SimonGAndrews/ESP32_SGATest/docs/targets/espruino_pico/resources/espruino_pico_pinout.jpg

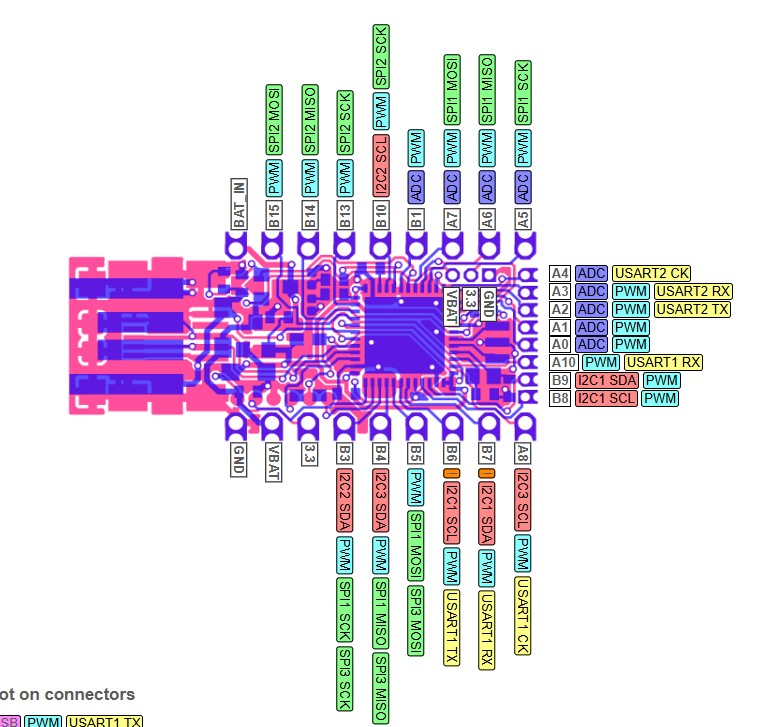
docs/targets/espruino_pico/resources/espruino_pico_pinout.jpg
