SimonGAndrews/ESP32_SGATest/docs/targets/olimex-esp32-devkit-lipo/Resources/Pinout_ESP32-S3-DevKit-LiPo.jpg

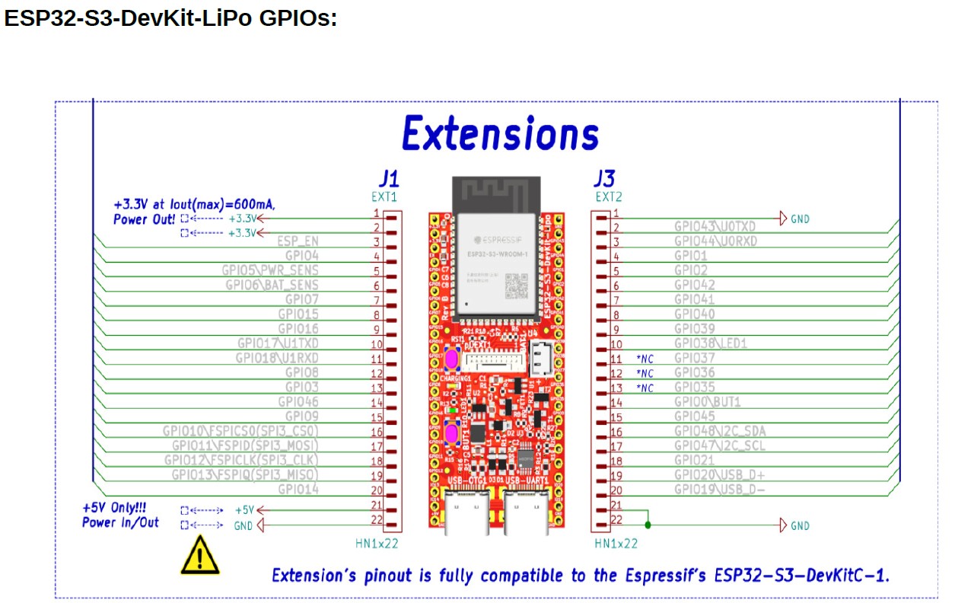
docs/targets/olimex-esp32-devkit-lipo/Resources/Pinout_ESP32-S3-DevKit-LiPo.jpg
