SimonGAndrews/ESP32_SGATest/KICAD/V2/RevA/README.md

# V2 Rev-A Project

The fresh Rev-A KiCad project is located at:

```text
KICAD/V2/RevA/Espruino_Harness_RevA/
```

It was created through KiCad as a new project rather than copied from the
exploratory schematic or PCB. Bring across only individually reviewed symbols,
footprints and implementation decisions, keeping each accepted library local
to the Rev-A project and referenced through `${KIPRJMOD}`.
