SimonGAndrews/ESP32_SGATest/KICAD/V2/RevA/Espruino_Harness_RevA/README.md

# Espruino Harness V2 Rev A

This is the fresh KiCad 9 project for the V2 Rev-A engineering-validation
harness.

The production hierarchy deliberately uses five pages:

1. `Espruino_Harness_RevA.kicad_sch` — the main A2 system page containing
   power, Rack Control, target control, the Target Interface and the
   hierarchical connections between the implementation pages.
2. `standard_test_blocks.kicad_sch` — one A2 page containing all accepted
   Standard Test Blocks as clearly labelled circuit sections.
3. `prototype_daughter_board.kicad_sch` — one A3 page containing the flexible
   wire-wrap daughter-board implementation.
4. `routing_control.kicad_sch` — one A3 page containing the Routing Fabric,
   both routing-control MCP23017s and the fixed direct-I2C isolation.
5. `power_control.kicad_sch` — one A2 page containing operating-mode
   selection, the 3.3 V rail selection and Test Block power control, and the
   target 5 V switch and two-range current monitor.

The main page is the visual integration view. Keep important supply, control,
routing and Target Interface relationships visible there. Diagnostic links,
isolation components and test points remain beside the circuits that own them.

## Draft workbench

`draft_workbench.kicad_sch` is an A3 standalone schematic for candidate
circuits and alternative implementations. It uses the project-local libraries
but is deliberately not referenced by the production hierarchy.

The workbench is therefore absent from production hierarchy exports, ERC,
netlists and BOMs. Validate it independently while drafting. When a circuit is
accepted:

1. copy it into its production-sheet location
2. check and, where necessary, re-annotate its references
3. inspect copied labels, power symbols and no-connect markers
4. run ERC and export the netlist from the production root schematic
5. compare the resulting connections with the governing specification

Do not treat the presence of a circuit on the workbench as design acceptance.

Use the project-local libraries described in `LIBRARY_PROVENANCE.md`. Bring
assets across from the exploratory project only after individual review.

The Rev-A verification scaffold is under `verification/`. Production ERC and
netlist evidence must be generated from the root schematic, not from an
individual hierarchical sheet.
