SimonGAndrews/ESP32_SGATest/docs/design/V2Harness/arch/TargetInterfaceContract_V2.md

# V2 Target Interface Contract

**Status:** Accepted — corrected power allocation and complete 48-contact map

**Version:** 1.4

**Last Updated:** 5 September 2026

## 1. Conclusion

The accepted mechanical direction uses two 24-pin connectors on each board,
giving 48 contacts. The accepted map assigns 32 signal/control contacts, four
power contacts — one target 3.3 V reference, one selected target-VBUS return
and two switched 5 V feeds — and twelve grounds. VBUS source selection is
manual and local to the daughter board, so no select conductor crosses the
Target Interface.

The currently mapped 32 signal and control pins provide:

* seven reusable route pins, R0-R6
* 23 direct connections to the Standard Test Blocks
* direct reset and boot-control pins

Section 7 shows the accepted mapping, how Connector A and Connector B mate
and how the Breakaway Links join the boards before separation. It is not an
implementation authority for the Target Interface.

The accepted physical arrangement uses two female right-angle socket banks on
the reusable harness and two male right-angle header banks on each daughter
board. The connectors are cut to 2x12 positions from the selected 2x36 parts
listed in Section 7.1 and hand-fitted after AISLER manufacture. Received-part
measurements, physical mating, current capacity and final PCB footprints still
need to be verified before the Rev-A PCB is released.

## 2. What This Document Defines

This document defines the wires that cross between the reusable harness board
and a removable target daughter board. It also gives each wire a pin on
Connector A or Connector B.

The pinout is based on:

* `StandardTestBlocks_V2.md`
* `StandardControlServices_V2.md`
* `TargetRoutingEnvelope_V2.md`
* `CombinedCapabilityConnectionMatrix_V2.md`
* `I2CControlledRouting_V2.md`
* `HybridHarnessArchitecture_V2.md`

Every daughter board must use this same pinout. A pin may carry one listed
function, a duplicated power connection or ground. There are no unassigned
spare pins in the accepted 48-pin arrangement.

## 3. Signals And Power On The Connectors

### 3.1 Reusable Route Pins

R0-R6 are seven connector pins that feed the Routing Fabric on the reusable
harness. The daughter board wires a suitable target GPIO to each route pin
used by that target.

| Route pin | It can be switched to | How the target uses it | Electrical type |
|---|---|---|---|
| R0 | `TI_ANALOG_ADC_IN`; `TI_ONEWIRE_DQ` | Analogue input or bidirectional open-drain | Bidirectional analogue-capable 0 V to 3.3 V |
| R1 | `TI_GPIO_LOOP_A_OUT`; `TI_SPI_MISO` | Output or input | Bidirectional 3.3 V digital |
| R2 | `TI_GPIO_LOOP_A_IN`; `TI_I2C_FB`; `TI_SPI_CS_ADC`; `TI_ONEWIRE_GPIO_A_FB` | Input or output | Bidirectional 3.3 V digital |
| R3 | `TI_GPIO_LOOP_B_OUT`; `TI_SPI_MOSI`; `TI_UART_A_TX` | Output | 3.3 V digital output |
| R4 | `TI_SPI_SCK`; `TI_UART_A_RX` | Output or input | Bidirectional 3.3 V digital |
| R5 | `TI_ANALOG_PWM_OUT`; `TI_RGB_DATA` | Output | 3.3 V digital waveform |
| R6 | `TI_GPIO_LOOP_B_IN`; `TI_I2C_INT`; `TI_SPI_CS_EXT`; `TI_ONEWIRE_GPIO_B_FB` | Input or output | Bidirectional 3.3 V digital |

All seven route pins are present on every harness. A daughter board may leave
one unconnected only when that target provides the required test connection by
a documented direct connection instead.

### 3.2 Direct Standard Test Block Pins

The connectors provide 23 pins that wire directly to the Standard Test Blocks.
A target with enough GPIO can use these direct pins. A target with fewer GPIO
can use R0-R6 and the Routing Fabric instead. The direction in the table is
shown from the target's point of view.

| Pin function | Test Block | Target direction | Connection |
|---|---:|---|---|
| `TI_GPIO_LOOP_A_OUT` | 1 | Output | Dedicated Test Block pin |
| `TI_GPIO_LOOP_A_IN` | 1 | Input | Dedicated Test Block pin |
| `TI_GPIO_LOOP_B_OUT` | 1 | Output | Dedicated Test Block pin |
| `TI_GPIO_LOOP_B_IN` | 1 | Input | Dedicated Test Block pin |
| `TI_ANALOG_PWM_OUT` | 2 | Output | Dedicated Test Block pin |
| `TI_ANALOG_ADC_IN` | 2 | Analogue input | Dedicated Test Block pin |
| `TI_I2C_SDA` | 3 | Bidirectional open-drain | Direct shared I2C bus |
| `TI_I2C_SCL` | 3 | Bidirectional open-drain | Direct shared I2C bus |
| `TI_I2C_FB` | 3 | Input | Dedicated Test Block pin |
| `TI_I2C_INT` | 3 | Input | Dedicated Test Block pin |
| `TI_SPI_SCK` | 4 | Output | Dedicated Test Block pin |
| `TI_SPI_MOSI` | 4 | Output | Dedicated Test Block pin |
| `TI_SPI_MISO` | 4 | Input | Dedicated Test Block pin |
| `TI_SPI_CS_ADC` | 4 | Output | Dedicated Test Block pin |
| `TI_SPI_CS_EXT` | 4 | Output | Dedicated Test Block pin |
| `TI_ONEWIRE_DQ` | 5 | Bidirectional open-drain | Dedicated Test Block pin |
| `TI_ONEWIRE_GPIO_A_FB` | 5 | Input | Dedicated Test Block pin |
| `TI_ONEWIRE_GPIO_B_FB` | 5 | Input | Dedicated Test Block pin |
| `TI_UART_A_TX` | 7 | Output | Dedicated Test Block pin |
| `TI_UART_A_RX` | 7 | Input | Dedicated Test Block pin |
| `TI_UART_B_TX` | 7 | Output | Dedicated Test Block pin |
| `TI_UART_B_RX` | 7 | Input | Dedicated Test Block pin |
| `TI_RGB_DATA` | 9 | Output | Dedicated Test Block pin |

The harness provides every pin in this table, but a daughter board does not
have to connect all of them. Its schematic and Target Profile must show which
functions are wired directly, wired through R0-R6 or left unconnected. The
direct and routed versions of the same function must never be enabled together.

### 3.3 Power, Reset And Boot Pins

| Pin function | Direction | What it does | Wiring rule |
|---|---|---|---|
| `TI_TARGET_3V3` | Target to harness | Provides the target's actual 3.3 V I/O-domain reference and rail-valid indication | Low-current reference only; shall remain between 3.00 V and 3.60 V while the target is powered and shall never supply harness logic or be joined to another 3.3 V source |
| `TI_TARGET_VBUS` | Daughter board to harness | Returns the manually selected VBUS — the same VBUS delivered to the target — to the harness-local 5 V-to-3.3 V regulator | Shall be absent when selected target VBUS is intentionally off and shall not bypass target-power monitoring or switching |
| `TI_SWITCHED_TARGET_5V` | Harness to daughter board | Supplies the Supervisor-controlled input to the daughter-board VBUS selector | Shall not be joined directly to host VBUS; the selector chooses exactly one source and is changed only while unpowered |
| `TI_TARGET_RESET_N` | Harness to target | Pulls the target reset input low | Must normally be released and must not depend on I2C or the Routing Fabric |
| `TI_BOOT_REQUEST` | Harness to target | Optionally pulls a target boot or recovery input low | A daughter board may leave it unconnected when the target has no safe equivalent |

`TI_TARGET_3V3` is deliberately independent of the 300 mA harness-load budget.
The corrected Power Control Service always supplies that load from either the
harness-local regulator or `EXT_3V3`.

The three power functions have fixed ownership: switched 5 V travels from the
harness to the selector, selected target VBUS returns from the selector to the
harness regulator, and target 3.3 V travels from the target only as a bounded
reference. None may be used in the opposite direction.

### 3.4 Common Ground

All `TI_GND` pins are connected to the same 0 V ground on both boards. Multiple
ground pins spread the return current and place a nearby ground beside the
main signal groups.

The accepted pinout uses twelve ground pins across Connector A and Connector B.
They are placed near power, analogue, I2C, SPI, UART and the general digital
signals.

## 4. Contact Allocation

The corrected interface has 35 different functions:

| Function group | Pins |
|---|---:|
| Route pins R0-R6 | 7 |
| Direct Standard Test Block pins | 23 |
| Target 3.3 V reference, selected target VBUS and switched 5 V | 3 |
| Reset and boot controls | 2 |
| **Different functions** | **35** |

The physical map uses 48 contacts for the 35 functions, one duplicate
switched-target-5-V contact and twelve ground contacts. The allocation is
therefore complete. Using R0-R6 can reduce the number of target GPIOs needed
for a particular daughter board, but it does not remove the direct Test Block
pins from the standard connector.

## 5. Connections Handled Elsewhere

The following connections do not pass through Connector A or Connector B:

| Function | Where it connects instead |
|---|---|
| Target USB D+, D−, host VBUS and the physical host/target USB connectors | Common daughter-board USB data/VBUS-selector Adapter Service; only selected `TI_TARGET_VBUS` and Supervisor `TI_SWITCHED_TARGET_5V` cross the interface |
| SWD, JTAG and target-specific debug | A target connector or daughter-board Adapter Service |
| UART CTS and RTS | A daughter-board Adapter Service when a target needs that test |
| Onboard USB-UART bridge isolation | Target-specific links, wiring or a proved target modification; a setup instruction alone is sufficient only when bench evidence shows that it removes the bridge drive |
| `SUP_EVENT_OUT` and `SUP_EVENT_IN` | The separate Supervisor Interface between the Rack Control Endpoint and Test Block 3 |
| Rack Control I2C | The Rack Control Backplane |
| Target Power Monitor I2C and shunt | Reusable-harness circuitry connected to the Rack Control Backplane |
| `ROUTE_CLEAR_N` and routing-controller controls | Internal reusable-harness wiring |
| External regulated 3.3 V and 5 V inputs | Harness power connectors |
| Target-specific VIN, VBAT, USB-OTG VBUS or other rails | A daughter-board Adapter Service where required |
| Target or daughter-board identity | Documentation and the Target Profile; no connector pin is currently required |

ESP32-C3-DevKitC-02 V1 evidence demonstrates why this remains outside the
common Interface. Its daughter-board native USB Adapter Service successfully
provides an independent `/dev/ttyACM` control path, but the target's onboard
CP2102N still drives UART0 RX on D20 through R21 whenever the DevKit is
powered. That internal target-board branch cannot be disconnected by Connector
A, Connector B or reusable-harness routing. The unmodified target profile must
therefore disable the full UART crosslink and use the standard endpoint-A
external-peer form unless another non-contending mapping is proved.

Adding one of these functions to a later Target Interface would require a
review of this pinout and the architecture documents that define the function.

## 6. Architecture Cross-Check

The pin list includes:

* all 23 target-facing connections from `StandardTestBlocks_V2.md`
* all seven route pins from `TargetRoutingEnvelope_V2.md`
* the direct I2C and second UART connections required by the combined matrix
* target 3.3 V reference, selected target VBUS, switched target 5 V, reset and optional boot from
  `StandardControlServices_V2.md`
* both the direct and routed wiring required by
  `HybridHarnessArchitecture_V2.md`
* the decision to handle CTS/RTS and the Target Power Monitor elsewhere

The accepted resolution is a separate manual two-position source selector on
every daughter board. It chooses host VBUS in Standalone or
`TI_SWITCHED_TARGET_5V` in Supervisor and is changed only while unpowered. No
schematic shall infer mode solely from the presence of
`TI_SWITCHED_TARGET_5V`, and raw host VBUS shall not cross this interface.

## 7. Connector Pinout

### 7.1 Connector Arrangement

The Target Interface uses two 24-pin connectors, called Connector A and
Connector B. Each connector has two rows of 12 pins on a 2.54 mm pitch.
Right-angle through-hole parts allow the reusable harness and daughter board
to lie in the same plane.

This gives:

* 48 pins using only two connectors on each board
* a clear Connector A and Connector B in the schematic and PCB layout
* female contacts on the permanently installed harness and exposed male pins
  only on the removable daughter board
* fewer parts to buy and align than four smaller connectors

The accepted connector products are:

| Board | Accepted product | Supplier reference | Preparation and assembly |
|---|---|---|---|
| Reusable harness | Adafruit Product `1543`, 0.1-inch 2x36 right-angle female socket strip | The Pi Hut SKU `104444` | Cut into 2x12 sections; mandatory hand-fit after AISLER manufacture |
| Daughter board | Adafruit Product `1541`, 0.1-inch 2x36 right-angle male breakaway header | The Pi Hut SKU `104400` | Break into 2x12 sections; mandatory hand-fit after manufacture |

Product sources and the available female technical drawing are:

* <https://thepihut.com/products/0-1-2x36-pin-strip-right-angle-socket-female-header-5-pack>
* <https://thepihut.com/products/break-away-0-1-2x36-pin-strip-right-angle-male-header-5-pack>
* <https://www.adafruit.com/product/1543>
* <https://www.adafruit.com/product/1541>
* <https://cdn-shop.adafruit.com/datasheets/P1543.pdf>

Received-part photographs are held in `../Parts/`; the controlled bench
measurement worksheet is
`../implementation/J900_J901_ReceivedPartMeasurementWorksheet.md`. Complete
that record before accepting the J900/J901 footprints, board-edge datums or
mating clearances.

The measured Rev-A footprints are held in the shared KiCad footprint library
`KICAD/V2/RevA/V2_Target_Interface.pretty`. The accepted nominal placement
uses 10.43 mm from the female inner-row centre to the harness mating edge and
4.42 mm from the male inner-row centre to the daughter-board mating edge. At
full insertion, each connector mating face projects 0.25 mm beyond its PCB
edge, producing the physically demonstrated 0.50 mm board-to-board gap. The
footprint `Dwgs.User` lines mark these nominal PCB-edge datums; they are not
`Edge.Cuts` geometry.

The male product is intended to break apart at the 2.54 mm pitch. The female
product is not breakaway: it shall be cut with diagonal cutters or a thin
hacksaw by sacrificing a socket position, then dressed and inspected so the
retained 2x12 housing and contacts are undamaged. The prepared parts are BOM
items for the completed assembly but shall use KiCad native DNP for the AISLER
assembly stage. For these Target Interface connectors, DNP therefore means
mandatory post-manufacture hand fitting rather than absence from the completed
board. `AISLER_MPN` shall remain empty.

The retail product information confirms the pitch, orientation and gold-plated
contacts but does not state an accepted contact-current rating. Before PCB
release, received samples must be measured and mated, the footprint and drill
geometry must be confirmed, and adequate current capacity must be established
for the accepted 3.3 V and 5 V limits.

### 7.2 Pin Names And Orientation

Connector A pins are named `A01`-`A24`. Connector B pins are named
`B01`-`B24`. These names do not depend on a particular connector manufacturer.
The matching schematic connector pins are numbered 1-24.

Each connector has twelve columns of two pins. Looking into the mating face of
the harness-board connector, with the pin-1 end on the left, the pins are:

```text
Column:    1   2   3   4   5   6   7   8   9  10  11  12
Odd row:  01  03  05  07  09  11  13  15  17  19  21  23
Even row: 02  04  06  08  10  12  14  16  18  20  22  24
```

The daughter-board connector must be laid out so `A01` mates with `A01`, `A02`
with `A02`, and so on. The same applies to Connector B. The daughter footprint
will normally appear mirrored relative to the harness footprint. The pin
numbers must be checked against the manufacturer's drawings rather than judged
from appearance.

Both harness connectors are female and both daughter-board connectors are
male. Connector A and Connector B shall therefore use a deliberately
asymmetric board-height offset and fixed edge datums so both banks can engage
simultaneously only in the correct orientation. When correctly mated, the
harness and daughter board lie in the same plane and their top edges align.
The PCB outlines, connector spacing and rack installation shall make inversion,
Connector A/B exchange, sideways one-pin offset and convincing one-bank-only
engagement mechanically implausible.

Both PCBs must mark Connector A, Connector B and pin 1. The boards must be
unpowered before the connectors are joined or separated. The daughter board
is inserted into the female banks on the harness after the harness is situated
in the rack.

### 7.3 Accepted Pin Allocation

Each connector uses sixteen pins for signals and controls, two for power and
six for ground.

| Pin use | Pins |
|---|---:|
| Signals and controls | 32 |
| `TI_TARGET_3V3` | 1 |
| `TI_TARGET_VBUS` | 1 |
| `TI_SWITCHED_TARGET_5V` | 2 |
| `TI_GND` | 12 |
| **Total** | **48** |

The switched 5 V feed appears once on each connector to share target current.
`TI_TARGET_3V3` and `TI_TARGET_VBUS` each use one contact with an adjacent
ground because their revised reference and regulator-input currents do not
require duplicated contacts. Contact-current capability remains a PCB-release
verification action.

#### 7.3.1 Connector A — Routing, Control And Low-Speed Signals

| Column | Odd pin | Function | Even pin | Function |
|---:|---|---|---|---|
| 1 | `A01` | `TI_TARGET_3V3` | `A02` | `TI_GND` |
| 2 | `A03` | `R0` | `A04` | `R1` |
| 3 | `A05` | `R2` | `A06` | `R3` |
| 4 | `A07` | `R4` | `A08` | `TI_GND` |
| 5 | `A09` | `R5` | `A10` | `R6` |
| 6 | `A11` | `TI_TARGET_RESET_N` | `A12` | `TI_GND` |
| 7 | `A13` | `TI_BOOT_REQUEST` | `A14` | `TI_RGB_DATA` |
| 8 | `A15` | `TI_I2C_SDA` | `A16` | `TI_GND` |
| 9 | `A17` | `TI_I2C_SCL` | `A18` | `TI_I2C_FB` |
| 10 | `A19` | `TI_I2C_INT` | `A20` | `TI_GND` |
| 11 | `A21` | `TI_ANALOG_PWM_OUT` | `A22` | `TI_ANALOG_ADC_IN` |
| 12 | `A23` | `TI_SWITCHED_TARGET_5V` | `A24` | `TI_GND` |

#### 7.3.2 Connector B — Direct Digital Test Block Signals

| Column | Odd pin | Function | Even pin | Function |
|---:|---|---|---|---|
| 1 | `B01` | `TI_TARGET_VBUS` | `B02` | `TI_GND` |
| 2 | `B03` | `TI_GPIO_LOOP_A_OUT` | `B04` | `TI_GPIO_LOOP_A_IN` |
| 3 | `B05` | `TI_GPIO_LOOP_B_OUT` | `B06` | `TI_GPIO_LOOP_B_IN` |
| 4 | `B07` | `TI_SPI_SCK` | `B08` | `TI_GND` |
| 5 | `B09` | `TI_SPI_MOSI` | `B10` | `TI_SPI_MISO` |
| 6 | `B11` | `TI_SPI_CS_ADC` | `B12` | `TI_GND` |
| 7 | `B13` | `TI_SPI_CS_EXT` | `B14` | `TI_ONEWIRE_DQ` |
| 8 | `B15` | `TI_ONEWIRE_GPIO_A_FB` | `B16` | `TI_GND` |
| 9 | `B17` | `TI_ONEWIRE_GPIO_B_FB` | `B18` | `TI_UART_A_TX` |
| 10 | `B19` | `TI_UART_A_RX` | `B20` | `TI_GND` |
| 11 | `B21` | `TI_UART_B_TX` | `B22` | `TI_UART_B_RX` |
| 12 | `B23` | `TI_SWITCHED_TARGET_5V` | `B24` | `TI_GND` |

### 7.4 Why The Pins Are Arranged This Way

The 48-pin arrangement was selected because:

* `TI_SWITCHED_TARGET_5V` supplies the complete target load in Supervisor
  operation, so it uses one pin on each connector
* `TI_TARGET_VBUS` returns the source-qualified VBUS delivered to the target
  and supplies the harness-local Standalone regulator through one contact
* `TI_TARGET_3V3` is a low-current target-domain reference through one contact
* twelve ground pins spread the return current and put ground pins near the
  main signal groups
* all required signals already have pins, so no pins are left unused just in
  case
* two 24-pin connectors cost less and are easier to align than four smaller
  connectors

Connector A keeps R0-R6 together with reset, boot, I2C, analogue and RGB.
Connector B carries the direct GPIO, SPI, OneWire and UART connections. Both
connectors include power and ground contacts; Connector A carries the target
3.3 V reference and Connector B carries the combined target-VBUS return.

This grouping only makes the schematic, PCB and wiring easier to follow. It
does not change which tests or combinations are allowed.

### 7.5 Breakaway Link Tracks

When the harness and daughter board are manufactured as one joined PCB, 40
copper tracks cross the Breakaway Links. Each of the 32 signal and control pins
uses one track. The 3.3 V, 5 V and ground connections use parallel tracks to
carry more current.

| Link group | Connector pins carried | Tracks |
|---|---|---:|
| `A-S1` | `A03`, `A04`, `A05`, `A06`, `A07`, `A09`, `A10`, `A11` | 8 |
| `A-S2` | `A13`, `A14`, `A15`, `A17`, `A18`, `A19`, `A21`, `A22` | 8 |
| `B-S1` | `B03`, `B04`, `B05`, `B06`, `B07`, `B09`, `B10`, `B11` | 8 |
| `B-S2` | `B13`, `B14`, `B15`, `B17`, `B18`, `B19`, `B21`, `B22` | 8 |
| `P-REF/VBUS` | `A01` (`TI_TARGET_3V3`), `B01` (`TI_TARGET_VBUS`), plus grounds `A02`, `B02` | 4 |
| `P-5V` | `A23`, `B23`, plus grounds `A24`, `B24` | 4 |
| **Total** | 32 signal, 4 power and 4 ground conductors | **40** |

The other eight ground pins are already connected to the same ground copper on
each PCB, so they do not need separate tracks across the break. The separate
target-3.3-V-reference and target-VBUS tracks plus the two switched-5-V tracks
match the accepted power contacts.

PCB layout must set suitable track widths for the expected current and make
the tracks narrow enough at the break points for clean separation. The link
group names are only PCB-layout labels; they do not create any new signals.

### 7.6 Checks Before Rev-A PCB Release

Before releasing the Rev-A PCB we must:

1. measure cut samples of Adafruit Products `1543` and `1541`, confirm their
   PCB-tail, drill, body, mating-depth and board-edge geometry, and check that
   both PCBs lie in the same plane with their top edges aligned when mated
2. establish adequate connector/contact current capacity and set maximum
   allowed 3.3 V and 5 V currents
3. check that A23 and B23 are connected together on every harness and daughter
   board and that the single-contact reference/return rails meet their budgets
4. place the Target Power Monitor before the switched 5 V track divides
   between Connector A and Connector B
5. check what happens during partial or misaligned insertion and prohibit
   connecting or disconnecting powered boards
6. verify that the asymmetric offset, board outlines, rack constraints and
   markings prevent reversal, connector exchange, one-pin offset and
   convincing one-bank-only engagement
7. check that both connectors align and mate without twisting either PCB
8. test the Breakaway Links for continuity, current capacity, clean separation
   and isolation after separation
9. define and verify a hand-assembly fixture or mated-board process that keeps
   both connector banks square, parallel and co-planar while their end pins are
   tack-soldered and before all joints are completed

There are no spare pins in this 48-pin pinout. If a future requirement needs
another pin, use a larger connector arrangement rather than removing the
recommended power or ground pins.

The signal pinout is accepted. The KiCad footprints must not be released until
the selected male and female parts have been checked against the pin view in
section 7.2.
