SimonGAndrews/ESP32_SGATest/docs/design/V2Harness/implementation/ReusableHarnessRevA_DesignBaseline.md

# Reusable Harness Rev-A Design Baseline

**Status:** Draft
**Baseline decision:** Not released for manufacture

## Purpose

This document defines the exact Rev-A implementation of the V2 Reusable
Harness Board and the evidence required before it is released to a PCB
manufacturer.

The architecture specifications define the required behaviour. This baseline
records how Rev A implements that behaviour. The KiCad project is the
authoritative implementation, while generated ERC, connectivity, BOM and DRC
outputs provide verification evidence.

The deterministic connectivity evidence required by this baseline is produced
by the tool defined in the
[Rev-A Connectivity Checker specification](ReusableHarnessRevA_ConnectivityChecker.md).

Rev A is ready for manufacture only when every applicable requirement maps to
an implemented and reviewed circuit, all release checks pass, and the accepted
baseline is identified by a Git commit.

## 1. Board identity, scope and implementation

| Item | Value |
|---|---|
| Board | V2 Reusable Harness Board |
| Revision | Rev A |
| Baseline status | Draft |
| Baseline Git commit | TBD |
| KiCad version | KiCad 9.0.x; exact release version TBD |
| Review date | TBD |
| Manufacturing release decision | Not approved |

### Included scope

- Reusable Harness Board implementation.
- Standard Test Blocks.
- Routing Control Service and Routing Fabric.
- Power Control Service.
- Target Interface connector banks.
- Provisional Rack Control and backplane interface.
- Rev-A isolation, diagnostic and test provisions.

Any excluded or provisional function shall be identified in its owning block
analysis before release.

### KiCad implementation structure

| Area | Owning schematic |
|---|---|
| Board integration and external interfaces | `Espruino_Harness_RevA.kicad_sch` |
| Standard Test Blocks | `standard_test_blocks.kicad_sch` |
| Routing Control and Routing Fabric | `routing_control.kicad_sch` |
| Power Control | `power_control.kicad_sch` |
| Rack Control Endpoint and direct reset/boot stages | `rack_control.kicad_sch` |
| Prototype daughter-board provision | `prototype_daughter_board.kicad_sch` |

The standalone `draft_workbench.kicad_sch` is not part of the production
hierarchy and cannot provide baseline evidence.

### First-pass schematic milestone

The first-pass functional schematic for the Rev-A Reusable Harness Board is
complete. Every circuit block in the register has an implementation in the
production hierarchy, and the root export dated 2026-08-05 completed with
zero ERC errors and zero warnings. This establishes schematic coverage and
hierarchical integration; it does not establish that any `Draft` block is
electrically verified or ready for manufacture.

The clean working exports are currently named `Rack_Control.net` and
`Rack_Control_ERC.rpt`. Subsequent baseline-review exports shall use the
full-hierarchy names defined in Appendix A so they cannot be mistaken for
sheet-only evidence.

The first-pass netlist contains 225 components. The following symbols do not
yet have footprints and therefore remain manufacturing-release gaps:

- `J900`, `J901` — Target Interface connector banks
- `J2`, `J301` — Grove I2C connectors
- `JBP2` — second provisional backplane connector

The prototype daughter-board sheet remains a provision rather than a
populated daughter-board design. The Shared Supervisor Assembly and physical
rack backplane are separate hardware designs outside this board baseline.

## 2. Governing requirements and artifact authority

### Governing specifications

- [V2 architecture](../arch/TestHarnessArchitecture_V2.md)
- [Conceptual model](../arch/HarnessConceptualModel_V2.md)
- [Hybrid harness architecture](../arch/HybridHarnessArchitecture_V2.md)
- [Standard Test Blocks](../arch/StandardTestBlocks_V2.md)
- [Standard Control Services](../arch/StandardControlServices_V2.md)
- [Target Routing Envelope](../arch/TargetRoutingEnvelope_V2.md)
- [Combined Capability Connection Matrix](../arch/CombinedCapabilityConnectionMatrix_V2.md)
- [Controlled routing](../arch/I2CControlledRouting_V2.md)
- [Target Interface contract](../arch/TargetInterfaceContract_V2.md)
- [Rev-A prototype strategy](../arch/ReusableHarnessPrototypeStrategy_V2.md)

### Artifact roles

| Artifact | Role |
|---|---|
| V2 architecture and interface specifications | Define required behaviour and accepted contracts |
| This baseline | Defines the selected Rev-A implementation and its acceptance state |
| `KICAD/V2/RevA/Espruino_Harness_RevA/` | Authoritative schematic, symbols, footprints and PCB implementation |
| Connectivity contract | Machine-readable required and forbidden connectivity |
| [Connectivity checker specification](ReusableHarnessRevA_ConnectivityChecker.md) | Defines the tool that compares the complete root netlist with the connectivity contract and produces deterministic evidence |
| Generated ERC, connectivity, BOM and DRC reports | Repeatable verification evidence |
| Review images | Visual record of the circuit that was reviewed; not connectivity authority |
| AISLER BOM Assign and final quote | Confirms the manufacturer part selections, exclusions, availability and assembly cost used for release |

When artifacts disagree, resolve the discrepancy explicitly. Do not silently
change a requirement to match the schematic or treat a generated report as a
replacement for design intent.

### KiCad assembly attributes

Set `DNP` through KiCad's native Symbol Fields Table control and then update
the PCB from the schematic. Do not add a user-defined symbol property named
`DNP`: it does not set the native schematic `(dnp yes)` state or propagate the
PCB `dnp` attribute. Parts that are hand fitted after manufacture remain
included in the KiCad BOM and on the board, with native DNP enabled; use
`Exclude from BOM` only when the part must be absent from the complete design
BOM rather than merely excluded from automated assembly.

## 3. Circuit-block register

Use `Draft`, `Reviewed` or `Verified` for block status. Manufacturing release
is a board-level decision. A material change returns the affected block to
`Draft`.

| ID | Circuit block | Risk | Owning sheet | Requirements | Visual review | Status |
|---|---|---|---|---|---|---|
| PC01 | Operating mode and 3.3 V rail | High | `power_control.kicad_sch` | Standard Control Services | [PNG](review-images/PC01-operating-mode-and-3v3-rail.png) | Superseded by accepted power correction; redesign pending |
| PC02 | Target 5 V switch and two-range monitor | High | `power_control.kicad_sch` | Standard Control Services | [PNG](review-images/PC02-target-5v-switch-and-two-range-monitor.png) | Verified |
| RC01 | Routing Fabric | High | `routing_control.kicad_sch` | Controlled routing | [PNG](review-images/RC01-routing-fabric.png) | Verified |
| RC02 | Routing controllers and fixed I2C isolation | High | `routing_control.kicad_sch`; Hardware Clear request stage on `rack_control.kicad_sch` | Controlled routing and Standard Control Services | [Full sheet](review-images/RC02-routing-controllers-and-fixed-i2c-isolation.png); [Hardware Clear](review-images/RC02-hardware-clear-request.png) | Verified |
| TB01 | Digital GPIO loopback | Standard | `standard_test_blocks.kicad_sch` | Standard Test Blocks | [PNG](review-images/TB01-digital-gpio-loopback.png) | Verified |
| TB02 | Analogue/PWM feedback | Standard | `standard_test_blocks.kicad_sch` | Standard Test Blocks | [PNG](review-images/TB02-analogue-pwm-feedback.png) | Verified |
| TB03 | I2C functional device | Standard | `standard_test_blocks.kicad_sch` | Standard Test Blocks | [Functional device](review-images/TB03-i2c-functional-device.png); [event handshake](review-images/TB03-supervisor-event-handshake.png) | Verified |
| TB04 | SPI functional device and fixed microSD storage extension | Standard | `standard_test_blocks.kicad_sch` | Standard Test Blocks | [PNG](review-images/TB04-spi-functional-device-and-storage.png) | Verified |
| TB05 | 1-Wire devices and GPIO | Standard | `standard_test_blocks.kicad_sch` | Standard Test Blocks | [PNG](review-images/TB05-onewire-functional-devices-and-gpio.png) | Verified |
| TB07 | UART crosslink and external peer | Standard | `standard_test_blocks.kicad_sch` | Standard Test Blocks | [PNG](review-images/TB07-uart-crosslink-and-external-peer.png) | Verified |
| TB09 | Addressable RGB output | Standard | `standard_test_blocks.kicad_sch` | Standard Test Blocks | [PNG](review-images/TB09-addressable-rgb-output.png) | Verified |
| TI01 | Target Interface connector banks | High | Root schematic | Target Interface contract | [PNG](review-images/TI01-target-interface-connector-banks.png) | Power-pin correction pending |
| BP01 | Rack Control and backplane interface | High | Root schematic | Standard Control Services | TBD | Draft |
| EP01 | Rack Control Endpoint and direct reset/boot stages | High | `rack_control.kicad_sch` | Standard Control Services | TBD | Draft |

## 4. Circuit-block analyses

This section records the analysis and verification state of each implemented
circuit block. Each block has its own subsection and follows the template in
Appendix A.

### 4.1 PC01 — Operating mode and 3.3 V rails

**Purpose and requirements:** Select the permitted Routing Logic 3.3 V source,
enable the local regulator only in Standalone, and provide either automatic or
Supervisor-controlled Test Block 3.3 V without joining the local and external
supplies. Complete power-off is achieved by removing the sources rather than
by a selector position. See Standard Control Services Sections 3.1–3.3 and
Appendix C.2.
**Source schematic:** `power_control.kicad_sch`, references `U1001`, `U1002`,
`D1001`–`D1005`, `Q1001`, `R1001`–`R1004`, `R1009` and `C1001`–`C1005`.
**Visual review:** Accepted
[`PC01-operating-mode-and-3v3-rail.png`](review-images/PC01-operating-mode-and-3v3-rail.png).
**Risk:** High
**Status:** Superseded by the accepted 22 August 2026 two-position power
architecture. The evidence below remains valid only where explicitly retained.
PC01 must be redesigned so `TI_TARGET_VBUS` feeds a harness-local 5 V-to-3.3 V
regulator and a manual 2x3 two-shunt selector chooses that local rail or
`EXT_3V3`. Its second shunt column drives `LOCAL_REG_ENABLE`: high in
Standalone, low in Supervisor and pulled low if unselected. A
`SN74LVC2G14DBVR` dual Schmitt-trigger inverter derives
`MODE_SUPERVISOR` and `TEST_BLOCK_AUTO_EN` from that static state.
`R1009` and `R1004` change from 100 kOhm to 22 kOhm so the corresponding
logic and Test Block enable states remain guaranteed low during partial-power
conditions. `TI_TARGET_3V3` is reference-only. TPS2116 and its old mode decode
are removed. Re-run the complete PC01 baseline before manufacturing release.

#### Interfaces and domains

| Type | Signals or rails | Function |
|---|---|---|
| Source inputs | `TI_TARGET_VBUS`, `EXT_3V3` | `TI_TARGET_VBUS` feeds the new local regulator; its output and `EXT_3V3` are alternative Routing Logic supplies and must never be directly joined |
| Reference input | `TI_TARGET_3V3` | Low-current target I/O-domain reference and rail-valid indication only |
| Mode selection | Würth `61300621121` 2x3 header with two `60900213421` shunts | Odd pins 1-3-5 select `LOCAL_3V3` or `EXT_3V3`; even pins 2-4-6 drive the resistor-protected `LOCAL_REG_ENABLE` state. `SN74LVC2G14DBVR` derives `MODE_SUPERVISOR` and `TEST_BLOCK_AUTO_EN`; hand-fitted header and shunts after AISLER manufacture |
| Supervisor input | `TEST_BLOCK_POWER_EN` | Enables Test Block power only in Supervisor mode |
| Power outputs | `ROUTING_LOGIC_3V3`, `TEST_BLOCK_3V3` | Supplies routing-control circuits and Standard Test Blocks |
| Ground | `TI_GND` | Common 0 V reference |

#### Corrected architecture requirement cross-check

This is a requirements-level result, not schematic acceptance. The accepted
two-selector architecture can satisfy the complete V2 power-service contract
without another Target Interface contact, subject to the implementation
conditions below.

| Requirement | Corrected architecture result | Remaining proof |
|---|---|---|
| Target USB enumeration in both active modes | Satisfied: D+/D−/GND pass directly and the selected source powers the target's normal USB VBUS | Target-by-target enumeration and back-power tests |
| No host/harness 5 V source joining | Satisfied by a local two-position daughter-board selector changed only while unpowered | Exact selector MPN, contact/current/inrush review and continuity test |
| Standalone routing and Test Blocks without target-3.3-V loading | Satisfied by the selected TPSM828438 module from returned `TI_TARGET_VBUS` through a TPS22917 input isolator | Schematic integration, layout/ripple/startup evidence and accepted host-source load envelope |
| Supervisor routing while target power is removed | Satisfied by the selected 3 A header/shunts on pins 3-5 and 4-6, selecting `EXT_3V3` and disabling the TPS22917 regulator-input isolator | Exact bias circuit, visual-preflight proof and cold-start/power-down captures |
| Supervisor-controlled target power cycling | Satisfied when the daughter selector is in its Harness position | Recorded selector states and preflight proof that the target de-energizes |
| 100 µA target-current measurement | Satisfied at component-budget level by isolating the regulator behind a TPS22917 whose disabled input current is 100 nA maximum through 85 °C | Complete calibrated error and leakage evidence through 55 °C |
| Test Block default and inrush behaviour | Unchanged: TPS22917 remains automatic-on in Standalone and controlled/default-off in Supervisor | Corrected enable decode and retained 2.2 nF/50 µF validation |
| Complete Target Interface allocation | Satisfied: 35 functions, duplicated switched 5 V and twelve grounds fit 48 contacts | TI01 net correction and connectivity contract refresh |
| Complete power-off | Satisfied as a system condition, not a selector state | Disconnect host, rack/external and every target-local competing source |

The analysis therefore identifies no fundamental architecture blocker. PC01
remains unverified until the mode-bias circuit is selected, the accepted
selector, regulator and input isolator are implemented, and the corrected
block passes the normal baseline process.

#### Resolved design decision — local regulator and PC02 isolation

**Status:** Regulator and input-isolator devices selected; schematic,
footprint and physical verification pending.
**Decision:** Use Texas Instruments `TPSM828438VCFR`, a 600 mA
integrated-inductor synchronous buck module, for the 5 V-to-3.3 V conversion.
Place a `TPS22917DBVR` active-high load switch between `TI_TARGET_VBUS` and
the module input. The even-numbered shunt column controls the TPS22917; the
module enable remains inside the isolated input domain. Set 3.3 V with
249 kΩ, 1% from `VSET` to
ground. Use at least 4.7 µF effective input capacitance and 10 µF nominal
output capacitance after tolerance and DC-bias derating.

**Manufacturer evidence:** The
[TPSM82843 product page](https://www.ti.com/product/TPSM82843) and
[Rev-A data sheet](https://www.ti.com/lit/ds/symlink/tpsm82843.pdf) confirm
1.8 V to 5.5 V input, 600 mA output, the QFN-FCMOD VCF-7 package, integrated
inductor, output discharge, the 249 kΩ 3.3 V selection and the required
capacitor ranges. The
[TPS22917 product page](https://www.ti.com/product/TPS22917) and
[Rev-B data sheet](https://www.ti.com/lit/ds/symlink/tps22917.pdf) confirm the
active-high DBVR device, 1 V to 5.5 V operation, 2 A rating, always-on reverse
current blocking and 100 nA maximum disabled input current from -40 °C to
85 °C. Mouser listed `TPSM828438VCFR` and `TPS22917DBVR` in stock during
the 22 August 2026 review; AISLER assignment and availability remain release
checks rather than frozen architecture facts.

**Thermal result:** TPSM828438 specifies `RθJA = 72.4 °C/W`. At 5 V,
3.3 V and 300 mA, a conservative 80% efficiency calculation gives 0.248 W
loss, approximately 18 °C rise and 73 °C junction at 55 °C ambient. At
the required 500 mA continuous design capability the same calculation gives
0.413 W, approximately 30 °C rise and 85 °C junction. Both retain clear
margin to the 125 °C operating-junction limit. The calculation selects the
part but does not replace layout and assembled-board temperature/ripple tests.

**Leakage and reverse-current result:** The regulator module alone allows up
to 850 nA shutdown current over the complete 1.8 V to 5.5 V input range and
-40 °C to 85 °C. Direct connection would consume 0.85 percentage point at
100 µA and leave only about 1.44% of the current PC02 residual allowance.
The upstream TPS22917 reduces the guaranteed monitored-rail contribution to
100 nA, or 0.10 percentage point, leaving about 2.19%. Its specified -1 µA
maximum reverse leakage applies only when its output is driven above its
input; the permitted mode topology prevents that condition by disconnecting
`LOCAL_3V3` from `EXT_3V3`. Reverse-current blocking is therefore a secondary
fault control, not a permitted steady-state current path. Verify the complete
branch through 55 °C and challenge selector overlap, missing-source and
partial-power cases before PC01 acceptance.

#### Resolved design issue — Test Block turn-on current

**Status:** Accepted and implemented; Rev-A measurement remains required
before PC01 acceptance and manufacturing release.
**Affected requirement:** Each valid mode must power its selected source and
the Test Blocks without collapsing the target or rack 3.3 V rail.
**Evidence:** `U1002` is a TPS22917 with its adjustable-rise-time `CT` pin open.
The current full-hierarchy netlist places at least 23.3 µF of fixed capacitance
on `TEST_BLOCK_3V3`: `C1004` 1 µF, `C401`, `C402` and `C901` 100 nF each, and
`C403` 22 µF. Removable Test Block modules can add more. TI's
[Managing Inrush Current](https://www.ti.com/lit/an/slva670a/slva670a.pdf)
shows that charging current is `C × dV/dt`, can collapse a shared source rail,
and must be designed from total load capacitance and an acceptable peak.
**Decision:** Limit the complete `TEST_BLOCK_3V3` switched load to 50 µF and
fit `C1005`, 2.2 nF C0G/NP0, from `U1002.CT` to
`ROUTING_LOGIC_3V3` (`U1002.VIN`). Using the TPS22917 typical 3.6 V timing
constant, the resulting 10%–90% output rise is approximately 3.5 ms. Charging
current is approximately 20 mA for the present 23.3 µF fixed load and 43 mA at
the 50 µF design limit. Because TI specifies the relevant timing constants as
typical rather than guaranteed limits, Rev A shall verify no more than 100 mA
peak charging current, acceptable source disturbance and successful startup
from both permitted 3.3 V sources. A later load above 50 µF requires renewed
calculation and validation.

#### Superseded evidence — discrete control-voltage margins

**Status:** Superseded with the target-powered source and retained only as
evidence for the currently implemented schematic. It shall not be used to
accept the corrected mode decoder.
**Affected requirement:** Every fitted Operating Mode row must select the stated
rail, while `OFF` must leave `ROUTING_LOGIC_3V3` high impedance.
**Decision:** `TI_TARGET_3V3` is specified as 3.00 V to 3.60 V at the Target
Interface. Use Vishay BAT54C-E3-08 for `D1001`–`D1005` and Diodes Inc.
DMN2024UQ-7 for `Q1001`. The diode guarantees at most 0.24 V forward drop at
0.1 mA. The MOSFET guarantees at most 29 mOhm on-resistance at 2.5 V gate
drive and retains the existing SOT-23 gate/source/drain pin mapping.
**Evidence:** The 100 kOhm decode loads keep D1001, D1002, D1004 and D1005
below the diode's 0.1 mA test current. The worst two-diode target-powered high
is 3.00 V - 2 x 0.24 V = 2.52 V, giving 1.52 V margin over the 1.0 V TPS2116
`MODE` and TPS22917 `ON` high thresholds. The external-source result is at
least 3.23 V - 2 x 0.24 V = 2.75 V. In external modes, Q1001 gate drive is at
least 3.23 V - 0.24 V = 2.99 V. `R1002` limits drain current to less than
0.34 mA, so 29 mOhm produces less than 0.01 mV at `MUX_PR1`, versus the
TPS2116 0.92 V minimum selection reference. With Q1001 off, target-derived
`MUX_PR1` is at least 3.00 V - 0.24 V = 2.76 V, giving 1.68 V margin over the
TPS2116 1.08 V maximum selection reference.

#### Superseded implemented topology

The following bullets describe the current KiCad circuit, not the newly
accepted requirement. They remain here to make the redesign delta auditable.

- `U1001`, TPS2116DRL, is used in manual mode as a break-before-make 2:1 power
  multiplexer. `VIN1` receives `TI_TARGET_3V3`, `VIN2` receives `EXT_3V3`, and
  `VOUT` drives `ROUTING_LOGIC_3V3`.
- `D1001`, `D1002`, `Q1001` and their bias resistors decode the three fitted
  Operating Mode rows into TPS2116 `MODE` and `PR1` without software.
- `U1002`, TPS22917DBV, switches `ROUTING_LOGIC_3V3` to `TEST_BLOCK_3V3`.
  `D1004` enables it automatically in either Standalone mode; `D1005` ORs that
  result with `TEST_BLOCK_POWER_EN` for Supervisor control. `C1005`, 2.2 nF,
  controls its output slew and Test Block charging current.
- `D1003` Schottky-ORs the available 3.3 V inputs only to create the low-current
  `MODE_BIAS_3V3` control bias. It does not join the power rails.
- `C1001`–`C1004` provide the local source, mux-output and Test Block output
  bypassing shown by the schematic. `C1005` is the separate TPS22917 timing
  capacitor and does not add to the switched-load capacitance.

#### Corrected required operating logic and safe states

| Operating Mode | Odd-column shunt | Even-column shunt | Routing source | Test Block switch |
|---|---|---|---|---|
| `STANDALONE` | Pins 1-3: `LOCAL_3V3` selected | Pins 2-4: local regulator enabled | Harness-local regulated 3.3 V from `TI_TARGET_VBUS` | On automatically |
| `SUPERVISOR` | Pins 3-5: `EXT_3V3` selected | Pins 4-6: local regulator disabled; `MODE_SUPERVISOR` asserted | `EXT_3V3` | Controlled by `TEST_BLOCK_POWER_EN`, default off |

The 2x3 header is a power-configuration device and both shunts shall be moved
only with associated sources off. The circuit does not rely on live transfer.
Both shunts must occupy the same end; missing, mismatched or cross-column
shunts are invalid preflight states. `OFF` is the de-energized condition with
host USB, external supplies and competing target sources removed. TPS22917
`QOD` remains tied to its output to discharge `TEST_BLOCK_3V3` when disabled;
no alternative source may drive that rail.

#### Superseded calculations and retained TPS22917 limits

| Subject | Calculation or limit | Reviewed result |
|---|---|---|
| Maximum specified steady load | U1001: Routing allocation 50 mA + selected Test Blocks 250 mA; U1002: selected Test Blocks 250 mA | 300 mA through U1001 and 250 mA through U1002, well below the 2.5 A and 2 A ratings |
| TPS2116 maximum hot path drop | 300 mA × 59 mΩ, using the 3.3 V, −40°C to 105°C data-sheet limit | 17.7 mV and 5.3 mW |
| TPS22917 conservative hot path drop | 250 mA × 185 mΩ, using the conservative 1.8 V, −40°C to 105°C limit because 3.3 V is below the tabulated 3.6 V point | 46.3 mV and 11.6 mW |
| Complete external-source path | 3.234 V minimum external supply − 17.7 mV − 46.3 mV | Approximately 3.170 V minimum at `TEST_BLOCK_3V3` before connector and PCB losses |
| Estimated junction rise | Data-sheet JEDEC `θJA`: 111.5°C/W for U1001 and 183°C/W for U1002 | Approximately 0.6°C and 2.1°C respectively; thermal performance is not a blocker at the specified load |
| Fixed switched capacitance | 1 µF + 22 µF + three × 100 nF | 23.3 µF before removable modules |
| Maximum switched capacitance | Fixed and removable loads combined | 50 µF; later increases require renewed analysis |
| Selected TPS22917 timing capacitor | `C1005 = 2.2 nF`; typical `dV/dt = 1900 / 2200` mV/µs at 3.6 V | Approximately 0.864 mV/µs and 3.5 ms 10%–90% rise |
| Calculated charging current | `I_INRUSH = C_LOAD × dV/dt` | Approximately 20 mA at 23.3 µF and 43 mA at 50 µF |
| Rev-A inrush acceptance | Measured at both permitted sources with the 50 µF maximum load | No more than 100 mA peak and no unacceptable source-rail disturbance |
| TPS22917 protection | Product data: no current limit | Source and wiring protection must not be inferred from this load switch |
| Minimum target-domain decode high | 3.00 V minimum `TI_TARGET_3V3` - 2 × 0.24 V BAT54C maximum forward drop | 2.52 V; at least 1.52 V above the 1.0 V input-high requirement |
| Minimum external-domain decode high | 3.23 V minimum external rail - 2 × 0.24 V | 2.75 V; at least 1.75 V above the 1.0 V input-high requirement |
| Q1001 minimum gate drive | 3.23 V - 0.24 V | 2.99 V; above the DMN2024UQ-7 2.5 V guaranteed on-resistance test point |
| Q1001 low-state current | 3.37 V maximum bias / 10 kΩ `R1002` | Less than 0.34 mA |
| `MUX_PR1` low | 0.34 mA × 29 mOhm | Less than 0.01 mV; far below the 0.92 V TPS2116 minimum reference |
| `MUX_PR1` target-derived high | 3.00 V - 0.24 V | At least 2.76 V; 1.68 V above the 1.08 V TPS2116 maximum reference |

#### Superseded manufacturer source and application review

The source screen below covers every principal PC01 component. Product pages
are retained because they are the current index of manufacturer-linked data
sheets and application material; the data sheets remain the authority for
guaranteed limits.

The reviewed local data-sheet snapshots are
[`tps2116.pdf`](DataSheets/tps2116.pdf) and
[`tps22917.pdf`](DataSheets/tps22917.pdf). The live manufacturer links below
remain authoritative for current revisions.

| Device | Manufacturer sources screened | Consequence for PC01 |
|---|---|---|
| TPS2116 | [Product page and all four linked documents](https://www.ti.com/product/TPS2116), [data sheet](https://www.ti.com/lit/ds/symlink/tps2116.pdf), [TPS2116EVM user guide](https://www.ti.com/lit/ug/slvubz0a/slvubz0a.pdf), [Basics of Power MUX](https://www.ti.com/lit/pdf/SLVAE51), eMeter and building-automation application briefs, and the linked 24 VAC reference-design guide | PC01 follows the manual `MODE`/`PR1` truth table. True `OFF` requires `MODE` low and `PR1` high; `MODE` low alone is not shutdown. The data sheet supports 1 µF input bypass in most applications and at least 0.1 µF at VOUT, subject to source-transient testing. The EVM independently demonstrates manual control, local capacitors, and VIN1/VIN2/VOUT/MODE/PR1 observability. Its automatic-priority, battery-backup, high-current bulk-capacitance and conversion examples are not copied because the PC01 header is changed with supplies off. Reverse-current blocking is not current limiting. |
| TPS22917 | [Product page and all eleven linked documents](https://www.ti.com/product/TPS22917), [data sheet](https://www.ti.com/lit/ds/symlink/tps22917.pdf), [TPS22917EVM user guide](https://www.ti.com/lit/ug/slvub64/slvub64.pdf), [Managing Inrush Current](https://www.ti.com/lit/an/slva670a/slva670a.pdf), [Timing of Load Switches](https://www.ti.com/lit/an/slva883/slva883.pdf), [On-Resistance](https://www.ti.com/lit/an/slva771/slva771.pdf), [Load Switch Thermal Considerations](https://www.ti.com/lit/pdf/SLVUA74), and [Selecting a Load Switch](https://www.ti.com/lit/pdf/SLVA887) | The exact TPS22917 is active-high; TPS22917L is active-low, despite conflicting generic metadata on the product page. `CT` must be designed from maximum switched capacitance and allowed inrush; timing varies with voltage, load, capacitance and temperature. QOD tied to VOUT is the deliberate fastest discharge path and is valid only because no alternative source drives `TEST_BLOCK_3V3`. The EVM independently demonstrates local input/output capacitance, adjustable `CT` and QOD arrangements, accessible enable and sense points, high-current PCB routing, and bench tests for rise time and on-resistance. Its evaluation jumpers and test fixtures are supporting evidence rather than Rev-A requirements. On-resistance, dissipation and lack of current limiting remain explicit release checks. The remaining linked integrated-vs-discrete, basics and power-consumption documents add no conflicting requirement. |
| BAT54C-E3-08 (`D1001`–`D1005`) | [Vishay BAT54 family data sheet](https://www.vishay.com/docs/86410/bat54_bat54a_bat54c_bat54s.pdf); no product-specific application note relevant to this static low-current decode was identified | The exact common-cathode SOT-23 part is selected. Its 0.24 V maximum forward drop at 0.1 mA supports every reviewed decode-high margin. |
| DMN2024UQ-7 (`Q1001`) | [Local reviewed Diodes Inc. data sheet](DataSheets/3168380-DMN2024UQ.pdf); no product-specific application note relevant to this low-current pull-down was identified | The part guarantees 29 mOhm maximum on-resistance at 2.5 V gate drive and uses the existing SOT-23 pin 1 gate, pin 2 source, pin 3 drain mapping. The calculated minimum gate drive is 2.99 V. |

#### Superseded components and packaging

| References | Manufacturer | Exact orderable part | Package | KiCad footprint | Datasheet/revision | Pin/pad mapping | AISLER assignment |
|---|---|---|---|---|---|---|---|
| `U1001` | Texas Instruments | [TPS2116DRLR](https://www.ti.com/product/TPS2116/part-details/TPS2116DRLR) | SOT-5X3 (DRL), 8 pin | `Package_TO_SOT_SMD:SOT-583-8` | [TPS2116](https://www.ti.com/lit/ds/symlink/tps2116.pdf), Rev A | Pins 1–8 agree. Hidden duplicate VOUT pin 7 is stacked with pin 2 in the symbol; PCB pads 2 and 7 both use `ROUTING_LOGIC_3V3`. The KiCad pad sizes, 0.50 mm pitch, row spacing and pin-1 marker agree with TI DRL0008A. Accepted. | Exact active-production MPN selected; assign and confirm AISLER availability |
| `U1002` | Texas Instruments | [TPS22917DBVR](https://www.ti.com/product/TPS22917/part-details/TPS22917DBVR) | SOT-23 (DBV), 6 pin | `Package_TO_SOT_SMD:SOT-23-6` | [TPS22917](https://www.ti.com/lit/ds/symlink/tps22917.pdf), Rev B | Pins 1–6, including CT pin 4 and QOD pin 5, agree. The KiCad IPC-7351 DBV footprint is a compatible alternate to TI DBV0006A and has the correct pitch, pad order and pin-1 marker. Accepted. | Exact active-production MPN selected; assign and confirm AISLER availability |
| `D1001`–`D1005` | Vishay | BAT54C-E3-08 | SOT-23 | `Package_TO_SOT_SMD:SOT-23` | [BAT54C-E3-08](https://www.vishay.com/docs/86410/bat54_bat54a_bat54c_bat54s.pdf) | Exact common-cathode mapping is pin 1 A1, pin 2 A2 and pin 3 K. The KiCad IPC-7351 TO-236/SOT-23 pad order, dimensions and pin-1 marker are compatible with the Vishay package. Accepted. | Accepted exact MPN and KiCad instance metadata synchronized; assign in AISLER |
| `Q1001` | Diodes Incorporated | DMN2024UQ-7 | SOT-23 | `Package_TO_SOT_SMD:SOT-23` | [DMN2024UQ](DataSheets/3168380-DMN2024UQ.pdf) | Exact mapping is pin 1 gate, pin 2 source and pin 3 drain. The KiCad IPC-7351 TO-236/SOT-23 pad order, dimensions and pin-1 marker are compatible with the Diodes package. Accepted. | Accepted exact MPN and KiCad value synchronized; assign in AISLER |
| `R1001`, `R1003`, `R1004`, `R1009` | TBD | 100 kΩ, standard passive policy | 0603 | `Resistor_SMD:R_0603_1608Metric` | Standard policy | Two-terminal mapping and standard KiCad footprint inspected; accepted | Grouped assignment pending |
| `R1002` | TBD | 10 kΩ, standard passive policy | 0603 | `Resistor_SMD:R_0603_1608Metric` | Standard policy | Two-terminal mapping and standard KiCad footprint inspected; accepted | Assignment pending |
| `C1001`–`C1004` | TBD | 1 µF, X7R, ±20% or better, at least 10 V | 0603 | `Capacitor_SMD:C_0603_1608Metric` | Standard policy | Two-terminal mapping and standard KiCad footprint inspected; accepted | Grouped assignment pending; preserve adequate effective capacitance at 3.3 V bias |
| `C1005` | TBD | 2.2 nF, C0G/NP0, ±10% or better, at least 10 V | 0603 | `Capacitor_SMD:C_0603_1608Metric` | [TPS22917](https://www.ti.com/lit/ds/symlink/tps22917.pdf) | `U1002.CT` to `U1002.VIN`; connectivity reviewed | Assign exact approved part; pending |

This package review applies to the superseded PC01 circuit only. Retained
devices may reuse its evidence, but the new regulator, corrected mode decode
and every changed connection require a fresh package and manufacturer review.

#### Superseded verification evidence

| Check | Evidence | Result |
|---|---|---|
| Requirements inspection | Superseded Standard Control Services topology | Historical result only; corrected requirements now govern |
| Behaviour and safe-state analysis | Historical truth table and calculations above | Retain only where unchanged by redesign |
| Manufacturer source screen | Product-linked documents summarized above | Retain for reused parts; new regulator and decode require review |
| Connectivity contract | `verification/contracts/PC01-operating-mode-and-3v3-rail.yaml` and historical exports | Superseded; contract and exports must be replaced after redesign |
| Full-hierarchy ERC | Historical accepted report | Superseded for PC01; run again after redesign |
| Symbol-to-footprint mapping | Historical component and PCB review | Superseded for changed or added parts |
| Visual schematic review | `review-images/PC01-operating-mode-and-3v3-rail.png` | Superseded; replace after redesign |

#### Open issues and accepted exceptions

- Implement the selected `TPS22917DBVR` input isolator and
  `TPSM828438VCFR` 5 V-to-3.3 V module from `TI_TARGET_VBUS`. Assign new
  references, add the 249 kΩ 1% `VSET` resistor, select exact input/output
  capacitors that retain the required effective capacitance, and verify the
  manufacturer-derived QFN-FCMOD footprint and AISLER assembly mapping.
- Replace the existing mode header and TPS2116 circuit with the accepted manual
  2x3 two-shunt selector. The odd-numbered column selects `LOCAL_3V3` or
  `EXT_3V3`; the even-numbered column enables the local regulator in
  Standalone and grounds its control in Supervisor. Use Würth
  `61300621121` with two `60900213421` shunts and select the static
  regulator-enable/`MODE_SUPERVISOR` circuit from manufacturer evidence.
- Update the Target Interface B01 implementation from duplicate
  `TI_TARGET_3V3` to `TI_TARGET_VBUS` and add the common USB data path and
  manual two-position VBUS selector to every daughter-board design. Route
  A23/B23 to its Supervisor input, B01 from its common output and host VBUS only
  to its Standalone input.
- Replace the PC01 connectivity contract, visual evidence, netlist and
  full-hierarchy ERC after the corrected schematic and PCB are synchronized.
- Perform the defined Rev-A inrush measurements with both permitted sources
  and the 50 µF maximum load.
- During PCB review, place `C1001`–`C1004` close to their devices and use short,
  wide VIN/VOUT/GND paths. Confirm that the backplane and target sources tolerate
  the specified load step or add connector-side bulk capacitance.
- Confirm accessible Rev-A measurement points for `TI_TARGET_VBUS`,
  `LOCAL_3V3`, `TI_TARGET_3V3`, `EXT_3V3`, `ROUTING_LOGIC_3V3`,
  `TEST_BLOCK_3V3`, local-regulator enable and `MODE_SUPERVISOR`.
- Verify the complete disabled TPS22917/regulator branch against the allocated
  100 nA PC02 contribution through 55 °C. Challenge reverse drive and
  selector-overlap fault cases even though the permitted states disconnect
  `LOCAL_3V3` from `EXT_3V3`.
- Define and verify the Standalone USB source envelope for simultaneous target
  current, up to 300 mA harness load at 3.3 V, regulator losses and startup
  inrush. Do not inherit the 1.5 A Supervisor allowance implicitly.
- Complete AISLER assignments and the release-stage PCB placement, rotation
  and assembly-rendering review. The engineering package and footprint review
  is complete.
No exceptions are accepted at this stage.

### 4.2 PC02 — Target 5 V switch and two-range power monitor

**Purpose and requirements:** Provide Supervisor-controlled target power,
observe the delivered voltage, current and power, cover both 100 µA sleep
measurements and target loads up to 1.5 A, and remain non-loading and
reverse-isolated while ordinary USB powers the target in Standalone modes.
See Standard Control Services Sections 3.1, 3.5 and 3.5.1.
**Source schematic:** `power_control.kicad_sch`, references `U1101`–`U1105`
and associated `Q1101`, `R11xx` and `C11xx` components.
**Visual review:**
[`PC02-target-5v-switch-and-two-range-monitor.png`](review-images/PC02-target-5v-switch-and-two-range-monitor.png).
**Status:** Verified; topology, exported connectivity, principal-device
sources, control behaviour, exact shunt selection, analytical electrical
budgets, engineering package evidence, visual review, ERC and deterministic
connectivity checks are accepted. PCB implementation, AISLER commercial
assignments and physical Rev-A measurements remain manufacturing-release
actions.

#### Key design issue — Integrated per-position target-power protection

**Status:** Accepted; schematic implementation complete and release
verification pending.
**Decision:** `U1101` shall be TPS2559-Q1 with a provisional 66.5 kΩ 1%
`ILIM` resistor. Each harness position therefore owns its target-power switch,
soft start, overload limit, fast short-circuit response, thermal protection
and active-low fault indication. The data-sheet tolerance gives an initial
limit range of approximately 1.63 A to 1.89 A: above the permitted 1.5 A load
at the low limit and bounded below 1.9 A at the high limit.
**Reason:** The earlier TPS22964C candidate conflicted with Standalone USB
power because its Quick Output Discharge loaded the disabled output. Removing
that discharge with TPS22963C preserved Standalone operation but left the
1.5 A position without hardware overload or short-circuit protection.
TPS2559-Q1 resolves both requirements in the normal switch position and is the
production-intent architecture for Rev A and subsequent revisions.
**Verification impact:** The schematic, project-local symbol and footprint,
connectivity contract, component record, netlist, ERC and visual review shall
all implement TPS2559-Q1. Review shall independently confirm the `ILIM`
tolerance, exposed-PowerPAD layout, voltage-drop and thermal budgets,
supported target capacitance, valid boot/radio transients, fault response and
disabled-state Standalone reverse isolation before PC02 is accepted.

#### Resolved design issue — Partial-power-safe range driver

**Status:** Accepted; schematic implementation complete and release
verification pending.
**Affected requirement:** The monitor and range-control circuit shall remain
safe when rack control is powered but external 5 V is absent, including
Standalone operation and arbitrary supply sequencing.
**Decision:** `U1102` is a TXU0101 fixed-direction dual-supply translator.
`VCCA` and its constant-high `A` input use `RACK_CONTROL_3V3`; `VCCB` uses
`EXT_5V`; `OE` receives `LOW_RANGE_GATE_3V3`; and output `B` drives
`LOW_SHUNT_BYPASS_GATE`. `R1106` and `R1107` hold `OE` and the MOSFET gate
low when the corresponding driver is unavailable.
**Evidence:** The
[TXU0101 data sheet](https://www.ti.com/lit/ds/symlink/txu0101.pdf) specifies
`Ioff` partial-power-down protection and disables the outputs to high
impedance if either supply is below 100 mV or disconnected. It also permits
either supply power-up order. The external pull-down on
`LOW_SHUNT_BYPASS_GATE` therefore restores the high-current bypass whenever
the translator cannot drive it.
**Verification impact:** The project-local symbol, SOT-23-6 pad mapping,
dual-supply decoupling, partial-power states and connectivity contract remain
release checks; the earlier SN74AHCT1G125 blocker is closed.

#### Resolved design issue — Low-range alert is latched and observable

**Status:** Accepted schematic implementation; firmware and release
verification remain pending.
**Affected requirement:** An unsafe low-range current shall restore the
high-current bypass and remain observable without oscillating or depending on
polling latency.
**Evidence:** `U1104` asserts `LOW_RANGE_OK_N` when its shunt-overvoltage
threshold is exceeded. That low state immediately disables `U1102` through
`U1105` and restores the `Q1101` bypass. Restoring the bypass also removes the
1 Ω shunt voltage that caused the alert. In the INA228 default transparent
mode, the alert can therefore clear while `TARGET_LOW_RANGE_EN` remains high
and reinsert the shunt. The INA228 data sheet states that `ALATCH = 1` holds
the alert and its flag active until `DIAG_ALRT` is read.
**Resolution:** `LOW_RANGE_OK_N` connects the `U1104` alert to the existing
`U1105` hardware interlock and to `GPB3` of Rack Control MCP23017 `U1201`.
`GPB3` contributes to the active-low open-drain `RACK_INT_N` interrupt. The
accepted firmware contract configures `U1104` for its ±40.96 mV range,
active-low latched shunt-overvoltage alert and accepted threshold. Firmware
clears `TARGET_LOW_RANGE_EN` before reading INA228 `DIAG_ALRT`, then clears the
MCP23017 capture. The refreshed root netlist contains the complete path and
the full hierarchy passes ERC with zero errors and zero warnings.

#### Key design issue — Low-range physical accuracy is not yet proved

**Severity:** Major; blocks acceptance of the 100 µA measurement claim.
**Affected requirement:** Sleep-current measurements shall achieve the agreed
5%–10% practical accuracy at 100 µA.
**Evidence:** The required signal is only 100 µV across `R1102`. INA228 offset
is small enough in the ±40.96 mV range, but `Q1101` remains connected across
the 1 Ω shunt while off. The selected AO3401A data sheet specifies 1 µA
maximum off leakage at 25°C and 5 µA at 55°C, measured at a much higher
drain-source voltage than this circuit. The 55°C limit therefore consumes up
to 5% of the 100 µA measurement allowance before shunt tolerance, thermal
EMF, PCB leakage, input bias, noise and layout are included.
**Analytical resolution:** Retain AO3401A as the exact Rev-A bypass MOSFET.
The component budget below gives a 7.71% known worst-case subtotal at 100 µA
with the accepted 1%, 100 ppm/°C shunt, leaving 2.29% for residual physical
effects within the ±10% requirement. The resulting 1% shunt requirement and
the exact Rev-A candidates are accepted in Standard Control Services.
**Required physical resolution:** Verify zero-offset and known-current points
on Rev A through 55°C. Cooling shall keep the circuit at or below 55°C when
the guaranteed low-current accuracy is required. Measured characterization
remains mandatory before the 100 µA claim is accepted because the data sheet
does not characterize leakage at the actual low drain-source voltage and the
remaining noise, thermal-EMF and PCB-leakage allowance is only 2.29%.

#### Interfaces and domains

| Type | Signals or rails | Function |
|---|---|---|
| Power input | `EXT_5V` | Source for Supervisor-controlled target power and the 5 V range driver |
| Always-on control supply | `RACK_CONTROL_3V3` | Supplies both monitors and the control gates |
| Control inputs | `MODE_SUPERVISOR`, `TARGET_POWER_EN`, `TARGET_LOW_RANGE_EN` | Qualify target power and low-range selection |
| Rack Control bus | `RACK_CONTROL_SDA`, `RACK_CONTROL_SCL` | Reads the two power monitors |
| Power output | `TI_SWITCHED_TARGET_5V` | Measured and switched 5 V delivered to the Target Interface |
| Status outputs | `TARGET_POWER_ALERT_N`, `TARGET_POWER_FAULT_N`, `LOW_RANGE_OK_N` | Normal-range alert, hardware switch fault and latched low-range qualification event observed by Rack Control |
| Ground | `TI_GND` | Common reference for the circuit and Target Interface |

#### Selected implementation

- TPS2559-Q1 `U1101` switches and protects `EXT_5V` only when both
  `MODE_SUPERVISOR` and `TARGET_POWER_EN` are asserted through `U1105`.
  Its 66.5 kΩ `ILIM` resistor sets the provisional per-position overload
  threshold, and `TARGET_POWER_FAULT_N` reports an overload or thermal fault.
- `R1101` is the always-present 50 mΩ normal-range shunt. `U1103` is the
  normal-range INA226 monitor at I2C address `0x40`.
- `R1102` is the 1 Ω low-range shunt. `Q1101` normally bypasses it so boot and
  active target current do not pass through 1 Ω.
- `U1104` is the low-offset INA228 low-range monitor at I2C address `0x41`.
  Its latched active-low alert output `LOW_RANGE_OK_N` qualifies
  `TARGET_LOW_RANGE_EN` through the second `U1105` gate and is observed by the
  Rack Control Endpoint.
- `U1102` is a TXU0101 powered from `RACK_CONTROL_3V3` on its A side and
  `EXT_5V` on its B side. It translates the qualified 3.3 V selection into
  the 5 V gate drive required to turn the P-channel bypass MOSFET off. Its
  `Ioff` and supply-disconnect behaviour make the output high impedance if
  either domain is unavailable.
- Both monitors are powered from always-on `RACK_CONTROL_3V3` and share
  `RACK_CONTROL_SDA` and `RACK_CONTROL_SCL`. Their bus-voltage inputs observe
  `TI_SWITCHED_TARGET_5V`.
- `U1103` senses `R1101` through `HIGH_SHUNT_P` and `HIGH_SHUNT_N`; `U1104`
  senses `R1102` through `HIGH_SHUNT_N` and `TI_SWITCHED_TARGET_5V`. The PCB
  shall route a separate Kelvin pair directly from each shunt's pads to its
  corresponding monitor inputs.
- `TARGET_POWER_ALERT_N` exposes the normal-range monitor alert to Rack
  Control. `TI_SWITCHED_TARGET_5V` feeds the Target Interface after both
  measurement elements.

The hardware-safe state is target power off and the low-range shunt bypassed.
`R1009`, owned by PC01, holds `MODE_SUPERVISOR` low; `R1103` and `R1104` hold
the two Rack Control requests low. `R1106` holds the range-driver input low and
`R1107` holds the P-channel MOSFET gate low if its driver is unavailable.

#### Operating logic and safe states

`U1105` implements two independent AND functions:

- `TARGET_SWITCH_EN = MODE_SUPERVISOR AND TARGET_POWER_EN`
- `LOW_RANGE_GATE_3V3 = TARGET_LOW_RANGE_EN AND LOW_RANGE_OK_N`

`U1102` drives the P-channel bypass gate. A low
`LOW_RANGE_GATE_3V3`, loss of either translator supply or a low
`LOW_RANGE_OK_N` makes the output high impedance; `R1107` then keeps `Q1101`
on and bypasses the 1 Ω shunt. A valid high value drives the gate towards
`EXT_5V`, turns `Q1101` off and inserts `R1102`.

| Supervisor mode | Target-power request | Low-range request | `LOW_RANGE_OK_N` | Expected hardware state |
|---:|---:|---:|---:|---|
| 0 | X | X | X | `U1101` off; target 5 V not supplied |
| 1 | 0 | X | X | `U1101` off; target 5 V not supplied |
| 1 | 1 | 0 | X | Target powered through `R1101`; `R1102` bypassed |
| 1 | 1 | 1 | 0 | Target powered; low range rejected and `R1102` bypassed |
| 1 | 1 | 1 | 1 | Target powered; `R1102` inserted for low-current measurement |

`X` means that the input does not change the expected state for that row.
Firmware shall request low range only after the normal-range monitor indicates
that target current is within the permitted transition threshold. `U1104`
shall use its active-low latched shunt-overvoltage alert for
`LOW_RANGE_OK_N`. If it asserts, hardware restores the bypass. Firmware shall
then clear `TARGET_LOW_RANGE_EN` before reading `DIAG_ALRT` to clear the
latched alert and shall not retry until normal-range current is verified.

The intended uncommanded state is target power off with `R1102` bypassed:

- `MODE_SUPERVISOR`, `TARGET_POWER_EN` and `TARGET_LOW_RANGE_EN` have external
  pull-downs.
- `LOW_RANGE_GATE_3V3` and `LOW_SHUNT_BYPASS_GATE` have pull-downs, so the
  1 Ω shunt is bypassed when range control is unavailable.
- Loss of `EXT_5V` removes the target supply regardless of the logic state;
  the TXU0101 becomes high impedance and cannot back-power either domain.

The [SN74LVC2G08 data sheet](https://www.ti.com/lit/ds/symlink/sn74lvc2g08.pdf)
specifies partial-power-down protection: `U1105` outputs become high impedance
when `RACK_CONTROL_3V3` is absent. The
[TPS2559-Q1 data sheet](https://www.ti.com/lit/ds/symlink/tps2559-q1.pdf)
requires a defined enable state. Therefore the current input-side pull-downs
do not by themselves guarantee the required power-off state across an
unpowered `U1105`. `R1110` therefore provides the required 100 kΩ pull-down
directly from `TARGET_SWITCH_EN` to `TI_GND` on the switch side of `U1105`.

#### Key calculations and limits

| Subject | Calculation | Initial result |
|---|---|---|
| Normal-range shunt drop | 1.5 A × 50 mΩ | 75 mV; exactly the specified shunt limit |
| Normal-range shunt dissipation | 1.5 A² × 50 mΩ | 112.5 mW; accepted 2 W PE2512 part has ample component margin, subject to final PCB thermal review |
| Low-range upper-limit drop | 20 mA × 1 Ω | 20 mV; meets the specified limit |
| Low-range upper-limit dissipation | 20 mA² × 1 Ω | 0.4 mW |
| Low-range minimum signal | 100 µA × 1 Ω | 100 µV |
| Target-switch loss | 1.5 A × 21 mΩ; 1.5 A² × 21 mΩ | 31.5 mV drop and 47.25 mW dissipation at the data-sheet maximum on-resistance |
| Listed-maximum component path | 21 mΩ switch + 50.65 mΩ maximum selected shunt at 55°C + 60 mΩ bypass MOSFET at 25°C | 197.5 mV at 1.5 A; leaves 52.5 mV, or 35 mΩ, for PCB, connectors and backplane |
| Temperature-aware 55°C path estimate | 21 mΩ switch + 50.65 mΩ shunt + approximately 69 mΩ bypass MOSFET | Approximately 211 mV at 1.5 A; leaves approximately 39 mV, or 26 mΩ, for PCB, connectors and backplane |
| Component-path dissipation at 1.5 A | 47.25 mW switch + 114 mW shunt + approximately 155 mW bypass MOSFET | Approximately 316 mW total; individual device dissipation is within rating, subject to the specified PCB copper and footprint implementation |
| Provisional current limit | 66.5 kΩ 1% `ILIM` resistor | Approximately 1.63 A minimum, 1.77 A nominal and 1.89 A maximum |

The listed-maximum bound uses the MOSFET 25°C maximum on-resistance and includes
the selected shunt's 1% initial tolerance plus 100 ppm/°C drift to 55°C. The
55°C estimate applies the AO3401A data-sheet typical normalized-temperature
curve to its 60 mΩ maximum at 25°C; the manufacturer does not guarantee that
combined value. The result shows that the 250 mV complete-path requirement is
feasible but allocates no more than about 26 mΩ to all copper, connector and
backplane contacts. PCB resistance calculation and a 1.5 A end-to-end Rev-A
measurement are therefore release requirements rather than unresolved circuit
topology.

The selection and protection review follows TI's
[Selecting a Load Switch to Replace a Discrete Solution](https://www.ti.com/lit/pdf/SLVA887)
and
[Power Multiplexing Using Load Switches and eFuses](https://www.ti.com/lit/an/slva811a/slva811a.pdf)
application reports. The former requires explicit preservation of current
limit, reverse-current, undervoltage and thermal protections where the system
needs them. The latter makes the coupled output-drop, inrush, reverse-current
and switchover trade-offs explicit. Live source transfer is not a harness
requirement because Operating Mode changes only with its supplies off, but
startup inrush and reverse isolation remain release checks.

The INA226 maximum 10 µV shunt offset is 2% of the 500 µV signal produced by
10 mA through `R1101`. The INA228 maximum 1 µV shunt offset is 1% of the
100 µV minimum low-range signal. These results support the selected split, but
the complete calibrated error budget still needs shunt tolerance, temperature,
layout, noise and zero-offset compensation.

The former 0.1% shunt-tolerance requirement was more restrictive than the
system accuracy requires and led to specialist precision-foil parts with
poor availability and high unit cost. The accepted Rev-A parts are a
[Yageo PE2512FKF7W0R05L](https://www.yageogroup.com/component-documentation/download/specsheet/PE2512FKF7W0R05L)
for `R1101` and a
[Bourns CHP2512-FX-1R00ELF](https://www.bourns.com/docs/product-datasheets/chp.pdf)
for `R1102`. Both are 2512, 1%, 100 ppm/°C parts. The Yageo `R1101` is rated
2 W and dissipates only 112.5 mW at 1.5 A. The RoHS-compliant Bourns `R1102`
is rated 3 W at 70°C and for high-power surge operation, so it covers the
2.25 W worst-case dissipation that would occur if 1.5 A persisted while the
low range was inserted. Its PCB land and copper area must keep the board
surface within the manufacturer's 105°C full-load limit. Both parts have
accepted project-local, manufacturer-derived two-terminal footprints.
Separate Kelvin traces must leave directly from their pads during PCB routing,
and AISLER availability still requires confirmation.

The conservative uncalibrated low-range budget at 100 µA and 55°C is:

| Contribution | Maximum allowance at 100 µA | Percentage of reading |
|---|---:|---:|
| AO3401A bypass off leakage | 5 µA | 5.00% |
| INA228 input offset at 25°C | 1 µV across 1 Ω | 1.00% |
| INA228 offset drift, 25°C to 55°C | 0.3 µV | 0.30% |
| INA228 gain error and 30°C drift | 0.11% combined | 0.11% |
| Proposed 1% shunt initial tolerance | 1% | 1.00% |
| Proposed 100 ppm/°C shunt drift, 25°C to 55°C | 0.30% | 0.30% |
| INA228 input bias, conservatively treated as 2.5 nA measurement current | 0.0025 µA | 0.003% |
| TPS22917 local-regulator input-isolator shutdown current | 0.10 µA | 0.10% |
| **Known worst-case subtotal** |  | **7.81%** |

This leaves approximately 2.19% for quantization, noise, thermal EMF, PCB
leakage and residual zero-compensation error within the ±10% requirement.
The selected TPSM828438 regulator is isolated from `TI_TARGET_VBUS` by the
TPS22917 during Supervisor measurement. The switch's 100 nA guaranteed
maximum through 85°C consumes 0.10 percentage point; the regulator's own
850 nA shutdown limit is downstream of the disabled isolation switch and is
not added.
Without that isolation, a 1 µA worst-case contribution would consume one
percentage point and leave only about 1.29% for all other residual effects.
Complete-board leakage and calibrated accuracy verification through 55°C
remain mandatory.
At 1 mA the bypass-leakage and monitor-offset percentages each reduce by a
factor of ten, leaving more than 2.5 percentage points inside the ±5%
requirement. In the normal range, the INA226 10 µV offset contributes 1% at
20 mA through 50 mΩ; including a 1% shunt, 0.3% shunt drift, 0.1% gain error
and 0.15% gain drift gives a known subtotal below 2.6%. The analytical result
therefore supports the accepted 1% shunt requirement, provided the required
zero measurement, averaging and Rev-A known-current calibration are retained.

The INA226 ±81.92 mV shunt range corresponds to 1.6384 A through the 50 mΩ
normal-range shunt. This covers the 1.5 A permitted load but can saturate
before the provisional TPS2559-Q1 upper current-limit tolerance. That is
acceptable only if firmware treats INA226 as the normal operating monitor and
uses `TARGET_POWER_FAULT_N`, rather than an INA226 current reading, as the
authoritative overload indication. INA228 shall use its ±40.96 mV range for
the 1 Ω low-current path, giving a 40.96 mA measurement ceiling.

#### Manufacturer source and application review

| Device | Manufacturer sources screened | Consequence for PC02 |
|---|---|---|
| TPS2559-Q1 | [Product page and both linked technical documents](https://www.ti.com/product/TPS2559-Q1), [data sheet](https://www.ti.com/lit/ds/symlink/tps2559-q1.pdf), [Basics of Load Switches](https://www.ti.com/lit/an/slva652/slva652.pdf), [MFi overcurrent-test application note](https://www.ti.com/lit/an/slvaeq2/slvaeq2.pdf), and [TPS2559-Q1 EVM guide](https://www.ti.com/lit/pdf/SLUUB15) | Adjustable current limit, soft start, fast short response, thermal retry, disabled reverse blocking, FAULT pull-up and PowerPAD layout apply. SLVA652A confirms the 1 µF local input bypass, the decision not to use output discharge where Standalone USB can power the output, and the need to calculate inrush, local bulk capacitance, voltage drop and thermal behaviour from the complete target load and PCB implementation. It introduces no topology change. The MFi compliance procedure itself does not apply, but its overload/fault test method supports Rev-A protection tests. |
| INA226 | [Product page and linked technical documents](https://www.ti.com/product/INA226), [data sheet](https://www.ti.com/lit/ds/symlink/ina226.pdf), [Getting Started with Digital Power Monitors](https://www.ti.com/lit/an/sboa511a/sboa511a.pdf), and [Digital Interfaces for Current-Sense Devices](https://www.ti.com/lit/an/sboa203a/sboa203a.pdf) | Shunt range, calibration, averaging, conversion timing, alert programming, I2C pull-ups and Kelvin connections apply. Copper-trace shunts, high-voltage, power-amplifier, heater, solar and ESD/EOS application examples do not change this precision 5 V external-shunt design. |
| INA228 | [Product page and linked technical documents](https://www.ti.com/product/INA228), [data sheet](https://www.ti.com/lit/ds/symlink/ina228.pdf), and the same digital-monitor and interface guides | ±40.96 mV range, averaging, conversion timing, calibration and Kelvin layout support the low range. Energy/charge accumulation is useful but not required. High-voltage, E3/solenoid, robot and heater examples do not alter this application. |
| SN74LVC2G08 | [Product page](https://www.ti.com/product/SN74LVC2G08), [data sheet](https://www.ti.com/lit/ds/symlink/sn74lvc2g08.pdf), and [Implications of Slow or Floating CMOS Inputs](https://www.ti.com/lit/an/scba004e/scba004e.pdf) | `Ioff` explicitly protects inputs/outputs when its 3.3 V supply is absent. External pull-downs keep all CMOS inputs defined; the product-linked solid-state-relay application brief is unrelated. |
| TXU0101 | [Product page and linked technical documents](https://www.ti.com/product/TXU0101) and [data sheet](https://www.ti.com/lit/ds/symlink/txu0101.pdf) | Fixed A-to-B translation, Schmitt-trigger input, output enable, `Ioff` protection, supply-disconnect isolation and arbitrary power sequencing implement the partial-power-safe 3.3 V-to-5 V range driver. The device becomes high impedance if either supply is absent; external pull-downs establish the bypass state. |
| AO3401A | [Alpha & Omega AO3401A data sheet](https://www.aosmd.com/res/data_sheets/AO3401A.pdf); no product-specific application note identified | The exact AO3401A is accepted for the Rev-A bypass path. Its on-resistance supports 1.5 A operation. Its 5 µA maximum off-leakage specification at 55°C can consume 5% of the 100 µA measurement allowance, and the actual low-`VDS` condition is not characterized; Rev-A leakage and accuracy verification through 55°C remain mandatory. |
| PE2512FKF7W0R05L (`R1101`) | [Yageo part specification](https://www.yageogroup.com/component-documentation/download/specsheet/PE2512FKF7W0R05L) | The exact 50 mΩ, 1%, 100 ppm/°C, 2 W, RoHS 2512 candidate has ample dissipation margin at 1.5 A. Pad-level Kelvin routing and AISLER assignment remain required. |
| CHP2512-FX-1R00ELF (`R1102`) | [Bourns CHP data sheet](https://www.bourns.com/docs/product-datasheets/chp.pdf) | The exact 1 Ω, 1%, 100 ppm/°C, 3 W, RoHS 2512 candidate supports the analytical accuracy budget and remains within its continuous rating even for the abnormal 2.25 W case. Its specified land pattern, copper area and 105°C board-surface limit apply. |

The product-page screen also covered documents linked to these devices that
address unrelated end equipment or sensing topologies. They are excluded above
by application rather than silently omitted.

#### Components and packaging

| References | Manufacturer | Exact orderable part | Package | KiCad symbol | KiCad footprint | Datasheet/revision | Pin/pad mapping | AISLER assignment |
|---|---|---|---|---|---|---|---|---|
| `U1101` | Texas Instruments | [TPS2559QWDRCRQ1](https://www.ti.com/product/TPS2559-Q1/part-details/TPS2559QWDRCRQ1) | DRC0010K, 10-pin 3 mm × 3 mm VSON with exposed PowerPAD and wettable flanks | Project-local `TPS2559Q1_TARGET_POWER_SWITCH` | Project-local `TPS2559Q1_DRC0010K_VSON10_EP` | [TPS2559-Q1](https://www.ti.com/lit/ds/symlink/tps2559-q1.pdf), SLVSD03 | Pins 1–10 map directly; symbol PowerPAD pin 11 maps to the 1.65 mm × 2.40 mm exposed pad. TI land dimensions and 81% paste coverage are implemented. PCB-editor inspection confirmed pin 1 at upper left, pins 1–5 down the left side, pins 6–10 up the right side and pad 11 on `TI_GND`. | Exact active-production MPN selected; confirm AISLER availability and assign |
| `U1102` | Texas Instruments | TXU0101DBVR | DBV, SOT-23-6 | Project-local `TXU0101_RANGE_DRIVER` | `Package_TO_SOT_SMD:SOT-23-6` | [TXU0101](https://www.ti.com/lit/ds/symlink/txu0101.pdf), SCES940A, Rev A | Exact mapping is pin 1 VCCA, pin 2 GND, pin 3 A, pin 4 B, pin 5 OE and pin 6 VCCB. The standard KiCad IPC-7351 DBV footprint is a compatible alternate to TI DBV0006A and has the correct 0.95 mm pitch, pad order and pin-1 marker. Accepted. | Exact active-production MPN selected; assign and confirm AISLER availability |
| `U1103` | Texas Instruments | [INA226AIDGSR](https://www.ti.com/product/INA226/part-details/INA226AIDGSR) | DGS, VSSOP-10 | Project-local `INA226_HIGH_RANGE` | `Package_SO:VSSOP-10_3x3mm_P0.5mm` | [INA226](https://www.ti.com/lit/ds/symlink/ina226.pdf), SBOS547B, Rev B | Pins 1–10 and their functions agree. The standard KiCad DGS/VSSOP footprint has the correct 3 mm × 3 mm body, 0.50 mm pitch, pad order and intrinsic pin-1 marker. Accepted. | Exact active-production MPN selected and visible in AISLER matching; final assignment pending |
| `U1104` | Texas Instruments | [INA228AIDGSR](https://www.ti.com/product/INA228/part-details/INA228AIDGSR) | DGS, VSSOP-10 | Project-local `INA228_LOW_RANGE` | `Package_SO:VSSOP-10_3x3mm_P0.5mm` | [INA228](https://www.ti.com/lit/ds/symlink/ina228.pdf), SLYS021A, Rev A | Pins 1–10 and their functions agree. The standard KiCad DGS/VSSOP footprint has the correct 3 mm × 3 mm body, 0.50 mm pitch, pad order and intrinsic pin-1 marker. Accepted. | Exact active-production MPN selected and visible in AISLER matching; final assignment pending |
| `U1105` | Texas Instruments | [SN74LVC2G08DCUR](https://www.ti.com/product/SN74LVC2G08/part-details/SN74LVC2G08DCUR) | DCU, VSSOP-8 | Project-local `74LVC2G08_POWER_CONTROL` | `Package_SO:VSSOP-8_2.3x2mm_P0.5mm` | [SN74LVC2G08](https://www.ti.com/lit/ds/symlink/sn74lvc2g08.pdf), Rev N | Exact mapping is pins 1/2 to gate 1 inputs, pin 7 gate 1 output, pins 5/6 to gate 2 inputs, pin 3 gate 2 output, pin 4 GND and pin 8 VCC. The standard KiCad DCU/VSSOP footprint has the correct 2.3 mm × 2 mm body, 0.50 mm pitch, pad order and intrinsic pin-1 marker. Accepted. | Exact active-production MPN selected; confirm AISLER availability and assign |
| `Q1101` | Alpha & Omega Semiconductor | AO3401A | SOT-23 | Project-local `AO3401A_LOW_RANGE_BYPASS` | `Package_TO_SOT_SMD:SOT-23` | [AO3401A](https://www.aosmd.com/res/data_sheets/AO3401A.pdf), Rev 3.1 | Exact mapping is pin 1 gate, pin 2 source and pin 3 drain. The standard KiCad IPC-7351 TO-236/SOT-23 footprint pad order, dimensions and pin-1 marker are compatible with the AOS package. Accepted. | Assign and confirm AISLER availability; pending |
| `R1101` | Yageo | PE2512FKF7W0R05L; 50 mΩ, 1%, 100 ppm/°C, 2 W | 2512 | Standard resistor | Project-local `R_Shunt_Yageo_PE2512_CurrentSense` | [Yageo part specification](https://www.yageogroup.com/component-documentation/download/specsheet/PE2512FKF7W0R05L) | Two-terminal symbol maps to pads 1 and 2. The manufacturer-derived footprint implements the PE2512 7 mΩ–910 mΩ land dimensions: 7.36 mm overall span, 4.06 mm inner gap and 1.65 mm × 3.68 mm pads. The root netlist and PCB agree on pad 1 `HIGH_SHUNT_P` and pad 2 `HIGH_SHUNT_N`. Accepted. | Accepted exact candidate; AISLER assignment pending |
| `R1102` | Bourns | CHP2512-FX-1R00ELF; 1 Ω, 1%, 100 ppm/°C, 3 W, RoHS | 2512 | Standard resistor | Project-local `R_Shunt_Bourns_CHP2512_CurrentSense` | [Bourns CHP data sheet](https://www.bourns.com/docs/product-datasheets/chp.pdf) | Two-terminal symbol maps to pads 1 and 2. The manufacturer-derived footprint implements the CHP2512 recommended 2.45 mm × 3.70 mm pads and 7.60 mm overall land span. The root netlist and PCB agree on pad 1 `HIGH_SHUNT_N` and pad 2 `TI_SWITCHED_TARGET_5V`. Accepted; the data-sheet copper-area requirement remains a PCB-layout control. | Accepted exact candidate; AISLER assignment pending |
| `R1103`, `R1104`, `R1106`, `R1107` | TBD | 100 kΩ; standard passive policy | 0603 | Standard resistor | `Resistor_SMD:R_0603_1608Metric` | Standard policy | Two-terminal mapping and standard KiCad footprint inspected; accepted | Assign as one grouped 100 kΩ part; pending |
| `R1105`, `R1108`, `R1112` | TBD | 10 kΩ; standard passive policy | 0603 | Standard resistor | `Resistor_SMD:R_0603_1608Metric` | Standard policy | Two-terminal mapping and standard KiCad footprint inspected; accepted | Assign as one grouped 10 kΩ part; pending |
| `R1110` | TBD | 100 kΩ `TARGET_SWITCH_EN` safe-state pull-down | 0603 | Standard resistor | `Resistor_SMD:R_0603_1608Metric` | Standard policy | Two-terminal mapping and standard KiCad footprint inspected; accepted | Assign in the grouped 100 kΩ AISLER part selection; pending |
| `R1111` | TBD | 66.5 kΩ, 1%, `U1101` current-limit programming resistor | 0603 | Standard resistor | `Resistor_SMD:R_0603_1608Metric` | TPS2559-Q1 current-limit programming | Two-terminal mapping and standard KiCad footprint inspected; accepted | Assign exact approved part; pending |
| `C1101` | TBD | 1 µF, X7R, ±20% or better, at least 10 V | 0603 | Standard capacitor | `Capacitor_SMD:C_0603_1608Metric` | TPS2559-Q1 input bypass | Two-terminal mapping and standard KiCad footprint inspected; accepted | Assign exact approved part; preserve adequate effective capacitance at 5 V bias |
| `C1102`–`C1107` | TBD | 100 nF, X7R, ±20% or better, at least 10 V | 0603 | Standard capacitor | `Capacitor_SMD:C_0603_1608Metric` | Principal-device local bypass | Two-terminal mapping and standard KiCad footprint inspected; accepted | Assign as one grouped 100 nF part; pending |

The engineering package review is complete for PC02. It accepts the listed
symbol pins, package families, footprint pad order and land patterns,
including the project-local PowerPAD and shunt footprints. Final PCB
placement, rotation, Kelvin routing, power/thermal copper and assembly-
rendering checks remain release-stage controls; AISLER stock and MPN
assignment remains a separate commercial selection step.

#### Verification

| Check | Evidence | Result |
|---|---|---|
| Requirements inspection | Standard Control Services 3.5, 3.5.1 and Appendix C.3 | Topology covers the required switching and two measurement ranges |
| Behaviour and safe-state analysis | Operating table, unpowered-state review and current schematic | Logic recorded and required `TARGET_SWITCH_EN` pull-down implemented as `R1110` |
| Manufacturer source screen and pin functions | Product pages, data sheets and applicable application documents summarized above | Pin functions and I2C addresses reviewed; TXU0101 closes the range-driver partial-power blocker, low-range alert integration is implemented, and exact shunt candidates support the analytical accuracy budget |
| Connectivity contract | `verification/contracts/PC02-target-5v-switch-and-two-range-monitor.yaml`, `verification/contracts/SYS01-power-events-to-rack-control.yaml`, canonical full-hierarchy netlist and `verification/baseline/Espruino_Harness_RevA_FullHierarchy_Connectivity.json` | Refreshed 2026-08-11: PC02 passes all 110 assertions and SYS01 passes all 3; complete PC01/PC02/SYS01 set passes 186 checks. `SYS01` confirms that `U1104.Alert`, `U1105.2B` and `U1201.GPB3` share `LOW_RANGE_OK_N`. |
| Full-hierarchy ERC | `verification/baseline/Espruino_Harness_RevA_FullHierarchy_ERC.rpt`, refreshed from the root schematic on 2026-08-12 | Accepted: zero errors and zero warnings |
| Symbol-to-footprint pin mapping | Manufacturer pin tables and package drawings, full-hierarchy netlist, project-local and installed KiCad footprints, and current PCB pad nets | U1101–U1105 and Q1101 pin functions, package pads and intrinsic pin-1 orientation agree. The project-local U1101 footprint implements the TI perimeter pads, exposed pad 11 and segmented paste opening. The manufacturer-derived R1101 and R1102 footprints implement their accepted two-terminal land patterns. Engineering package review complete; release-stage placement, Kelvin, copper and assembly checks remain. |
| Visual schematic review | `review-images/PC02-target-5v-switch-and-two-range-monitor.png` | Accepted current reviewed circuit capture |
| Electrical limits | Calculations above | Protection topology and analytical component-path voltage-drop, dissipation and accuracy budgets are supported; PCB/contact resistance, inrush and physical accuracy remain release measurements |

#### Open issues and accepted exceptions

- Confirm the TPS2559-Q1 no-via-in-pad assembly choice with AISLER during PCB
  review and place short, wide PowerPAD-to-ground copper with nearby ground
  vias. The project-local DRC0010K footprint and its top-view orientation,
  symbol mapping, 66.5 kΩ `ILIM` resistor, `TARGET_SWITCH_EN` pull-down,
  `TARGET_POWER_FAULT_N` and PC02 connectivity contract are implemented.
- Synchronize exact MPN metadata and complete component assignments together
  during the later board-wide AISLER BOM Assign stage. TPS2559-Q1 and
  SN74LVC2G08 availability remains to be confirmed; the selected INA226 and
  INA228 variants were visible in the AISLER matching results.
- Complete AISLER assignments and the release-stage PCB placement, rotation
  and assembly-rendering review. The PC02 engineering package and footprint
  review is complete. Pad-level Kelvin routing and the Bourns full-load copper
  area remain PCB implementation actions.
- Keep the combined PCB, connector and backplane resistance below the
  provisional 26 mΩ allocation, verify it from the completed PCB layout, and
  measure at least 4.75 V at `TI_SWITCHED_TARGET_5V` with a 5.00 V source and
  1.5 A Rev-A load. The AO3401A temperature coefficient is typical rather
  than guaranteed, so the physical test remains authoritative.
- Determine the maximum complete target-side capacitance, calculate the
  TPS2559-Q1 turn-on transient, provide the required local `EXT_5V` bulk
  capacitance and confirm the measured rail rise, rack-rail disturbance and
  observation delay on Rev A.
- Measure target-rail decay with TPS2559-Q1 and define the Target Power Monitor
  threshold and timeout that confirm the rail is off before power-cycle
  sequencing continues.
- Exercise valid target boot, radio and peripheral transients at the minimum
  current-limit tolerance, then verify overload, short-circuit, thermal-retry
  and `TARGET_POWER_FAULT_N` behaviour at the maximum tolerance.
- Implement and verify the firmware configuration for the `U1104` ±40.96 mV
  range, active-low latched shunt-overvoltage alert and accepted threshold.
  Enable the `U1201.GPB3` interrupt and verify the specified request-clear /
  `DIAG_ALRT`-read / MCP23017-capture-clear order.
- Verify both TXU0101 local decoupling capacitors and all partial-power states
  on Rev A. Its data-sheet pin mapping and KiCad footprint pad numbering now
  agree; the PC02 connectivity assertions are refreshed.
- The analytical low-range budget supports the proposed 1% shunts with a
  7.71% known worst-case subtotal at 100 µA. Characterize AO3401A bypass
  leakage, noise, thermal EMF, PCB leakage and zero-offset at 100 µA through
  55°C before accepting the stated minimum measurement.
- Configure INA228 for its ±40.96 mV shunt range and define conversion time,
  averaging and calibration. Treat INA226 saturation above 1.6384 A as an
  overload-region limitation and use `TARGET_POWER_FAULT_N` for protection.
- Confirm Rack Control I2C pull-ups and the total always-on
  `RACK_CONTROL_3V3` load in the Rack Control/backplane design.

No exceptions are accepted at this stage.

### 4.3 RC01 — Routing Fabric

**Purpose and requirements:** Implement the accepted 19 independently
controlled route-selection paths `RP01`–`RP19` between Target Interface route
entries R0–R6 and their legal Test Block endpoints. Every path shall default
open, pass bidirectional analogue and digital signals over the complete 0 V to
3.3 V harness range, remain isolated with the Routing Logic Supply Rail absent,
and preserve the required simultaneous configurations. See Controlled Routing
Sections 4, 5, 7, 9, 11 and 13 and the Combined Capability Connection Matrix
Sections 4, 7 and 9.
**Source schematic:** `routing_control.kicad_sch`, references `U601`–`U605`,
`C601`–`C605`, the 19 functional 100 kΩ `RPxx_EN` pull-downs and representative
test points `TP612`–`TP614`.
**Visual review:** Accepted after the redundant-resistor cleanup:
[`RC01-routing-fabric.png`](review-images/RC01-routing-fabric.png).
**Risk:** High
**Status:** Verified; the TMUX1511 circuit approach, current manufacturer
application material, exact `TMUX1511PWR` selection, PW package implementation,
100 nF decoupling-capacitor policy, 100 kΩ route-enable pull-down policy, visual
schematic and current full-hierarchy ERC have been reviewed and are suitable.
The board-wide 2.54 mm through-hole test-point policy and exact part are
accepted, and the DNP state is verified on all 43 test points in the saved
schematic hierarchy and current PCB. The independent RC01 connectivity contract
passes against a fresh root netlist. AISLER's interpretation of the test-point
DNP state remains a release-stage BOM-reconciliation issue and does not block
the schematic baseline.

#### Interfaces and domains

| Type | Signals or rails | Function |
|---|---|---|
| Route entries | `R0`–`R6` | Seven target-facing common route-entry nodes |
| Route destinations | `TI_ANALOG_ADC_IN`, `TI_ONEWIRE_DQ`, `TI_GPIO_LOOP_A_OUT`, `TI_SPI_MISO`, `TI_GPIO_LOOP_A_IN`, `TI_I2C_FB`, `TI_SPI_CS_ADC`, `TI_ONEWIRE_GPIO_A_FB`, `TI_GPIO_LOOP_B_OUT`, `TI_SPI_MOSI`, `TI_UART_A_TX`, `TI_SPI_SCK`, `TI_UART_A_RX`, `TI_ANALOG_PWM_OUT`, `TI_RGB_DATA`, `TI_GPIO_LOOP_B_IN`, `TI_I2C_INT`, `TI_SPI_CS_EXT`, `TI_ONEWIRE_GPIO_B_FB` | Accepted `RP01`–`RP19` Test Block endpoints |
| Control inputs | `RP01_EN`–`RP19_EN` | Active-high independent TMUX1511 channel controls from the routing controllers |
| Supply | `ROUTING_LOGIC_3V3` | Powers all five RC01 switch packages |
| Ground | `TI_GND` | Signal, control-bias and decoupling reference |

#### Key design issues

**Shared route-entry capacitance — accepted for the circuit approach; complete
path validation remains required.** Each R0–R6 entry is connected to every
TMUX1511 source pin assigned to that entry. An active route therefore sees the
active channel's maximum 6 pF on-capacitance plus the maximum 4 pF off-
capacitance of every alternative channel. The switch-only maximum contribution
is approximately 10 pF for the two-destination R0, R1, R4 and R5 entries,
14 pF for the three-destination R3 entry, and 18 pF for the four-destination R2
and R6 entries. These values exclude PCB, connector, daughter-board, protection
and Test Block capacitance. They do not challenge the selected device, but the
complete analogue, SPI, 1-Wire, UART, RGB and GPIO path budgets and prototype
tests shall use the fan-out totals rather than one channel's nominal
capacitance.

**Powered-off leakage and 3.6 V boundary — bounded and subject to physical
acceptance.** TMUX1511 powered-off protection maintains the signal path high
impedance and prevents ordinary ESD-diode back-power when `VDD = 0 V`. The
guaranteed powered-off signal range ends at 3.6 V, which equals the accepted
maximum `TI_TARGET_3V3` domain voltage. The data sheet permits up to 2 µA
powered-off I/O leakage per pin at that boundary. A deliberately conservative
19-channel RC01 aggregate is therefore 38 µA if every target-facing switch pin
simultaneously has worst-case leakage in the same direction. Rev A shall verify
that the supported partial-power sequences produce no functional or damaging
back-power, record the actual leakage and resulting unpowered-rail voltage, and
keep switching overshoot within the powered-off operating limit.

**Route-change charge injection and settling — implementation action.** The
data sheet gives 2 pC typical charge injection. The accepted reconfiguration
sequence establishes routes while target and peer drivers are inactive, which
prevents a route-change transient from becoming contention. Analogue tests
shall additionally allow the routed node to settle after `RP01` or `RP14`
changes and shall determine whether the first ADC conversion must be discarded.

**Simultaneous analogue and SPI operation — PCB and prototype action.** The
accepted analogue-plus-SPI configuration operates multiple switch channels at
the same time, including `RP01` and `RP04` in `U601`. TMUX1511 has substantial
typical bandwidth, off-isolation and crosstalk margin, but those figures do not
replace complete-board validation. Placement and routing shall separate the
analogue path from SPI clock and control edges, and Rev A shall compare analogue
results with SPI idle and active.

No application-note finding requires an architecture change. Netlist review
identified six copied 100 kΩ positions whose two pads were already on
`TI_GND`: `R603`, `R608`, `R13`, `R18`, `R23` and `R25`. They provided no
pull-down or isolation function and were removed on 2026-08-11. Their former
positions now directly connect `U601`–`U605.GND` and the deliberately disabled
`U605.SEL4` to `TI_GND`. Exact passive MPN selection remains a later RC01
implementation-review item.

#### Selected implementation

- `U601` implements `RP01`–`RP04`, `U602` implements `RP05`–`RP08`, `U603`
  implements `RP09`–`RP12`, `U604` implements `RP13`–`RP16`, and `U605`
  implements `RP17`–`RP19`. `U605` channel 4 is unused, its select input is
  grounded, and its signal pins are marked unconnected.
- Every selected channel is an independently controlled bidirectional 1:1
  switch. No shared address or select line couples route entries.
- Each switch has a local schematic 100 nF `ROUTING_LOGIC_3V3` decoupling
  capacitor. The data sheet accepts 0.1 µF to 10 µF from VDD to GND.
- Each implemented `RPxx_EN` input has a 100 kΩ external pull-down in addition
  to the TMUX1511 nominal 6 MΩ internal pull-down. With the switch's maximum
  ±2 µA control-input leakage considered alone, 100 kΩ develops no more than
  0.2 V, below the 0.45 V maximum input-low threshold. Routing-controller
  reset-state leakage and combined margin remain part of RC02 review.
- The accepted exact orderable device is `TMUX1511PWR`, the PW TSSOP-14 tape-
  and-reel variant. AISLER BOM Assign groups and assigns this part to all seven
  current PW-package instances: RC01 `U601`–`U605`, RC02 `U606` and TB07
  `U701`. This assignment accepts the RC01 devices commercially; RC02 and TB07
  retain their independent circuit-block reviews. The schematic value remains
  the functional base name `TMUX1511` while this baseline records the exact
  orderable MPN.

#### Operating logic and safe states

| Condition | Required and reviewed state |
|---|---|
| `ROUTING_LOGIC_3V3` absent or below the TMUX1511 operating range | Every RC01 signal path remains high impedance through powered-off protection for signal pins held within 0 V to 3.6 V |
| Routing controller reset, unpowered or configured as inputs | External 100 kΩ and internal nominal 6 MΩ pull-downs hold every implemented select input low; all paths remain open |
| Valid route state | At most one destination is enabled for each R0–R6 entry; other destinations remain open |
| Route change | Target and peer drivers inactive; old paths cleared and verified before a new path is enabled |
| Test complete or failed configuration | Drivers inactive before the selected paths are cleared and verified |
| Unused `U605` channel 4 | Select held low; S4 and D4 remain unconnected |

The TMUX1511 fixed logic thresholds accept the 3.3 V routing-controller
outputs with substantial high-level margin. Fail-safe control inputs prevent a
controller output from back-powering an unpowered switch, although RC01 and its
controllers normally share `ROUTING_LOGIC_3V3`.

#### Key calculations and limits

| Subject | Data-sheet or application-note basis | RC01 conclusion |
|---|---|---|
| Signal and supply range | VDD 1.5 V to 5.5 V; powered signal range 0 V to `VDD × 2` subject to 5.5 V maximum; powered-off range 0 V to 3.6 V | Suitable for the 3.3 V harness domain; 3.6 V is a no-margin powered-off boundary to be protected and measured |
| On-resistance | 2 Ω typical, 4.5 Ω maximum at 8 mA | Suitable for the high-impedance and protected Test Block loads; include 4.5 Ω in complete path budgets |
| Continuous signal current | ±25 mA maximum | Above normal routed signal currents; contention remains prohibited rather than treated as a valid load case |
| On/off capacitance | 6 pF maximum on and 4 pF maximum off | Fan-out contribution is 10 pF, 14 pF or 18 pF depending on route entry |
| Powered-off leakage | Up to ±2 µA per I/O pin over 0 V to 3.6 V | Conservative 19-target-pin aggregate 38 µA; physical partial-power verification required |
| On/off leakage while powered | 50 nA maximum on; 100 nA maximum off | Suitable at device level; complete analogue-node leakage remains a board-level check |
| Logic thresholds | `VIH` 1.2 V minimum; `VIL` 0.45 V maximum | Compatible with 3.3 V MCP23017 outputs; external pull-down margin accepted provisionally |
| Bandwidth and propagation | 3 GHz typical bandwidth and 67 ps typical propagation delay | Substantial device-level margin for the accepted SPI, UART, RGB and GPIO rates; PCB and attached loading determine the validated limits |
| Charge injection | 2 pC typical | Route before enabling drivers; allow analogue settling and assess first-sample discard |
| Crosstalk and off-isolation | Typical −90 dB channel crosstalk at 100 kHz and −75 dB off-isolation at 1 MHz | Supporting evidence only; verify the simultaneous analogue/SPI configuration on the completed board |

#### Manufacturer source and application review

The current [TMUX1511 product page](https://www.ti.com/product/TMUX1511) and
[Rev. B data sheet](https://www.ti.com/lit/ds/symlink/tmux1511.pdf) were
reviewed on 2026-08-10. The product page lists TMUX1511 as active and provides
the PW TSSOP-14 option. The data sheet is the authority for pin functions,
guaranteed electrical limits and powered-off behaviour.

| Manufacturer material | RC01 consequence |
|---|---|
| TMUX1511 data sheet, Rev. B | Confirms independent bidirectional channels, PW pinout, 0.1 µF to 10 µF decoupling, fixed logic thresholds, fail-safe control inputs, powered-off range and leakage, resistance, capacitance, current and timing limits. Its protocol-isolation example matches the RC01 use. |
| [Selecting the Correct Texas Instruments Signal Switch, Rev. E](https://www.ti.com/lit/an/szza030e/szza030e.pdf) | Confirms that configuration, signal/supply range, resistance, capacitance, leakage, bandwidth, charge injection, crosstalk, off-isolation and powered-off behaviour are the applicable selection criteria. RC01 satisfies the device-level screen; complete-board loading remains to be checked. |
| [Eliminate Power Sequencing with Powered-off Protection Signal Switches, Rev. C](https://www.ti.com/lit/ab/scda015c/scda015c.pdf) | Confirms that a switch without powered-off protection can back-power its supply and unintentionally pass signals. TMUX1511 is appropriate for the V2 target/routing partial-power boundary; data-sheet leakage and prototype evidence still bound acceptance. |
| [1.8-V Logic for Multiplexers and Signal Switches, Rev. C](https://www.ti.com/lit/pdf/SCAA126) | Confirms direct logic control without a translator when output-high and output-low margins satisfy the fixed thresholds. RC01 uses 3.3 V control and needs no translation. |
| [Enabling SPI-Based Flash Memory Expansion by Using Multiplexers, Rev. B](https://www.ti.com/lit/ab/scda016b/scda016b.pdf) | Identifies TMUX1511 as a suitable 1:1 SPI isolation switch based on low resistance and capacitance, high bandwidth, powered-off protection and logic compatibility. RC01 shall still validate its complete fan-out and PCB loading at the accepted SPI rate. |
| [Multiplexers and Signal Switches Glossary, Rev. B](https://www.ti.com/lit/an/slla471b/slla471b.pdf) | Supports the interpretation of bidirectionality, fail-safe logic, integrated pull-downs, leakage, charge injection and isolation terms; it adds no separate circuit requirement. |
| Selecting the Right Multiplexer for a Discrete PGA and Improve Stability Issues with Low-CON Multiplexers | The op-amp feedback applications do not apply directly. Their low-resistance and low-capacitance guidance supports the selected device and the requirement to include all shared-node capacitance. |
| Product-linked powered-off-protection and servo-drive technical articles | Supporting explanations only; they reinforce the authoritative powered-off application brief and add no new RC01 implementation requirement. |

#### Components and packaging

| References | Manufacturer | Exact orderable part | Package | KiCad symbol | KiCad footprint | Datasheet/revision | Pin/pad mapping | AISLER assignment |
|---|---|---|---|---|---|---|---|---|
| `U601`–`U605` | Texas Instruments | [`TMUX1511PWR`](https://www.ti.com/product/TMUX1511/part-details/TMUX1511PWR) | PW0014A, 14-pin TSSOP, 4.4 mm × 5.0 mm nominal body, 0.65 mm pitch | `Espruino_Harness_RevA:TMUX1511_PW` | `Package_SO:TSSOP-14_4.4x5mm_P0.65mm` | [TMUX1511 Rev. B, SCDS390B, March 2025](https://www.ti.com/lit/ds/symlink/tmux1511.pdf) | Accepted. Symbol pins agree exactly with the PW top-view table: `SEL1/S1/D1/SEL2/S2/D2/GND/D3/S3/SEL3/D4/S4/SEL4/VDD` on pins 1–14. The footprint has 14 sequential pads, the required 0.65 mm pitch, compatible 4.4 mm × 5.0 mm body outline and intrinsic pin-1 indication. Its IPC pads are 1.475 mm × 0.40 mm versus TI's 1.50 mm × 0.45 mm example; TI explicitly permits IPC-7351 alternate designs. | Assigned in AISLER on 2026-08-11 as one seven-component group covering `U601`–`U606` and `U701`; RC01 allocation is `U601`–`U605` |
| `C601`–`C605` | AISLER-selected commodity MLCC | Manufacturer intentionally open; controlled by `AISLER_MPN = 100nF 10% 16V X7R 0603` | 0603 (1608 metric) | `Device:C` | `Capacitor_SMD:C_0603_1608Metric` | TMUX1511 Rev. B requires 0.1 µF to 10 µF local VDD bypass; final supplied-part data applies at release | Accepted. Non-polarized two-terminal mapping agrees with the standard footprint. The 100 nF nominal value meets the TMUX1511 recommendation; 16 V provides nearly 5× rating margin over `ROUTING_LOGIC_3V3`, and X7R/10% controls dielectric and initial tolerance. Local placement and short VDD/GND connections remain PCB action `PCB-RC01-01`. | KiCad Smart Match requirement accepted. The current AISLER capture retains an earlier generic assignment for `C601`–`C605`; reject/reassign it and verify all parameters during final BOM reconciliation. |
| Nineteen functional `RPxx_EN` pull-downs: `R601`, `R602`, `R604`–`R607`, `R609`, `R610`, `R11`, `R12`, `R14`–`R17`, `R19`–`R22`, `R24` | AISLER-selected commodity resistor | Manufacturer intentionally open; controlled by `AISLER_MPN = 100k 0603 1% 0.1W` | 0603 (1608 metric), 0.1 W | `Device:R` | `Resistor_SMD:R_0603_1608Metric` | TMUX1511 Rev. B control-input limits and [AISLER Smart Match resistor parameters](https://community.aisler.net/t/documenting-parts/56) | Accepted. The refreshed hierarchy confirms exactly one 100 kΩ pull-down from each `RP01_EN`–`RP19_EN` to `TI_GND` and the standard two-terminal mapping. At the 1% high limit, 2 µA leakage develops 0.202 V, below the 0.45 V maximum input-low threshold without relying on the internal pull-down. Dissipation at 3.3 V is approximately 0.109 mW, more than 900 times below 0.1 W. | KiCad Smart Match requirement accepted on exactly the nineteen listed references. Reassign the current generic AISLER 100 kΩ entries and verify tolerance, power and package during final BOM reconciliation. |
| `TP612`–`TP614` | Würth Elektronik | [`61300111121`](https://www.we-online.com/components/products/datasheet/61300111121.pdf) | One-position, single-row, vertical 2.54 mm THT pin header; 0.64 mm square pin, 3.0 mm PCB tail and 6.0 mm exposed post | `Connector:TestPoint` | `Connector_PinHeader_2.54mm:PinHeader_1x01_P2.54mm_Vertical` | Würth `61300111121`, drawing revision 003.001, 2023-08-15 | Accepted under board-wide decision `INT02`. The KiCad footprint uses a 1.0 mm drill and 1.7 mm pad; the drill lies within the manufacturer's recommended 1.10 ±0.15 mm hole range and gives a 0.35 mm nominal annular ring. The single electrical pin maps directly to pad 1. | Exact `MPN = 61300111121` and DNP state are verified on all 43 board test points, including RC01 `TP612`–`TP614`. Retain them in the overall KiCad BOM and hand-fit after manufacture. AISLER exclusion interpretation remains a final BOM-reconciliation check. |

#### Verification

| Check | Evidence | Result |
|---|---|---|
| Requirements inspection | Controlled Routing and Combined Capability Connection Matrix | Accepted: the selected five-switch approach implements the complete 19-path inventory and preserves the required route-entry grouping |
| Behaviour and safe-state analysis | Operating table, partial-power review and current full-hierarchy normalized connectivity | Circuit approach accepted; powered-off leakage, 3.6 V boundary and complete controller-reset margin remain physical/RC02 checks |
| Manufacturer source screen | Sources and conclusions above | Accepted for circuit approach; no architecture or topology change required |
| Connectivity contract | `verification/contracts/RC01-routing-fabric.yaml` and `verification/baseline/Espruino_Harness_RevA_FullHierarchy_Connectivity.json` | Accepted: 164 RC01 checks pass against the fresh root netlist: 116 pin/net, 29 component-value and 19 forbidden-direct-path assertions; the complete thirteen-contract set passes 1071 checks |
| Full-hierarchy ERC | `verification/baseline/Espruino_Harness_RevA_FullHierarchy_ERC.rpt`, refreshed from the root schematic on 2026-08-12 | Accepted: zero errors and zero warnings after removal of the six redundant ground-to-ground resistors and application of the board-wide test-point metadata |
| Symbol-to-footprint pin mapping | TMUX1511 Rev. B PW pin table, PW0014A package drawing, project-local symbol, installed KiCad footprint and current PCB pads | Accepted: pins 1–14, package family, body size, pitch, pad order and pin-1 orientation agree; the footprint's IPC land pattern is a permitted alternate to TI's example pattern |
| Visual schematic review | `review-images/RC01-routing-fabric.png` | Accepted current reviewed circuit capture after removal of the six redundant resistors |
| Electrical limits | Calculations above | Device-level margins supported; complete path and prototype evidence pending |

#### Open issues and accepted exceptions

- The accepted DNP state is present on all 43 `INT02` test points in the saved
  hierarchy and PCB, but the latest AISLER upload did not exclude them as
  expected. Resolve the importer or assignment-state behaviour and verify the
  exclusion during final BOM reconciliation; retain the exact test-point MPNs
  in the overall KiCad BOM for hand fitting. Also reassign the current generic AISLER entries
  for `C601`–`C605` and the nineteen route-enable pull-downs to their accepted
  Smart Match requirements. The six redundant ground-to-ground positions have
  been removed and do not belong in the BOM or PCB.
- Include the maximum fan-out capacitance and 4.5 Ω switch resistance in every
  affected complete Test Block path budget.
- Define the analogue route-settling and first-sample policy from prototype
  evidence.
- Measure powered-off leakage and unpowered-rail voltage across the supported
  target/routing power sequences, including the 3.6 V boundary.
- Validate analogue performance with the required concurrent SPI activity and
  retain the maximum proven SPI, UART, 1-Wire, RGB and GPIO rates.

No exception is accepted at this stage.

### 4.4 RC02 — Routing controllers and fixed I2C isolation

**Purpose and requirements:** Provide the target-owned direct I2C control
plane at `RCTRL0 = 0x21` and `RCTRL1 = 0x22`, qualify the target, Test Block
and Routing Logic 3.3 V rails before connecting the fixed I2C branches, and
hold both routing controllers in hardware reset until the Routing Logic Supply
Rail is valid. Hardware Clear shall return every route-control output to its
safe inactive state independently of responsive target firmware. See
Controlled Routing Sections 3, 8, 9, 10 and 13 and Standard Control Services
Sections 5 and 8.
**Source schematic:** `routing_control.kicad_sch`, references `U606`–`U611`,
`C606`–`C611`, `C621`–`C623`, `R620`–`R623`, `R630`–`R634`, `JP610`–`JP615`
and diagnostic points `TP601`–`TP611`; the cross-sheet Hardware Clear request
stage is `Q1203`, `R1209` and `R1210` on `rack_control.kicad_sch`.
**Visual review:** Accepted full-sheet
[`RC02-routing-controllers-and-fixed-i2c-isolation.png`](review-images/RC02-routing-controllers-and-fixed-i2c-isolation.png)
and cross-sheet
[`RC02-hardware-clear-request.png`](review-images/RC02-hardware-clear-request.png).
**Risk:** High
**Status:** Verified at schematic-baseline level. Manufacturer-source review,
the corrected TPS3808 SENSE bypassing and address notes, the independent
Hardware Clear implementation, visual review, full-hierarchy ERC and the RC02
connectivity contract are accepted. PCB-layout and physical waveform/loading
actions remain open in Section 6.

#### Functional control, signal and safety flow

This subsection maps the accepted functional flow onto the implemented RC02
references. It introduces no additional route or behaviour; the owning
Controlled Routing and Standard Control Services specifications remain
authoritative.

Target firmware owns route configuration. Commands and controller-state
readback use the permanently assigned direct I2C path rather than any `RPxx`
route-selection path:

```text
Target firmware / Target Support Module
        |
        | bidirectional TI_I2C_SDA / TI_I2C_SCL
        v
R620 / R621 target-domain pull-ups
        |
        | U606 channels 1 and 2 (IP01 / IP02)
        | enabled by U607 only while TI_TARGET_3V3 is valid
        v
ROUTE_I2C_SDA / ROUTE_I2C_SCL
        |
        +----> U610 / RCTRL0 / 0x21
        |          +----> RP01_EN-RP16_EN
        |
        +----> U611 / RCTRL1 / 0x22
        |          +----> RP17_EN-RP19_EN
        |          +----> UP01_EN-UP04_EN
        |
        | U606 channels 3 and 4 (IP03 / IP04)
        | enabled by U608 only while TEST_BLOCK_3V3 is valid
        v
Standard Test Block I2C segment
```

`R622` and `R623` pull the routing-controller segment up to
`ROUTING_LOGIC_3V3`. Pull-ups on an enabled target or Test Block segment act
in parallel and are therefore part of the complete bus-current and rise-time
calculation. `U606` is itself powered from `ROUTING_LOGIC_3V3`; if that rail is
absent, its powered-off protection holds all four fixed I2C paths high
impedance even if an endpoint rail remains present.

The routing controllers convert the requested state into individual
active-high switch controls:

```text
verified U610 / U611 GPIO state
        |
        +----> RP01_EN-RP19_EN ----> U601-U605 routing-fabric channels
        |                                  |
        |                                  v
        |                         one legal R0-R6 destination
        |
        +----> UP01_EN-UP04_EN ----> U701 Block 7 local switching
```

`JP610`–`JP612` establish the `U610` default address `0x21`; `JP613`–`JP615`
establish the `U611` default address `0x22`. Firmware preloads the relevant
`OLAT` registers low before changing `IODIR` from inputs to outputs, reads the
actual `GPIO` state back, and enables target or Test Block drivers only after
the complete route state is verified. Controller readback proves the control
pin state; it does not prove TMUX1511 continuity or isolation.

Rail qualification and Hardware Clear form an out-of-band safety path:

```text
TI_TARGET_3V3 invalid                TEST_BLOCK_3V3 invalid
        |                                      |
        v                                      v
U607 RESET asserted                    U608 RESET asserted
        |                                      |
TARGET_I2C_ISO_EN low                  TEST_I2C_ISO_EN low
        |                                      |
U606 IP01 / IP02 open                  U606 IP03 / IP04 open

ROUTING_LOGIC_3V3 invalid       Supervisor Hardware Clear request
        |                       U1201.GPA6 -> R1209 -> Q1203
        v                                      |
U609 RESET asserted                            |
        +------------------+-------------------+
                           v
                    ROUTE_CLEAR_N low
                           |
                           v
                  U610 and U611 in reset
                           |
                           v
                controller GPIO high impedance
                           |
                           v
        external 100 kΩ RPxx_EN / UPxx_EN pull-downs
                           |
                           v
                 all controlled switches open
```

`R630/R631` and `R632/R633` provide the pull-up and disabled-state bias for
the two fixed-I2C enable groups. `R634` pulls `ROUTE_CLEAR_N` high only after
`U609` releases it. `C606`–`C611` are the local active-device supply bypasses;
`C621`–`C623` separately filter `U607`–`U609.SENSE` with 4.7 nF to `TI_GND`.
`TP601`–`TP611` expose representative rails, I2C, clear, interrupt and enable
states for bring-up without participating in normal control flow.

| References | Functional role |
|---|---|
| `U606` | Four-channel powered-off-protected fixed I2C boundary: IP01/IP02 connect target I2C to routing I2C and IP03/IP04 connect routing I2C to the Standard Test Block segment. |
| `U607` | Qualifies `TI_TARGET_3V3` and releases `TARGET_I2C_ISO_EN` after the rail-valid delay. |
| `U608` | Qualifies `TEST_BLOCK_3V3` and releases `TEST_I2C_ISO_EN` after the rail-valid delay. |
| `U609` | Qualifies `ROUTING_LOGIC_3V3` and releases the common active-low `ROUTE_CLEAR_N` reset after the rail-valid delay. |
| `U610`, `U611` | Target-owned MCP23017 routing controllers. `U610` owns `RP01`–`RP16`; `U611` owns `RP17`–`RP19` and `UP01`–`UP04`. |
| `R620`–`R623` | Target-side and routing-side direct-I2C pull-ups; their enabled parallel combinations set bus sink current and rise time. |
| `R630`–`R634` | TPS3808 output pull-ups and disabled-state bias: paired pull-up/pull-down networks for the two U606 enable groups and the pull-up for `ROUTE_CLEAR_N`. |
| `Q1203`, `R1209`, `R1210` | Rack Control-domain open-drain Hardware Clear stage. `U1201.GPA6` drives the `DMG2302UKQ-7` gate through 10 kΩ; 100 kΩ holds the gate inactive and the NMOS drain asserts `ROUTE_CLEAR_N`. |
| `JP610`–`JP615` | Reworkable hardware address straps establishing controller defaults `0x21` and `0x22`. |
| `C606`–`C611` | Local 100 nF active-device supply bypasses. |
| `C621`–`C623` | Separate 4.7 nF TPS3808 SENSE-to-`TI_GND` bypass capacitors for `U607`–`U609`. |
| `TP601`–`TP611` | DNP/hand-fit diagnostic access to the principal rail, I2C, clear, interrupt and enable signals. |
| RC01 and TB07 switch-control pull-downs | The nineteen `RPxx_EN` 100 kΩ pull-downs and `R705`–`R708` on `UP01_EN`–`UP04_EN` hold all controlled switch inputs inactive while `U610/U611` are reset or configured as inputs. |

#### Manufacturer source and application review

The current manufacturer product pages, data sheets, associated application
material and published MCP23017 errata were reviewed on 2026-08-11, with the
Q1203 exact-part review completed on 2026-08-12. Third-party data-sheet mirrors
were used only to discover source material; the evidence below cites the
original manufacturer documents.

| Manufacturer material | RC02 consequence |
|---|---|
| [MCP23017/MCP23S17 data sheet, DS20001952D](https://ww1.microchip.com/downloads/aemDocuments/documents/APID/ProductDocuments/DataSheets/MCP23017-Data-Sheet-DS20001952.pdf) | Confirms the `MCP23017-E/SO` wide-SOIC package, address pins, reset timing, I2C modes and reset defaults. `IODIRA` and `IODIRB` reset to inputs and the output latches reset low, so the external 100 kΩ `RPxx_EN` pull-downs retain the hardware-safe open state while either controller is reset or unconfigured. |
| [AN1043 — Unique Features of the MCP23X08/17 GPIO Expanders](https://ww1.microchip.com/downloads/en/AppNotes/01043a.pdf) | Confirms that `IODIR = 1` disables the output driver, `IODIR = 0` drives the corresponding `OLAT` value, and a `GPIO` read observes the actual pad state. Firmware shall leave the pins as inputs, write zero to both relevant output latches, then configure the allocated pins as outputs and read `GPIO` back before enabling any route. Reading only `OLAT` is not sufficient operational verification. Firmware shall also set and verify the intended `IOCON.BANK` and `IOCON.SEQOP` conventions rather than assuming a library default. |
| [AN1081 — Interfacing a 4x4 Matrix Keypad with an 8-Bit GPIO Expander](https://ww1.microchip.com/downloads/en/AppNotes/01081a.pdf) | Screened because Microchip associates it with the MCP23X17 family. Its keypad scanning and interrupt-on-change sequence does not apply to the routing controllers. It reinforces that writes to `GPIO` update the output latch and reads of `GPIO` return the pin state; it adds no RC02 circuit requirement. |
| [MCP23017 Rev. A Silicon Errata, DS80252A](https://www.microchip.com/content/dam/mchp/documents/OTH/ProductDocuments/MISC/80252A.pdf) | Revision A0 could falsely acknowledge non-address data on a shared I2C bus. Microchip states that date code `0542` and earlier is affected and `0543` and later is corrected. Current production parts require no workaround, but obsolete, reclaimed or otherwise untraceable date-code `0542` or earlier devices shall not be fitted. |
| [TPS3808 data sheet, Rev. M](https://www.ti.com/lit/ds/symlink/tps3808.pdf) | Confirms the `TPS3808G30DBVR` DBV SOT-23-6 pinout, nominal 2.79 V falling threshold, open-drain active-low output, 10 kΩ to 1 MΩ permitted RESET pull-up, open-`CT` nominal 20 ms release delay, 100 nF local VDD bypass and 1 nF to 10 nF SENSE bypass recommendation. `U607`–`U609` therefore each require a dedicated SENSE-to-`TI_GND` bypass capacitor in addition to `C607`–`C609`. A nominal 4.7 nF 0603 capacitor is the proposed value. |
| [Voltage Supervisors (Reset ICs): Frequently Asked Questions, SLVAE47A](https://www.ti.com/lit/pdf/slvae47) | Supports using the supervisor output to hold an enable or reset inactive until the monitored rail is valid, and requires output pull-up current, supervisor leakage, load-input leakage, `VOL`/`VIL`, `VOH`/`VIH`, threshold accuracy, hysteresis and indeterminate output below the power-on-reset voltage to be considered explicitly. |
| [Mitigating the Indeterminate Output of a Voltage Supervisor During Power Up/Down, SNVA845](https://www.ti.com/lit/pdf/snva845) | An active-low supervisor output is undefined below its power-on-reset voltage because its internal pull-down device cannot yet operate. No extra JFET stage is required here: each TPS3808, its output pull-up and the controlled TMUX1511 or MCP23017 share `ROUTING_LOGIC_3V3`. Below the approximately 0.8 V TPS3808 power-on-reset boundary, the divided output remains below the TMUX1511 1.2 V input-high threshold and the controlled devices are themselves below their operating range. Validate this conclusion on the actual rail ramp and power-down waveform. |
| [Setting the SVS Voltage Monitor Threshold, SLVA521](https://www.ti.com/lit/pdf/slva521) | Confirms that threshold selection must include rail tolerance, supervisor accuracy and the minimum operating voltage of the protected circuitry. The fixed 2.79 V nominal threshold provides substantial separation from a valid nominal 3.3 V rail and asserts while the routing devices still have supply headroom. It qualifies rail presence; it does not replace endpoint-specific power-good or functional checks. |
| [Choosing an Appropriate Pull-up/Pull-down Resistor for Open Drain Outputs, SLVA485](https://www.ti.com/lit/pdf/slva485) | Requires the asserted output to satisfy `VOL < VIL` at a bounded sink current and the released output to satisfy `VOH > VIH` after leakage and load currents. The current 10 kΩ pull-up and 100 kΩ disabled-state pull-down produce approximately 3.0 V released, well above the TMUX1511 1.2 V `VIH`. TPS3808 guarantees at most 0.4 V at 1 mA versus the TMUX1511 0.45 V `VIL`; the approximately 0.33 mA circuit current should produce a lower voltage, but the 50 mV guaranteed-limit separation is small and remains a layout and prototype measurement action. |
| [TMUX1511 product page](https://www.ti.com/product/TMUX1511), [Rev. B data sheet](https://www.ti.com/lit/ds/symlink/tmux1511.pdf), [1.8-V Logic for Multiplexers and Signal Switches, SCAA126C](https://www.ti.com/lit/pdf/SCAA126), [Selecting the Correct Texas Instruments Signal Switch, SZZA030E](https://www.ti.com/lit/pdf/SZZA030) and [Powered-off Protection Signal Switches, SCDA015C](https://www.ti.com/lit/ab/scda015c/scda015c.pdf) | Confirm that TMUX1511 supports I2C, independent bidirectional channels, fixed 1.2 V/0.45 V logic thresholds, fail-safe controls, powered-off high-impedance isolation to 3.6 V, 4.5 Ω maximum on-resistance and approximately 3.3 pF typical on-capacitance. The fixed-isolation topology is suitable; include switch resistance and capacitance in the complete I2C calculation and keep every partial-power signal within 3.6 V. The remaining product-linked PGA, SPI-flash, op-amp-stability and general glossary material adds no separate RC02 requirement. |
| [I2C Bus Pull-up Resistor Calculation, SLVA689](https://www.ti.com/lit/an/slva689/slva689.pdf) | Requires pull-ups to be strong enough to meet rise time but weak enough for every participant to sink the bus low. Two enabled 4.7 kΩ branches give 2.35 kΩ; three give approximately 1.57 kΩ. At 3.3 V and a 0.4 V low level these draw approximately 1.23 mA and 1.85 mA respectively, below the 3 mA standard/fast-mode basis. At 400 kHz, the 300 ns rise-time limit permits approximately 151 pF at 2.35 kΩ or 225 pF at 1.57 kΩ. At 100 kHz the calculated resistance limits exceed the I2C 400 pF bus limit, so 400 pF remains the governing maximum. Measure the completed configurations rather than accepting the resistor value alone. |
| [DMG2302UKQ product page](https://www.diodes.com/part/view/DMG2302UKQ) and [data sheet, DS40354](https://www.diodes.com/datasheet/download/DMG2302UKQ.pdf) | Select exact orderable `DMG2302UKQ-7` for `Q1203`. Its SOT-23 gate/source/drain mapping is 1/2/3 and matches the implemented symbol and footprint. The 10 kΩ/100 kΩ network gives approximately 3.0 V gate drive; the device specifies 120 mΩ maximum `RDS(on)` at 2.5 V gate drive and 25 °C, at a test current vastly above the approximately 0.33 mA Hardware Clear sink current. This removes the generic 2N7002's unsupported low-gate-drive assumption while retaining the prototype `ROUTE_CLEAR_N` low-level measurement. |

#### Exact active components and package mapping

| References | Exact MPN | Package and KiCad footprint | Review result |
|---|---|---|---|
| `U606` | `TMUX1511PWR` | PW, 14-pin TSSOP; `Package_SO:TSSOP-14_4.4x5mm_P0.65mm` | Pin mapping and grouped AISLER selection accepted with RC01. |
| `U607`–`U609` | `TPS3808G30DBVR` | DBV, SOT-23-6; `Package_TO_SOT_SMD:SOT-23-6` | Data-sheet top-view pin table and footprint pad numbering agree. Exact schematic MPN metadata present. |
| `U610`, `U611` | `MCP23017-E/SO` | SO, 28-pin wide SOIC; `Package_SO:SOIC-28W_7.5x17.9mm_P1.27mm` | Data-sheet pin table and footprint pad numbering agree. Exact schematic MPN metadata present. |
| `Q1203` | `DMG2302UKQ-7` | SOT-23; `Package_TO_SOT_SMD:SOT-23` | Gate/source/drain pins 1/2/3 agree with the data sheet and implemented netlist. Exact value and MPN metadata present. |

The 100 nF and 4.7 nF capacitors and the pull-up, pull-down and series
resistors use standard 0603 footprints. Their values are controlled by the
schematic; final manufacturer assignment remains part of BOM reconciliation.

#### Application-review outputs and retained physical checks

- The three required TPS3808 SENSE bypass capacitors are implemented as
  `C621`–`C623`, 4.7 nF 0603, while `C607`–`C609` remain separate 100 nF VDD
  bypass capacitors.
- The displayed `RCTRL1` address-jumper defaults now read `JP613 A0 default 0`,
  `JP614 A1 default 1` and `JP615 A2 default 0`, preserving address `0x22`.
- The independent Hardware Clear path is implemented from `U1201.GPA6`
  through `R1209`, `Q1203` and `R1210`, with exact
  `Q1203 = DMG2302UKQ-7` metadata.
- Exact schematic MPN metadata is present for `U606`–`U611` and `Q1203`.
- Treat MCP23017 initialization and route-state readback as part of the
  controlled-routing firmware contract: preload zero, establish output
  direction, read actual GPIO state, then enable only an accepted route set.
- Validate TPS3808 assert and release waveforms, SENSE transient filtering,
  output-low margin and route-clear timing across cold start, brownout and
  power-down. Validate direct-I2C rise time, low level and current with every
  permitted combination of target, routing and Test Block pull-ups.

#### Verification and acceptance

| Evidence | Result |
|---|---|
| Requirements and manufacturer review | Accepted against Controlled Routing and Standard Control Services, including MCP23017, TPS3808, TMUX1511 and DMG2302UKQ manufacturer sources. |
| Full-hierarchy ERC | Accepted root report dated 2026-08-12: zero errors and zero warnings. |
| Connectivity contract | `verification/contracts/RC02-routing-controllers-and-fixed-i2c-isolation.yaml` passes 210 checks: 160 pin/net, 39 component-value and 11 forbidden-direct-path assertions. The complete thirteen-contract set passes all 1071 checks. |
| Visual schematic review | Accepted full Routing Control sheet and focused cross-sheet Hardware Clear request-stage images linked above. |
| Package and metadata review | Exact active-device MPNs and symbol/footprint pin mappings accepted as recorded above. |
| Remaining work | Physical waveform, I2C loading, layout, BOM assignment and assembly checks remain in the PCB action and release registers; they do not reopen the accepted schematic topology. |

No RC02 exception is accepted at this stage.

### 4.5 TB01 — Digital GPIO loopback

**Purpose and requirements:** Provide two independent, concurrently usable
target-output-to-target-input loopback paths for digital output, input, pulse,
shift and event testing. Each path shall retain 470 Ω series protection, a
removable 2.54 mm hard-isolation shunt and diagnostic access on both external
sides. See Standard Test Blocks Section 6.1 and the Combined Capability
Connection Matrix GPIO-loopback configuration.
**Source schematic:** `standard_test_blocks.kicad_sch`, references `R101`,
`R102`, `JP101`, `JP102` and `TP101`–`TP104`.
**Visual review:** Accepted focused
[`TB01-digital-gpio-loopback.png`](review-images/TB01-digital-gpio-loopback.png).
**Risk:** Standard
**Status:** Verified at schematic-baseline level. Requirements, V1 functional
evidence, circuit operation, exact parts, package mappings, visual review,
full-hierarchy ERC and the deterministic connectivity contract are accepted.
The draft PCB is synchronized with the accepted components and nets; layout
and completed-board measurements remain open in Section 6.

#### V1 evidence and Rev-A boundary

Both completed V1 harnesses proved the two-pair 470 Ω loopback pattern through
the shared `gpio_block1` tests. Retained results cover static high/low reads,
edge watches, `digitalPulse` and `shiftOut`. The deliberate removal of the V1
loopback links caused the expected high-state failures, and restoring the links
restored passing results. This is useful positive and negative physical
evidence for the circuit function and hard-isolation concept.

The V1 passive components were through-hole. That construction is not package
evidence for Rev A: `R101` and `R102` are deliberately SMD 0603 parts. The
two-pin isolation headers, removable shunts and individual diagnostic pins
remain through-hole because they are user-operated mechanical interfaces.

Primary retained V1 evidence:

- `tests/Results/gpio_block1/Initial_runs.md`
- `docs/handoff/2026-06-25-esp32-family-tests.md`
- `tests/repl/gpio_block1/`

#### Implemented functional flow

```text
TI_GPIO_LOOP_A_OUT -- TP101 -- R101 470 Ω -- JP101 + fitted shunt -- TP102 -- TI_GPIO_LOOP_A_IN
TI_GPIO_LOOP_B_OUT -- TP103 -- R102 470 Ω -- JP102 + fitted shunt -- TP104 -- TI_GPIO_LOOP_B_IN
```

The saved hierarchy implements those two paths exactly. `R101.2/JP101.1` and
`R102.2/JP102.1` are private intermediate nets. Removing either shunt opens
only its own loopback. The block adds no supply connection, pull-up or
pull-down, and the two pairs are not joined.

The complete Target Interface configuration still depends on the accepted
routing one-hot rules: `RP03`, `RP05`, `RP09` and `RP16` select the four TB01
endpoints. Firmware shall configure the intended input directions and verified
route state before driving either loopback output.

#### Electrical and fault review

At nominal 3.3 V, an accidental opposite-level output configuration is limited
by 470 Ω to approximately 7.0 mA before including output-driver and switch
resistance. At 3.6 V and the proposed resistor's 1% minimum value, the
conservative resistor-only current is approximately 7.7 mA and its dissipation
approximately 28 mW. This is below the selected 0.1 W resistor rating with more
than 3.5:1 power margin. It limits rather than makes output contention safe;
the required direction and route sequencing remains mandatory.

The additional 470 Ω is negligible for static CMOS input sensing. The V1
edge, pulse and shift results support the functional pattern, while maximum
Rev-A pulse and shift rates remain a completed-board measurement because the
TMUX1511, Target Interface, daughter-board and PCB capacitances are new.

#### Exact components and package mapping

| References | Selected part | Package and KiCad footprint | Review result |
|---|---|---|---|
| `R101`, `R102` | Yageo [`RC0603FR-07470RL`](https://www.yageogroup.com/component-documentation/download/specsheet/RC0603FR-07470RL), 470 Ω, 1%, 100 ppm/°C, 0.1 W | 0603/1608; `Resistor_SMD:R_0603_1608Metric` | Accepted Rev-A SMD part. Manufacturer dimensions are 1.6 mm × 0.8 mm; the standard KiCad 0603 footprint is compatible. Exact MPN and data-sheet metadata are present in the saved schematic. |
| `JP101`, `JP102` | Würth Elektronik [`61300211121`](https://www.we-online.com/components/products/datasheet/61300211121.pdf), two-position straight 2.54 mm header | Project-local `LOOPBACK_ISOLATION_HEADER`; THT, 0.64 mm square pins; `Connector_PinHeader_2.54mm:PinHeader_1x02_P2.54mm_Vertical` | Accepted header. The 1.0 mm KiCad drills lie within the manufacturer's 1.10 ±0.15 mm recommendation; pad pitch and numbering agree. Exact MPN metadata is present. The project-local symbol preserves pins 1/2 and removes dependence on modified global-library copies. |
| One fitted shunt per `JP101`/`JP102` | Würth Elektronik [`60900213421`](https://www.we-online.com/components/products/datasheet/60900213421.pdf), black 2.54 mm jumper with test point | Removable accessory fitted over the two header contacts | Accepted proposed normal-state shunt. Record as `SHUNT_MPN` on each owning header so the deterministic KiCad BOM can account for one accessory per header. Hand fit after manufacture. |
| `TP101`–`TP104` | Würth Elektronik `61300111121` | THT single pin; `Connector_PinHeader_2.54mm:PinHeader_1x01_P2.54mm_Vertical` | Already accepted by board-wide decision `INT02`; DNP records hand fitting rather than absence from the completed board. |

No active-device application note applies to TB01. The authoritative sources
are the governing functional specification, retained V1 evidence and the
manufacturer component drawings/specifications above.

#### Verification state

| Evidence | Result |
|---|---|
| Requirements and functional review | Accepted circuit approach; no architecture change required. |
| V1 prototype evidence | Accepted as proof of the two-pair 470 Ω functional pattern, including link-removal negative control; not used as Rev-A package proof. |
| Connectivity contract | `verification/contracts/TB01-digital-gpio-loopback.yaml` passes 28 checks against a fresh full-hierarchy export: 12 pin/net, 8 component-value and 8 forbidden-direct-path assertions. The accepted thirteen-contract baseline passes all 1071 checks. |
| Package review | Accepted SMD resistors, THT headers, shunts and existing test pins are compatible with their intended roles and footprints. |
| Full-hierarchy ERC | Accepted root report dated 2026-08-12: zero errors and zero warnings after migrating `JP101/JP102` to the project-local symbol. |
| Visual schematic review | Accepted focused image linked above; both paths, values, endpoints, assembly-stage DNP test points and operating notes are legible. |
| PCB synchronization | Accepted: the current PCB contains exactly one each of `R101`, `R102`, `JP101` and `JP102`, with the accepted values, footprints, MPN/accessory metadata and pad nets. The board remains an unrouted provisional placement, so final physical placement is still open. |
| Remaining work | Complete the layout and physical checks in Section 6. |

#### Open issues and accepted exceptions

- Measure the complete Rev-A loopback waveform at the required pulse and shift
  rates after routing, including the routing fabric and target daughter board.

No TB01 exception is accepted at this stage.

### 4.6 TB02 — Analogue/PWM feedback

**Purpose and requirements:** Convert a target-generated PWM signal into a
stable `ANALOG_FB` voltage that can be measured concurrently by the selected
target ADC and MCP3008 CH0. Provide independent hard isolation of the PWM
source and both ADC branches, a 0 V to 3.3 V external-stimulus input, and
diagnostic access to every functional node. See Standard Test Blocks Section
6.2 and the Combined Capability Connection Matrix analogue-feedback
configuration.
**Source schematic:** `standard_test_blocks.kicad_sch`, references `R201`,
`C201`, `J201`, `JP201`–`JP203` and `TP201`–`TP205`; cross-block endpoints
`U401.1` and `J401.1` are owned by TB04.
**Visual review:** [Focused accepted image](review-images/TB02-analogue-pwm-feedback.png).
**Risk:** Standard
**Status:** Verified. Requirements, V1 functional evidence, circuit operation,
exact TB02 parts, package mappings, full-hierarchy ERC, deterministic
connectivity, focused visual review and PCB synchronization are accepted.

#### V1 evidence and Rev-A boundary

Both completed V1 harnesses proved the basic 10 kOhm filtered-PWM feedback
pattern. The shared `analog_block2` tests passed target ADC low/high/span checks
and produced monotonic useful readings at 25%, 50% and 75% PWM duty. The shared
`spi_block4` test additionally passed MCP3008 CH0 low, mid and high conversion,
monotonicity and agreement with the target ADC. This is direct physical
evidence for the functional concept and concurrent two-ADC comparison.

V1 used a 100 nF through-hole filter capacitor and through-hole resistor. Rev A
deliberately changes the filter to 10 kOhm and 1 uF in SMD 0603 packages to
reduce PWM ripple. V1 therefore proves function but not the Rev-A time
constant, package implementation, routing fabric, three isolation headers or
PCB analogue performance.

Primary retained V1 evidence:

- `tests/Results/analog_block2/Initial_runs.md`
- `tests/Results/spi_block4/Initial_runs.md`
- `tests/repl/analog_block2/`
- `tests/repl/spi_block4/`

#### Implemented functional flow and isolation

```text
TI_ANALOG_PWM_OUT -- TP201 -- JP201 -- R201 10 kOhm --+-- ANALOG_FB -- TP202
                                                       |
                                                       +-- C201 1 uF -- TI_GND
                                                       +-- J201.1 external stimulus
                                                       +-- JP202 -- TP203 -- TI_ANALOG_ADC_IN
                                                       +-- JP203 -- TP204 -- U401.1 MCP3008 CH0
                                                                            +-- J401.1 breakout
J201.2 --------------------------------------------------------------- TI_GND -- TP205
```

All three shunts are fitted for normal operation. Removing `JP201` disconnects
the target PWM source before an external 0 V to 3.3 V stimulus is applied at
`J201`. `JP202` and `JP203` independently disconnect the target ADC and
MCP3008 CH0 branches. The saved corrected hierarchy places `U401.1`, `J401.1`
and `TP204` together on the ADC side of `JP203`; removing that shunt therefore
isolates the complete MCP3008 CH0 branch rather than only its diagnostic point.

The Target Interface configuration remains subject to the accepted routing
rules: `RP01` selects `TI_ANALOG_ADC_IN` and `RP14` selects
`TI_ANALOG_PWM_OUT`. Firmware shall disable the source before route or shunt
changes and shall not connect an external source until `JP201` is open.

#### Electrical review and calculations

The selected 10 kOhm and 1 uF values give a nominal time constant of 10 ms and
a -3 dB corner of approximately 15.9 Hz. Five time constants are 50 ms; the
standard 150 ms test delay is 15 nominal time constants. At the provisional
5 kHz PWM frequency, the nominal worst ripple near 50% duty is approximately
16.5 mV peak-to-peak. Component tolerance, MLCC DC bias, target output
resistance, TMUX1511 resistance and PCB parasitics remain included in the
completed-board measurements rather than being treated as guaranteed by this
ideal calculation.

Microchip's MCP3008 data sheet shows a 20 pF sample/hold capacitor and warns
that a non-low-impedance source can cause conversion error. In this circuit,
`C201` is the local charge reservoir on `ANALOG_FB`, while `R201` determines the
slower duty-cycle settling. The 1 uF nominal reservoir is many orders of
magnitude larger than the MCP3008 sampling capacitor, supporting the selected
functional sample strategy. The data sheet also requires the SPI conversion
to complete quickly enough to prevent stored charge decay and recommends
analogue/digital separation and local bypass placement; those SPI timing and
layout checks remain owned jointly by TB04 and the PCB stage.

The external stimulus limit is 0 V to 3.3 V relative to `TI_GND`. It must not
exceed the safe range of either selected target ADC or the 3.3 V-powered
MCP3008. The external equipment and harness must share ground. This connector
does not provide overvoltage protection, so its voltage limit and the required
open `JP201` state must be clear on the silkscreen.

#### Manufacturer source and application review

- Microchip's current
  [MCP3004/MCP3008 data sheet](https://ww1.microchip.com/downloads/aemDocuments/documents/MSLD/ProductDocuments/DataSheets/MCP3004-MCP3008-Data-Sheet-DS20001295.pdf)
  supports the CH0 sampling analysis, SPI timing requirement, input filtering,
  local bypass and analogue-layout actions above.
- Microchip
  [AN688, Layout Tips for 12-Bit A/D Converter Application](https://www.microchip.com/en-us/application-notes/an688),
  is conservative guidance for this 10-bit design. Keep the RC node and
  analogue return compact, keep SPI clock and other fast digital traces away
  from it, avoid routing digital signals underneath the ADC or its bypass, and
  preserve a low-impedance common ground implementation.
- Other product-linked MCP3008 application notes concern particular sensors or
  higher-order signal-conditioning designs. They do not change this low-rate,
  target-generated functional stimulus circuit. The device data sheet and
  AN688 provide the applicable implementation consequences.

#### Exact components and package mapping

| References | Selected part | Package and KiCad footprint | Review result |
|---|---|---|---|
| `R201` | Yageo [`RC0603FR-0710KL`](https://www.yageogroup.com/component-documentation/download/specsheet/RC0603FR-0710KL), 10 kOhm, 1%, 0.1 W, 100 ppm/degC | 0603/1608; `Resistor_SMD:R_0603_1608Metric` | Accepted Rev-A SMD filter resistor. Manufacturer dimensions are 1.6 mm x 0.8 mm and are compatible with the standard KiCad 0603 footprint. Exact MPN metadata is present. |
| `C201` | TDK [`C1608X7R1C105K080AC`](https://product.tdk.com/en/search/capacitor/ceramic/mlcc/info?part_no=C1608X7R1C105K080AC), 1 uF, 10%, 16 V, X7R | 0603/1608; `Capacitor_SMD:C_0603_1608Metric` | Accepted Rev-A SMD filter capacitor. The 16 V rating gives useful DC-bias headroom at 3.3 V; manufacturer dimensions and recommended reflow lands are compatible with the KiCad footprint. Exact MPN metadata is present. |
| `JP201`–`JP203`, `J201` | Würth Elektronik [`61300211121`](https://www.we-online.com/components/products/datasheet/61300211121.pdf), two-position straight 2.54 mm header | THT; `Connector_PinHeader_2.54mm:PinHeader_1x02_P2.54mm_Vertical` | Accepted user-operated isolation and stimulus headers. The 1.0 mm KiCad drills lie within the 1.10 +/-0.15 mm recommendation; pitch and numbering agree. Exact MPN metadata is present. |
| One fitted shunt per `JP201`–`JP203` | Würth Elektronik [`60900213421`](https://www.we-online.com/components/products/datasheet/60900213421.pdf), 2.54 mm jumper with test point | Removable accessory fitted over each isolation header | Accepted normal-state shunt, recorded as `SHUNT_MPN` on each owning header and hand fitted after manufacture. `J201` does not receive a shunt. |
| `TP201`–`TP205` | Würth Elektronik `61300111121` | THT single pin; `Connector_PinHeader_2.54mm:PinHeader_1x01_P2.54mm_Vertical` | Accepted by board-wide decision `INT02`; DNP records hand fitting rather than absence from the completed board. |

`U401` and `J401` remain TB04 component selections. Their CH0 pin mappings
are nevertheless checked here because they form the far side of the TB02
isolation boundary.

#### Verification state

| Evidence | Result |
|---|---|
| Requirements and functional review | Accepted circuit approach; the corrected MCP3008 isolation topology implements the existing architecture without changing it. |
| V1 prototype evidence | Accepted for the 10 kOhm filtered-PWM function and concurrent target/MCP3008 ADC comparison; not used as Rev-A package or 1 uF performance proof. |
| Connectivity contract | `verification/contracts/TB02-analogue-pwm-feedback.yaml` passes 38 checks: 19 pin/net, 11 component-value and 8 forbidden-direct-path assertions. The complete thirteen-contract baseline passes all 1071 checks. |
| Package review | Accepted `R201`, `C201`, three isolation headers, three shunts, stimulus header and existing board-wide test-pin selection. |
| Full-hierarchy ERC | Accepted root report dated 2026-08-13: zero errors and zero warnings. |
| Visual schematic review | Accepted focused image linked above. It shows the complete Block 2 path, all three isolation boundaries, stimulus precautions, filter values and the MCP3008 CH0/`J401.1` cross-block endpoint. |
| PCB synchronization | Accepted. The current PCB contains exactly one each of `R201`, `C201`, `J201`, `JP201`–`JP203` and `TP201`–`TP205`. `JP201` now carries the accepted PWM-source description, value, MPN and shunt metadata. The isolation pad nets are correct: `JP201` separates `TI_ANALOG_PWM_OUT` from `Net-(JP201-B)`, `JP202` separates `ANALOG_FB` from `TI_ANALOG_ADC_IN`, and `JP203` separates `ANALOG_FB` from `MCP3008_CH0`. Final physical placement and routing remain PCB-stage work. |

#### Open issues and accepted exceptions

- At PCB layout, place `C201` at the `ANALOG_FB` branch point with a short
  ground return, keep the complete analogue node compact, and keep SPI clock
  and other fast digital routing away from it.
- Clearly mark `J201` as `0–3V3`, signal and ground, and mark all three shunts'
  normal fitted state and isolation function on the silkscreen.
- Measure settling time, PWM ripple, target/MCP3008 agreement and external
  stimulus behaviour on the completed Rev-A board.
- TB04 resolved the manufacturer recommendation for local MCP3008 bypassing:
  `C401` is now 1 uF X7R from the joined VDD/VREF supply to the joined analogue
  and digital ground return. This does not alter the accepted TB02 filter.

No TB02 exception is accepted at this stage.

### 4.7 TB03 — I2C functional device

**Purpose and requirements:** Provide the target with a known 16-bit I2C GPIO
device at address `0x20`, a protected GPIO feedback path, a mirrored
open-drain interrupt path, a protected Supervisor event handshake, one Grove
I2C expansion connector, selectable central bus pull-ups, full GPIO breakout
and diagnostic access. See Standard Test Blocks Section 6.3.
**Source schematic:** `standard_test_blocks.kicad_sch`, references `U301`,
`C301`, `J301`, `J302`, `JP301`–`JP304`, `JP306`–`JP309`, `Q301`, `Q302`,
`R301`–`R312` and `TP301`–`TP306`.
**Visual review:** [Functional-device image](review-images/TB03-i2c-functional-device.png)
and [Supervisor-event image](review-images/TB03-supervisor-event-handshake.png).
**Risk:** Standard
**Status:** Verified schematic baseline. Requirements, corrected circuit
operation, manufacturer guidance, exact component and package selections,
full-hierarchy ERC, deterministic connectivity, PCB synchronization and the
two focused visual records are accepted. Physical placement, routing and
populated-board measurements remain PCB-stage actions.

#### V1 evidence and Rev-A boundary

Both completed V1 harnesses proved the MCP23008 register, GPIO-feedback,
interrupt and external-Grove concepts. The retained I2C investigations show
that the classic ESP32 failure occurred during controller setup rather than
bus traffic and that the same hardware passed after the firmware correction.
This supports the functional pattern but does not prove the Rev-A MCP23017,
two-bank breakout, isolated device branches, selectable central pull-ups or
Supervisor event stages.

Primary retained evidence is identified in Standard Test Blocks Section 6.3,
including the I2C bring-up and upstream-fix investigations. Rev-A board tests
must therefore preserve the V1 MCP23008 suite and add an MCP23017-specific
two-bank test.

#### Implemented functional, isolation and safety flow

```text
TEST_BLOCK_3V3 -- JP308 -- R301 4.7k --------+
                         R303 4.7k DNP ------+-- shared SDA -- J301.2 / TP301
                                                           |
                                                           +-- JP302 -- U301.13

TEST_BLOCK_3V3 -- JP309 -- R302 4.7k --------+
                         R304 4.7k DNP ------+-- shared SCL -- J301.1 / TP302
                                                           |
                                                           +-- JP303 -- U301.12

TEST_BLOCK_3V3 -- JP301 -- MCP23017_VDD --+-- U301.9 / C301
                                           +-- R306 -- RESET
                                           +-- R312 -- INTA -- JP307 -- TI_I2C_INT
                                           +-- R309 -- protected SUP_EVENT_OUT input

U301.GPA0 -- R305 470R -- JP306 -- TI_I2C_FB
U301.GPA1 ---------------- GPA2              internal feedback/interrupt stimulus
U301.GPB0 <-- JP304 <-- Q301 <-- SUP_EVENT_OUT
U301.GPB1 --> Q302 open drain --> SUP_EVENT_IN
U301 GPA0–GPA7 / GPB0–GPB7 <--> J302 breakout
```

`JP302` and `JP303` isolate only the MCP23017 pins; the Grove connector,
central pull-ups, test points and fixed routing-control bus remain connected.
`JP301` defines the isolated device-supply node. The VDD pin, decoupling,
RESET pull-up, INTA pull-up and event-input drain pull-up are all downstream,
preventing a local signal from biasing an unpowered U301. `JP306`, `JP307` and
`JP304` independently isolate feedback, target interrupt and Supervisor event
input respectively. The Grove branch is isolated by unplugging `J301`.

The default single 4.7 kOhm pull-up on each bus line draws approximately
0.70 mA at 3.3 V when low. Populating the parallel 4.7 kOhm DNP position gives
2.35 kOhm and approximately 1.40 mA. Neither option is accepted solely by
calculation: the completed bus population and attached Grove device determine
effective resistance, capacitance, rise time and low-level margin.

#### Manufacturer source and application review

- Microchip's current
  [MCP23017/MCP23S17 data sheet](https://ww1.microchip.com/downloads/aemDocuments/documents/APID/ProductDocuments/DataSheets/MCP23017-Data-Sheet-DS20001952.pdf)
  supports the SOIC-28 pin mapping, address `0x20`, reset defaults, open-drain
  interrupt configuration, local decoupling and I2C electrical checks. The
  saved schematic ties A0–A2 low, leaves INTB unconnected for direct package
  probing, and supplies INTA through the accepted local 10 kOhm pull-up.
- Microchip
  [AN1043 — Unique Features of the MCP23X08/17 GPIO Expanders](https://ww1.microchip.com/downloads/en/AppNotes/01043a.pdf)
  supports explicit direction/latch setup and real-pad readback. Firmware must
  set and verify the intended `IOCON.BANK`, `IOCON.SEQOP`, `IOCON.MIRROR` and
  `IOCON.ODR` conventions; leave unused pins as inputs; establish safe output
  latch values before enabling outputs; and use `GPIO` reads rather than only
  `OLAT` when verifying the actual pin state.
- The official Seeed Grove system definition and designer guidance govern
  `J301`: pin 1 SCL, pin 2 SDA, pin 3 3.3 V and pin 4 ground. PCB review must
  verify the footprint viewing direction, pin-1 marking and actual mating
  connector because cable illustrations can otherwise be misread.
- The onsemi
  [2N7002L data sheet](https://www.onsemi.com/download/data-sheet/pdf/2n7002l-d.pdf)
  supports the selected `2N7002LT1G` SOT-23 package and pin 1 gate, pin 2
  source, pin 3 drain mapping for `Q301/Q302`. The event stages sink only
  low-current logic pull-ups; final populated-board testing must nevertheless
  confirm asserted-low voltage, released-state leakage and unpowered behaviour.

#### Exact components and package state

| References | Current implementation | Review result |
|---|---|---|
| `U301` | Microchip `MCP23017-E/SO`; `Package_SO:SOIC-28W_7.5x17.9mm_P1.27mm` | Exact MPN, wide SOIC-28 footprint, data sheet and AISLER assembly metadata accepted. |
| `C301`, `R301`–`R312` | 0603 SMD footprints with reviewed electrical values and parametric `AISLER_MPN` Smart Match descriptions | Accepted for prototype assembly. `R303/R304` remain built-in DNP parallel pull-up adjustment positions; verify AISLER's final assigned parts against the deterministic KiCad BOM before manufacture. |
| `JP301`–`JP304`, `JP306`–`JP309` | Wuerth `61300211121` 2.54 mm vertical headers with `60900213421` shunts | Exact header, footprint and normal-operation shunt metadata accepted. `JP304` now uses the common event-input-isolation metadata and `JP306` correctly describes feedback isolation. |
| `J301` | Seeed `1125R-4P`, single-part SKU `320110034`; retail ten-pack `110990037` | Exact right-angle THT selection and project footprint `Espruino_Harness_RevA:Grove_1x04_P2mm_RightAngle_Seeed_320110034` accepted. KiCad built-in DNP retains its pads and plated holes while excluding AISLER placement; hand-fit after manufacture. |
| `J302` | Wuerth `61301621121`; `Connector_PinHeader_2.54mm:PinHeader_2x08_P2.54mm_Vertical` | Exact vertical 2x8 THT selection accepted. Functional Value remains `MCP23017_GPIO`; KiCad built-in DNP retains the footprint for hand fitting while excluding AISLER placement. |
| `Q301`, `Q302` | onsemi `2N7002LT1G`; `Package_TO_SOT_SMD:SOT-23` | Exact MPN, SOT-23 gate/source/drain mapping, data sheet and AISLER assembly metadata accepted for the low-current event stages. |
| `TP301`–`TP306` | Wuerth `61300111121`; single-pin 2.54 mm THT | Accepted under board-wide decision `INT02`; DNP records hand fitting rather than absence from the completed board. |

#### Verification state

| Evidence | Result |
|---|---|
| Requirements and functional review | Accepted against Standard Test Blocks Section 6.3, including the corrected device-only SDA/SCL isolation and downstream RESET/INTA biasing. |
| V1 prototype evidence | Accepted for the functional I2C device, GPIO feedback, interrupt and Grove-extension concepts; not used as Rev-A package, isolation or event-stage proof. |
| Connectivity contract | `verification/contracts/TB03-i2c-functional-device.yaml` passes 150 checks: 99 pin/net, 32 component-value and 19 forbidden-direct-path assertions. The complete thirteen-contract set passes all 1071 checks. |
| Full-hierarchy ERC | Accepted root report dated 2026-08-13: zero errors and zero warnings. |
| Visual schematic review | Accepted in the two focused images linked above. Together they show the shared bus, pull-ups, all device-isolation boundaries, isolated supply and biases, full GPIO breakout, feedback/interrupt paths and both Supervisor event stages. |
| PCB synchronization | Accepted for schematic-baseline scope. Every contracted TB03 reference occurs exactly once on the current PCB, including the project-local `J301` footprint. The PCB carries the final `MCP23017_GPIO` value for `J302` and exact U301/Q301/Q302 metadata. Final placement, pad-level physical review and routing remain PCB-stage work. |

#### Closure actions and accepted exceptions

- At PCB layout, place `J301` near the upper outer edge with its mating face
  outward and body mechanically supported; verify pin 1, cable approach and
  clearance. Place and label `J302` for unambiguous GPA/GPB bank and bit order.
- Keep the pull-up enable shunts, optional `R303/R304` positions, isolation
  shunts and SDA/SCL/GND probing points accessible. Keep `C301` close to U301
  with a short ground return and keep the shared I2C bus compact.
- Measure effective SDA/SCL pull-up resistance unpowered and capture rise time
  and valid-low voltage with the populated routing devices and each supported
  Grove configuration at 100 kHz. Treat 400 kHz as optional until measured.
- Verify cold-start, supply-isolated and independently isolated feedback,
  interrupt and event states. Exercise the two-bank register map, mirrored
  open-drain interrupt, GPA1/GPA2 loop, GPA0 feedback and both event directions.

No TB03 exception is accepted at this stage.

### 4.8 TB04 — SPI functional device and fixed microSD storage extension

**Purpose and requirements:** Provide a known SPI ADC, independent active-low
chip selects, a shared three-wire SPI bus, MCP3008 analogue-channel access and
a fixed underside microSD module with a removable card. See Standard Test
Blocks Section 6.4.
**Source schematic:** `standard_test_blocks.kicad_sch`, references `U401`,
`J401`, `J402`, `C401`–`C403`, `R401`, `R402` and `TP401`–`TP407`, with the
Block 2 `JP203`/`TP204` MCP3008-CH0 isolation boundary.
**Visual review:** [SPI functional-device and storage image](review-images/TB04-spi-functional-device-and-storage.png).
**Risk:** Standard
**Status:** Verified schematic baseline. Requirements, circuit operation,
manufacturer guidance, exact active-device and connector selections,
full-hierarchy ERC, deterministic connectivity, PCB synchronization and the
focused visual record are accepted. Physical placement, routing, module fit
and populated-board measurements remain PCB-stage actions.

#### V1 evidence and Rev-A boundary

Both completed V1 harnesses proved the socketed MCP3008 SPI-transfer,
low/mid/high conversion, monotonic-response and Block 2 comparison pattern.
The earlier W25xxx extension also demonstrated the intended second-chip-select
and shared-bus test concept, although later inconsistent module identification
showed why the replaceable extension itself required improvement.

That evidence supports the shared-bus architecture and MCP3008 reference
device. It does not prove the new Adafruit 5683 microSD module, its underside
castellated mounting, card-access envelope, local capacitance or final Rev-A
routed timing. Those remain explicit PCB and populated-board checks.

#### Implemented functional, signal and safety flow

```text
TEST_BLOCK_3V3 --+-- U401.15 VREF / U401.16 VDD -- C401 1uF -- TI_GND
                 +-- R401 10k -- TI_SPI_CS_ADC -- U401.10 / TP401
                 +-- J402.4 -- C402 100nF / C403 22uF -- TI_GND
                 +-- R402 10k -- TI_SPI_CS_EXT -- J402.6 / TP406
                 +-- TP407

TI_SPI_SCK  -- U401.13 / J402.1 / TP403
TI_SPI_MOSI -- U401.11 / J402.3 / TP404
TI_SPI_MISO -- U401.12 / J402.2 / TP405
TI_GND      -- U401.9 AGND / U401.14 DGND / J402.5 / TP402

ANALOG_FB -- JP203 -- MCP3008_CH0 -- U401.1 / J401.1 / TP204
U401 CH1–CH7 ---------------------- J401.2–J401.8
```

`R401` and `R402` hold both chip selects high and inactive while the target is
absent, resetting or unconfigured. The MCP3008 and microSD module share SCK,
MOSI and MISO but retain independent chip selects. The MCP3008 remains fully
removable through its socket; the BFF's normal storage-device isolation is an
unmounted and removed card, while complete module removal is powered-off
solder rework.

#### Manufacturer source and application review

- Microchip's current
  [MCP3004/MCP3008 data sheet](https://ww1.microchip.com/downloads/aemDocuments/documents/MSLD/ProductDocuments/DataSheets/MCP3004-MCP3008-Data-Sheet-DS20001295.pdf)
  supports the saved PDIP-16 pin mapping, 2.7–5.5 V supply range, SPI framing,
  input range and the selected `MCP3008-I/P` order code. Section 6.4 recommends
  a 1 uF local bypass; `C401` now implements that recommendation at the joined
  VDD/VREF node.
- Adafruit's
  [microSD BFF technical guide](https://learn.adafruit.com/adafruit-microsd-card-bff)
  and [published PCB design](https://github.com/adafruit/Adafruit-microSD-Card-BFF-PCB)
  define the accepted Product 5683 module, 3.3 V-only operation, SPI signals,
  factory TX-to-CS selection and castellated-pad geometry. The harness uses
  TX as `TI_SPI_CS_EXT`; RX, A0 and A1 alternatives remain open.
- The published module design identifies the fitted Molex `104031-0811`
  push-pull socket and provides no regulator, level shifter or local supply
  bypass. The harness therefore supplies 3.3 V directly and provides `C402`
  100 nF plus `C403` 22 uF locally at J402.
- Würth's `61300811121` data sheet confirms the selected J401 eight-position,
  single-row, vertical 2.54 mm through-hole header and its recommended hole
  pattern. Harwin `D2816-42` is the selected hand-fitted 16-pin, 7.62 mm
  dual-row socket accessory for the removable MCP3008.

#### Exact components and package state

| References | Current implementation | Review result |
|---|---|---|
| `U401` | Microchip `MCP3008-I/P`; `Package_DIP:DIP-16_W7.62mm_LongPads` | Exact PDIP-16 MPN, data sheet and footprint accepted. Built-in DNP excludes AISLER placement; hand-fit Harwin `D2816-42` socket and insert U401 after manufacture. |
| `J401` | Würth `61300811121`; `Connector_PinHeader_2.54mm:PinHeader_1x08_P2.54mm_Vertical` | Exact 1x8 THT header, data sheet and footprint accepted. Built-in DNP records hand fitting. Pin 1 is CH0 and pins 2–8 are CH1–CH7. |
| `J402` | Adafruit Product `5683`, supplier reference `ADA5683`; project footprint `Espruino_Harness_RevA:Adafruit_MicroSD_BFF_5683_Underside` | Exact assembled module and underside footprint accepted. Built-in DNP retains all fourteen copper/mask lands without paste while excluding AISLER placement; six lands are electrically connected and eight mechanical lands remain unnumbered. |
| `C401` | 1 uF, 10%, 16 V X7R, 0603 | Accepted MCP3008 VDD/VREF bypass value and package. |
| `C402`, `C403` | 100 nF 0603 and 22 uF 0805 X7R | Accepted BFF high-frequency and bulk bypass values. Final effective capacitance and switched-rail budget remain PCB checks. |
| `R401`, `R402` | 10 kOhm, 1%, 0.1 W, 0603 | Accepted inactive-state pull-ups for `TI_SPI_CS_ADC` and `TI_SPI_CS_EXT`. |
| `TP401`–`TP407` | Würth `61300111121`; single-pin 2.54 mm THT | Accepted under board-wide decision `INT02`; DNP records hand fitting rather than absence from the completed board. |

#### Verification state

| Evidence | Result |
|---|---|
| Requirements and functional review | Accepted against Standard Test Blocks Section 6.4, including the fixed underside microSD decision, shared SPI bus, independent chip selects, CH0 cross-block isolation and required observation points. |
| V1 prototype evidence | Accepted for the socketed MCP3008 and shared-bus/second-chip-select concepts; not used as ADA5683, local-capacitance, footprint or routed-timing proof. |
| Connectivity contract | `verification/contracts/TB04-spi-functional-device-and-storage.yaml` passes 75 checks: 49 pin/net, 15 component-value and 11 forbidden-direct-path assertions. The complete thirteen-contract baseline passes all 1071 checks. |
| Full-hierarchy ERC | Accepted root report dated 2026-08-14: zero errors and zero warnings. |
| Visual schematic review | Accepted focused image linked above. It shows the MCP3008 core and breakout, both inactive-state chip-select pull-ups, fixed BFF interface, local capacitance, hand-fit state and seven observation points. |
| PCB synchronization | Accepted for schematic-baseline scope. U401 and J401 carry their exact MPNs and DNP state; J402 occurs once on `B.Cu` with the accepted project footprint, DNP state, six correct electrical pad nets, eight unnumbered mechanical lands and no paste apertures. Final placement and routing remain PCB-stage work. |

#### Closure actions and accepted exceptions

- Place J402 on the underside at the upper board edge with `CARD ACCESS`
  outward. Verify orientation, castellated-land registration, solder access,
  support, Grove-connector clearance and card insertion/withdrawal using the
  actual module and a printed 1:1 board review.
- Place `C402` closest to J402's 3.3 V/GND lands and `C403` immediately nearby.
  Place `C401` at U401 VDD/VREF with a short joined ground return. Confirm the
  effective 22 uF capacitance and total `TEST_BLOCK_3V3` switched-capacitance
  budget after voltage derating and the complete board population are known.
- Route SCK, MOSI and MISO compactly over a continuous ground reference, keep
  both chip-select pull-ups local, avoid long MISO branches and preserve probe
  access to TP401–TP407 and clear CH0–CH7 labelling at J401.
- Verify socket orientation and pin 1 before inserting U401. Test MCP3008
  conversion and Block 2 agreement, both inactive chip selects, shared-bus
  switching, microSD connect/mount/file/unmount operation and clean card
  removal on the populated board.

No TB04 exception is accepted at this stage.

### 4.9 TB05 — 1-Wire functional devices and GPIO

**Purpose and requirements:** Provide a known mixed-device 1-Wire bus with two
removable, externally powered DS18B20 sensors, one removable parasite-powered
DS2413 dual-GPIO device, protected simultaneous PIO feedback and a selectable
resistor-limited bus pull-up. See Standard Test Blocks Section 6.5.
**Source schematic:** `standard_test_blocks.kicad_sch`, references `J501`–
`J504`, `R501`–`R506` and `TP501`–`TP505`, with routed endpoints implemented by
RC01 `U601`, `U602` and `U605`.
**Visual review:** [1-Wire functional-device and GPIO image](review-images/TB05-onewire-functional-devices-and-gpio.png).
**Risk:** Standard
**Status:** Verified schematic baseline. Requirements, V1 evidence, current
manufacturer guidance, application notes, circuit operation, exact harness
components, full-hierarchy ERC, deterministic connectivity, PCB
synchronization and the focused visual record are accepted. Final routing,
accessory fit, lead-length limits and populated-bus measurements remain
PCB-stage actions.

#### V1 evidence and Rev-A boundary

The ESP32-C3 V1 harness proved two externally powered DS18B20 devices on a
short multidrop bus with a fixed 4.7 kOhm pull-up. The classic ESP32 V1 harness
proved the mixed population of two DS18B20 devices and one removable DS2413,
using a nominal 2.2 kOhm pull-up with 2.0 kOhm fitted, independent 4.7 kOhm PIO
pull-ups and protected target feedback. The restored mixed bus completed the
focused six-scan functional test with the same three ROMs, valid DS18B20 CRCs
and clean DS2413 command/status behaviour. A longer search soak returned the
complete population in 47 of 50 scans, confirming that the topology operates
but can be a firmware-timing and signal-integrity margin case.

V2 preserves the device combination while changing the implementation. It
adds switched Test Block power, two removable sensor terminals, a
resistor-limited 2.2 kOhm/4.7 kOhm selector, one bidirectional TMUX1511 route
in DQ and independently routed PIO feedback. It also reverses the terminal
order used by the C3 V1 connectors: V2 is pin 1 GND, pin 2 DQ and pin 3 3.3 V.
V1 therefore proves the functional circuit pattern and test method, not the
new connector orientation, routed path, PCB topology or representative sensor
leads.

#### Implemented functional, signal and safety flow

```text
TEST_BLOCK_3V3 -- R501 2.2k -- J503.1 --[normal 1-2]--+
TEST_BLOCK_3V3 -- R502 4.7k -- J503.3 --[diagnostic 2-3]--+-- TI_ONEWIRE_DQ
                                                               |
                  +-- J501.2; J501.1 GND / J501.3 3.3 V        |
                  +-- J502.2; J502.1 GND / J502.3 3.3 V        |
                  +-- J504.3 DS2413 DQ; J504.4 GND             |
                  +-- TP501                                    |
                  +-- U601.6 bidirectional route to target ----+

TEST_BLOCK_3V3 -- R504 4.7k -- ONEWIRE_PIOA -- R505 470R
                                              +-- TP502
                                              `-- TI_ONEWIRE_GPIO_A_FB -- U602.11

TEST_BLOCK_3V3 -- R503 4.7k -- ONEWIRE_PIOB -- R506 470R
                                              +-- TP503
                                              `-- TI_ONEWIRE_GPIO_B_FB -- U605.8
```

J503 pins 1–2 select the normal complete-population 2.2 kOhm pull-up. Pins
2–3 select the diagnostic 4.7 kOhm comparison and an open selector removes the
harness pull-up. Both valid positions remain resistor limited. Sensors and
the DS2413 are changed only with power removed. Before connecting or changing
routes, the target DQ pin is released as input/open drain, both DS2413 PIOs are
released and the target feedback pins are inputs. The routing Control Service
keeps reused Block 1 loopback drivers mutually exclusive with the two PIO
feedback routes.

#### Manufacturer source and application review

- The current [DS18B20 data sheet](https://www.analog.com/media/en/technical-documentation/data-sheets/DS18B20.pdf)
  supports 3.0–5.5 V external power, open-drain DQ, multidrop addressing and a
  passive pull-up. External VDD removes the strong-pull-up requirement during
  temperature conversion used by parasite-powered DS18B20 operation.
- The current [DS2413 data sheet](https://www.analog.com/media/en/technical-documentation/data-sheets/ds2413.pdf)
  supports 2.8–5.25 V standard-speed operation, parasite-powered DQ, open-drain
  PIO outputs and the retained 2.2 kOhm maximum passive pull-up condition. Its
  PIO state can persist for tens of seconds after DQ disconnection, so route
  changes require explicit PIO release rather than assuming immediate decay.
- Analog Devices application note 3829, [Determining the Recovery Time for
  Multiple-Slave 1-Wire Networks](https://www.analog.com/en/resources/technical-articles/determining-the-recovery-time-for-multipleslave-1wirereg-networks.html),
  treats externally powered devices as approximately one tenth of a parasite
  load. One DS2413 plus two externally powered DS18B20 devices gives effective
  `N = 1.2`; the conservative 2.8 V, -40 degrees C equation gives about 5.2 us.
  Rev-A therefore uses 6 us as the provisional minimum recovery-time design
  target pending waveform confirmation.
- Application note 148, [Guidelines for Reliable Long Line 1-Wire
  Networks](https://www.analog.com/en/resources/technical-articles/guidelines-for-reliable-long-line-1wire-networks.html),
  makes topology, stubs, cable capacitance, reflections and measured waveform
  quality part of acceptance. Passive pull-up operation is suitable for this
  intended short local network, but representative sensor leads remain part
  of populated-board validation.
- The [TMUX1511 data sheet](https://www.ti.com/lit/ds/symlink/tmux1511.pdf)
  specifies bidirectional operation, 2 Ohm typical/4.5 Ohm maximum
  on-resistance, 3.3 pF typical/6 pF maximum on-capacitance and powered-off
  isolation to 3.6 V. These additions are negligible relative to the passive
  pull-up and complete bus loading, while preserving the required open-drain
  path.

#### Electrical review and calculations

The normal 2.2 kOhm position draws approximately `3.3 V / 2.2 kOhm = 1.5 mA`
when DQ is low. This is below the 4 mA low-level test condition supported by
both device families. The TMUX1511 maximum 4.5 Ohm on-resistance adds only
about 6.8 mV at that current. Its maximum 6 pF on-capacitance contributes only
13.2 ns of pull-up RC time in isolation and is not the dominant bus load.

The 4.7 kOhm position draws about 0.70 mA, giving easy low-level margin but
less than half the normal recharge current. It is therefore correctly limited
to diagnostic or measured reduced-population use. The final acceptable rise
and recovery time cannot be calculated from the schematic alone because
sensor leads, branches, connectors, PCB traces and substituted modules add
capacitance. Any accessory-provided pull-up must also be included in the
effective resistance measurement.

The PIO pull-ups draw about 0.70 mA when asserted low. Each 470 Ohm series
resistor limits accidental target-output contention, but does not make that
state permissible. The DS2413's 20 mA PIO capability leaves substantial normal
low-level margin.

#### Exact components and package state

| References | Current implementation | Review result |
|---|---|---|
| `J501`, `J502` | Phoenix Contact `1725669`; horizontal-entry 3-position, 2.54 mm THT terminal | Exact connector MPN and footprint accepted. Native DNP retains both footprints and excludes AISLER placement for hand fitting. Sensor assemblies remain removable accessories rather than PCB BOM components. |
| `J503` | Würth `61300311121`; 1x3 vertical 2.54 mm THT header; Würth `60900213421` shunt | Exact header and shunt accepted. Native DNP records hand fitting. Value and description identify pins 1–2 as normal 2.2 kOhm and pins 2–3 as diagnostic 4.7 kOhm. |
| `J504` | Würth `61300411121`; 1x4 vertical 2.54 mm THT male header | Exact harness connector accepted with pin order PIOB, PIOA, DQ, GND. Native DNP records hand fitting. The mating DS2413 breakout remains a removable accessory whose final envelope and female-header orientation require physical confirmation. |
| `R501`–`R506` | 0603 SMD; 2.2 kOhm, three 4.7 kOhm and two 470 Ohm values as shown | Values, functions, footprints and AISLER parametric descriptions accepted. |
| `TP501`–`TP505` | Würth `61300111121`; single-pin vertical 2.54 mm THT | Accepted under board-wide decision `INT02`; native DNP records post-manufacture hand fitting. |

#### Verification state

| Evidence | Result |
|---|---|
| Requirements and functional review | Accepted against Standard Test Blocks Section 6.5, including normal and diagnostic selector states, removable devices, simultaneous protected PIO feedback and safe route sequencing. |
| V1 prototype evidence | Accepted for the two-sensor and mixed DS18B20/DS2413 functional patterns; explicitly not used as proof of the V2 switch path, connectors, layout or leads. |
| Connectivity contract | `verification/contracts/TB05-onewire-functional-devices-and-gpio.yaml` passes 65 checks: 36 pin/net, 15 component-value and 14 forbidden-direct-path assertions. The complete thirteen-contract baseline passes all 1071 checks. |
| Full-hierarchy ERC | Accepted root report dated 2026-08-14: zero errors and zero warnings. |
| Visual schematic review | Accepted focused image linked above. It clearly records DQ and feedback flow, selector states, removable devices, observation points, power-off reconfiguration and DS2413 retained-state behaviour. |
| PCB synchronization | Accepted for schematic-baseline scope. `J501`–`J504`, `R501`–`R506` and `TP501`–`TP505` each occur once on the current PCB with the accepted footprints and pad nets. `J501`–`J504` carry native through-hole DNP attributes matching the saved schematic. Final placement, silkscreen, routing and accessory fit remain PCB-stage work. |

#### Closure actions and accepted exceptions

- Mark both sensor terminals `GND | DQ | 3V3` and distinguish them from the
  reversed C3 V1 terminal order. Confirm entry direction and pin 1 using the
  actual Phoenix part and do not reuse V1 sensor leads without rewiring.
- Mark J504 pin 1 and `PIOB | PIOA | DQ | GND`; verify the selected DS2413
  breakout, downward female header, body clearance and unkeyed orientation
  with the physical module before manufacturing release.
- Keep the DQ trunk and all three device branches short over continuous ground,
  avoid long stubs and noisy aggressors, and preserve access to TP501–TP505.
- On the populated board, measure DQ low level, rise and recovery time with the
  normal full population and representative leads. Retain repeated three-ROM
  search, DS18B20 scratchpad/CRC, DS2413 command/status and both PIO feedback
  results. Compare the 2.2 kOhm and 4.7 kOhm positions and record every fitted
  accessory pull-up.

No TB05 schematic-baseline exception is accepted at this stage.

### 4.10 TB07 — UART crosslink and external peer

**Purpose and requirements:** Provide an automated protected full-duplex
crosslink between logical target UART endpoints A and B, plus a mutually
exclusive switched endpoint-A connection to an independently controlled 3.3 V
external peer. Preserve a safe open state during reset and partial power, and
provide separate peer and high-impedance diagnostic connectors. See Standard
Test Blocks Section 6.7 and the Combined Capability Connection Matrix Section
5.
**Source schematic:** `standard_test_blocks.kicad_sch`, references `U701`,
`C701`, `R701`–`R708`, `J701` and `J702`; route endpoints are implemented by
RC01 `U603`/`U604`, and RC02 `U611.GPA3`–`GPA6` owns `UP01_EN`–`UP04_EN`.
**Visual review:** [UART crosslink and external-peer image](review-images/TB07-uart-crosslink-and-external-peer.png).
**Risk:** Standard
**Status:** Verified schematic baseline. Requirements, V1 evidence, current
manufacturer guidance, application notes, circuit operation, exact components,
full-hierarchy ERC, deterministic connectivity, PCB synchronization and the
focused visual record are accepted. Final placement, routing, connector access,
powered-off measurements and populated UART validation remain PCB-stage and
prototype actions.

#### V1 evidence and Rev-A boundary

The classic ESP32 V1 harness proved a fixed full-duplex UART1/UART2 crosslink
while UART0 remained the independent control connection. The same hardware
helped reproduce and resolve Espruino issue 2718, then passed complete and
hash-correct 32-, 64-, 65-, 96-, 128- and 200-byte transfers in both
directions. It also passed simultaneous unequal full-duplex traffic, 9600,
57600 and 115200 baud, 8N1, 7E1 and 8O2 framing, event and polling reception,
listener changes, repeated setup, `unsetup` and mismatch recovery. This is
strong evidence for the crossed-UART function, 470 Ohm protection and test
method.

Rev-A retains that capability but replaces V1's fixed/manual arrangement with
four TMUX1511 channels under target-owned routing control. It also adds the
endpoint-A external-peer mode, powered-off isolation, deterministic control
pull-downs and separate peer/diagnostic connectors. V1 does not prove the new
TMUX path, controller state transitions, partial-power behaviour, connector
orientation or completed-PCB signal integrity. The critical-prototype workflow
therefore includes representative bidirectional UART traffic in Experiment A.

#### Implemented functional, signal and safety flow

```text
UP01: TI_UART_A_TX -- U701 S1/D1 -- R701 470R --> TI_UART_B_RX
UP02: TI_UART_B_TX -- U701 S2/D2 -- R702 470R --> TI_UART_A_RX

UP03: TI_UART_A_TX -- U701 S3/D3 -- R703 470R --> J701.1 UART_PEER_RX
UP04: J701.2 UART_PEER_TX -- U701 S4/D4 -- R704 470R --> TI_UART_A_RX
                                           J701.3 --> TI_GND

J702.1 --> TI_UART_B_TX    high-impedance observation only
J702.2 --> TI_UART_B_RX    high-impedance observation only
J702.3 --> TI_GND          no external drive and no power output

U611 GPA3..GPA6 --> UP01_EN..UP04_EN --> U701 SEL1..SEL4
                         |
                         +-- R705..R708 100k --> TI_GND
```

`UART_PEER_RX` and `UART_PEER_TX` use the peer perspective: peer RX receives
endpoint-A TX, and peer TX drives endpoint-A RX. J701 is the only standard
active-peer interface. J702 directly observes endpoint B and shall not be
driven. Neither connector supplies power; a peer must be independently powered,
use 3.3 V signalling and share `TI_GND`.

| `UP01..UP04` | Permitted state | Required precondition |
|---|---|---|
| `0000` | Safe/open | Default, reset, failed configuration and state-change state |
| `1100` | Target A/B full-duplex crosslink | External peer transmitter disabled; target transmitters enabled only after control readback |
| `0011` | Endpoint-A external peer | Endpoint-B crosslink open; peer and target transmitters enabled only after control readback |
| Any other combination | Prohibited | Reject before writing; return to `0000` on failure |

Drivers shall be disabled before leaving an active state. Firmware clears and
verifies the old state, writes the complete new state, reads it back, then
enables transmitters. R705–R708 supplement the TMUX1511 internal pull-downs so
all four paths remain open while U611 is reset or high impedance.

#### Manufacturer source and application review

The current [TMUX1511 product page](https://www.ti.com/product/TMUX1511) and
[Rev. B data sheet](https://www.ti.com/lit/ds/symlink/tmux1511.pdf) remain the
authority for U701. The RC01 manufacturer review applies directly to this
identical device and package:

- the data sheet confirms independent bidirectional SPST channels, active-high
  controls, fail-safe logic inputs, nominal internal pull-downs, powered-off
  isolation to 3.6 V, the PW pinout and the accepted 0.1 uF local bypass
- [Selecting the Correct Texas Instruments Signal Switch, Rev. E](https://www.ti.com/lit/an/szza030e/szza030e.pdf)
  confirms that signal range, resistance, capacitance, leakage, bandwidth,
  powered-off behaviour and logic compatibility are the relevant selection
  criteria; U701 passes the device-level screen
- [Eliminate Power Sequencing with Powered-off Protection Signal Switches,
  Rev. C](https://www.ti.com/lit/ab/scda015c/scda015c.pdf) confirms why the
  powered-off feature is required when a target or peer can remain powered
- [1.8-V Logic for Multiplexers and Signal Switches, Rev. C](https://www.ti.com/lit/pdf/SCAA126)
  supports direct 3.3 V MCP23017 control without level translation
- TI's SPI isolation application brief is a useful high-speed digital example,
  but no UART-specific TMUX1511 implementation note was identified. UART adds
  no device-level topology requirement beyond the reviewed generic switch,
  powered-off and safe-state rules

The [Würth 61300311121 data sheet](https://www.we-online.com/components/products/datasheet/61300311121.pdf)
confirms the selected three-position straight 2.54 mm THT header. The standard
KiCad 1x3 vertical footprint's 1.0 mm drill lies within Würth's recommended
1.10 +/- 0.15 mm finished-hole range.

#### Electrical review and calculations

At 3.3 V, the 3.3 V MCP23017 control outputs have substantial margin against
the TMUX1511 fixed `VIH = 1.2 V` minimum and `VIL = 0.45 V` maximum. With the
maximum +/-2 uA control-input leakage considered alone, each 100 kOhm external
pull-down develops no more than 0.2 V, below `VIL`; the internal nominal 6 MOhm
pull-down adds further bias.

Each active signal path contains one switch and one 470 Ohm resistor. Using the
4.5 Ohm maximum switch resistance gives 474.5 Ohm maximum nominal series path
resistance before PCB and connector contributions. A worst illustrative 3.6 V
output disagreement would therefore be limited to about 7.6 mA, below the
switch's 25 mA continuous-signal limit, but output contention remains a
prohibited fault rather than an operating mode.

The TMUX1511's 6 pF maximum on-capacitance contributes about 2.8 ns of simple
`RC` time with 470 Ohm, negligible compared with the 8.68 us bit period at the
V1-proven 115200 baud. Complete target, PCB, connector, peer and instrument
capacitance determines the real edge and maximum usable baud; retain waveform
evidence rather than treating this device-only calculation as completed-board
proof.

With `ROUTING_LOGIC_3V3` absent, U701 provides powered-off isolation only while
all signal pins remain within 0 V to 3.6 V. Overshoot, leakage and any resulting
unpowered-rail voltage remain physical prototype checks. J702 instruments must
be high impedance so they do not alter the endpoint-B load or become an
uncontrolled source.

#### Exact components and package state

| References | Current implementation | Review result |
|---|---|---|
| `U701` | Texas Instruments `TMUX1511PWR`; PW TSSOP-14; `Package_SO:TSSOP-14_4.4x5mm_P0.65mm` | Exact active orderable MPN, project-local symbol, PW pins 1–14, footprint pad order and AISLER seven-device assignment accepted under the RC01 package review. |
| `C701` | 100 nF, 10%, 16 V, X7R 0603; `AISLER_MPN = 100nF 10% 16V X7R 0603` | Accepted local U701 bypass. Final supplied part and placement remain release checks. |
| `R701`–`R704` | 470 Ohm, 1%, 0.1 W 0603; `AISLER_MPN = 470R 0603 1% 0.1W` | Values, standard footprints and four distinct protection functions accepted. |
| `R705`–`R708` | 100 kOhm, 1%, 0.1 W 0603; `AISLER_MPN = 100k 0603 1% 0.1W` | Values, standard footprints and individual safe-state descriptions accepted; all four are required fitted components. |
| `J701`, `J702` | Würth `61300311121`; 1x3 vertical 2.54 mm THT; `Connector_PinHeader_2.54mm:PinHeader_1x03_P2.54mm_Vertical` | Exact MPN, footprint and pin mappings accepted. Native DNP retains both PCB footprints while excluding automated through-hole fitting. J701 is the active endpoint-A peer interface; J702 is endpoint-B observation only. |

#### Verification state

| Evidence | Result |
|---|---|
| Requirements and functional review | Accepted against Standard Test Blocks Section 6.7, the UP01–UP04 connection matrix and the updated separate-header architecture. |
| V1 prototype evidence | Accepted for full-duplex crosslink function, 470 Ohm protection and at least 115200 baud; explicitly not used as proof of TMUX switching, external-peer mode or partial power. |
| Connectivity contract | `verification/contracts/TB07-uart-crosslink-and-external-peer.yaml` passes 76 checks: 48 pin/net, 12 component-value and 16 forbidden-direct-path assertions. The complete thirteen-contract baseline passes all 1071 checks. |
| Full-hierarchy ERC | Accepted root report dated 2026-08-15: zero errors and zero warnings. |
| Visual schematic review | Accepted focused image linked above. It records the complete switch paths, permitted state vectors, safe-state pull-downs, peer-perspective names, connector restrictions and absence of connector power. |
| PCB synchronization | Accepted for schematic-baseline scope. `U701`, `C701`, `R701`–`R708`, `J701` and `J702` each occur once on the current PCB with the accepted footprints and pad nets. J701/J702 carry native `through_hole dnp` attributes; their pads are respectively peer RX/peer TX/GND and endpoint-B TX/endpoint-B RX/GND. Final placement and routing remain PCB-stage work. |
| Planned physical proof | Critical Prototype Experiment A includes a representative TMUX1511 path, safe-state control and bidirectional UART traffic before manufacturing release. |

#### Closure actions and accepted exceptions

- Keep U701, C701 and R701–R708 as one compact functional group over a
  materially continuous ground reference. Avoid unnecessary UART stubs and
  preserve clear separation from fast switching and power routes.
- Place J701 and J702 as visibly separate connectors. Mark pin 1, `PEER`,
  `DIAGNOSTIC - NO DRIVE`, signal direction, GND and the absence of connector
  power. Confirm cable and probe access using the actual headers.
- Exercise `0000`, `1100` and `0011` on the prototype and populated board,
  including cold start, Hardware Clear, route readback, bidirectional traffic,
  V1-proven framing/rates and external-peer operation. Reject every other
  state and retain powered-off and signal-integrity captures.

No TB07 schematic-baseline exception is accepted at this stage.

### 4.11 TB09 — Addressable RGB output

**Purpose and requirements:** Provide a removable timing-sensitive addressable
RGB load for `require("neopixel")` and `neopixel.write()` validation, with a
protected 3.3 V target-data observation point and no exported module-generated
5 V. The implementation is governed by Standard Test Blocks Section 6.9 and
the accepted `TI_RGB_DATA` Target Interface assignment.
**Source schematic:** `standard_test_blocks.kicad_sch`, references `R901`,
`C901`, `J902`, `TP901` and `TP902`; `J900.14` provides the Target Interface
contact and RC01 `U604.8` provides route destination `RP15`.
**Visual review:** [Addressable RGB output image](review-images/TB09-addressable-rgb-output.png).
**Risk:** Standard
**Status:** Verified schematic baseline. Requirements, module integration,
manufacturer sources, corrected connector order, exact harness components,
full-hierarchy ERC, deterministic connectivity, PCB synchronization and the
focused visual record are accepted. Actual module engagement, placement,
waveform margin and populated-board operation remain PCB-stage actions.

#### V1 evidence and Rev-A boundary

V1 has no standard addressable-RGB block and therefore supplies no direct
prototype proof for this circuit. TB09 is a new V2 capability selected because
encoded single-wire RGB output exercises target-port timing that static GPIO
loopback and filtered PWM do not cover.

The Adafruit product 6066 module integrates the level shifting, local 5 V
generation and one visible NeoPixel. Rev A adds only its removable 3.3 V input
interface, series protection, local harness-side bypass and diagnostic access.
The module is a hand-fitted test accessory rather than an AISLER-assembled PCB
component.

#### Functional, power and safety flow

```text
Target output / legal route
  -> TI_RGB_DATA
  -> R901 470R
  -> RGB_DATA_PROTECTED
  -> TP901 and J902.3 DAT
  -> Adafruit 6066 input buffer
  -> onboard NeoPixel

TEST_BLOCK_3V3 -> J902.2 V
                  |
                  +-- C901 100nF -> TI_GND

TI_GND -> J902.1 G and TP902
J902.4 CLK -> explicit no-connect; mechanical engagement only
```

Firmware shall establish and verify the selected route before enabling the
target output. The target pin starts low or high impedance. The module is
inserted or removed only with Test Block power off and the route inactive.
TP901 is observation-only and shall be driven only by the target through the
accepted path.

The module accepts the harness 3.3 V input and generates its own local 5 V. No
module-generated 5 V or shifted output is returned to the harness, Target
Interface or a general-purpose connector. Brightness and test duration remain
bounded to the functional need until completed-board current measurements are
accepted.

#### Resolved review issue — module input contact order

The first schematic pass did not match the module's physical input order. The
Adafruit pinout and official source CAD establish input connector contacts
`1 G`, `2 V`, `3 DAT`, `4 CLK`. The owning Standard Test Blocks specification
was corrected before the schematic. The accepted Rev-A implementation now
connects J902 pin 1 to `TI_GND`, pin 2 to `TEST_BLOCK_3V3`, pin 3 to
`RGB_DATA_PROTECTED`, and marks pin 4 explicitly no-connect.

The four-position header is retained because all four mechanical positions
engage the module input connector. A deterministic contract now prevents any
future electrical reuse of the unused CLK position.

#### Manufacturer-source and application review

The following primary sources were reviewed for the baseline:

- [Adafruit Pixel Shifter overview](https://learn.adafruit.com/adafruit-pixel-shifter/overview),
  covering the 3 V to 5 V supply range, onboard level shifting, local 5 V
  generation and included NeoPixel.
- [Adafruit Pixel Shifter pinouts](https://learn.adafruit.com/adafruit-pixel-shifter/pinouts),
  defining the input and output terminal functions.
- [Adafruit Pixel Shifter official source CAD](https://github.com/adafruit/Adafruit-Pixel-Shifter-PCB),
  used to confirm the input connector numbering and the module-local power and
  logic boundary.
- [Würth Elektronik 61300411021 data sheet](https://www.we-online.com/components/products/datasheet/61300411021.pdf),
  confirming the selected four-position, right-angle, 2.54 mm through-hole
  header family and mating-pin geometry.

For this integrated board-level module, its official guide, pinout and source
CAD are the relevant application material. They require no further schematic
topology change. The actual screw-terminal-to-header engagement and mechanical
support cannot be accepted from drawings alone and remain physical checks.

#### Electrical and safe-state review

- The 3.3 V harness supply is within the module's documented 3 V to 5 V input
  range and keeps every harness-facing signal in the 3.3 V domain.
- R901 retains the common 470 Ohm digital protection value. The module input is
  high impedance, but the complete target, route, PCB, connector and module
  capacitance determines encoded-edge margin; prototype and completed-board
  waveforms remain authoritative.
- C901 is a local 100 nF bypass from `TEST_BLOCK_3V3` to `TI_GND`; it is not in
  series with the module supply. The module's own local capacitance remains in
  place.
- No fixed pull-up or pull-down loads `TI_RGB_DATA`. Safe startup therefore
  depends on route-before-drive sequencing and a low or high-impedance target
  output.
- Removing the module provides complete device isolation. J902, TP901 and
  TP902 are native DNP/hand-fit through-hole parts, preserving their copper and
  holes while excluding automated assembly.

#### Exact components and package state

| References/item | Current implementation | Review result |
|---|---|---|
| Removable module | Adafruit Pixel Shifter for Addressable LEDs, product `6066` | Accepted hand-fitted test accessory. Its local 5 V and shifted outputs remain module-local; actual fit and current remain physical checks. |
| `J902` | Würth Elektronik `61300411021`; 1x4 right-angle 2.54 mm THT; `Connector_PinHeader_2.54mm:PinHeader_1x04_P2.54mm_Horizontal`; value `PIXEL_SHIFTER_6066`; native DNP | Exact header MPN, footprint, four pad nets and assembly disposition accepted at schematic-baseline level. |
| `R901` | 470 Ohm, 1%, 0.1 W 0603; `AISLER_MPN = 470R 0603 1% 0.1W` | Value, footprint, metadata and target-to-DAT protection function accepted. |
| `C901` | 100 nF, 10%, 16 V, X7R 0603; `AISLER_MPN = 100nF 10% 16V X7R 0603` | Value, footprint, metadata and local supply-to-ground bypass function accepted. |
| `TP901`, `TP902` | Würth `61300111121`; 1x1 vertical 2.54 mm THT; native DNP | Accepted hand-fit protected-data and ground observation points under the board-wide test-point policy. |

#### Verification state

| Evidence | Result |
|---|---|
| Requirements and functional review | Accepted against Standard Test Blocks Section 6.9 and the Target Interface/route-destination assignments. |
| V1 prototype evidence | None: TB09 is new in V2. This absence is retained as a physical-verification requirement rather than treated as schematic evidence. |
| Connectivity contract | `verification/contracts/TB09-addressable-rgb-output.yaml` passes 25 checks: 12 pin/net, 5 component-value and 8 forbidden-direct-path assertions. The complete thirteen-contract baseline passes all 1071 checks. |
| Full-hierarchy ERC | Accepted root report dated 2026-08-15: zero errors and zero warnings. |
| Visual schematic review | Accepted focused image linked above. It shows the corrected G/V/DAT/CLK order, explicit CLK no-connect, protected data path, local bypass, DNP state and safe operating notes. |
| PCB synchronization | Accepted for schematic-baseline scope. `R901`, `C901`, `J902`, `TP901` and `TP902` each occur once with the accepted footprints and pad nets. J902, TP901 and TP902 carry native `through_hole dnp`; R901 and C901 carry their accepted AISLER metadata. Final placement and routing remain PCB-stage work. |

#### Closure actions and accepted exceptions

- Place J902 at the selected board edge with the physical module overhang,
  input-terminal access and onboard NeoPixel visibility preserved. Confirm
  screw-terminal engagement, support and adjacent Grove/microSD clearances
  using the actual module and header.
- Keep R901, J902 and TP901 on a short data path over a materially continuous
  ground reference. Place C901 at the J902 supply/ground entry and retain nearby
  TP902 probe access.
- Verify low/high-impedance startup, powered-off insertion/removal, 3.3 V input
  current, local-5-V containment and the 470 Ohm protected waveform. Retain
  device-off, primary/mixed-colour, repeated-update, byte-order and recovery
  results at the supported targets and brightness.

No TB09 schematic-baseline exception is accepted at this stage.

### 4.12 TI01 — Target Interface connector banks

**Purpose and requirements:** Provide the fixed 48-contact electrical and
mechanical boundary between the reusable harness and each removable target
daughter board. The implementation is governed by the accepted Target
Interface Contract, particularly Section 7.
**Source schematic:** root `Espruino_Harness_RevA.kicad_sch`, references
`J900` and `J901`.
**Visual review:** [Target Interface connector-bank image](review-images/TI01-target-interface-connector-banks.png).
**Risk:** High
**Status:** Power allocation superseded by the accepted 22 August 2026
correction. The connector products, footprints, harness/daughter gender,
native-DNP hand-fit disposition and mechanical evidence remain valid, but B01
must change from the duplicate `TI_TARGET_3V3` net to `TI_TARGET_VBUS`.
Connectivity, visual evidence, ERC and PCB synchronization must then be
refreshed before TI01 can become `Verified`.

#### Functional, power and safety flow

```text
Target daughter-board signals and target I/O-domain 3.3 V reference
  -> two 2x12 right-angle male banks cut from Adafruit 1541
  -> coplanar board-to-board mating boundary
  -> J900/J901 female banks cut from Adafruit 1543
  -> harness routing, control and Standard Test Block circuits

Harness switched target 5 V
  -> J900.23 and J901.23
  -> daughter-board manual VBUS-selector Supervisor input

Target-provided 3.3 V reference
  -> J900.1
  -> harness target-domain qualification and pull-ups only

Daughter-board selected target VBUS
  -> J901.1 as TI_TARGET_VBUS
  -> harness-local Standalone 5 V-to-3.3 V regulator

Twelve distributed connector contacts -> common TI_GND
```

J900 carries the seven routing entries, target reset and boot request, fixed
I2C, I2C feedback/interrupt, RGB and analogue signals. J901 carries the direct
GPIO-loopback, SPI, 1-Wire and UART signals. J900.1 is the sole
`TI_TARGET_3V3` reference contact; J901.1 is the `TI_TARGET_VBUS` return. Each
connector contributes one `TI_SWITCHED_TARGET_5V` contact and six ground
contacts; the two switched-5-V contacts are joined at both boards.

The harness uses two female banks and the daughter board uses two male banks.
Because Connector A and Connector B no longer use mixed gender as a key, their
board-height positions and edge datums shall be asymmetric. Both banks must
engage together only in the correct orientation. The boards are mated or
separated only while unpowered; the interface makes no hot-plug, first-mate or
last-break guarantee.

#### Manufacturer-source review

The following selected-product sources were reviewed:

- [Adafruit Product 1543](https://www.adafruit.com/product/1543) and its
  [female connector drawing](https://cdn-shop.adafruit.com/datasheets/P1543.pdf),
  covering the 2x36, 2.54 mm, right-angle socket stock used on the harness.
- [The Pi Hut SKU 104444](https://thepihut.com/products/0-1-2x36-pin-strip-right-angle-socket-female-header-5-pack),
  confirming the purchased five-pack, manual cutting method and gold-plated
  contacts.
- [Adafruit Product 1541](https://www.adafruit.com/product/1541) and
  [The Pi Hut SKU 104400](https://thepihut.com/products/break-away-0-1-2x36-pin-strip-right-angle-male-header-5-pack),
  confirming the matching 2x36, 2.54 mm, right-angle breakaway male stock for
  daughter boards.

The male stock is deliberately broken into 2x12 sections. The female housing
is not breakaway and requires a sacrificed socket position at each cut, then
dressing and inspection of the retained housing and contacts. The retail
sources establish pitch, form and plating but do not provide an accepted
contact-current rating. Received-part measurement and current-capacity evidence
therefore remain release requirements rather than inferred catalogue values.

#### Electrical and fault review

- The corrected allocation remains 48 contacts: 32 signals/controls, one
  target-3.3-V reference, one target-VBUS return, two switched-5-V contacts and
  twelve ground contacts.
- `TI_TARGET_3V3`, `TI_TARGET_VBUS`, `TI_SWITCHED_TARGET_5V` and `TI_GND` shall
  remain distinct nets. The interface shall not join the target reference,
  selected VBUS and switched Supervisor source.
- Distributed ground contacts place returns beside the principal signal
  groups and share rail-return current. Final copper, contact and daughter-board
  paths must still meet the PC02 voltage-drop allocation and all accepted
  target profiles.
- Signal contacts add no schematic pull-up, pull-down or protection element;
  their electrical behaviour remains owned by the corresponding routing,
  control or Test Block circuit.
- Partial or one-bank-only engagement can expose incorrect power and signal
  sequences. Mechanical asymmetry, rack constraints, clear A/B and pin-1
  marking, unpowered mating and physical fit tests are mandatory controls.

#### Exact components and package state

| References/item | Current implementation | Review result |
|---|---|---|
| `J900`, `J901` | Adafruit Product `1543`, purchased as The Pi Hut SKU `104444`; functional values `TARGET INTERFACE CONNECTOR A/B`; datasheet `P1543.pdf`; native DNP; `V2_Target_Interface:TargetInterface_2x12_P2.54mm_RA_Female_Adafruit1543_Harness` | Product, measured project footprint, metadata and post-AISLER mandatory hand-fit disposition accepted. B01 net correction remains pending. |
| Daughter-board mating banks | Adafruit Product `1541`, purchased as The Pi Hut SKU `104400`; two 2x12 male sections required per daughter; shared measured male project footprint | Accepted connector choice and footprint. Each daughter-board B01 net and manual VBUS-selector implementation remain pending. |
| Cut-stock procurement | Adafruit `1543` and `1541` are five-pack retail products rather than individually orderable 2x12 sections | KiCad reference quantities count prepared connector sections, not retail packs. Final procurement shall apply the recorded cut yield and include cutting spares rather than interpreting two schematic references as two retail packs. |

`AISLER_MPN` remains blank for J900/J901. Native DNP excludes them from AISLER
assembly while retaining them in the complete BOM; for TI01, DNP means
mandatory post-manufacture hand fitting rather than absence from the completed
board.

#### Verification state

| Evidence | Result |
|---|---|
| Requirements and functional review | Mechanical arrangement retained; B01 electrical allocation superseded and correction pending. |
| Connectivity contract | Historical 54-check result is superseded; update B01 and forbidden-net assertions after schematic correction. |
| Full-hierarchy ERC | Historical accepted report is superseded for TI01; rerun after correction. |
| Visual schematic review | Existing image is superseded by the B01 net change; replace after correction. |
| PCB synchronization | Measured harness footprints are assigned and present in the PCB; synchronize the B01 net after schematic correction. |

#### Closure actions and accepted exceptions

- Change J901.1/B01 from `TI_TARGET_3V3` to `TI_TARGET_VBUS` on the harness and
  every daughter board; update the PCB and deterministic connectivity contract.
- Establish adequate contact-current capacity for the accepted 3.3 V and 5 V
  limits. Include both contacts, PCB copper, daughter-board copper and the
  complete PC02 voltage-drop budget; do not assume equal current sharing without
  verification.
- Prove the asymmetric A/B placement, aligned top edges, simultaneous mating,
  rack insertion/removal clearance and resistance to reversal, exchange,
  one-pin offset and one-bank-only engagement using actual parts and a printed
  1:1 or fabricated-board check.
- Define a hand-assembly fixture or mated-board process that keeps both banks
  square, parallel and co-planar while end pins are tack-soldered and all joints
  are completed with power removed.

TI01 remains `Reviewed`; no exception is accepted for the pending B01
correction, current-capacity evidence or final physical mating proof.

## 5. System integration review

Use this section for checks that cross circuit-block ownership. Do not repeat
calculations or verification already recorded in the owning block.

| Interface or mode | Governing contract | Implemented by | Status |
|---|---|---|---|
| Target Interface | Target Interface contract | `TI01` | Reviewed; B01 power-net correction and physical verification pending |
| Rack Control/backplane | Standard Control Services | `BP01` | Draft |
| Supervisor | Standard Control Services | `PC01`, `PC02` | Draft |
| Standalone | Standard Control Services | `PC01`, `PC02` | Draft |
| Off/safe state | Standard Control Services | `PC01`, `PC02`, `RC01`, `RC02` | Draft |

The final integration review shall trace every power source, ground, connector,
control signal and operating mode across the complete hierarchy. It shall
also challenge startup, shutdown, missing-supply, partial-power and incorrect-
mode cases.

### 5.1 Accepted integration decisions

This table records accepted decisions that cross circuit-block ownership.
Their circuit implementation and release evidence remain subject to the owning
block review.

| ID | Decision | Implementation contract | Status |
|---|---|---|---|
| `INT01` | Use one MCP23017 for each Rack Control Endpoint | Port A owns six control outputs; Port B observes `TARGET_POWER_FAULT_N`, `TARGET_POWER_ALERT_N`, `SUP_EVENT_IN` and the latched `LOW_RANGE_OK_N`; `INTB` is the sole active-low open-drain `RACK_INT_N` source. Fault and alert events are host-only; `SUP_EVENT_OUT` changes only on an explicit Supervisor operation. The exact allocation is defined by Standard Control Services Section 8.3. | Accepted; schematic implementation complete and full-hierarchy ERC clean; firmware and release verification pending |
| `INT02` | Use one consistent fitted diagnostic test-point part across Rev A | All 43 `TP` references use Würth Elektronik `61300111121`, a one-position vertical 2.54 mm through-hole header pin, with `Connector_PinHeader_2.54mm:PinHeader_1x01_P2.54mm_Vertical`. Scope is Routing Control `TP601`–`TP614` and Standard Test Blocks `TP101`–`TP104`, `TP201`–`TP205`, `TP301`–`TP306`, `TP401`–`TP407`, `TP501`–`TP505` and `TP901`–`TP902`. Keep each part in the overall KiCad BOM with exact `MPN = 61300111121`. Mark each DNP so AISLER excludes it from its assembly stage, then hand-fit it after manufacture. For `INT02` only, DNP records an assembly-stage boundary rather than absence from the completed Rev-A board. This retains the accepted individual 2.54 mm header-pin architecture and common compatibility with probes, hooks, clips and female jumper leads. | Accepted policy, package mapping and MPN metadata; hierarchy-wide DNP application, PCB metadata and final accessibility review pending |
| `INT03` | Use one common daughter-board USB data path/manual VBUS selector and a harness-local Standalone regulator | D+/D−/GND pass continuously. The unpowered manual selector chooses host VBUS in Standalone or `TI_SWITCHED_TARGET_5V` in Supervisor, powers the target's normal USB VBUS input and returns the selected rail as `TI_TARGET_VBUS`. The harness 2x3 two-shunt selector chooses local or external 3.3 V and drives a resistor-protected static state that disables the TPS22917 input isolator in Supervisor. `SN74LVC2G14DBVR` derives `MODE_SUPERVISOR` and `TEST_BLOCK_AUTO_EN`. `TI_TARGET_3V3` is reference-only; no host-VBUS/select conductor crosses the Target Interface. | Architecture, TPSM828438 regulator, TPS22917 input isolator, SN74LVC2G14 mode stage and Würth `61300621121` plus two `60900213421` selector parts accepted; Target Interface allocation complete; PC01, TI01 and daughter-board implementations pending |

### 5.2 Open integration gaps

The accepted `INT03` correction is an open cross-block schematic integration
gap. PC01, TI01 and the daughter boards still implement the superseded
target-powered/No-VBUS assumptions and must be corrected together. The
48-contact interface is complete; VBUS selection is manual on each daughter
board and adds no interface signal.
The `DB-ESP32-FAMILY` implementation also has a target-specific UART
integration gate. V1 bench evidence proves that its native D18/D19 USB/JTAG
Adapter Service can provide the independent C3 control path, but that path
does not isolate the DevKitC-02 CP2102N TX output from UART0 RX on D20. The
unmodified-target profile must therefore prevent the TB07 full-crosslink state
and use endpoint-A external-peer operation unless a different mapping is
proved. A separately identified modified-target profile may enable the
crosslink only after target-side bridge-isolation evidence.
`LOW_RANGE_OK_N` is connected from PC02 to Rack Control `U1201.GPB3`, the
`SYS01` contract records that cross-block path, and the refreshed full
hierarchy passes ERC. Firmware verification remains a release check. Other
block-local issues and release checks remain in their owning analyses.

The clean first-pass ERC is an integration checkpoint, not the final accepted
release ERC. The release checklist remains unchecked until the block reviews,
connectivity contracts, packaging review and final cold review are complete.

## 6. Manufacturing release checks and decision

### PCB implementation action register

This register is the single handover point for PCB-stage work. It collects
physical implementation actions from the reviewed circuit blocks and governing
Rev-A specifications; it does not replace those sources or create new design
requirements. Add an action when a block review identifies a PCB dependency,
and close it only with the evidence named below.

| ID | Source | PCB action | Completion evidence | Status |
|---|---|---|---|---|
| `PCB-GEN-01` | Prototype Strategy Sections 5 and 10 | Hold the harness height at 100 mm, extend only its length if more area is required, and preserve the backplane datum, mounting-hole positions and mechanically fixed connector locations. | Dimensioned board drawing, KiCad measurements and printed 1:1 review | Open |
| `PCB-GEN-02` | Prototype Strategy Section 4 | Begin with the accepted two-layer preference, preserve a materially continuous ground reference, and change to four layers if placement or routing demonstrates one of the documented two-layer failure conditions. | Reviewed stack-up decision plus ground-plane and critical-route inspection | Open |
| `PCB-GEN-03` | Prototype Strategy Sections 3 and 7 | Keep isolation links, selectors, test points, removable modules and diagnostic access usable with the target fitted; retain clear pin-1, polarity and mode markings. | 3D review, printed 1:1 review and access checklist | Open |
| `PCB-PC01-01` | PC01 correction | Place the TPS22917 input isolator, TPSM828438 regulator module, manufacturer-required capacitors, 249 kΩ VSET resistor, manual 2x3 two-shunt selector, static mode stage and U1002 bypassing as compact power groups. Follow TI's QFN-FCMOD land pattern and short input/output/ground-loop guidance; keep the VSET node free of added leakage/capacitance and assess required connector-side bulk capacitance. | Placement inspection, routed-copper and thermal review, manufacturer-footprint comparison and recorded capacitance decision | Open |
| `PCB-PC01-02` | PC01 correction | Provide accessible measurement points for `TI_TARGET_VBUS`, isolated regulator input, local regulated 3.3 V, `TI_TARGET_3V3`, `EXT_3V3`, `ROUTING_LOGIC_3V3`, `TEST_BLOCK_3V3`, isolator enable and `MODE_SUPERVISOR`. Verify selector labelling/access, complete disabled-branch leakage against the 100 nA allocation through 55 °C and the Standalone target-plus-harness USB load envelope. | PCB inspection, probe-access review, leakage evidence and load/startup captures | Open |
| `PCB-PC02-01` | PC02 and TPS2559-Q1 data sheet | Connect U1101 PowerPAD pad 11 to `TI_GND` with short, wide copper and nearby ground vias. Keep vias out of the paste-covered pad unless AISLER accepts a changed via-in-pad process. | Routed-layout inspection, thermal/ground review and AISLER DFM confirmation | Open |
| `PCB-PC02-02` | PC02 measurement design | Use the accepted project-local footprints for `R1101` and `R1102`; take separate Kelvin sense traces directly from the corresponding shunt pads to each monitor IN+/IN− pair, away from load-current copper and noisy switching routes. | Pad-level net inspection, routed Kelvin-pair review and PCB DRC | Open |
| `PCB-PC02-03` | PC02 voltage-drop budget | Size and review the complete 1.5 A path so PCB, Target Interface, backplane and connector resistance remains within the provisional combined 26 mΩ allocation. | KiCad conductor calculation, connector/contact calculation and completed-layout path review | Open |
| `PCB-PC02-04` | PC02 transient and accuracy budgets | Keep power-monitor decoupling local, minimize low-current leakage and thermal-gradient error around the 1 Ω path, and determine the required local `EXT_5V` bulk capacitance from the completed target-load estimate. | Placement review, leakage/thermal review and recorded transient calculation | Open |
| `PCB-RC01-01` | RC01 TMUX1511 data sheet and application review | Place each `C601`–`C605` 100 nF capacitor at its owning switch VDD/GND pins with short, low-inductance connections. | Placement inspection and routed power/ground review | Open |
| `PCB-RC01-02` | RC01 shared-node capacitance and simultaneous-use review | Keep route-entry and switch-to-endpoint paths short over a materially continuous ground reference. Separate the analogue route from SPI clock and control edges, and review the complete PCB, connector and daughter-board capacitance against the recorded 10 pF, 14 pF and 18 pF switch contributions. | Routed-layout inspection, complete path-capacitance record and signal-integrity review | Open |
| `PCB-RC01-03` | RC01 powered-off protection review | Control ringing and overshoot so target-facing switch pins remain within the 3.6 V powered-off limit, then measure leakage and resulting unpowered-rail voltage for every supported target/routing power sequence. | Oscilloscope captures, leakage measurements and partial-power acceptance record | Open |
| `PCB-RC01-04` | RC01 analogue and SPI concurrency review | Provide practical access to the representative route, endpoint and enable observation points and compare analogue accuracy/noise with SPI idle and active. Establish route-settling and first-ADC-sample handling from the measurements. | Probe-access inspection and retained analogue/SPI prototype results | Open |
| `PCB-RC01-05` | RC01 redundant-resistor cleanup | Update the PCB from the accepted root schematic so obsolete footprints `R603`, `R608`, `R13`, `R18`, `R23` and `R25` are removed without disturbing the 19 functional pull-downs or direct TMUX ground connections. | PCB component inspection, refreshed BOM and PCB DRC | Open |
| `PCB-RC02-01` | RC02 TPS3808 data-sheet review | After the schematic correction, place each 4.7 nF SENSE bypass directly between its owning `U607`–`U609.SENSE` pin and `TI_GND`. Keep `C607`–`C609` as separate 100 nF VDD bypasses placed at the corresponding VDD/GND pins; place `C606`, `C610` and `C611` locally at their owning TMUX1511 and MCP23017 supplies. | Placement inspection and routed power, SENSE and ground review | Open |
| `PCB-RC02-02` | RC02 I2C pull-up and TMUX1511 application review | Keep the fixed-I2C paths short over a materially continuous ground reference and record total PCB, connector, endpoint and enabled-switch capacitance. Verify the 2.35 kΩ and approximately 1.57 kΩ effective pull-up cases against the selected bus rate. | Completed capacitance/rise-time calculation, routed-layout inspection and oscilloscope captures for every permitted isolation state | Open |
| `PCB-RC02-03` | RC02 supervisor output-margin and indeterminate-state review | Keep each TPS3808 RESET connection short and referenced to the same local ground as the controlled device. Measure RESET/enable, `ROUTE_CLEAR_N`, monitored rail and `ROUTING_LOGIC_3V3` during cold start, slow ramp, brownout and power-down; confirm no false TMUX1511 enable or premature MCP23017 reset release and retain the asserted-low margin evidence. | Layout inspection and retained multi-channel rail/reset oscilloscope captures including the worst measured `VOL` | Open |
| `PCB-TB01-01` | TB01 isolation and diagnostic review | PCB metadata synchronization is complete. During real placement, keep `JP101/JP102` and `TP101`–`TP104` where both shunts can be changed and every test pin can be probed with the target fitted. Mark pair A/B, OUT/IN and the normal fitted-shunt state clearly on silkscreen. | Placement, 3D and printed 1:1 access review | Open |
| `PCB-TB01-02` | TB01 signal and fault review | Keep each output-resistor-header-input path short and keep pairs A and B visually and electrically distinct. Review the complete routed and daughter-board loading, then measure representative static, edge, pulse and shift behaviour through the selected routes. | Routed-path inspection, PCB DRC and retained prototype waveforms/results | Open |
| `PCB-TB03-01` | TB03 component and access review | Exact component metadata and PCB synchronization are complete. Place `J301` near the upper outer edge with its mating face outward and body supported within the outline. Place `J302`, `JP301`–`JP304`, `JP306`–`JP309` and `TP301`–`TP306` so pin 1, normal shunt state and every diagnostic contact remain clear and accessible with the target fitted. | 3D mating-part review, printed 1:1 access check and final BOM comparison | Open |
| `PCB-TB03-02` | TB03 shared-I2C and pull-up review | Keep SDA/SCL together over a materially continuous ground reference, keep `C301` local to U301, and avoid branch stubs or fast aggressors. Measure total effective pull-up resistance, bus capacitance, rise time and valid-low level for the populated board and each supported Grove configuration at the accepted bus rates. | Routed-layout inspection, PCB DRC, unpowered resistance measurements and retained oscilloscope captures | Open |
| `PCB-TB03-03` | TB03 isolation and event review | Keep the isolated VDD/RESET/INTA domain compact and preserve the protected event-stage gate pull-downs and ground returns. Verify all shunt boundaries and capture cold start, power-down, supply-isolated, feedback, mirrored interrupt and both Supervisor event behaviours. | Pad-net inspection, isolation continuity matrix and retained functional/oscilloscope evidence | Open |
| `PCB-TB04-01` | TB04 module mechanics and assembly | Place the DNP/hand-fitted J402 footprint on the underside at the upper edge with card access outward. Verify the actual ADA5683 outline, castellated-land registration, solder access, mechanical support, adjacent Grove clearance and complete insertion/withdrawal envelope. Confirm all six electrical and eight unnumbered mechanical lands remain copper/mask only with no paste. | Actual-module inspection, 3D review, printed 1:1 fit/access check and final hand-assembly record | Open |
| `PCB-TB04-02` | TB04 SPI layout and local capacitance | Keep U401/J402 shared SCK, MOSI and MISO paths compact over continuous ground; avoid long MISO branches; keep R401/R402 local to their chip-select branches. Place C401 at U401 VDD/VREF, C402 closest to J402 and C403 immediately nearby. Confirm C403 effective capacitance and the complete `TEST_BLOCK_3V3` switched-capacitance budget. | Placement/routing inspection, capacitance record, PCB DRC and signal captures at the selected maximum SPI clock | Open |
| `PCB-TB04-03` | TB04 diagnostics and populated operation | Hand-fit Harwin `D2816-42`, U401, J401, J402 and TP401–TP407 with power removed. Preserve socket/header pin-1, CH0–CH7 and card-access markings and probe access. Verify both inactive chip selects, MCP3008 conversions and Block 2 agreement, alternating shared-bus transactions, microSD connect/mount/file/unmount behaviour and safe card removal. | BOM/assembly reconciliation, continuity checks and retained functional-test results | Open |
| `PCB-TB05-01` | TB05 connector and module mechanics | Place J501/J502 for practical sensor-lead entry and mark each terminal `GND | DQ | 3V3`, explicitly accounting for the reversed C3 V1 terminal order. Mark J504 pin 1 and `PIOB | PIOA | DQ | GND`; verify the selected DS2413 breakout, downward female header, body clearance and fitted orientation using the actual parts. Keep J503 accessible and mark `2K2 | DQ | 4K7` with pins 1–2 as normal. | Actual-part inspection, 3D review, printed 1:1 access/orientation check and final hand-assembly record | Open |
| `PCB-TB05-02` | TB05 1-Wire topology and routing | Keep the DQ trunk and J501/J502/J504 branches short over a materially continuous ground reference, avoid unnecessary stubs and fast aggressors, and preserve access to TP501–TP505. Record PCB, connector, module and representative sensor-lead loading; include every accessory-provided pull-up when calculating effective resistance. | Routed-layout inspection, PCB DRC, topology/lead record and probe-access review | Open |
| `PCB-TB05-03` | TB05 populated-bus operation | With the normal full population and representative leads, measure DQ low level, rise time and at least the provisional 6 us recovery-time target. Retain repeated three-ROM search, DS18B20 scratchpad/CRC, DS2413 command/status and both protected PIO-feedback results. Compare J503's normal 2.2 kOhm and diagnostic 4.7 kOhm positions and record the supported population/lead conditions for each. | Oscilloscope captures, resistance measurements and retained functional/soak-test evidence | Open |
| `PCB-TB07-01` | TB07 switch placement and routing | Keep U701, C701 and R701–R708 as one compact functional group over a materially continuous ground reference. Place C701 at U701 VDD/GND, retain each 470 Ohm resistor in its owning switched path, minimize UART stubs and separate the paths from fast power/control aggressors. | Placement and routed-path inspection, PCB DRC and ground-reference review | Open |
| `PCB-TB07-02` | TB07 connector access and identification | Place DNP/hand-fitted J701 and J702 as physically and visually separate 1x3 headers that cannot be mistaken for a symmetric 2x3 interface. Mark pin 1, `PEER`, `DIAGNOSTIC - NO DRIVE`, peer-perspective TX/RX, GND and no-power status; confirm cable and high-impedance probe access using the actual parts. | Actual-header inspection, 3D review, printed 1:1 access check and silkscreen review | Open |
| `PCB-TB07-03` | TB07 safe-state and populated operation | Verify `0000` safe/open, `1100` full-duplex crosslink and `0011` endpoint-A peer states with controller readback; reject every other state. Capture cold start, Hardware Clear, power-down and powered-off isolation, then retain bidirectional UART results at V1-proven rates/framing and characterize the completed-board maximum rate and edge quality. | Continuity/state matrix, oscilloscope captures, routing-control logs and retained UART/peer functional-test evidence | Open |
| `PCB-DB-C3-01` | ESP32-C3 Target Routing Envelope and 5 September 2026 V1 UART evidence | Implement and verify the C3 native D18/D19 USB/JTAG Adapter Service without treating it as UART0 bridge isolation. For an unmodified DevKitC-02, define the endpoint-A external-peer Target Profile and prevent TB07 `1100` full-crosslink selection. If a modified-target profile is retained, identify the target-side CP2102N TX isolation explicitly and require continuity, D20 bias and bidirectional transfer proof before enabling `1100`. | Daughter-board schematic and connectivity review, Target Profile state-policy test, repeated `/dev/ttyACM` enumeration, D20 ownership measurement and retained UART evidence | Open |
| `PCB-TB09-01` | TB09 module mechanics and identification | Place native-DNP J902 at the selected board edge so the actual Adafruit 6066 input screw terminal engages all four header positions, the module overhang is supported, its NeoPixel remains visible and adjacent Grove/microSD access is unobstructed. Mark pin 1 and `GND | 3V3 | DAT | NC`; make reversal visibly implausible. | Actual-module/header fit, 3D review, printed 1:1 access check and silkscreen review | Open |
| `PCB-TB09-02` | TB09 protected data and local power layout | Keep R901, J902 and TP901 on a short path over a materially continuous ground reference. Place C901 directly at the J902 3.3 V/ground entry and retain nearby TP902 ground access. Confirm J902.4 has no copper connection and keep module-local 5 V isolated from all harness nets. | Routed-layout and pad-net inspection, PCB DRC, ground-reference review and probe-access check | Open |
| `PCB-TB09-03` | TB09 startup, waveform and functional operation | With the actual module, verify powered-off fit/removal, route-before-drive sequencing, low/high-impedance startup, 3.3 V input current and absence of exported module 5 V. Capture the R901-protected encoded waveform at TP901 and retain off, primary/mixed-colour, repeated-update, byte-order and recovery results at the supported targets and bounded brightness. | Power/current measurements, oscilloscope or logic-analyser captures and retained NeoPixel functional-test results | Open |
| `PCB-IF-01` | Target Interface Contract and Prototype Strategy | Prepare 2x12 sections from Adafruit `1543` female and `1541` male stock; measure and accept the exact footprints, holes, body/edge datums and mating depth. Place the two banks asymmetrically with aligned board tops, clear A/B and pin-1 markings, and prove simultaneous engagement without reversal, exchange, one-pin offset, one-bank-only engagement or PCB twist. Verify contact/current and voltage-drop capacity, rack access and the post-AISLER hand-fit alignment process using actual parts. | Accepted project footprints, pad mapping, current/contact calculation, 3D model, printed 1:1 check, actual-part mating review and assembly record | Open |
| `PCB-IF-02` | Standard Control Services Section 3.4 and Target Interface Contract | Implement and review the common USB data path and manual VBUS selector on every daughter board. Keep D+/D− short and paired; route host VBUS only to the Standalone input, A23/B23 only to the Supervisor input and the common output to target USB VBUS plus B01 `TI_TARGET_VBUS`. Verify switch current/contact resistance/inrush, clear mode labelling, source isolation, repeated USB enumeration and Supervisor preflight detection of a wrong selector state. | Manufacturer-source selector review, PCB DRC, continuity/source-isolation measurements, oscilloscope captures and repeated enumeration/power-cycle evidence | Open |
| `PCB-PANEL-01` | Prototype Strategy Section 6 | Implement the harness/daughter-board breakaway geometry, Breakaway Links and local trace neck-down rules without vias or layer changes in the bridges. | Panel drawing, PCB DRC and AISLER manufacturing review | Open |
| `PCB-REL-01` | Prototype Strategy Section 9 | Complete final PCB DRC, 3D and printed 1:1 reviews, silkscreen/polarity review, AISLER rendering/orientation review and BOM Assign before release. | Accepted reports, review record and final AISLER project/quote | Open |

Rows for Routing Control, Standard Test Blocks, Rack Control and the remaining
interfaces shall be added as their block reviews reach the same maturity as
PC01 and PC02. PCB work may start before then, but manufacturing release
remains blocked until the register and release checklist are complete.

### Accepted ERC and DRC exclusions

No exclusion is accepted without a specific explanation.

| Check | Location | Justification | Approved |
|---|---|---|---|
| None recorded | — | — | — |

### Release checklist

- [ ] All applicable requirements map to implemented circuit blocks.
- [ ] Every circuit block is `Verified`.
- [ ] Every high-risk block has an accepted logic/state or electrical-limit analysis.
- [ ] Every key design issue has a recorded disposition and verification result.
- [ ] No unresolved major design issue remains.
- [ ] Full-hierarchy ERC is accepted after the power correction.
- [ ] Corrected PC01 and TI01 connectivity contracts pass.
- [ ] All IC and connector package/pin mappings are checked.
- [ ] BOM matches the intended fitted and DNP configuration.
- [ ] PCB DRC is accepted.
- [ ] Mechanical dimensions and connector placements are checked.
- [ ] AISLER BOM groups match the intended references, values and footprints.
- [ ] AISLER assignments/exclusions match the approved component tables.
- [ ] Deterministic KiCad-to-AISLER BOM reconciliation passes with no
      unassigned, unreviewed, mismatched or unexpected references.
- [ ] Final AISLER part availability and quoted assembly cost are accepted.
- [ ] Rev-A first-power and bring-up procedure is prepared.
- [ ] Open issues and accepted exceptions are recorded.
- [ ] Baseline Git commit is recorded above.
- [ ] Manufacturing release decision is approved.

### Release decision

**Current decision:** Not approved for manufacture.

Before approval, perform a final cold review from the governing requirements,
this baseline, the complete schematic, the contracts, PCB, BOM and AISLER
upload. Do not rely on the original drafting discussion as evidence. Record
the accepted Git commit and decision in Section 1.

## Appendix A — Rev-A circuit design and verification method

### A.1 Purpose

The process exists to maximise the chance that the first manufactured Rev-A
board works without building separate circuit prototypes. It must establish
two things:

1. the selected circuit should meet its requirements and behave safely
2. KiCad and the manufactured board implement that reviewed circuit

Retain information only when it supports one of those conclusions or provides
necessary traceability.

### A.2 Block review cycle

#### A.2.1 Define the required behaviour

Record the block's inputs, outputs, power and ground domains, operating modes,
safe state and electrical limits. Link the governing requirement rather than
repeating it.

#### A.2.2 Prove the circuit approach

Explain how the selected circuit provides the required behaviour. Logic,
switching and sequencing blocks require a concise truth or state table.
Analogue and power blocks require the applicable threshold, polarity,
startup, shutdown, partial-power, back-power, voltage-drop, dissipation,
accuracy and datasheet-support checks.

For every principal device, review the current manufacturer product page,
data sheet and every product-linked application note, application brief or
design guide before accepting the circuit approach. Record the documents that
affect this use and their implementation consequences. Group documents that
do not apply and state why they were excluded; a long bibliography without an
engineering conclusion is not evidence. Application material guides the
design, while guaranteed limits and pin behaviour come from the current data
sheet. Repeat this source screen when a principal device changes.

Any finding that conflicts with a required operating mode, safety property or
interface contract shall be recorded prominently in the block's **Key design
issues** subsection. Record its severity, affected requirement, evidence,
resolution or blocking status, and verification impact. Do not bury such a
finding in implementation detail, a component table or a general open-issues
list. A major unresolved issue keeps the block in `Draft` and blocks
manufacturing release.

Use simulation only where it resolves a material uncertainty.

#### A.2.3 Implement and visually review

Draft the bounded circuit in the workbench or production sheet, then inspect
it interactively in KiCad. Correct placement, grid alignment, symbol
orientation, labels and visible wiring. Save one readable accepted screenshot
under `implementation/review-images/`. The screenshot records the circuit
reviewed; it is not connectivity authority.

#### A.2.4 Check parts and physical implementation

For every IC, connector and critical passive:

- select an exact orderable part
- confirm its electrical and package limits
- check symbol pin numbers against the data sheet
- check footprint pads and dimensions against the package drawing
- confirm symbol-to-footprint mapping
- record whether AISLER should assign, exclude or leave the part for hand
  fitting

Ordinary passives may follow an agreed package policy. Shunts, precision,
high-current and unusual parts require individual checks.

Use the following KiCad symbol-field policy:

- `Value` records the functional component identity or nominal value. It is not
  the definitive purchasing field.
- `MPN` records an approved exact, orderable manufacturer part number.
- `AISLER_MPN` records an approved AISLER Smart Match specification when the
  manufacturer part is intentionally left open but its required
  characteristics are controlled.
- `SHUNT_MPN` records one required removable shunt fitted to the owning header.
  It is an accessory field rather than a substitute for that header's `MPN`;
  the deterministic BOM shall expand one shunt for each populated field.
- A fitted assembly component shall normally use either `MPN` or `AISLER_MPN`,
  not both. Explain any deliberate exception in its block component table.
- A required fitted component may not reach release with both fields blank.
  Record DNP, excluded and hand-fitted dispositions explicitly instead.

By default, DNP means that a component is absent from the completed board. A
recorded staged-assembly decision may define a narrower meaning. `INT02` test
points and the Block 4 Adafruit 5683 module `J402` are Rev-A exceptions: they
are DNP for the AISLER assembly stage but are mandatory hand-fitted parts on
the completed board. They retain their exact MPNs and remain in the overall
KiCad BOM.

Use the block component table as the engineering reference during AISLER BOM
Assign. For each presented group:

1. confirm that AISLER has grouped the intended references and interpreted the
   KiCad value/comment and footprint correctly
2. select the approved exact MPN, or an alternative that meets the recorded
   requirements
3. use the presented data-sheet link to recheck package, pinout and critical
   electrical characteristics
4. record the accepted MPN and assignment/exclusion state in this baseline

Live stock and unit price remain in the AISLER project or quote. Record them
here only when cost or availability causes a design or part-selection change.

#### A.2.5 Create the independent connectivity contract

Author one compact YAML contract from the accepted circuit analysis, not by
copying the KiCad netlist. Add it to the manifest only when it contains real
reviewed intent.

Record only assertions the checker can evaluate:

- important component pin to expected net
- operationally significant value or fitted/DNP state
- critical connector contact to net
- forbidden direct connection
- exact net membership where an unexpected member would be dangerous

Explanations, status, evidence and open issues remain in this baseline.

#### A.2.6 Verify the KiCad implementation

Run ERC and export the netlist from the root production schematic. Run the
[specified connectivity checker](ReusableHarnessRevA_ConnectivityChecker.md)
against the complete contract set and resolve every mismatch. A material
circuit or contract change returns the block to `Draft`.

Use these block states:

- `Draft`: design or evidence incomplete
- `Reviewed`: circuit behaviour and implementation accepted; deterministic
  checks not all accepted
- `Verified`: behaviour, parts, visual review, ERC and connectivity checks
  accepted

Manufacturing release is a board-level decision, not a fourth block state.

### A.3 System and release review

After all blocks are verified:

1. Trace every power source, ground, connector, control signal and operating
   mode across the complete hierarchy.
2. Challenge startup, shutdown, missing-supply, partial-power and incorrect-
   mode cases.
3. Complete BOM, footprint, PCB DRC and mechanical checks.
4. Upload the production PCB to AISLER and complete BOM Assign against the
   approved component tables. Confirm the final part selection, exclusions
   and quoted assembly cost.
5. Perform a cold review from the requirements, baseline and production
   artifacts without relying on the drafting discussion.
6. Record the accepted Git commit and manufacturing decision in this
   baseline.

### A.4 Connectivity checker behaviour

The detailed requirements, design, invocation, outputs and scope limits of the
tool required by this baseline are defined in the
[Rev-A Connectivity Checker specification](ReusableHarnessRevA_ConnectivityChecker.md).
The summary below records the acceptance intent within the Rev-A process.

The checker shall:

1. read the manifest and every referenced substantive contract
2. reject missing files, duplicate IDs and contradictory definitions
3. read the raw full-hierarchy KiCad netlist
4. produce a sorted, path-free normalized connectivity model
5. report missing required connections, forbidden connections, unexpected
   critical-net membership and contract entries that cannot be resolved
6. return a failing result for every unresolved mismatch
7. produce the deterministic connectivity report retained as release evidence

Each mismatch shall be classified as:

- a schematic defect, requiring a KiCad correction
- a contract defect, requiring renewed requirements or datasheet review
- an unresolved design decision, which keeps the block in `Draft`

After correction, regenerate the full-hierarchy netlist and run the complete
contract again so that a local fix cannot introduce a cross-block regression.

A checker pass means that the production schematic matches the independently
reviewed connectivity contract for the recorded scope. It does not prove
analogue performance, component suitability, package mapping, PCB layout or
complete system behaviour.

At release, the manifest, substantive contracts, KiCad sources and generated
evidence are frozen by the Git commit recorded in this baseline.

### A.5 Circuit-block record template

Create one subsection per block under Section 4. Keep it concise and refer to
the governing specification rather than repeating it. In Section 4, use a
level-three heading for the block and level-four headings for its internal
analysis.

#### XX00 — Circuit name

**Purpose and requirements:** TBD
**Source schematic:** TBD
**Visual review:** TBD
**Risk:** Standard/High
**Status:** Draft

##### Interfaces and domains

| Type | Signals or rails | Function |
|---|---|---|
| TBD | TBD | TBD |

##### Key design issues

Record each material requirement conflict and its disposition. State `None`
only after the operating modes, safe states, partial-power cases and principal
device data sheets have been reviewed.

##### Selected implementation

- Circuit approach: TBD
- Principal devices: TBD

##### Operating logic and safe states

Add the applicable truth/state table and startup, shutdown, unpowered or
partial-power conclusions. For a simple passive block, state the normal and
isolated configurations instead.

##### Key calculations and limits

TBD.

##### Components and packaging

| References | Manufacturer | Exact orderable part | Package | KiCad symbol | KiCad footprint | Datasheet/revision | Pin/pad mapping | AISLER assignment |
|---|---|---|---|---|---|---|---|---|
| TBD | TBD | TBD | TBD | TBD | TBD | TBD | Pending | Pending |

Ordinary passives may be covered by an agreed package policy. ICs, connectors,
unusual passives and safety-critical components require an individual record.

##### Verification

| Check | Evidence | Result |
|---|---|---|
| Requirements inspection | Governing specification | Pending |
| Behaviour and safe-state analysis | Logic/state table or electrical analysis | Pending |
| Datasheet and pin functions | Datasheet reference | Pending |
| Connectivity contract | Normalized connectivity report | Pending |
| Full-hierarchy ERC | ERC report | Pending |
| Symbol-to-footprint pin mapping | Library/footprint inspection | Pending |
| Visual schematic review | Review image | Pending |

##### Open issues and accepted exceptions

TBD.

### A.6 Visual review images

Store one current accepted PNG for each circuit block, using the block ID and a
short lower-case description:

```text
PC01-operating-mode-and-3v3-rail.png
PC02-target-5v-switch-and-two-range-monitor.png
RC01-routing-fabric.png
TB03-i2c-functional-device.png
```

Replace the image under the same name after a material change; Git preserves
the earlier version. Intermediate screenshots need not be retained unless they
record an important defect or decision.

A review image should show the circuit title, references, values, pin numbers,
net labels, support components, notes and the complete circuit boundary at a
readable scale. It is visual review evidence, not the source of connectivity.

### A.7 Verification artifact names

Production evidence is always generated from the root schematic and uses:

```text
Espruino_Harness_RevA_FullHierarchy.net
Espruino_Harness_RevA_FullHierarchy_ERC.rpt
```

Workbench-only diagnostics use:

```text
draft_workbench_Working.net
draft_workbench_Working_ERC.rpt
```

Do not name a full-hierarchy export after an individual sheet. Sheet-only
checks are working diagnostics and are not baseline evidence.

Raw KiCad netlists are placed under `verification/generated/`. They are not
tracked because they contain volatile timestamps and checkout-specific paths.
The normalized, path-free connectivity report and other accepted release
evidence are tracked under `verification/baseline/`. This document records the
manufacturing decision; no second manually maintained summary is required.

### A.8 BOM and assembly-assignment reconciliation

Final manufacturing release shall include a per-reference comparison between
the BOM defined by the KiCad hierarchy and the component assignments presented
by AISLER. This is a release-stage check and does not block acceptance of an
individual circuit block while the remaining schematic is still under
development.

The KiCad BOM is the authoritative statement of design intent. Generate it
deterministically from the root schematic with, at minimum, reference,
quantity, value, footprint, DNP state, exact `MPN` and `AISLER_MPN` Smart Match
requirements. The overall BOM shall include DNP rows; do not use an export mode
that removes them. `Value` and footprint provide supporting identity checks but
do not override either sourcing field.

Capture the corresponding AISLER assignment data from the live BOM page:

1. open the browser developer tools and select **Network** and **Fetch/XHR**
2. reload the BOM page and locate the `bom.json` request
3. use **Copy response**, not **Copy as cURL**
4. save the response as dated JSON
5. after all assignments are confirmed, print the complete grouped BOM page to
   PDF as human-readable evidence

Use these release-evidence names:

```text
YYYY-MM-DD-AISLER-BOM-confirmed.json
YYYY-MM-DD-AISLER-BOM-confirmed.pdf
```

A working capture taken before final confirmation may instead use
`YYYY-MM-DD-AISLER-BOM-assigned.json`. Do not retain a saved AISLER HTML page:
it contains no embedded BOM rows and may contain session-related metadata.

Normalize the JSON to a naturally sorted, one-row-per-reference representation
before comparison. Omit volatile AISLER identifiers, prices and timestamps from
the comparison keys. Retain the dated raw JSON and PDF as source evidence.

The reconciliation shall verify:

1. every assembly reference occurs exactly once in both sources
2. each exact KiCad `MPN` directly matches the AISLER-assigned physical-part
   manufacturer part number
3. each KiCad `AISLER_MPN` requirement is represented by AISLER's parsed Smart
   Match value, tolerance, voltage, dielectric, power rating and package
   parameters, as applicable
4. KiCad DNP and BOM-exclusion states agree with the AISLER state, including
   every staged hand-assembly exception recorded by this baseline
5. every hand-fitted test point under `INT02` retains exact
   `MPN = 61300111121` in the overall KiCad BOM, is DNP and excluded from AISLER
   assembly, and is classified `HAND_FIT` rather than absent
6. no required assembler-fitted component is unassigned or awaiting assignment
   review
7. no footprint mismatch or unexpected component assignment remains

The structured comparison provides deterministic coverage. The PDF records
what the AISLER interface displayed at the release point. Neither artifact
replaces the KiCad schematic as the source of component requirements.
