SimonGAndrews/ESP32_SGATest/docs/design/V2Harness/arch/StandardControlServices_V2.md

# V2 Standard Control Services

**Status:** Accepted — two-position manual power architecture; Rev-A schematic update pending

**Version:** 0.3

**Last Updated:** 22 August 2026

## 1. Purpose

This document defines the reusable services used to configure, operate,
observe and recover the V2 harness system. It covers Power Control,
host-facing target control, console and firmware flashing, direct reset and
boot, Routing Control, and the minimum Harness Supervisor services needed for
recovery, sleep/wake, Wi-Fi and Bluetooth Low Energy (BLE) testing. It also
defines the prototype rack arrangement in which one Supervisor serves up to
eight independent rack positions.

The standard harness shall remain useful in a **Standalone** mode without a
**Harness Supervisor**. A Supervisor adds unattended control and recovery but
is not required for Standalone testing.

This document defines behaviour and practical system boundaries. Component
selection, detailed circuits and physical Target Interface contacts remain
downstream design work.

## 2. Control-Service Principles

Control Services shall start in electrically safe states without depending on
target or Supervisor software. A defined hardware reset or recovery action
shall return controlled routes to their safe states and shall not leave a
competing driver or uncontrolled target supply.

The Target Profile shall state which services and owners are available. The
Resolved Test Configuration shall record the selections and observed states
needed to reproduce a test.

The USB data path and manually selected VBUS path are common Adapter Services
on every target daughter board. Target-specific connector, polarity and
protection details remain daughter-board responsibilities. The reusable
harness owns the common Standalone 5 V-to-3.3 V regulator because the accepted
target set cannot be required to supply the complete harness load from target
3.3 V.

### 2.1 Operating-Mode Capability Summary

The reusable harness provides its routing and Standard Test Block functions in
both active operating modes. `SUPERVISOR` additionally provides the independent
control, observation and recovery services that must remain available while
the target is unpowered or unresponsive. Availability still depends on the
interfaces declared by the applicable Target Profile.

| Capability | `STANDALONE` | `SUPERVISOR` |
|---|---|---|
| Target execution, functional tests and direct Routing Control | **Available.** The target owns the routing-control I2C. | **Available.** The target retains ownership of the routing-control I2C. |
| Standard Test Blocks | **Available**, powered by the harness-local regulator and enabled automatically. | **Available**, powered from external regulated 3.3 V and enabled by the Supervisor when required. |
| Host console, test control and firmware flashing | **Available** through the target's normal USB or another declared host endpoint. | **Available** through the same target endpoint; the daughter-board selector isolates host VBUS while passing USB data and applying harness-controlled target VBUS. |
| Harness-controlled target power cycling | **Not available.** Host USB supplies target VBUS. | **Available** through the switched, monitored and manually selected external 5 V target supply. |
| Integrated target voltage, current and sleep-current measurement | **Not available.** Use external instrumentation. | **Available** through the Target Power Monitor and its normal- and low-current ranges. |
| Harness-controlled direct reset and boot requests | **Not available.** Use a declared target/host automatic sequence or manual controls. | **Available** through the selected Rack Control Endpoint and target-specific daughter-board mapping. |
| Rack-position selection and Rack Control Endpoint services | **Not available.** | **Available.** The Supervisor selects and controls one rack position at a time. |
| Automated external sleep/wake stimulus and timestamped acknowledgement | **Not available.** Timer wake and manual stimulus remain possible while the local regulator keeps harness services powered. | **Available** through the Supervisor event interface; timer wake also remains available. |
| Harness Supervisor Wi-Fi/BLE test peer | **Not available.** An independently provided peer may still be used. | **Available.** |
| Unattended out-of-band recovery from unresponsive target firmware | **Not available.** Host-endpoint recovery or operator intervention is required. | **Available** through independent power, reset, boot and host-observation services. |

## 3. Power Control Service

### 3.1 Architecture

Two deliberately coordinated, two-position manual selectors define the
active operating mode:

1. a daughter-board VBUS selector chooses host VBUS or
   `TI_SWITCHED_TARGET_5V` for the target; and
2. a harness-board 2x3 two-shunt selector chooses the Routing Logic Supply
   Rail source and the harness-local regulator-enable state.

| Mode | Daughter-board VBUS selector | Routing Logic Supply Rail | Local regulator | Test Block Supply Rail |
|---|---|---|---|---|
| `STANDALONE` | Host VBUS | Harness-local regulated 3.3 V | Enabled from `TI_TARGET_VBUS` | On automatically |
| `SUPERVISOR` | `TI_SWITCHED_TARGET_5V` | External regulated 3.3 V | Disabled | Supervisor-controlled, default off |

These Operating Mode selector positions are physical power-configuration
preconditions, not test-facing capability modes. Tests still request
capabilities through the Target Support Module and record the resulting
Resolved Test Configuration.

`OFF` is not a selector position. It is the de-energized system condition in
which host USB VBUS and the external/rack supplies are disconnected. Any
additional target-local source, including a second USB connection or battery,
shall also be disconnected. This avoids implying that a selector can remove a
source still connected directly to the target.

This removes the invalid assumption that an accepted target can supply the
complete 300 mA harness allowance from its onboard 3.3 V regulator. The
two-selector implementation shall be revised and confirmed during schematic
design. Both selectors shall be changed only while all associated sources are
off. Their states shall agree and shall be recorded in the Resolved Test
Configuration.

The target owns the direct routing-control I2C in both Standalone and
Supervisor operation. Operating Mode selection does not switch I2C ownership.

The earlier architecture overview is withdrawn because it depicts the
superseded target-powered Standalone and USB No-VBUS arrangement. Its draw.io
source shall be redrawn only after the corrected schematic topology is
accepted; the normative flows in this section are the present authority.

Every daughter board shall provide the common USB data path and manual VBUS
selector and shall return the selected target VBUS through `TI_TARGET_VBUS`.
No raw host VBUS or VBUS-select control crosses the Target Interface.
Target-specific
Adapter Services may additionally use target-local rails where required, but
shall identify every source and load and shall not bypass the common source
isolation.

### 3.2 Routing-Control 3.3 V

The Routing Logic Supply Rail shall accept either harness-local regulated
3.3 V or an external regulated 3.3 V harness-system supply. A manual 2x3,
2.54 mm through-hole header with two removable shunts shall select one source
without allowing the two supplies to be connected together in either valid
configuration. The odd-numbered column selects `LOCAL_3V3` or `EXT_3V3` to
`ROUTING_LOGIC_3V3`. The even-numbered column enables the local regulator
input-isolation stage in `STANDALONE` and holds it disabled in `SUPERVISOR`.

The selector pin and shunt contract shall be:

| Pins | Connection |
|---|---|
| 1 | `LOCAL_3V3` |
| 3 | `ROUTING_LOGIC_3V3` common |
| 5 | `EXT_3V3` |
| 2 | Standalone enable source: `TI_TARGET_VBUS` through 10 kOhm |
| 4 | `LOCAL_REG_ENABLE` common: TPS22917 input-isolator `ON`, mode-stage input and 22 kOhm pull-down to `TI_GND` |
| 6 | Supervisor disable bias: `TI_GND` through 10 kOhm |

Both shunts shall always occupy the same end of the header: pins 1-3 and 2-4
for `STANDALONE`, or pins 3-5 and 4-6 for `SUPERVISOR`. A missing shunt, a
mismatched pair or a shunt fitted across the two columns is an invalid
configuration and shall be caught by visual preflight. The PCB silkscreen
shall show the two valid paired patterns and identify `STANDALONE` and
`SUPERVISOR` without relying on pin numbers alone.

The reusable harness shall use a `TPSM828438VCFR` synchronous buck module to
regulate selected `TI_TARGET_VBUS` to `LOCAL_3V3`. The selected device
integrates its inductor, is rated for 600 mA from 1.8 V to 5.5 V and therefore
supports the specified 300 mA steady harness load and the required 500 mA
continuous design capability. A `TPS22917DBVR` active-high load switch shall
isolate the module input from `TI_TARGET_VBUS`; the selector's even-numbered
shunt column controls its `ON`
input. The switch output supplies the module `VIN`, and the module `EN` shall
be driven only from that isolated input domain. In `SUPERVISOR`, only the
disabled TPS22917 input remains connected to the monitored rail.

The TPS22917 data sheet guarantees at most 100 nA disabled input current over
1 V to 5.5 V and -40 °C to 85 °C. This consumes at most 0.10 percentage
point of a 100 µA PC02 reading and leaves approximately 2.19% of the present
uncalibrated error allowance. Its always-active reverse-current blocking is a
secondary protection; permitted mode states shall also keep the regulator
output isolated from `EXT_3V3`, so no source is allowed to drive the isolated
regulator domain backwards. The TPSM828438's own 850 nA maximum shutdown
current is downstream of the disabled isolation switch and is therefore not a PC02
measurement load. Complete-board leakage shall nevertheless be measured
through 55 °C before the 100 µA claim is accepted.

Set the TPSM828438 output to 3.3 V with a 249 kΩ, 1% `VSET` resistor. Fit at
least 4.7 µF effective low-ESR ceramic capacitance at its input and 10 µF
nominal at its output, using X5R or X7R dielectric and preserving the data-sheet
effective-capacitance limits after tolerance and DC-bias derating. The
TPS22917 `QOD` pin shall be tied to its output to discharge the isolated input
domain; its `CT` value shall be selected during schematic implementation to
limit charging current into the regulator input capacitor without violating
the required startup envelope.

The TPSM828438 data sheet gives `RθJA = 72.4 °C/W`. At 5 V, 3.3 V and
300 mA, even an intentionally conservative 80% efficiency assumption gives
0.248 W loss, an 18 °C junction rise and approximately 73 °C junction at
the 55 °C design ambient. At the 500 mA design capability the same
conservative assumption gives 0.413 W, a 30 °C rise and approximately 85 °C
junction, below the 125 °C operating limit. Final PCB review shall still
follow the manufacturer's capacitor placement, short current-loop and ground
guidance and shall verify output ripple and transient response on assembled
hardware.

`TI_TARGET_3V3` shall remain available only as a bounded, low-current target
I/O-domain reference whenever the target is powered. When the Operating Mode
selection disconnects it from the Routing Logic Supply Rail, the reference may
serve only approved loads such as target-side I2C pull-ups and target-domain
power-valid qualification. It shall not be connected to the external 3.3 V
source.

`TI_TARGET_3V3` shall remain between 3.00 V and 3.60 V whenever the target is
powered. Its complete accepted load shall be specified as a low-current
reference budget during the corrected schematic review; it shall never supply
the Routing Logic or Test Block rails.

The selected source powers the Routing Logic Supply Rail directly. The Test
Block Supply Rail is derived from it through a controlled power switch. It is
on in Standalone so active Test Blocks remain available without a
software power-enable step. In `SUPERVISOR` it defaults off and is enabled only
when required. Passive Test Block connections do not require this rail.

The complete switched load on `TEST_BLOCK_3V3`, including fixed harness
capacitance and every fitted removable Test Block module, shall not exceed
50 µF. Rev A shall fit 2.2 nF from the TPS22917 `CT` pin to its
`ROUTING_LOGIC_3V3` input. Using TI's typical 3.6 V slew-rate constant, this
gives approximately 3.5 ms 10%–90% output rise time and 43 mA charging current
at the 50 µF limit; the present 23.3 µF fixed load gives approximately 20 mA.
The calculated values select the component but are not guaranteed limits,
because the data sheet specifies the relevant timing constants as typical.
Rev-A testing shall therefore confirm no more than 100 mA peak charging
current, acceptable source-rail disturbance and valid Test Block startup from
both the harness-local regulated source and `EXT_3V3`. Any later increase beyond 50 µF requires a
new inrush calculation and validation before it is accepted.

The Operating Mode is a test precondition and neither selector shall be
changed while an associated source is powered. The two header shunts shall be
removed and refitted only after host USB, external supplies and competing
target sources are disconnected. Their separated manual movement is not a
live-transfer mechanism. Rev A shall use Würth Elektronik `61300621121`, a
3 A straight 2x3 2.54 mm through-hole WR-PHD header, with two
`60900213421` 3 A open-top shunts already used elsewhere in Rev A. The header
and shunts shall be hand-fitted after AISLER manufacture and retained in the
design BOM as the completed-board configuration. Automatic priority
switchover, live transfer and a selector `OFF` position are not required.

The even-numbered shunt column shall drive the TPS22917 input-isolation switch
control so that those contacts carry only switch-control bias rather than
regulator load current. A 10 kOhm resistor shall connect `TI_TARGET_VBUS` to
selector pin 2, a second 10 kOhm resistor shall connect pin 6 to `TI_GND`, and
a 22 kOhm resistor shall hold pin 4 `LOCAL_REG_ENABLE` low. The two endpoint
resistors limit current if a shunt is accidentally fitted across columns;
such placement remains invalid and shall not be used as an operating state.

`LOCAL_REG_ENABLE` shall drive the TPS22917 `ON` input directly and one input
of a `SN74LVC2G14DBVR` dual Schmitt-trigger inverter powered from
`ROUTING_LOGIC_3V3`. The first inverter output shall be `MODE_SUPERVISOR`; the
second shall invert `MODE_SUPERVISOR` to produce `TEST_BLOCK_AUTO_EN`.
`R1009` shall change from 100 kOhm to 22 kOhm from `MODE_SUPERVISOR` to
`TI_GND`, holding Supervisor qualification absent while the inverter is
unpowered. `R1004` shall likewise change from 100 kOhm to 22 kOhm on
`TEST_BLOCK_SWITCH_EN`, ensuring powered-off leakage through the second
inverter output and `D1005` cannot enable U1002. The Schmitt-input device is
required because the source and power-startup edges may be slow. Its 5.5 V-
tolerant input and `Ioff` partial-power-down behaviour permit the Standalone
enable input to precede `ROUTING_LOGIC_3V3` without back-powering that rail.

At the specified 4.75 V minimum switched-target supply, the 10 kOhm feed,
22 kOhm pull-down, 5 uA worst-case powered inverter input leakage and 10 nA
TPS22917 `ON` leakage leave at least approximately 3.23 V at
`LOCAL_REG_ENABLE`. This exceeds the inverter's 2.2 V maximum positive-going
threshold at a 3.0 V supply and the TPS22917 1.0 V input-high requirement.
With the common shunt absent and the inverter unpowered, its 10 uA maximum
`Ioff` contribution develops no more than 0.22 V across the 22 kOhm
pull-down, below the TPS22917 0.35 V input-low limit. In Supervisor, the
10 kOhm disable resistor in parallel with the pull-down holds the common near
ground. At either inverter output, 10 uA maximum powered-off output leakage
plus 5 uA maximum receiving-input leakage develops no more than 0.33 V across
22 kOhm. This remains below the 0.8 V input-low limit of the powered PC02 LVC
logic. The second output alone can develop no more than 0.22 V at
`TEST_BLOCK_SWITCH_EN` through `D1005` and `R1004`, below U1002's 0.35 V
input-low limit. The detailed circuit shall not depend on target firmware or
`TI_TARGET_3V3`.

Appendix C records the Rev-A circuit that implements this mode selection and
the derived Test Block Supply Rail control.

#### 3.2.1 Rev-A External Rack Supplies

The Rev-A rack shall use separate externally regulated 3.3 V and 5 V
supplies with a common `TI_GND` reference. Their minimum requirements are:

| Supply | Required output | Loads supplied |
|---|---:|---|
| External 3.3 V | 3.30 V nominal, ±2%, 1 A continuous | The Routing Logic Supply Rail for every installed harness position and the Test Block Supply Rail for the one active position |
| External 5 V | 5.10 V nominal, 3 A continuous | The switched target-power path for the one active target position, including any Target-specific Adapter Service powered from that path |

The external 5 V supply shall remain between 5.00 V and 5.20 V at the rack
backplane input over the accepted load range; 5.10 V is the preferred nominal
setting. Ripple and ordinary load transients shall remain inside that range,
and no transient shall exceed 5.25 V. This input range, together with the
250 mV complete-path limit in Section 3.5.1, preserves at least 4.75 V at
`TI_SWITCHED_TARGET_5V` under the maximum accepted target load. The 3 A supply
rating provides practical boot and load-transient margin above the 1.5 A
per-position limit; it does not permit more than one target position to be
active or raise the permitted current of an individual position. An
unspecified 3 A source-protection threshold cannot enforce the 1.5 A
per-position limit, so the complete target-power system shall also provide
hardware overload and short-circuit containment sized for its switch,
measurement shunts, connectors and PCB copper. Target Power Monitor
observation and firmware response are not substitutes for that protection.

The external 3.3 V supply shall remain between 3.23 V and 3.37 V at the rack
backplane input over its accepted load range. Its 1 A rating is based on a
maximum design allowance of 50 mA for each of eight continuously powered
Routing Logic domains, up to 250 mA for the selected position's enabled Test
Blocks and 350 mA of supply and transient margin. Schematic and prototype
measurements shall confirm the actual safe-state, active and peak loads
against those allocations.

Both supplies shall be mains-isolated SELV regulated sources with
short-circuit, over-current, over-voltage and thermal protection. Their
negative outputs shall either already share a common reference or be suitable
for connection together at the rack distribution point. The backplane shall
provide the functional `TI_GND` power return; USB cable ground shall not be
used as a substitute supply return. Supply wiring, connectors, protection and
PCB copper shall be rated and derated for the defined output current.

The external supplies may remain on while the Supervisor selects and
deactivates rack positions. Hardware defaults on each harness board shall
keep target and Test Block power off until deliberately enabled. No
test-critical sequencing between external 3.3 V, external 5 V and Supervisor
USB power is required, but every order of application and removal shall leave
the harness in a safe state.

The Supervisor MCU remains powered through its own host USB connection.
`RACK_CONTROL_3V3`, distributed by the Grove rack-control connection, is a
separate Supervisor-derived always-on rail for the Rack Control Endpoints and
Target Power Monitors. Its load is therefore not included in the external
3.3 V rating above and shall be budgeted when the Supervisor schematic and
its 3.3 V regulator are designed.

### 3.3 Standalone Operation

Standalone operation uses the target's normal USB data connection. Host VBUS
passes through the daughter-board VBUS selector, supplies the target USB VBUS
input and returns through `TI_TARGET_VBUS` to the reusable-harness regulator. The target
establishes and verifies the required routes through the direct
routing-control I2C.

```text
Host USB D+/D- ----------------------------------> target USB D+/D-
Host USB VBUS --> daughter selector --> target USB VBUS
                                      `--> TI_TARGET_VBUS
                                             `--> harness 5 V-to-3.3 V
                                                  `--> routing and Test Blocks
```

The host port, hub, cable, daughter-board selector and target connector shall
support the simultaneous Standalone load of the target plus the local
regulator input current required to supply up to 300 mA at 3.3 V, including
startup and inrush margin. This is a separate Standalone source envelope; the
1.5 A Supervisor target-position allowance shall not be assumed available from
an arbitrary USB host port. Each Target Profile or Resolved Test Configuration
shall state the accepted Standalone source and any excluded high-load tests.

Automated power cycling is unavailable in this arrangement. Tests that require
it shall be excluded, adapted to a manual step or run later with a Supervisor.
Recovery uses the target's normal reset, boot and USB power controls.

The routing fabric shall not be needed to establish the control bus or the
normal recovery connection. This prevents an incorrect route from blocking
the means required to correct it.

### 3.4 USB Data And Manual VBUS Selection

Every daughter board shall use a manual two-position selector to choose one of
two mutually exclusive 5 V sources for the VBUS presented at the target's
normal USB connector:

* host USB VBUS in `STANDALONE`
* `TI_SWITCHED_TARGET_5V` in `SUPERVISOR`

USB D+ and D- and ground remain direct host-to-target paths in both modes. The
selector shall not connect the two 5 V sources together, shall support the
accepted target current and inrush, and shall expose its common output both to
the target and as the `TI_TARGET_VBUS` return. A target without native USB
shall retain the same common power contract while its Target Profile declares
the applicable data/control endpoint and accepted target-power input.

The selector is local to the daughter board; no source-select signal crosses
the Target Interface. It shall be changed only with both sources off and shall
be clearly labelled `HOST / STANDALONE` and `HARNESS / SUPERVISOR`. The exact
selector or header-and-shunt MPN shall be reviewed for current rating, contact
resistance, inrush, physical keying and manual-assembly requirements.

The two manual selectors can be set inconsistently. `SUPERVISOR` on the
harness with `HOST` on the daughter board can leave the target host-powered
and defeat controlled power cycling. Supervisor preflight shall therefore
command target power off and confirm that the target is de-energized through a
declared independent observation, normally disappearance of its USB endpoint.
A target without an observable USB endpoint shall declare an alternative
target-rail, debug or handshake observation in its Target Profile; unattended
Supervisor power-cycle tests are unavailable if the off state cannot be
observed. The runner shall refuse the test if the target remains powered.
`STANDALONE` on the
harness with `HARNESS` on the daughter board is a safe but non-functional
configuration. Clear labelling and recorded selector states remain mandatory.

### 3.5 Supervisor-Controlled Target Power

Supervisor operation shall provide a switched 5 V target supply while keeping
the Supervisor and routing-control domain powered. The Supervisor shall be
able to remove target power, confirm the target supply state and restore power
without assistance from target firmware. The routing-control circuitry shall
be arranged so the same reset or recovery operation also returns controlled
routes to their hardware safe state; Supervisor access to the routing-control
I2C is not required.

In rack operation, the common external 5 V supply is distributed to an
independent target-power switch on each harness board. The Supervisor selects
the rack position through the TCA9548A and writes that harness's Rack Control
MCP23017. One MCP23017 output controls the local switch enable; target current
does not pass through the expander. External biasing holds the switch off
before the endpoint is configured or whenever its control is unavailable.

Each harness board shall also provide a Supervisor-owned **Target Power
Monitor** on its existing rack-control I2C branch. The monitor shall be powered
from `RACK_CONTROL_3V3` so it remains available while target power is off. It
shall observe the switched target-power path downstream of the power switch
and before that path divides between the Target Board and Target-specific
Adapter Services. Its bus-voltage measurement shall provide the observed
target-power state, and it shall also report target-position current and
power.

The Target Power Monitor shall support useful measurements of both normal
operating consumption and low-power or sleep consumption. Rev A shall use two
measurement ranges so that it can measure settled sleep current without
sacrificing the target's required boot, radio and peripheral current
capacity. The monitor shares the existing TCA9548A-selected SDA and SCL
connection with the MCP23017; it does not add another I2C backplane or
additional backplane conductors.

#### 3.5.1 Rev-A Target-Power Measurement Contract

The accepted Rev-A design basis is one active target position, a maximum
target current of 1.5 A and a minimum calibrated sleep-current measurement of
100 µA at the switched 5 V input to the complete target position. Each of the
up to eight rack positions repeats the same independently switched and
monitored circuit, but the one-active-position rule in Section 8.4 means that
the 1.5 A allowance is per active position rather than eight simultaneous
1.5 A loads. The limit provides margin for complete development boards,
radio-current peaks and attached target-side services; it is a permitted
position maximum rather than an expected continuous load. Power-path
components shall be rated with suitable margin above it.

The 1.5 A limit shall be enforced locally at each position by the
TPS2559-Q1 target-power switch, independently of Supervisor firmware. Its
programmed current-limit tolerance shall admit the 1.5 A permitted target load
while limiting a sustained overload or target short before the measurement
shunts, connectors or PCB copper exceed their accepted electrical or thermal
ratings. Current-limit tolerance, trip response, transient-load behaviour and
switch voltage drop shall be included in the complete-path budget below.

The two required measurement ranges are:

| Range | Intended use | Required useful range |
|---|---|---:|
| Low-current | Settled sleep, dormant and other low-power states | 100 µA to 20 mA |
| Normal-current | Boot, active operation, radio activity and attached peripherals | 10 mA to 1.5 A |

Together these limits span 15,000:1. A nominal 50 mΩ high-current shunt
produces only 5 µV at 100 µA, which is too small for the required low-current
accuracy. A nominal 1 Ω low-current shunt instead produces 100 µV at 100 µA,
but would drop 1.5 V and dissipate 2.25 W at the maximum target current.
Neither value can therefore cover the complete requirement safely and
accurately by itself; the design needs two effective measurement ranges.

The 10 mA to 20 mA overlap shall allow the two ranges to be compared during
prototype validation and shall allow software to change range without an
unmeasured gap. The high-current range shall be the hardware-safe default.
The low-current range shall be selected only after the measured current has
fallen below a safe threshold, and the circuit shall return to the
high-current range before reset, wake-up or any operation that can restore a
normal target load. Loss of range control shall select the high-current
range. Range selection shall not interrupt target power or disturb the sleep
state being measured.

Rev A shall use the INA228 low-range monitor as a hardware qualification and
observation path, not merely as a measurement device. Its active-low
open-drain `ALERT` output is `LOW_RANGE_OK_N`: an asserted low state shall
override `TARGET_LOW_RANGE_EN` and restore the high-current bypass without
waiting for firmware. The INA228 shall use the ±40.96 mV shunt range and a
shunt-overvoltage threshold no higher than the accepted low-range current
ceiling after component tolerances are included. Conversion-ready signalling
shall not share this `ALERT` function.

The INA228 alert shall be configured active low and latched (`APOL = 0`,
`ALATCH = 1`). Latching is mandatory because restoring the bypass removes the
1 Ω shunt voltage that caused the alert; a transparent alert could otherwise
clear while `TARGET_LOW_RANGE_EN` remained asserted and repeatedly reinsert
the shunt. `LOW_RANGE_OK_N` shall therefore feed both the local range
interlock and `GPB3` of the Rack Control MCP23017. Its asserted state shall
contribute to `RACK_INT_N` like the other Supervisor-owned endpoint events.
This behaviour follows the
[INA228 data sheet](https://www.ti.com/lit/ds/symlink/ina228.pdf), which
defines `ALATCH = 1` as holding `ALERT` and its flag active until
`DIAG_ALRT` is read.

The Supervisor low-range sequence shall be:

1. Configure the INA228 range, calibration, conversion timing,
   shunt-overvoltage threshold and latched alert before low range is enabled.
2. Confirm from the normal-range monitor that current is below the permitted
   transition threshold, then assert `TARGET_LOW_RANGE_EN`.
3. Wait for the defined INA228 conversion interval and accept low range only
   if no latched alert is present and the INA228 reading is within the
   accepted low-current range.
4. On a captured `LOW_RANGE_OK_N` event, first clear
   `TARGET_LOW_RANGE_EN`, then read `DIAG_ALRT` to identify and clear the
   latched INA228 alert. A retry shall be a deliberate new request after the
   normal-range current has again been verified.
5. Clear `TARGET_LOW_RANGE_EN` and confirm the high-current range before any
   reset, wake-up or other operation that can increase target current.

The measurement and complete-path voltage-drop limits are:

| Condition | Maximum drop |
|---|---:|
| High-current measurement shunt at 1.5 A | 75 mV |
| Complete switched path at 1.5 A, including switch, shunt, connectors, PCB tracks and backplane connection | 250 mV |
| Low-current measurement element at 20 mA | 20 mV |

With a regulated 5.0 V rack supply, the complete-path limit preserves at
least 4.75 V at `TI_SWITCHED_TARGET_5V`. Nominal 50 mΩ and 1 Ω shunts
respectively satisfy the high- and low-range shunt-drop limits and are the
Rev-A calculation basis. The detailed circuit may use equivalent values or
another topology only if its calculated and measured range, accuracy, fault
behaviour and voltage drop meet the same contract. In particular, the
low-current measurement element shall be bypassed or otherwise protected from
boot and active current.

The required calibrated accuracy is:

| Measured current | Required absolute accuracy |
|---:|---:|
| 100 µA to below 1 mA | ±10% |
| 1 mA to 20 mA | ±5% |
| Above 20 mA to 1.5 A | ±5% |

The low-current accuracy requirement applies with the local power-monitor
circuit, including the bypass MOSFET, at no more than 55°C. If necessary,
the rack shall use cooling to remain within that limit. Measurements made
above it are outside the accepted Rev-A accuracy range.

Settled sleep-current measurements shall additionally have repeatability
better than ±2% under the same recorded test conditions. Before a low-current
measurement, the Supervisor shall obtain a target-power-off zero reading and
apply the defined offset compensation. A settled sleep result shall use a
defined observation interval and report its averaging configuration. Short
wake, radio or other load pulses shall be preserved as separate observations
rather than hidden in the settled sleep average.

The shunts shall use Kelvin sensing, nominal 1% tolerance and no more than
100 ppm/°C temperature coefficient. Rev A shall use the accepted 50 mΩ,
2 W Yageo `PE2512FKF7W0R05L` for the normal range and the 1 Ω, 3 W Bourns
`CHP2512-FX-1R00ELF` for the low range, subject to final AISLER assignment.
The selected monitor, switching method, PCB layout, zero measurement,
averaging and calibration together shall meet the complete error budget;
converter resolution alone is not evidence of measurement accuracy. At
100 µA, a nominal 1 Ω low-range shunt produces only 100 µV, so the ±10%
requirement permits approximately 10 µV of total error. An INA226-class
device remains useful background for the architecture, but its maximum input
offset can consume that allowance before shunt, layout and temperature errors
are included. Rev A shall therefore use a demonstrably lower-offset monitor
or another verified method for the low range.

The 100 µA lower limit is a practical complete-board requirement rather than
a bare-MCU current claim. Raspberry Pi documents approximately 0.95 mA for a
Pico in dormant mode and approximately 0.18 mA for a Pico 2 in its lowest
measured Pstate when powered through `VSYS`. The ESP32-C3 silicon can consume
far less in deep sleep, but the accepted ESP32-C3-DevKitC-02 also powers an
LDO, power LED and USB-to-UART bridge. Rev-A validation shall measure the
actual accepted target boards and confirm that every declared C3 and Pico
sleep scenario remains within the calibrated range. A target position below
100 µA is outside the initial guaranteed range and requires external
instrumentation or a later lower-current extension.

The supporting supplier references are the
[Raspberry Pi low-power measurements](https://www.raspberrypi.com/documentation/pico-sdk/high_level.html),
[ESP32-C3 data sheet](https://documentation.espressif.com/esp32-c3_datasheet_en.html)
and
[ESP32-C3-DevKitC-02 hardware description](https://docs.espressif.com/projects/esp-dev-kits/en/latest/esp32c3/esp32-c3-devkitc-02/user_guide.html).

The Hackaday.io article
[Mastering the INA219 & INA226](https://hackaday.io/project/204686-mastering-the-ina219-ina226/details)
provides non-normative background on shunt selection, high-side sensing,
Kelvin connections, filtering and averaging. Component limits and final
design requirements shall be taken from the manufacturer's data sheet and
verified by prototype measurement.

The Power Control Service provides `TI_SWITCHED_TARGET_5V` as the Supervisor
input to the daughter-board VBUS selector. This connection is an output from
the harness, not a general bidirectional 5 V rail. The selector applies it
instead of host VBUS to the target's normal USB VBUS input and returns the
result as `TI_TARGET_VBUS`. It shall not energise a target header power input
in parallel with the target USB input. Appendix A records the assessed-target
consequences and the limited exception for a target without native USB.

```text
Host USB D+/D- ----------------------------------> target USB D+/D-
Host USB VBUS -- isolated by daughter selector in Supervisor mode
EXT_5V --> harness switch and monitor --> TI_SWITCHED_TARGET_5V
         --> daughter selector --> target USB VBUS --> TI_TARGET_VBUS return
EXT_3V3 ------------------------------------------------> harness logic
```

The switching and monitoring implementation shall provide the current,
measurement-range, accuracy and voltage-drop performance in Section 3.5.1,
with suitable component margin, reverse-current protection and predictable
removal of residual target-rail charge. Exact device selection, range-control
topology, sensing thresholds and discharge circuit remain detailed design
decisions.

### 3.6 Host USB During Controlled Power Cycling

The harness system normally uses a powered local USB hub. Ordinary complete
USB cables connect stable hub ports to the daughter-board host connectors.
The daughter-board selector, rather than a modified cable, controls VBUS
ownership while leaving D+, D- and ground continuous. This is required for
targets whose onboard USB bridge or MCU needs VBUS present to establish or
maintain the host connection.

In `STANDALONE`, host VBUS supplies the target and the harness-local regulator.
In `SUPERVISOR`, the selector isolates host VBUS and selects
`TI_SWITCHED_TARGET_5V`; removal of that source removes target VBUS without
disconnecting the USB data pair. Selection is a manual, unpowered
configuration step; live source transfer is prohibited.

ESP32-S3 USB OTG host operation additionally requires the target to supply
VBUS to the attached USB device. Its daughter board shall therefore provide an
optional, controllable VBUS Adapter Service supplied from the harness switched
5 V service. The VBUS output shall default off and prevent reverse current; it
is enabled only when the target is deliberately operating as the USB host.
The switch, current protection, control path and connector arrangement remain
daughter-board design decisions. The common device-mode selector does not by
itself provide the separately controlled downstream VBUS required in OTG-host
operation.

USB VBUS isolation alone does not prove that a target is unpowered. Prototype
verification shall also check USB data, control I2C, routing, reset, debug,
wake and handshake connections for back-power paths.

### 3.7 Evidence And Verification

Power-related test evidence shall record both manual selector states, the
target power source and the Test Block Supply Rail state.
Supervisor-controlled tests shall record both the commanded and
observed target-power state. They shall also record target-position voltage,
current and power measurements where required by the test, including the
settled sleep-current measurement for a low-power test.

The prototype shall demonstrate:

1. safe Standalone startup with routing powered by the harness-local regulator
2. correct host-VBUS and switched-5-V selection without source backfeed
3. controlled enable and removal of the Test Block Supply Rail
4. safe routing and peripheral states during target power removal
5. supervised removal and restoration of target VBUS
6. absence of material back-power through every attached path
7. restoration of the selected console or USB connection after power cycling
8. target-position current measurement across the accepted operating and
   sleep-current ranges
9. external 3.3 V and 5 V regulation, ripple, load-transient behaviour and
   safe-state operation at the maximum accepted rack loads
10. Supervisor preflight detection of a target that remains host-powered
11. Standalone operation at the accepted target-plus-harness USB load envelope

### 3.8 Downstream Decisions

Appendix C records the required Rev-A two-selector correction. Detailed design shall complete the
harness-local regulator,
target-power switch, Target Power Monitor, two-range measurement arrangement,
discharge behaviour and protection components against the Section 3.5.1
contract. Prototype measurements shall demonstrate the required peak-current,
sleep-current, accuracy and voltage-drop performance and determine whether
any target requires USB data isolation in addition to the common VBUS
selector.

Physical Target Interface contacts are not assigned by this specification.

## 4. Target Control, Console And Firmware Flashing

This service provides the host-facing **endpoints** used to prepare, run,
observe and recover target tests. An endpoint is a distinct communication
connection between the host and target, such as USB, UART or a wireless
console, that can provide one or more service roles. Through these endpoints,
**Test Control** sends JavaScript tests through the REPL and collects their
results, while **Console** provides interactive REPL and diagnostic access.
**Firmware Flashing** installs the selected firmware build, and **Recovery**
restores flashing or console access when the runtime is unavailable. These
services remain independent of the Test Block routing fabric and the
capability under test.

Every selected test configuration shall identify one direct host-facing
test-control endpoint. The Target Profile declares the legal endpoints; the
Resolved Test Configuration selects the endpoint used for that run.

### 4.1 Roles And Ownership

One physical endpoint may provide several logical roles:

| Role | Purpose |
|---|---|
| Test Control | Sends JavaScript tests through the REPL and collects their results |
| Console | Provides interactive REPL and diagnostic access |
| Firmware Flashing | Installs the selected firmware build on the target |
| Recovery | Restores firmware-flashing or console access when the runtime is unavailable |

The host runner owns the selected target endpoint. The Harness Supervisor uses
its own USB connection. The host connects directly to the target for console
access and firmware flashing without involving the Supervisor. Only one host
process or tool shall own a physical endpoint at a time.

The selected path shall be direct or target-specific. It shall not depend on a
Test Block route that target firmware must first establish, because the host
may need the path before routing is configured or to recover from firmware or
routing failure. Hardware-debug probes remain host-coordinated Adapter
Services rather than reusable harness hardware.

Where an endpoint and a Test Block share target pins, the connection matrix
shall define mutually exclusive paths with a safe disconnected default. The
selected test-control endpoint shall remain independent of the route under
test.

### 4.2 Path Selection

In `STANDALONE`, the normal target USB or documented alternative provides the
host-facing path. In `SUPERVISOR`, the host still connects directly to the
target through the daughter-board USB data path while the daughter-board
selector applies harness-switched 5 V to target VBUS. The de-energized `OFF`
condition requires all independent target sources to be disconnected.

The Target Profile shall identify each available endpoint, its supported
roles, power behaviour, firmware dependencies, conflicts and required
preconditions. When the normal endpoint is itself under test, an independent
alternative shall be selected. If none is available, that capability is
unavailable rather than failed.

A target with multiple USB, UART, debug or wireless paths shall give each a
stable logical role. Rack configuration additionally maps each selected USB
role to the stable Linux path defined in Section 8.5.

### 4.3 Safety, Recovery And Evidence

No connection used for test control, console, firmware flashing or debug may
back-power an unpowered target or compete with another driver. The USB/VBUS
selector isolates the two declared VBUS sources but does not replace powered-off
validation of USB data, UART, I2C, debug and other attached signals.

Firmware flashing shall have exclusive use of its endpoint. If the runtime path
fails, recovery shall use the declared direct reset, boot, power-cycle,
ROM-loader or debug path rather than an unverified Test Block route. After
flashing or recovery, the host shall verify the expected target and firmware
identity where the runtime permits.

Evidence shall record the selected logical role and endpoint, Operating Mode,
target power source, stable host identifier, connection power state,
preconditions, ownership changes and observed target and firmware identity.
Exact connectors, target-specific adapters, host software and Target Profile
storage format remain downstream decisions.

## 5. Direct Reset And Boot Control

This service provides the direct target controls used to restore a known
execution state and, where supported, select a firmware-flashing mode. It
enables the test system to restart an unresponsive target, enter its ROM or
board bootloader and perform repeatable reset and boot tests without depending
on responsive target firmware or the Test Block routing fabric.

**Reset Request** asserts the target's reset or enable input. **Boot Request**
is an optional condition applied with reset or power-up to select a target
bootloader or other recovery mode. Target power cycling remains the separate
Power Control Service defined in Section 3.

### 5.1 Controls And Ownership

| Control | Purpose |
|---|---|
| Reset Request | Forces a direct hardware reset and returns the target to its normal boot path |
| Boot Request | Selects a target-specific bootloader or recovery path during reset or power-up |

The host runner owns the reset or boot operation. In `SUPERVISOR`, the Harness
Supervisor performs the requested action through the Supervisor Interface and,
in rack operation, the selected Rack Control Endpoint. In Standalone
mode, the host uses the target's supported automatic sequence or the operator
uses the declared manual controls.

A host endpoint may provide the same logical controls through a target-provided
automatic sequence, such as USB-UART DTR/RTS driving onboard reset and boot
circuitry. The Target Profile shall describe this as an endpoint capability
rather than a separate Control Service.

The provisional `TI_TARGET_RESET_N` service is an active-low open-drain
control that defaults released. The optional provisional `TI_BOOT_REQUEST`
service is asserted by pulling its open-drain Interface control low and is
otherwise released. The target daughter board provides any inversion, level
adaptation, protection or isolation needed by the target.

Onboard automatic-download circuits, debug probes, manual controls and harness
controls may share a target reset or boot node only when their inactive states
are compatible and no source can oppose another. Neither control shall depend
on target-controlled I2C or a Test Block route.

### 5.2 Modes And Target Options

In the de-energized `OFF` condition, harness-driven reset and boot controls
remain inactive.
Standalone retains the target's documented manual or host-endpoint
sequence. `SUPERVISOR` adds automated reset and optional boot sequencing
without changing their target-side meaning.

Direct reset is available when the target exposes a safe reset or enable
input. Boot Request is optional because boot polarity, sampling and onboard
download arrangements differ between targets. A target without a safe direct
reset mapping shall declare another recovery action, such as controlled power
cycling, ROM USB or a debug adapter.

The Target Profile shall state the available controls, their daughter-board
mappings, active polarity, timing, power dependencies, onboard circuit
interactions and supported Operating Modes. It shall also identify any manual
action or connection precondition.

### 5.3 Sequencing, Safety And Evidence

A normal reset shall leave Boot Request inactive, assert Reset Request for the
target's required minimum interval, release it and wait for the selected
control endpoint to return. The host shall then verify the expected target and
runtime identity.

A firmware-flashing boot sequence shall assert Boot Request, perform the
target-defined reset or power-up sequence, then release Boot Request at the
time declared by the Target Profile. After flashing, the service shall restore
the normal boot state, restart the target and verify the expected runtime where
the endpoint permits.

Reset and Boot Request shall default inactive before software configuration,
during Supervisor loss and while the relevant control circuitry is unpowered.
They shall not back-power the target, disturb unsafe strapping states or leave
the target held in reset or bootloader mode after a failed operation.

Evidence shall record the requested action, owner, Operating Mode, target
power state, asserted controls, configured timing, observed endpoint
disconnection or return, resulting boot mode and final target and firmware
identity. Exact circuits, physical Target Interface contacts and target-specific
adaptation remain downstream decisions.

## 6. Routing Control Service

This service controls the electronic switches on the reusable harness board
that connect target GPIO signals to Standard Test Blocks. This capability
allows a target GPIO to be reused for different Test Blocks from one test
configuration to another. It also allows the same fixed Test Blocks to support
targets with different GPIO and hardware-peripheral assignments, without
manually rewiring the harness.

A **target routing connection**, called a **route entry** in the Target Routing
Envelope, carries one target GPIO signal through the Target Interface into the
Routing Fabric. **Route Selection** uses route-selection switches to connect
those entries to predefined Test Block signals.

**Block-local connection switching** controls switches inside a Test Block
after the target signals have reached it. For example, Block 7 selects whether
its protected UART endpoints are cross-connected for a two-UART test,
connected to an external peer, or isolated.

Before a test, the service automatically applies and verifies the complete
switch configuration that connects the selected target pins to the required
Test Block. After the test, it clears those connections.

**Routing-control devices** are the I2C-controlled expanders and switches that
implement these paths. Route Selection and Block-Local Connection Switching
remain distinct logical functions even where they share an I2C controller.
The Target Profile declares the legal configurations; the Resolved Test
Configuration records the complete configuration selected for a test.

### 6.1 Functions And Ownership

| Function | Purpose |
|---|---|
| Route Selection | Connects target route entries to their legal Test Block destinations using route-selection switches |
| Block-Local Connection Switching | Selects a Test Block's predefined internal connection arrangement |
| State Verification | Reads back the commanded routing-control state |
| Hardware Clear | Returns every controlled path to its safe inactive state without target firmware |

The target is the software owner of the Routing Control Service in every
powered Operating Mode. The host requests a logical capability through the
target's Test Control endpoint, and the Target Support Module applies and
verifies the resolved configuration. The Harness Supervisor does not own the
target routing-control I2C or select arbitrary routes.

Routing control uses the mandatory direct `TI_I2C_SDA` and `TI_I2C_SCL`
connections. The bus shall be usable before any Test Block route is configured
and shall remain independent of the path it controls. The Supervisor may
invoke Hardware Clear through a direct control, but it does not require access
to the routing-control I2C.

The direct bus crosses independently powered target, Routing Control Service
and Standard Test Block domains. The reusable harness shall therefore provide
the two fixed, power-qualified SDA/SCL isolation boundaries specified by
`I2CControlledRouting_V2.md`. These boundaries are infrastructure and are not
software-selected routes.

### 6.2 Modes And Configuration Options

In the de-energized `OFF` condition, routing-control power is removed and every controlled path shall
remain in its safe inactive state. In `STANDALONE`, the harness-local
regulator powers the Routing Logic Supply Rail; in `SUPERVISOR`, the external
regulated 3.3 V source powers it. The target remains the routing owner in both
active modes.

In `SUPERVISOR`, the Routing Logic Supply Rail remains powered while target
power is cycled. Hardware Clear establishes the safe routing state before the
target starts or is removed, and target firmware establishes the selected
configuration after startup.

The [accepted Target Routing Envelope](TargetRoutingEnvelope_V2.md) defines the
common R0-R6 route-entry minimum, legal direct alternatives and required
simultaneous configurations. A Target Profile may therefore use the common
routed form, direct Test Block paths or a reviewed combination of both. It
shall declare the legal route sets, block-local selections, conflicts,
exclusive reuse and unavailable capabilities. The service does not provide an
arbitrary crosspoint matrix.

### 6.3 Sequencing, Safety And Evidence

A route change shall use this safe order:

1. place affected target and peer drivers in their inactive or high-impedance
   states
2. clear connections that conflict with the requested configuration
3. apply the complete legal route and block-local selection
4. read back and verify the commanded state
5. enable target or Test Block drivers only after verification
6. disable drivers, clear the configuration and verify the safe state after
   the test

An invalid or incomplete configuration shall be rejected before any driver is
enabled. Controlled paths shall default high impedance before software
configuration, during reset and after Hardware Clear. No configuration may
connect two active outputs, apply more than one active source to an input,
leave conflicting direct and routed paths enabled or back-power an unpowered
target. Target boot, strap, console and recovery signals shall remain safe
throughout route changes.

A hardware clear associated with reset or recovery shall return routing and
block-local switches to their safe state without target I2C activity.
Controller readback confirms the commanded control state; prototype
continuity and electrical tests verify that the physical path implements it.

Evidence shall record the Target Profile revision, requested logical
capability, resolved route and block-local selections, control writes,
readback, safe state before and after the test, and any rejected or failed
operation. Exact switch topology, components, I2C addresses, register map,
physical Target Interface contacts and signal-integrity limits remain owned by
the routing specification, connection matrix and schematic work.
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
