SimonGAndrews/ESP32_SGATest/docs/design/V2Harness/arch/diagrams/Rack-Architecture-Power-Supervisor_V2.png

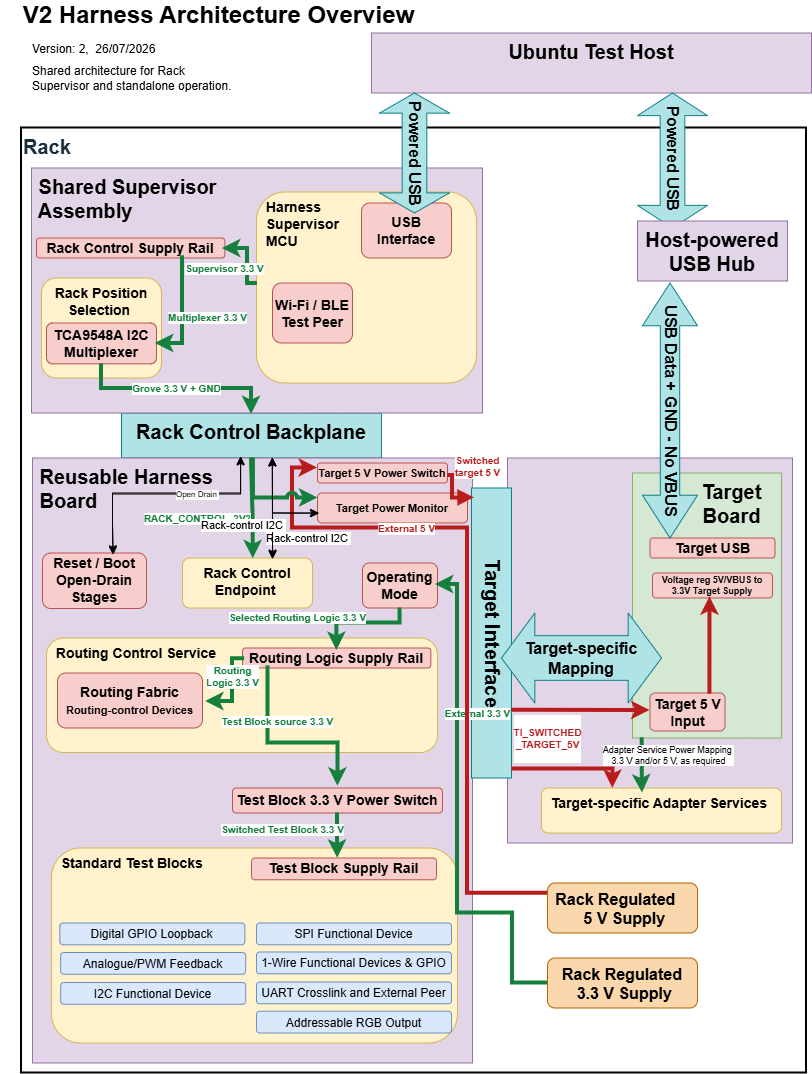
docs/design/V2Harness/arch/diagrams/Rack-Architecture-Power-Supervisor_V2.png
