SimonGAndrews/ESP32_SGATest/docs/design/V2Harness/implementation/review-images/PC02-target-5v-switch-and-two-range-monitor.png

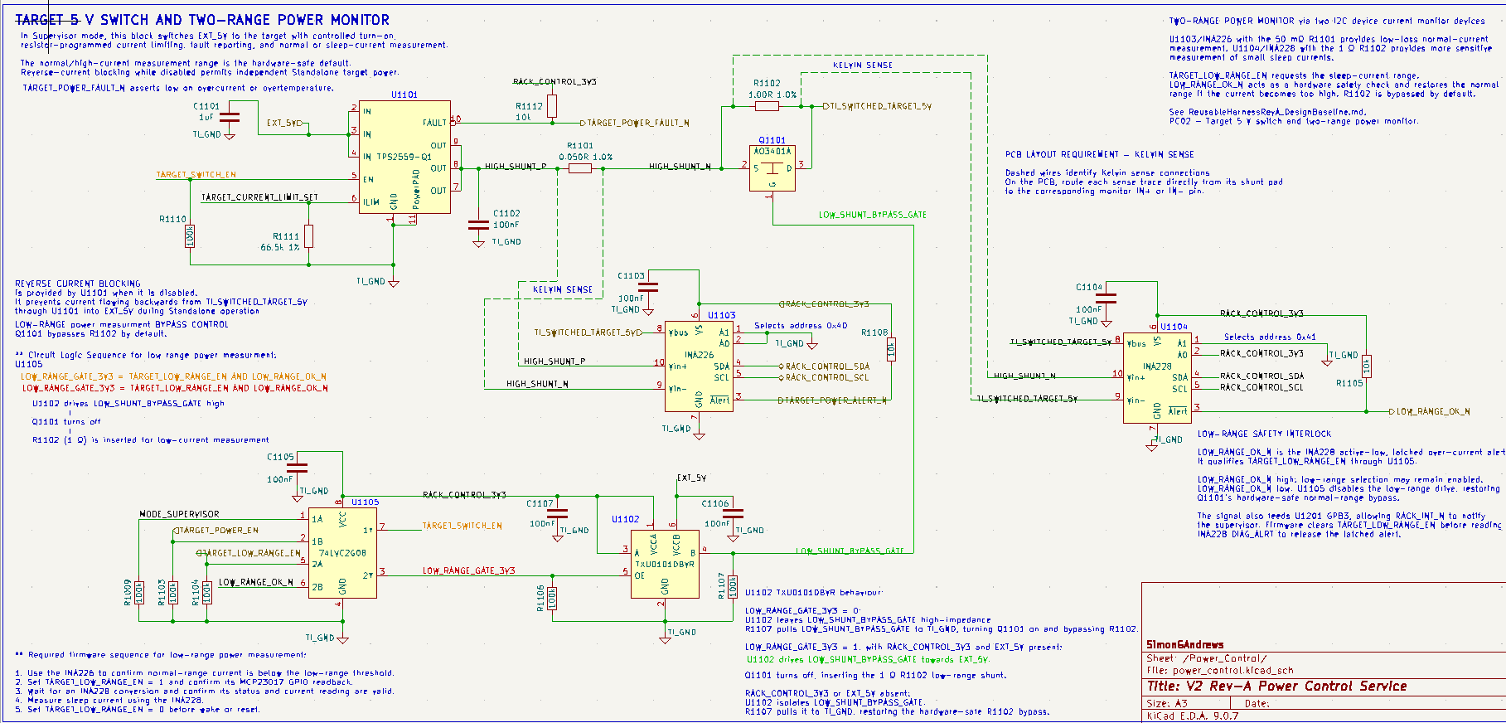
docs/design/V2Harness/implementation/review-images/PC02-target-5v-switch-and-two-range-monitor.png
