SimonGAndrews/ESP32_SGATest/docs/design/V2Harness/implementation/review-images/RC01-routing-fabric.png

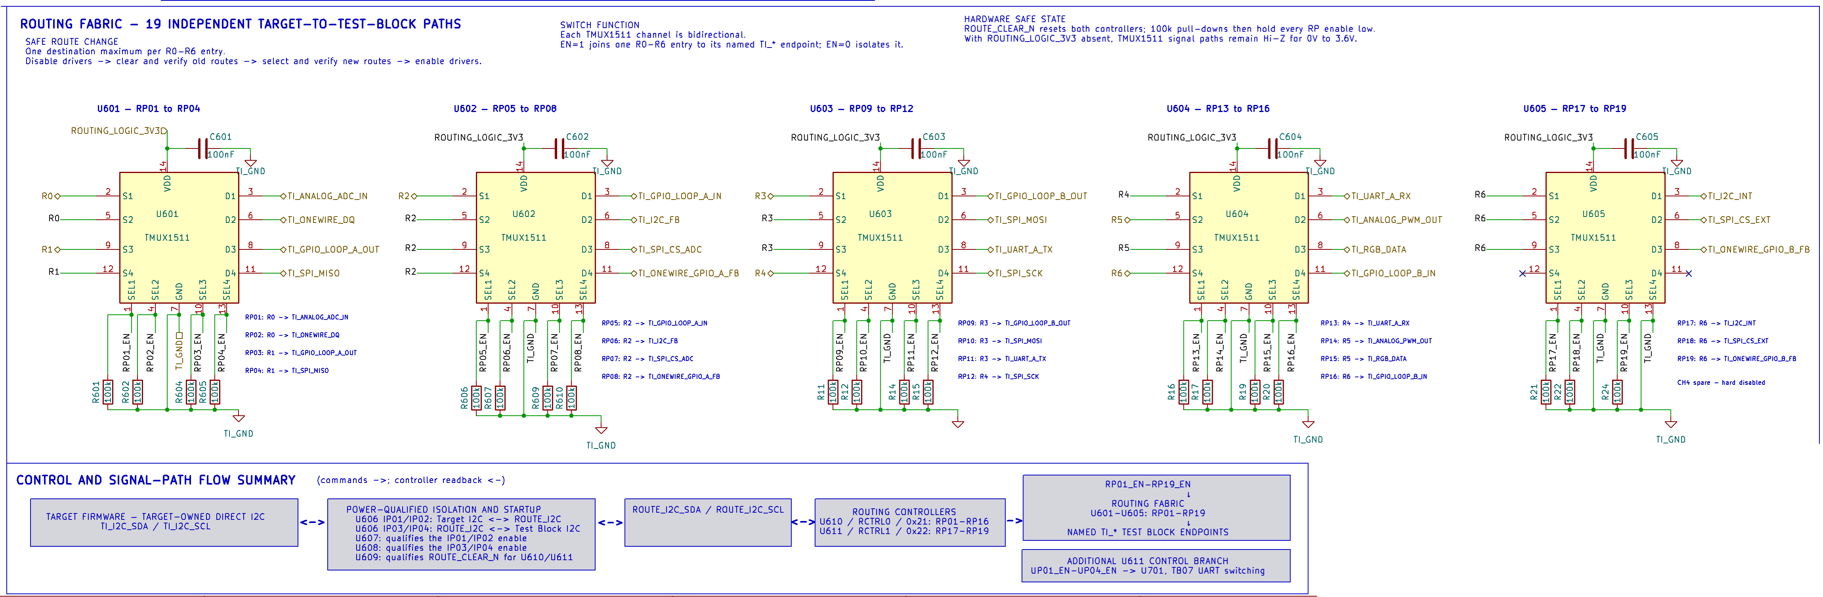
docs/design/V2Harness/implementation/review-images/RC01-routing-fabric.png
