SimonGAndrews/ESP32_SGATest/docs/design/V2Harness/implementation/review-images/RC02-routing-controllers-and-fixed-i2c-isolation.png

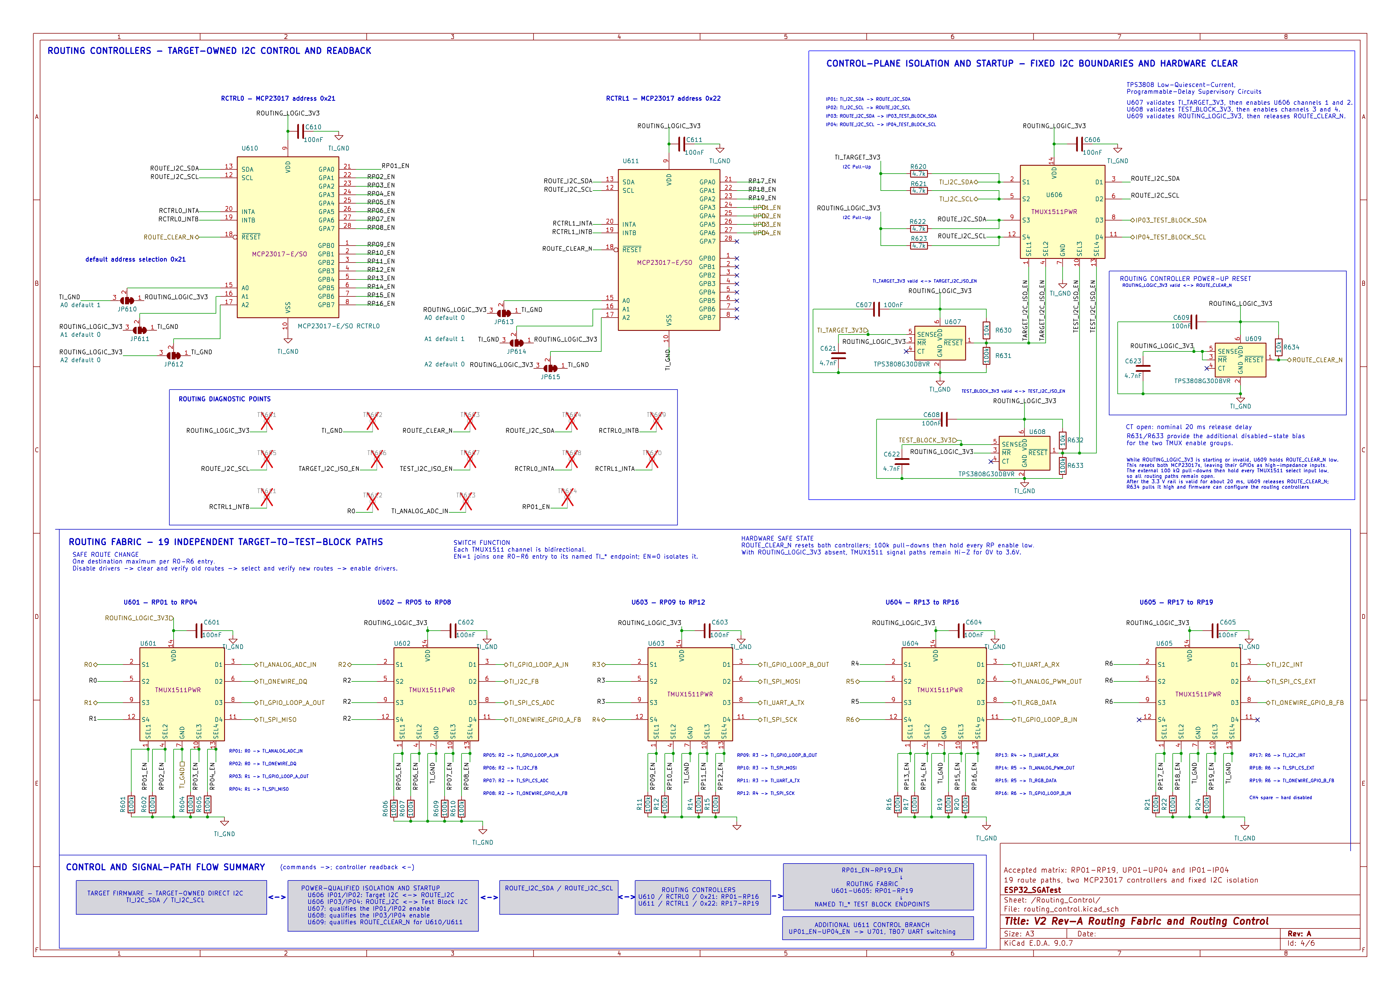
docs/design/V2Harness/implementation/review-images/RC02-routing-controllers-and-fixed-i2c-isolation.png
