SimonGAndrews/ESP32_SGATest/docs/design/V2Harness/implementation/review-images/TB02-analogue-pwm-feedback.png

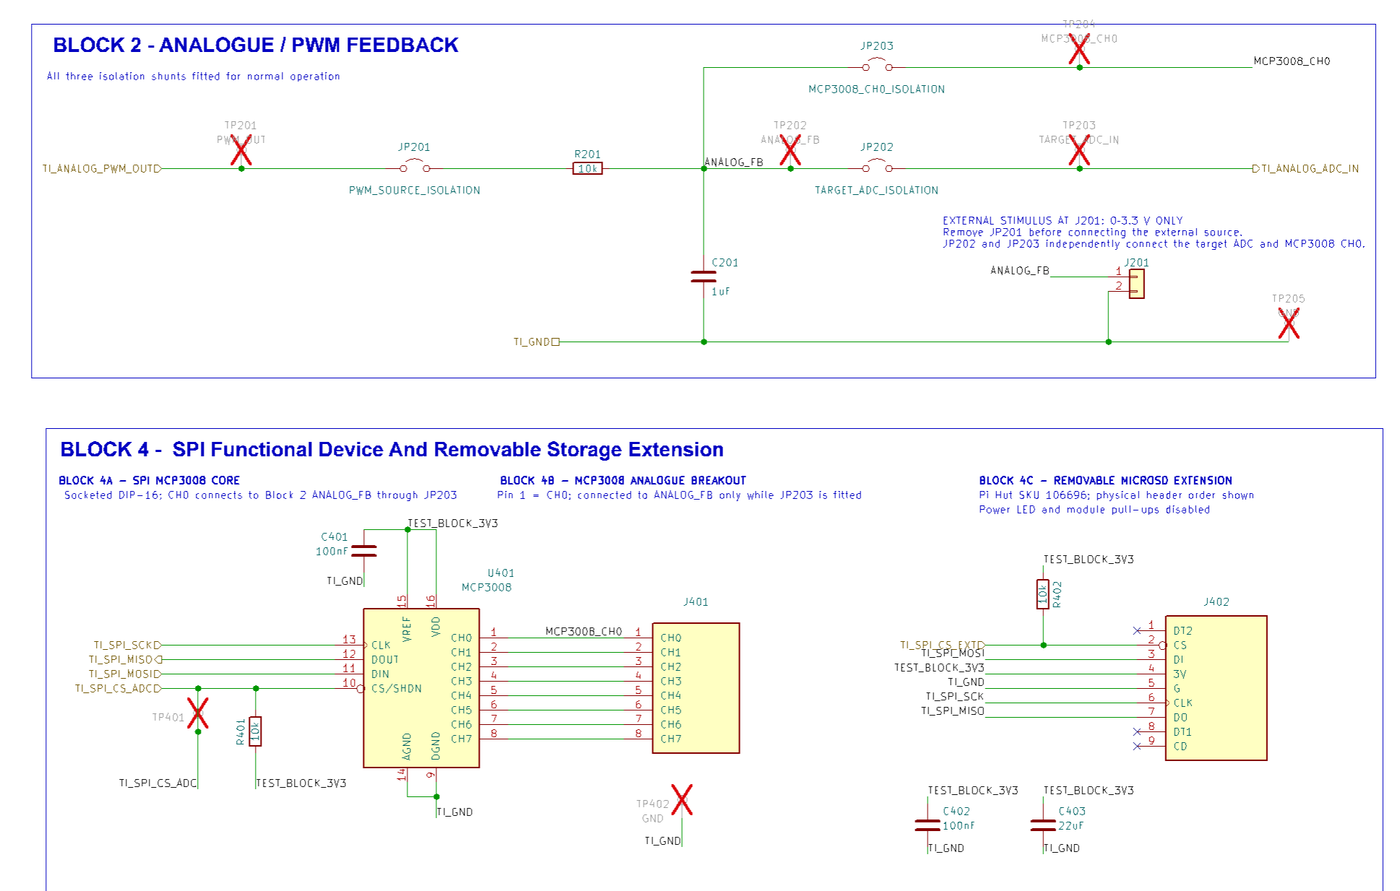
docs/design/V2Harness/implementation/review-images/TB02-analogue-pwm-feedback.png
