SimonGAndrews/ESP32_SGATest/docs/design/V2Harness/implementation/review-images/TB03-i2c-functional-device.png

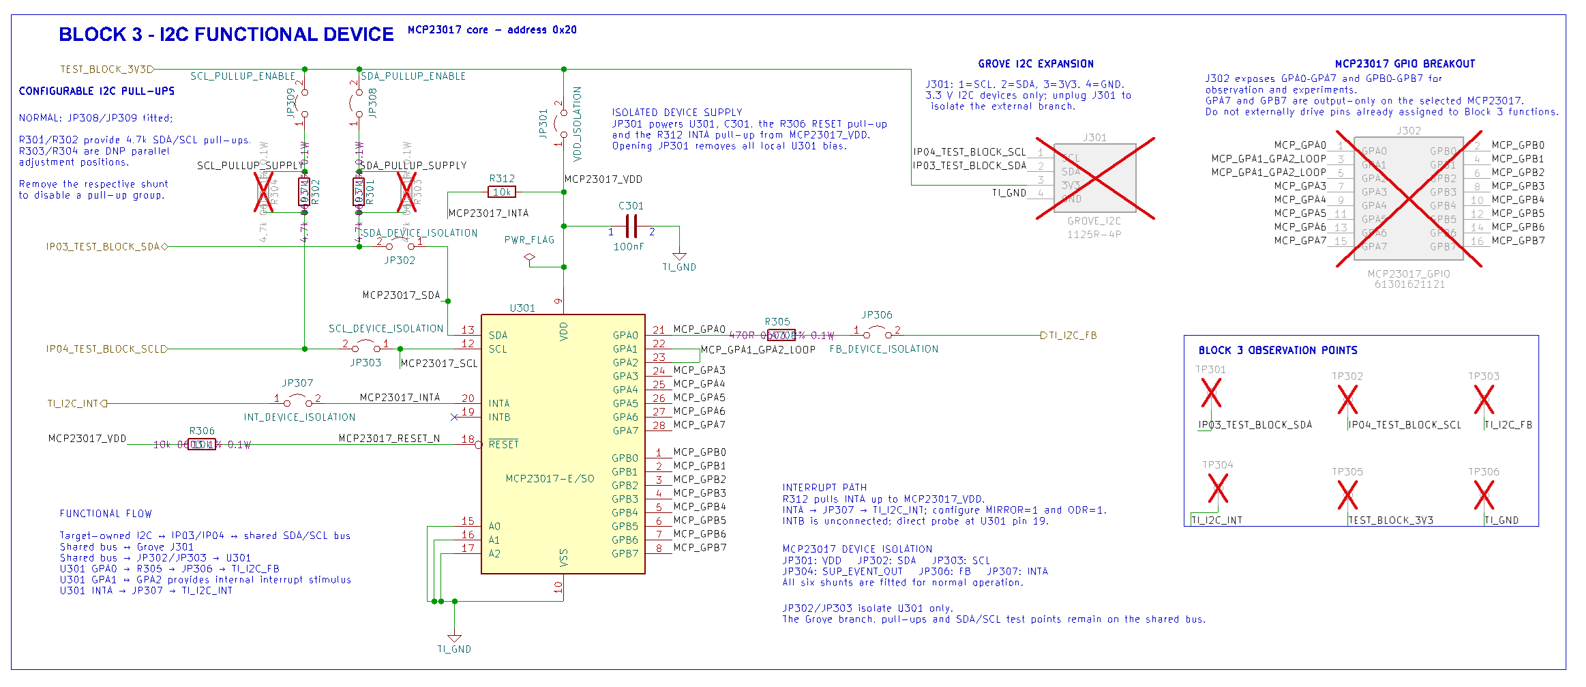
docs/design/V2Harness/implementation/review-images/TB03-i2c-functional-device.png
