SimonGAndrews/ESP32_SGATest/docs/design/V2Harness/implementation/review-images/TB04-spi-functional-device-and-storage.png

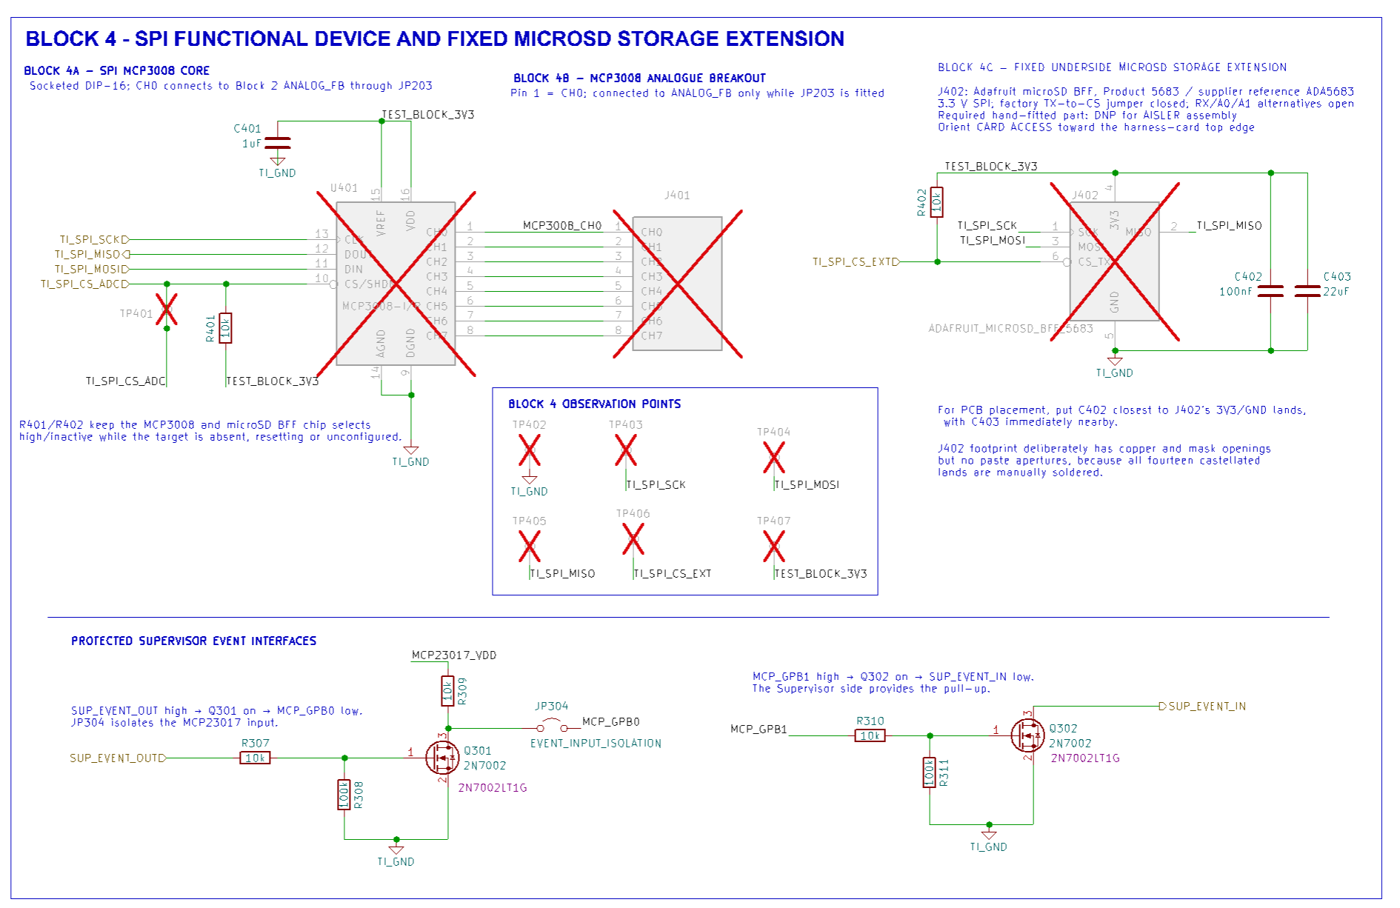
docs/design/V2Harness/implementation/review-images/TB04-spi-functional-device-and-storage.png
