SimonGAndrews/ESP32_SGATest/docs/design/V2Harness/implementation/review-images/TB05-onewire-functional-devices-and-gpio.png

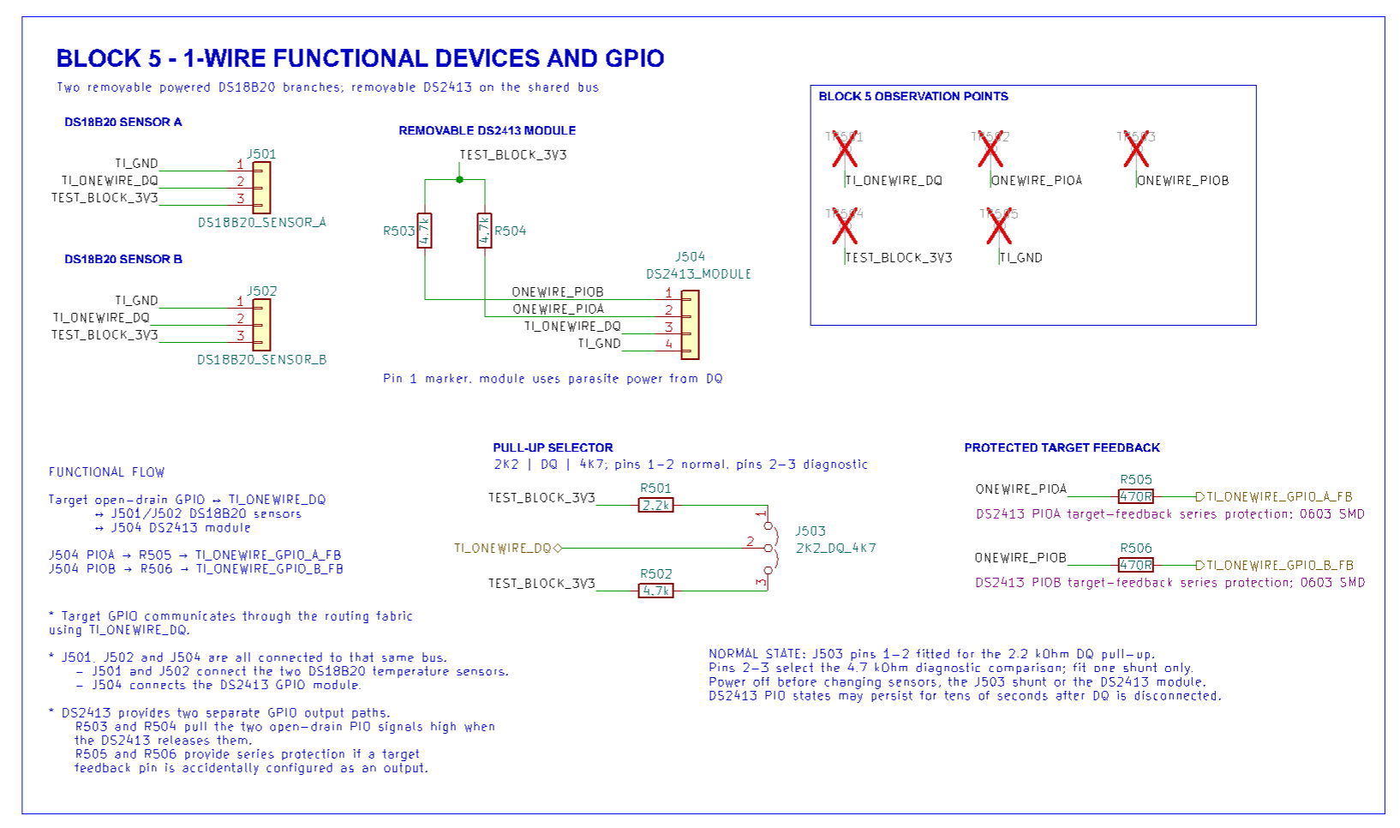
docs/design/V2Harness/implementation/review-images/TB05-onewire-functional-devices-and-gpio.png
