SimonGAndrews/ESP32_SGATest/docs/design/V2Harness/implementation/review-images/TB07-uart-crosslink-and-external-peer.png

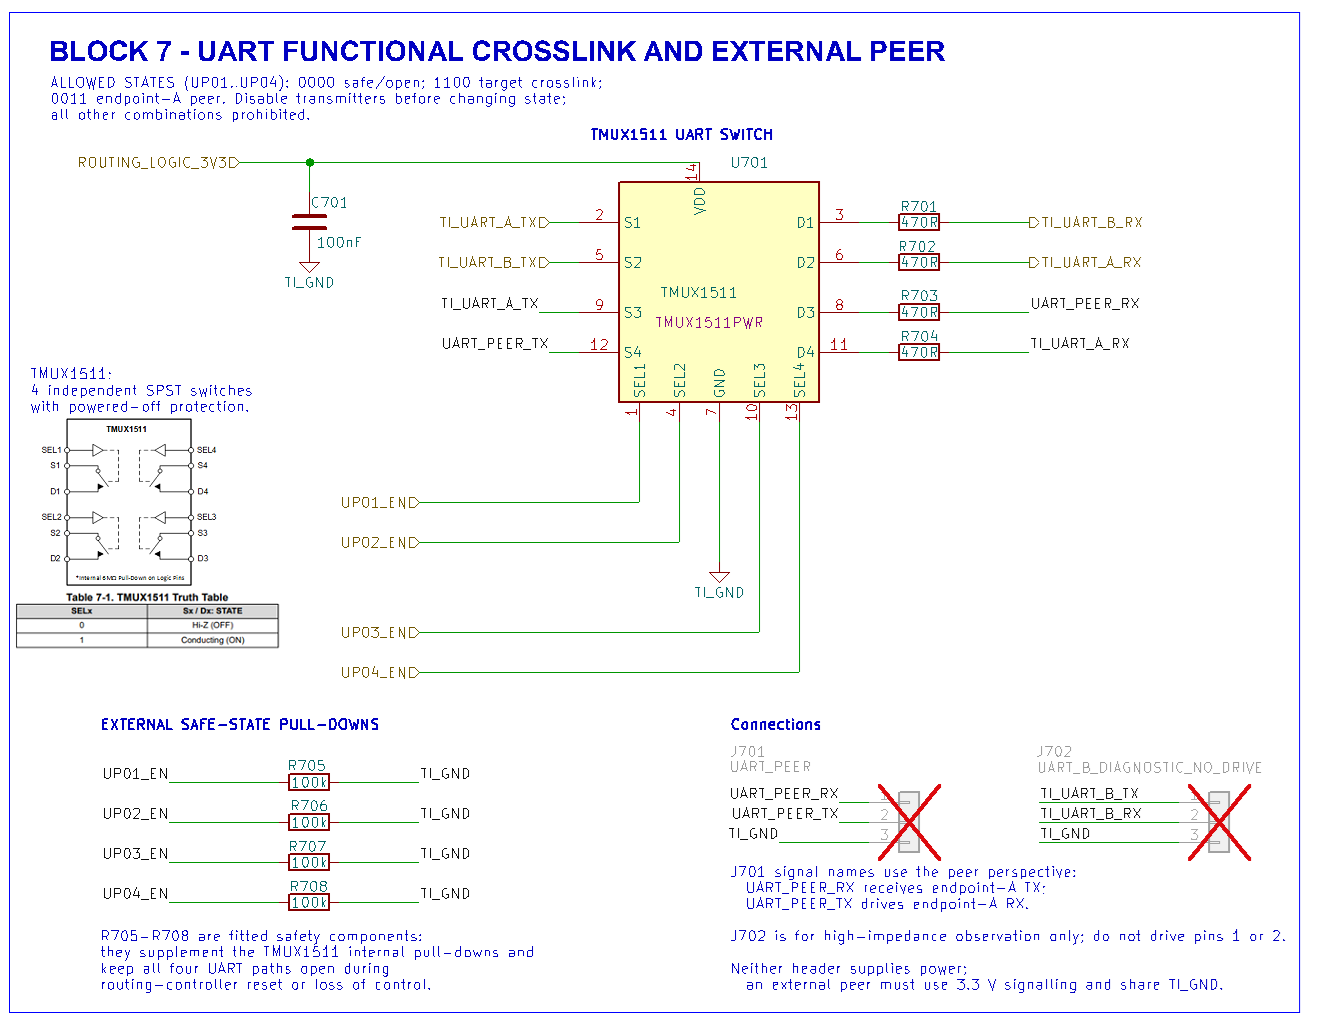
docs/design/V2Harness/implementation/review-images/TB07-uart-crosslink-and-external-peer.png
