SimonGAndrews/ESP32_SGATest/docs/investigations/watch-debounce/artifacts/scope-captures/Watch Pico - Pulse 20 20 20 - no stress.jpg

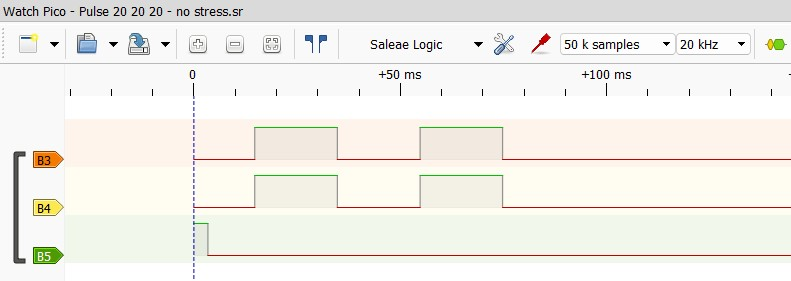
docs/investigations/watch-debounce/artifacts/scope-captures/Watch Pico - Pulse 20 20 20 - no stress.jpg
