SimonGAndrews/ESP32_SGATest/docs/investigations/watch-debounce/artifacts/scope-captures/Watch Pico - Pulse 20 20 20 start 35.jpg

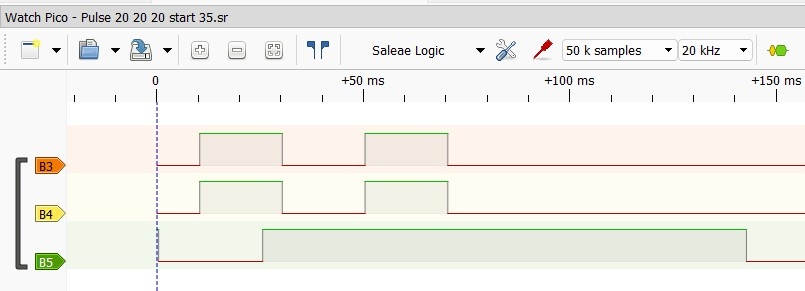
docs/investigations/watch-debounce/artifacts/scope-captures/Watch Pico - Pulse 20 20 20 start 35.jpg
