SimonGAndrews/ESP32_SGATest/docs/targets/ESP32-S3-DevKitC-1_V1.1/Resources/Connectors_ESP32-S3-DevKitC-1_V1.1_20220429.png

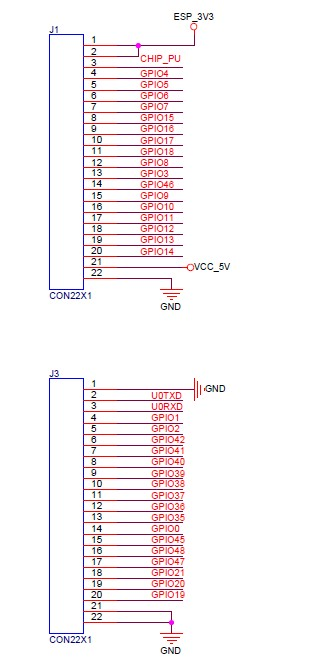
docs/targets/ESP32-S3-DevKitC-1_V1.1/Resources/Connectors_ESP32-S3-DevKitC-1_V1.1_20220429.png
