SimonGAndrews/ESP32_SGATest/docs/targets/MDBT42Q_breakout/resources/connector_pins.jpg

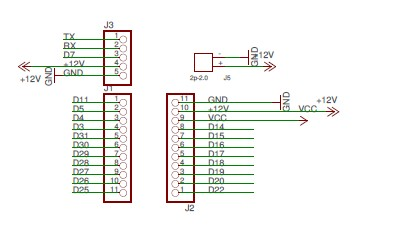
docs/targets/MDBT42Q_breakout/resources/connector_pins.jpg
