SimonGAndrews/ESP32_SGATest/docs/targets/olimex-esp32-devkit-lipo/Resources/ESP32-S3-DevKit-LiPo-dimensions.png

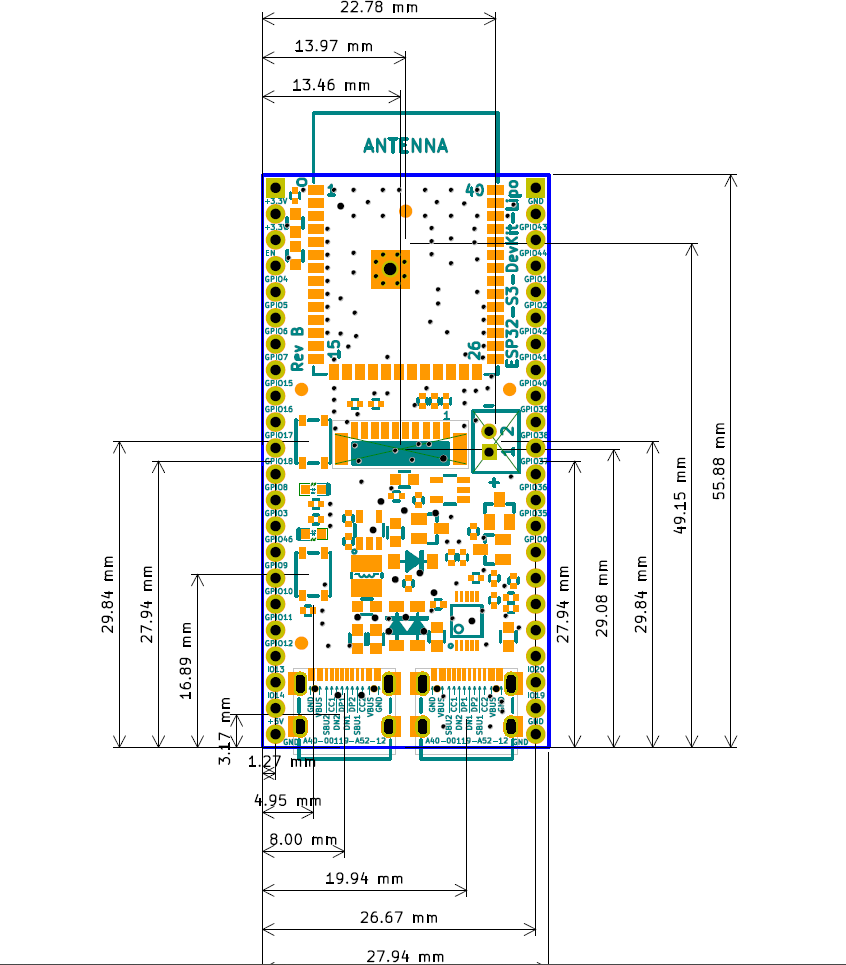
docs/targets/olimex-esp32-devkit-lipo/Resources/ESP32-S3-DevKit-LiPo-dimensions.png
