SimonGAndrews/ESP32_SGATest/docs/targets/Raspberry-Pi-Pico-Family/Resources/Raspberry-Pi-Pico-2-W-details-size.jpg

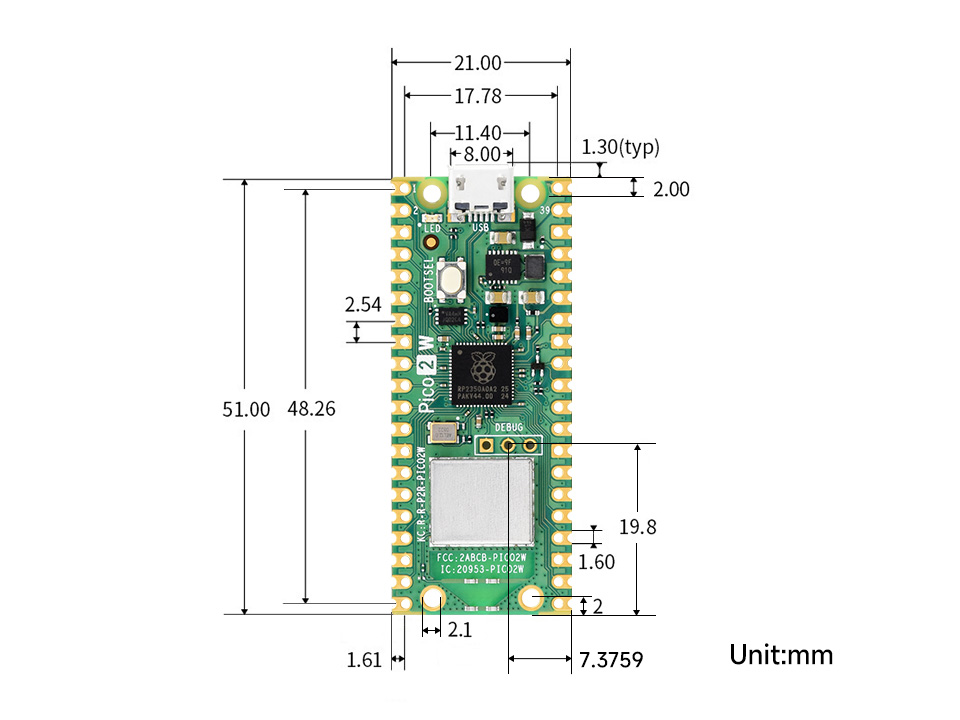
docs/targets/Raspberry-Pi-Pico-Family/Resources/Raspberry-Pi-Pico-2-W-details-size.jpg
