SimonGAndrews/ESP32_SGATest/Hardware/ESP32_C3/ESP_C3_harness.jpeg

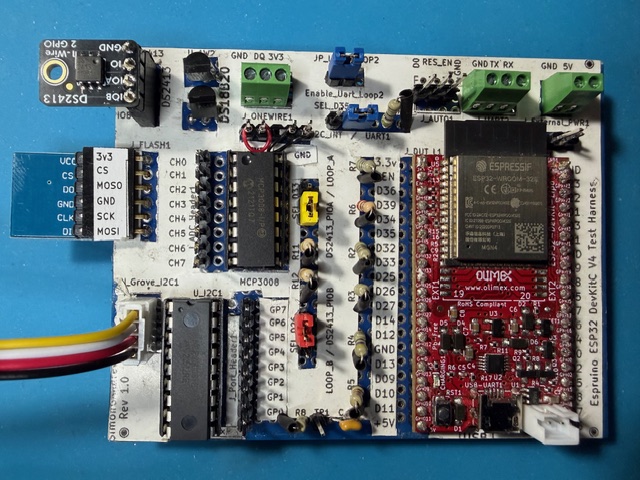
Hardware/ESP32_C3/ESP_C3_harness.jpeg
