SimonGAndrews/ESP32_SGATest/Hardware/ESP32_V1/ESP32_V1_harness.jpeg

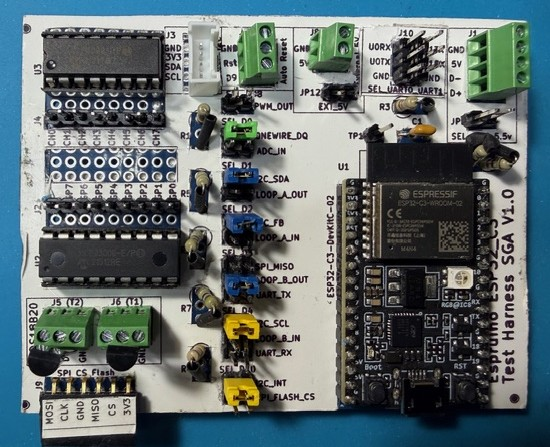
Hardware/ESP32_V1/ESP32_V1_harness.jpeg
