SimonGAndrews/ESP32_SGATest/KICAD/V2/ComponentDevelopment/EspruinoPicoDirectMount/Pico_BottomSide.png

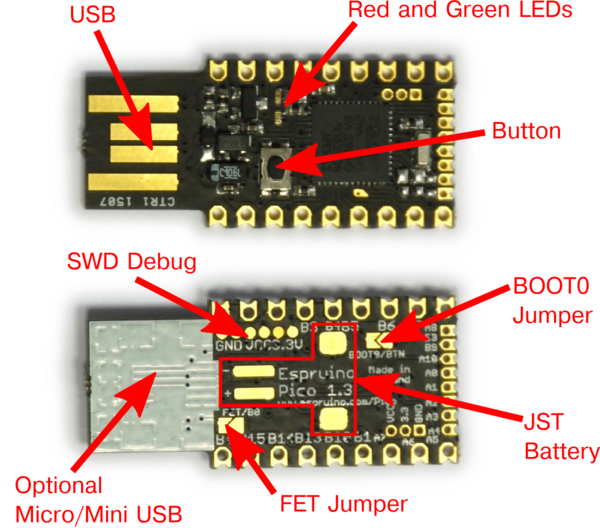
KICAD/V2/ComponentDevelopment/EspruinoPicoDirectMount/Pico_BottomSide.png
