SimonGAndrews/ESP32_SGATest/docs/investigations/IDF5_port_testing/IDF5_build/ESP32_GW_baseline_ESP32_build_error_01.txt

simon@OptiPlex3050:~/MaBecker/Espruino_IDF5_Gordon_validation$ make BOARD=ESP32_IDF5 RELEASE=1 flash
##@cp /home/simon/MaBecker/Espruino_IDF5_Gordon_validation/targets/esp32/IDF5/sdkconfig.defaults.esp32 bin
# Only add mdns dependency if missing
Executing action: add-dependency
NOTICE: Created "/home/simon/MaBecker/Espruino_IDF5_Gordon_validation/bin/main/idf_component.yml"
NOTICE: Successfully added dependency "espressif/mdns": "^1.11.0" to component "main"
NOTICE: If you want to make additional changes to the manifest file at path /home/simon/MaBecker/Espruino_IDF5_Gordon_validation/bin/main/idf_component.yml manually, please refer to the documentation: https://docs.espressif.com/projects/idf-component-manager/en/latest/reference/manifest_file.html
Done
cd bin && idf.py build
Executing action: all (aliases: build)
Running cmake in directory /home/simon/MaBecker/Espruino_IDF5_Gordon_validation/bin/build
Executing "cmake -G Ninja -DPYTHON_DEPS_CHECKED=1 -DPYTHON=/home/simon/.espressif/python_env/idf4.4_py3.12_env/bin/python -DESP_PLATFORM=1 -DCCACHE_ENABLE=0 /home/simon/MaBecker/Espruino_IDF5_Gordon_validation/bin"...
-- IDF_TARGET is not set, guessed 'esp32' from sdkconfig '/home/simon/MaBecker/Espruino_IDF5_Gordon_validation/bin/sdkconfig.defaults'
-- Found Git: /usr/bin/git (found version "2.43.0")
-- Minimal build - ON
-- The C compiler identification is GNU 14.2.0
-- The CXX compiler identification is GNU 14.2.0
-- The ASM compiler identification is GNU
-- Found assembler: /home/simon/.espressif/tools/xtensa-esp-elf/esp-14.2.0_20251107/xtensa-esp-elf/bin/xtensa-esp32-elf-gcc
-- Detecting C compiler ABI info
-- Detecting C compiler ABI info - done
-- Check for working C compiler: /home/simon/.espressif/tools/xtensa-esp-elf/esp-14.2.0_20251107/xtensa-esp-elf/bin/xtensa-esp32-elf-gcc - skipped
-- Detecting C compile features
-- Detecting C compile features - done
-- Detecting CXX compiler ABI info
-- Detecting CXX compiler ABI info - done
-- Check for working CXX compiler: /home/simon/.espressif/tools/xtensa-esp-elf/esp-14.2.0_20251107/xtensa-esp-elf/bin/xtensa-esp32-elf-g++ - skipped
-- Detecting CXX compile features
-- Detecting CXX compile features - done
-- Building ESP-IDF components for target esp32
NOTICE: Dependencies lock doesn't exist, solving dependencies.
...NOTICE: Updating lock file at /home/simon/MaBecker/Espruino_IDF5_Gordon_validation/bin/dependencies.lock
NOTICE: Processing 2 dependencies:
NOTICE: [1/2] espressif/mdns (1.11.3)
NOTICE: [2/2] idf (5.5.3)
-- ESP-TEE is currently supported only on the esp32c6;esp32h2;esp32c5 SoCs
-- Project sdkconfig file /home/simon/MaBecker/Espruino_IDF5_Gordon_validation/bin/sdkconfig
Loading defaults file /home/simon/MaBecker/Espruino_IDF5_Gordon_validation/bin/sdkconfig.defaults...
/home/simon/MaBecker/Espruino_IDF5_Gordon_validation/bin/sdkconfig.defaults:21 CONFIG_TASK_WDT was replaced with CONFIG_ESP_TASK_WDT_INIT
/home/simon/MaBecker/Espruino_IDF5_Gordon_validation/bin/sdkconfig.defaults:40 CONFIG_ESP32_DEFAULT_CPU_FREQ_240 was replaced with CONFIG_ESP_DEFAULT_CPU_FREQ_MHZ_240
warning: unknown kconfig symbol 'BT_ENABLED' assigned to 'y' in /home/simon/MaBecker/Espruino_IDF5_Gordon_validation/bin/sdkconfig.defaults
warning: unknown kconfig symbol 'RMT_SUPPRESS_DEPRECATE_WARN' assigned to 'y' in /home/simon/MaBecker/Espruino_IDF5_Gordon_validation/bin/sdkconfig.defaults
-- Compiler supported targets: xtensa-esp-elf
-- Found Python3: /home/simon/.espressif/python_env/idf4.4_py3.12_env/bin/python (found version "3.12.3") found components: Interpreter
-- Performing Test CMAKE_HAVE_LIBC_PTHREAD
-- Performing Test CMAKE_HAVE_LIBC_PTHREAD - Success
-- Found Threads: TRUE
-- Performing Test C_COMPILER_SUPPORTS_WFORMAT_SIGNEDNESS
-- Performing Test C_COMPILER_SUPPORTS_WFORMAT_SIGNEDNESS - Success
-- USING O3
-- App "espruino" version: RELEASE_2V28-143-g391070be2
-- Adding linker script /home/simon/MaBecker/Espruino_IDF5_Gordon_validation/bin/build/esp-idf/esp_system/ld/memory.ld
-- Adding linker script /home/simon/MaBecker/Espruino_IDF5_Gordon_validation/bin/build/esp-idf/esp_system/ld/sections.ld.in
-- Adding linker script /home/simon/MaBecker/Espruino_IDF5_Gordon_validation/esp-idf-5/esp-idf/components/esp_rom/esp32/ld/esp32.rom.ld
-- Adding linker script /home/simon/MaBecker/Espruino_IDF5_Gordon_validation/esp-idf-5/esp-idf/components/esp_rom/esp32/ld/esp32.rom.api.ld
-- Adding linker script /home/simon/MaBecker/Espruino_IDF5_Gordon_validation/esp-idf-5/esp-idf/components/esp_rom/esp32/ld/esp32.rom.libgcc.ld
-- Adding linker script /home/simon/MaBecker/Espruino_IDF5_Gordon_validation/esp-idf-5/esp-idf/components/esp_rom/esp32/ld/esp32.rom.newlib-data.ld
-- Adding linker script /home/simon/MaBecker/Espruino_IDF5_Gordon_validation/esp-idf-5/esp-idf/components/esp_rom/esp32/ld/esp32.rom.syscalls.ld
-- Adding linker script /home/simon/MaBecker/Espruino_IDF5_Gordon_validation/esp-idf-5/esp-idf/components/esp_rom/esp32/ld/esp32.rom.libc-funcs.ld
-- Adding linker script /home/simon/MaBecker/Espruino_IDF5_Gordon_validation/esp-idf-5/esp-idf/components/esp_rom/esp32/ld/esp32.rom.newlib-reent-funcs.ld
-- Adding linker script /home/simon/MaBecker/Espruino_IDF5_Gordon_validation/esp-idf-5/esp-idf/components/soc/esp32/ld/esp32.peripherals.ld
-- Components: app_update bootloader bootloader_support console cxx efuse esp_app_format esp_bootloader_format esp_coex esp_common esp_driver_gpio esp_driver_spi esp_driver_uart esp_driver_usb_serial_jtag esp_event esp_hw_support esp_mm esp_netif esp_netif_stack esp_partition esp_phy esp_pm esp_psram esp_ringbuf esp_rom esp_security esp_system esp_timer esp_vfs_console esp_wifi espressif__mdns esptool_py freertos hal heap log lwip main mbedtls newlib nvs_flash partition_table pthread soc spi_flash vfs wpa_supplicant xtensa
-- Component paths: /home/simon/MaBecker/Espruino_IDF5_Gordon_validation/esp-idf-5/esp-idf/components/app_update /home/simon/MaBecker/Espruino_IDF5_Gordon_validation/esp-idf-5/esp-idf/components/bootloader /home/simon/MaBecker/Espruino_IDF5_Gordon_validation/esp-idf-5/esp-idf/components/bootloader_s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
-- Configuring done (20.2s)
-- Generating done (1.1s)
-- Build files have been written to: /home/simon/MaBecker/Espruino_IDF5_Gordon_validation/bin/build
Running ninja in directory /home/simon/MaBecker/Espruino_IDF5_Gordon_validation/bin/build
Executing "ninja all"...
[4/863] Generating ../../partition_table/partition-table.bin
Partition table binary generated. Contents:
*******************************************************************************
# ESP-IDF Partition Table
# Name, Type, SubType, Offset, Size, Flags
nvs,data,nvs,0x9000,24K,
phy_init,data,phy,0xf000,4K,
factory,app,factory,0x10000,2000K,
flash,data,64,0x310000,64K,
storage,data,undefined,0x320000,896K,
*******************************************************************************
[286/863] Performing configure step for 'bootloader'
-- Found Git: /usr/bin/git (found version "2.43.0")
-- Minimal build - OFF
-- The C compiler identification is GNU 14.2.0
-- The CXX compiler identification is GNU 14.2.0
-- The ASM compiler identification is GNU
-- Found assembler: /home/simon/.espressif/tools/xtensa-esp-elf/esp-14.2.0_20251107/xtensa-esp-elf/bin/xtensa-esp32-elf-gcc
-- Detecting C compiler ABI info
-- Detecting C compiler ABI info - done
-- Check for working C compiler: /home/simon/.espressif/tools/xtensa-esp-elf/esp-14.2.0_20251107/xtensa-esp-elf/bin/xtensa-esp32-elf-gcc - skipped
-- Detecting C compile features
-- Detecting C compile features - done
-- Detecting CXX compiler ABI info
-- Detecting CXX compiler ABI info - done
-- Check for working CXX compiler: /home/simon/.espressif/tools/xtensa-esp-elf/esp-14.2.0_20251107/xtensa-esp-elf/bin/xtensa-esp32-elf-g++ - skipped
-- Detecting CXX compile features
-- Detecting CXX compile features - done
-- Building ESP-IDF components for target esp32
-- ESP-TEE is currently supported only on the esp32c6;esp32h2;esp32c5 SoCs
-- Project sdkconfig file /home/simon/MaBecker/Espruino_IDF5_Gordon_validation/bin/sdkconfig
-- Compiler supported targets: xtensa-esp-elf
-- Adding linker script /home/simon/MaBecker/Espruino_IDF5_Gordon_validation/esp-idf-5/esp-idf/components/soc/esp32/ld/esp32.peripherals.ld
-- Bootloader project name: "bootloader" version: 1
-- Adding linker script /home/simon/MaBecker/Espruino_IDF5_Gordon_validation/esp-idf-5/esp-idf/components/esp_rom/esp32/ld/esp32.rom.ld
-- Adding linker script /home/simon/MaBecker/Espruino_IDF5_Gordon_validation/esp-idf-5/esp-idf/components/esp_rom/esp32/ld/esp32.rom.api.ld
-- Adding linker script /home/simon/MaBecker/Espruino_IDF5_Gordon_validation/esp-idf-5/esp-idf/components/esp_rom/esp32/ld/esp32.rom.libgcc.ld
-- Adding linker script /home/simon/MaBecker/Espruino_IDF5_Gordon_validation/esp-idf-5/esp-idf/components/esp_rom/esp32/ld/esp32.rom.libc-funcs.ld
-- Adding linker script /home/simon/MaBecker/Espruino_IDF5_Gordon_validation/esp-idf-5/esp-idf/components/bootloader/subproject/main/ld/esp32/bootloader.rom.ld
-- Components: bootloader bootloader_support efuse esp_app_format esp_bootloader_format esp_common esp_hw_support esp_rom esp_security esp_system esptool_py freertos hal log main micro-ecc newlib partition_table soc spi_flash xtensa
-- Component paths: /home/simon/MaBecker/Espruino_IDF5_Gordon_validation/esp-idf-5/esp-idf/components/bootloader /home/simon/MaBecker/Espruino_IDF5_Gordon_validation/esp-idf-5/esp-idf/components/bootloader_support /home/simon/MaBecker/Espruino_IDF5_Gordon_validation/esp-idf-5/esp-idf/components/efuse /home/simon/MaBecker/Espruino_IDF5_Gordon_validation/esp-idf-5/esp-idf/components/esp_app_format /home/simon/MaBecker/Espruino_IDF5_Gordon_validation/esp-idf-5/esp-idf/components/esp_bootloader_format /home/simon/MaBecker/Espruino_IDF5_Gordon_validation/esp-idf-5/esp-idf/components/esp_common /home/simon/MaBecker/Espruino_IDF5_Gordon_validation/esp-idf-5/esp-idf/components/esp_hw_support /home/simon/MaBecker/Espruino_IDF5_Gordon_validation/esp-idf-5/esp-idf/components/esp_rom /home/simon/MaBecker/Espruino_IDF5_Gordon_validation/esp-idf-5/esp-idf/components/esp_security /home/simon/MaBecker/Espruino_IDF5_Gordon_validation/esp-idf-5/esp-idf/components/esp_system /home/simon/MaBecker/Espruino_IDF5_Gordon_validation/esp-idf-5/esp-idf/components/esptool_py /home/simon/MaBecker/Espruino_IDF5_Gordon_validation/esp-idf-5/esp-idf/components/freertos /home/simon/MaBecker/Espruino_IDF5_Gordon_validation/esp-idf-5/esp-idf/components/hal /home/simon/MaBecker/Espruino_IDF5_Gordon_validation/esp-idf-5/esp-idf/components/log /home/simon/MaBecker/Espruino_IDF5_Gordon_validation/esp-idf-5/esp-idf/components/bootloader/subproject/main /home/simon/MaBecker/Espruino_IDF5_Gordon_validation/esp-idf-5/esp-idf/components/bootloader/subproject/components/micro-ecc /home/simon/MaBecker/Espruino_IDF5_Gordon_validation/esp-idf-5/esp-idf/components/newlib /home/simon/MaBecker/Espruino_IDF5_Gordon_validation/esp-idf-5/esp-idf/components/partition_table /home/simon/MaBecker/Espruino_IDF5_Gordon_validation/esp-idf-5/esp-idf/components/soc /home/simon/MaBecker/Espruino_IDF5_Gordon_validation/esp-idf-5/esp-idf/components/spi_flash /home/simon/MaBecker/Espruino_IDF5_Gordon_validation/esp-idf-5/esp-idf/components/xtensa
-- Adding linker script /home/simon/MaBecker/Espruino_IDF5_Gordon_validation/esp-idf-5/esp-idf/components/bootloader/subproject/main/ld/esp32/bootloader.ld
-- Configuring done (20.8s)
-- Generating done (0.4s)
-- Build files have been written to: /home/simon/MaBecker/Espruino_IDF5_Gordon_validation/bin/build/bootloader
[117/118] Generating binary image from built executable
esptool.py v4.12.0
Creating esp32 image...
Merged 2 ELF sections
Successfully created esp32 image.
Generated /home/simon/MaBecker/Espruino_IDF5_Gordon_validation/bin/build/bootloader/bootloader.bin
[118/118] cd /home/simon/MaBecker/Espruino_IDF5_Gordon_validation/bin/build/bo...n/MaBecker/Espruino_IDF5_Gordon_validation/bin/build/bootloader/bootloader.bin
Bootloader binary size 0x5b30 bytes. 0x14d0 bytes (19%) free.
[775/863] Building C object esp-idf/main/CMakeFiles/__idf_main.dir/home/simon/MaBecker/Espruino_IDF5_Gordon_validation/src/jsdevices.c.obj
/home/simon/MaBecker/Espruino_IDF5_Gordon_validation/src/jsdevices.c:450:1: warning: ignoring attribute 'section (".iram1.3")' because it conflicts with previous 'section (".iram1.0")' [-Wattributes]
  450 | bool CALLED_FROM_INTERRUPT jshPushEvent(IOEventFlags evt, uint8_t *data, unsigned int length) {
      | ^~~~
In file included from /home/simon/MaBecker/Espruino_IDF5_Gordon_validation/src/jsdevices.c:15:
/home/simon/MaBecker/Espruino_IDF5_Gordon_validation/src/jsdevices.h:191:28: note: previous declaration here
  191 | bool CALLED_FROM_INTERRUPT jshPushEvent(IOEventFlags evt, uint8_t *data, unsigned int length);
      |                            ^~~~~~~~~~~~
/home/simon/MaBecker/Espruino_IDF5_Gordon_validation/src/jsdevices.c:484:1: warning: ignoring attribute 'section (".iram1.4")' because it conflicts with previous 'section (".iram1.1")' [-Wattributes]
  484 | bool CALLED_FROM_INTERRUPT jshPushCustomEvent(IOCustomEventFlags customFlags) {
      | ^~~~
/home/simon/MaBecker/Espruino_IDF5_Gordon_validation/src/jsdevices.h:193:28: note: previous declaration here
  193 | bool CALLED_FROM_INTERRUPT jshPushCustomEvent(IOCustomEventFlags customFlags);
      |                            ^~~~~~~~~~~~~~~~~~
/home/simon/MaBecker/Espruino_IDF5_Gordon_validation/src/jsdevices.c: In function 'jshPushIOCharEvents':
/home/simon/MaBecker/Espruino_IDF5_Gordon_validation/src/jsdevices.c:503:43: warning: passing argument 2 of 'jshPushIOCharEventsHandler' discards 'const' qualifier from pointer target type [-Wdiscarded-qualifiers]
  503 |   if (jshPushIOCharEventsHandler(channel, data, count)) return;
      |                                           ^~~~
/home/simon/MaBecker/Espruino_IDF5_Gordon_validation/src/jsdevices.c:489:68: note: expected 'char *' but argument is of type 'const char *'
  489 | static bool jshPushIOCharEventsHandler(IOEventFlags channel, char *data, unsigned int count) {
      |                                                              ~~~~~~^~~~
[793/863] Building C object esp-idf/main/CMakeFiles/__idf_main.dir/home/simon/MaBecker/Espruino_IDF5_Gordon_validation/src/jsvar.c.obj
/home/simon/MaBecker/Espruino_IDF5_Gordon_validation/src/jsvar.c: In function 'jsvNewNativeString':
/home/simon/MaBecker/Espruino_IDF5_Gordon_validation/src/jsvar.c:1243:11: warning: comparison between pointer and integer
 1243 |   if (ptr >= FLASH_START && (ptr < FLASH_START+FLASH_TOTAL))
      |           ^~
/home/simon/MaBecker/Espruino_IDF5_Gordon_validation/src/jsvar.c:1243:34: warning: comparison between pointer and integer
 1243 |   if (ptr >= FLASH_START && (ptr < FLASH_START+FLASH_TOTAL))
      |                                  ^
/home/simon/MaBecker/Espruino_IDF5_Gordon_validation/src/jsvar.c: In function 'jsvNewFromStringVar':
/home/simon/MaBecker/Espruino_IDF5_Gordon_validation/src/jsvar.c:2037:50: warning: passing argument 1 of 'jsvNewFlatStringFromStringVar' discards 'const' qualifier from pointer target type [-Wdiscarded-qualifiers]
 2037 |       JsVar *var = jsvNewFlatStringFromStringVar(str, stridx, length);
      |                                                  ^~~
/home/simon/MaBecker/Espruino_IDF5_Gordon_validation/src/jsvar.c:1982:45: note: expected 'JsVar *' {aka 'struct JsVarStruct *'} but argument is of type 'const JsVar *' {aka 'const struct JsVarStruct *'}
 1982 | JsVar *jsvNewFlatStringFromStringVar(JsVar *var, size_t stridx, size_t maxLength) {
      |                                      ~~~~~~~^~~
[797/863] Building C object esp-idf/main/CMakeFiles/__idf_main.dir/home/simon/MaBecker/Espruino_IDF5_Gordon_validation/targets/esp32/jshardwareI2c.c.obj
FAILED: esp-idf/main/CMakeFiles/__idf_main.dir/home/simon/MaBecker/Espruino_IDF5_Gordon_validation/targets/esp32/jshardwareI2c.c.obj
/home/simon/.espressif/tools/xtensa-esp-elf/esp-14.2.0_20251107/xtensa-esp-elf/bin/xtensa-esp32-elf-gcc -DESP_MDNS_VERSION_NUMBER=\"1.11.3\" -DESP_PLATFORM -DIDF_VER=\"v5.5.3\" -DMBEDTLS_CONFIG_FILE=\"mbedtls/esp_config.h\" -DNDEBUG -DSOC_MMU_PAGE_SIZE=CONFIG_MMU_PAGE_SIZE -DSOC_XTAL_FREQ_MHZ=CONFIG_XTAL_FREQ -D_GLIBCXX_HAVE_POSIX_SEMAPHORE -D_GLIBCXX_USE_POSIX_SEMAPHORE -D_GNU_SOURCE -D_POSIX_READER_WRITER_LOCKS -I/home/simon/MaBecker/Espruino_IDF5_Gordon_validation/bin/build/config -I/home/simon/MaBecker/Espruino_IDF5_Gordon_validation -I/home/simon/MaBecker/Espruino_IDF5_Gordon_validation/targets -I/home/simon/MaBecker/Espruino_IDF5_Gordon_validation/src -I/home/simon/MaBecker/Espruino_IDF5_Gordon_validation/libs/compression -I/home/simon/MaBecker/Espruino_IDF5_Gordon_validation/libs/compression/heatshrink -I/home/simon/MaBecker/Espruino_IDF5_Gordon_validation/libs/graphics -I/home/simon/MaBecker/Espruino_IDF5_Gordon_validation/libs/network -I/home/simon/MaBecker/Espruino_IDF5_Gordon_validation/libs/network/http -I/home/simon/MaBecker/Espruino_IDF5_Gordon_validation/libs/network/js -I/home/simon/MaBecker/Espruino_IDF5_Gordon_validation/libs/network/esp32 -I/home/simon/MaBecker/Espruino_IDF5_Gordon_validation/libs/bluetooth -I/home/simon/MaBecker/Espruino_IDF5_Gordon_validation/libs/neopixel -I/home/simon/MaBecker/Espruino_IDF5_Gordon_validation/targets/esp32 -I/home/simon/MaBecker/Espruino_IDF5_Gordon_validation/gen -I/home/simon/MaBecker/Espruino_IDF5_Gordon_validation/esp-idf-5/esp-idf/components/newlib/platform_include -I/home/simon/MaBecker/Espruino_IDF5_Gordon_validation/esp-idf-5/esp-idf/components/freertos/config/include -I/home/simon/MaBecker/Espruino_IDF5_Gordon_validation/esp-idf-5/esp-idf/components/freertos/config/include/freertos -I/home/simon/MaBecker/Espruino_IDF5_Gordon_validation/esp-idf-5/esp-idf/components/freertos/config/xtensa/include -I/home/simon/MaBecker/Espruino_IDF5_Gordon_validation/esp-idf-5/esp-idf/components/freertos/FreeRTOS-Kernel/include -I/home/simon/MaBecker/Espruino_IDF5_Gordon_validation/esp-idf-5/esp-idf/components/freertos/FreeRTOS-Kernel/portable/xtensa/include -I/home/simon/MaBecker/Espruino_IDF5_Gordon_validation/esp-idf-5/esp-idf/components/freertos/FreeRTOS-Kernel/portable/xtensa/include/freertos -I/home/simon/MaBecker/Espruino_IDF5_Gordon_validation/esp-idf-5/esp-idf/components/freertos/esp_additions/include -I/home/simon/MaBecker/Espruino_IDF5_Gordon_validation/esp-idf-5/esp-idf/components/esp_hw_support/include -I/home/simon/MaBecker/Espruino_IDF5_Gordon_validation/esp-idf-5/esp-idf/components/esp_hw_support/include/soc -I/home/simon/MaBecker/Espruino_IDF5_Gordon_validation/esp-idf-5/esp-idf/components/esp_hw_support/include/soc/esp32 -I/home/simon/MaBecker/Espruino_IDF5_Gordon_validation/esp-idf-5/esp-idf/components/esp_hw_support/dma/include -I/home/simon/MaBecker/Espruino_IDF5_Gordon_validation/esp-idf-5/esp-idf/components/esp_hw_support/ldo/include -I/home/simon/MaBecker/Espruino_IDF5_Gordon_validation/esp-idf-5/esp-idf/components/esp_hw_support/debug_probe/include -I/home/simon/MaBecker/Espruino_IDF5_Gordon_validation/esp-idf-5/esp-idf/components/esp_hw_support/mspi_timing_tuning/include -I/home/simon/MaBecker/Espruino_IDF5_Gordon_validation/esp-idf-5/esp-idf/components/esp_hw_support/mspi_timing_tuning/tuning_scheme_impl/include -I/home/simon/MaBecker/Espruino_IDF5_Gordon_validation/esp-idf-5/esp-idf/components/esp_hw_support/power_supply/include -I/home/simon/MaBecker/Espruino_IDF5_Gordon_validation/esp-idf-5/esp-idf/components/esp_hw_support/port/esp32/. -I/home/simon/MaBecker/Espruino_IDF5_Gordon_validation/esp-idf-5/esp-idf/components/esp_hw_support/port/esp32/include -I/home/simon/MaBecker/Espruino_IDF5_Gordon_validation/esp-idf-5/esp-idf/components/heap/include -I/home/simon/MaBecker/Espruino_IDF5_Gordon_validation/esp-idf-5/esp-idf/components/heap/tlsf -I/home/simon/MaBecker/Espruino_IDF5_Gordon_validation/esp-idf-5/esp-idf/components/log/include -I/home/simon/MaBecker/Espruino_IDF5_Gordon_validation/esp-idf-5/esp-idf/components/soc/include -I/home/simon/MaBecker/Espruino_IDF5_Gordon_validation/esp-idf-5/esp-idf/components/soc/esp32 -I/home/simon/MaBecker/Espruino_IDF5_Gordon_validation/esp-idf-5/esp-idf/components/soc/esp32/include -I/home/simon/MaBecker/Espruino_IDF5_Gordon_validation/esp-idf-5/esp-idf/components/soc/esp32/register -I/home/simon/MaBecker/Espruino_IDF5_Gordon_validation/esp-idf-5/esp-idf/components/hal/platform_port/include -I/home/simon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
ation/esp-idf-5/esp-idf/components/bootloader_support/bootloader_flash/include -I/home/simon/MaBecker/Espruino_IDF5_Gordon_validation/esp-idf-5/esp-idf/components/esp_partition/include -I/home/simon/MaBecker/Espruino_IDF5_Gordon_validation/esp-idf-5/esp-idf/components/efuse/include -I/home/simon/MaBecker/Espruino_IDF5_Gordon_validation/esp-idf-5/esp-idf/components/efuse/esp32/include -I/home/simon/MaBecker/Espruino_IDF5_Gordon_validation/esp-idf-5/esp-idf/components/esp_mm/include -I/home/simon/MaBecker/Espruino_IDF5_Gordon_validation/esp-idf-5/esp-idf/components/spi_flash/include -I/home/simon/MaBecker/Espruino_IDF5_Gordon_validation/esp-idf-5/esp-idf/components/esp_security/include -I/home/simon/MaBecker/Espruino_IDF5_Gordon_validation/esp-idf-5/esp-idf/components/pthread/include -I/home/simon/MaBecker/Espruino_IDF5_Gordon_validation/esp-idf-5/esp-idf/components/esp_ringbuf/include -I/home/simon/MaBecker/Espruino_IDF5_Gordon_validation/esp-idf-5/esp-idf/components/esp_driver_spi/include -I/home/simon/MaBecker/Espruino_IDF5_Gordon_validation/esp-idf-5/esp-idf/components/esp_psram/include -I/home/simon/MaBecker/Espruino_IDF5_Gordon_validation/esp-idf-5/esp-idf/components/esp_driver_uart/include -I/home/simon/MaBecker/Espruino_IDF5_Gordon_validation/esp-idf-5/esp-idf/components/esp_driver_usb_serial_jtag/include -I/home/simon/MaBecker/Espruino_IDF5_Gordon_validation/esp-idf-5/esp-idf/components/nvs_flash/include -I/home/simon/MaBecker/Espruino_IDF5_Gordon_validation/esp-idf-5/esp-idf/components/esp_phy/include -I/home/simon/MaBecker/Espruino_IDF5_Gordon_validation/esp-idf-5/esp-idf/components/esp_phy/esp32/include -I/home/simon/MaBecker/Espruino_IDF5_Gordon_validation/esp-idf-5/esp-idf/components/wpa_supplicant/include -I/home/simon/MaBecker/Espruino_IDF5_Gordon_validation/esp-idf-5/esp-idf/components/wpa_supplicant/port/include -I/home/simon/MaBecker/Espruino_IDF5_Gordon_validation/esp-idf-5/esp-idf/components/wpa_supplicant/esp_supplicant/include -I/home/simon/MaBecker/Espruino_IDF5_Gordon_validation/esp-idf-5/esp-idf/components/esp_coex/include -I/home/simon/MaBecker/Espruino_IDF5_Gordon_validation/esp-idf-5/esp-idf/components/esp_wifi/include -I/home/simon/MaBecker/Espruino_IDF5_Gordon_validation/esp-idf-5/esp-idf/components/esp_wifi/include/local -I/home/simon/MaBecker/Espruino_IDF5_Gordon_validation/esp-idf-5/esp-idf/components/esp_wifi/wifi_apps/include -I/home/simon/MaBecker/Espruino_IDF5_Gordon_validation/esp-idf-5/esp-idf/components/esp_wifi/wifi_apps/nan_app/include -mlongcalls -Wno-frame-address  -fno-builtin-memcpy -fno-builtin-memset -fno-builtin-bzero -fno-builtin-stpcpy -fno-builtin-strncpy -fdiagnostics-color=always -ffunction-sections -fdata-sections -Wall -Werror=all -Wno-error=unused-function -Wno-error=unused-variable -Wno-error=unused-but-set-variable -Wno-error=deprecated-declarations -Wextra -Wno-error=extra -Wno-unused-parameter -Wno-sign-compare -Wno-enum-conversion -gdwarf-4 -ggdb -Os -freorder-blocks -fmacro-prefix-map=/home/simon/MaBecker/Espruino_IDF5_Gordon_validation/bin=. -fmacro-prefix-map=/home/simon/MaBecker/Espruino_IDF5_Gordon_validation/esp-idf-5/esp-idf=/IDF -fstrict-volatile-bitfields -fno-jump-tables -fno-tree-switch-conversion -std=gnu17 -Wno-old-style-declaration -DESP_IDF_VERSION_MAJOR=4 -DGIT_COMMIT=391070be2 -DNO_ASSERT -DRELEASE -DBUILDNUMBER=\"41\" -DESP32_IDF4 -DESP_PLATFORM -DESP32=1 -DESP_STACK_SIZE=25000 -DJSVAR_MALLOC -DUSE_FONT_6X8 -DUSE_DEBUGGER -DUSE_TAB_COMPLETE -DUSE_HEATSHRINK -DUSE_GRAPHICS -DUSE_NET -DUSE_NETWORK_JS -DUSE_ESP32 -DBLUETOOTH -DUSE_NEOPIXEL -DESP32 -DESPR_DEFINES_ON_COMMANDLINE -DEMBEDDED -Og -fno-strict-aliasing -fgnu89-inline -nostdlib -MMD -MP -Wno-enum-compare -Wno-pointer-sign -Wno-implicit-int -Wno-maybe-uninitialized -Wno-return-type -Wno-switch -Wno-unused-variable -Wno-unused-function -Wno-unused-but-set-variable -Wno-cast-function-type -Wno-format -MD -MT esp-idf/main/CMakeFiles/__idf_main.dir/home/simon/MaBecker/Espruino_IDF5_Gordon_validation/targets/esp32/jshardwareI2c.c.obj -MF esp-idf/main/CMakeFiles/__idf_main.dir/home/simon/MaBecker/Espruino_IDF5_Gordon_validation/targets/esp32/jshardwareI2c.c.obj.d -o esp-idf/main/CMakeFiles/__idf_main.dir/home/simon/MaBecker/Espruino_IDF5_Gordon_validation/targets/esp32/jshardwareI2c.c.obj -c /home/simon/MaBecker/Espruino_IDF5_Gordon_validation/targets/esp32/jshardwareI2c.c
/home/simon/MaBecker/Espruino_IDF5_Gordon_validation/targets/esp32/jshardwareI2c.c:20:10: fatal error: driver/i2c.h: No such file or directory
   20 | #include "driver/i2c.h"
      |          ^~~~~~~~~~~~~~
compilation terminated.
[800/863] Building C object esp-idf/main/CMakeFiles/__idf_main.dir/home/simon/MaBecker/Espruino_IDF5_Gordon_validation/targets/esp32/jshardwareUart.c.obj
FAILED: esp-idf/main/CMakeFiles/__idf_main.dir/home/simon/MaBecker/Espruino_IDF5_Gordon_validation/targets/esp32/jshardwareUart.c.obj
/home/simon/.espressif/tools/xtensa-esp-elf/esp-14.2.0_20251107/xtensa-esp-elf/bin/xtensa-esp32-elf-gcc -DESP_MDNS_VERSION_NUMBER=\"1.11.3\" -DESP_PLATFORM -DIDF_VER=\"v5.5.3\" -DMBEDTLS_CONFIG_FILE=\"mbedtls/esp_config.h\" -DNDEBUG -DSOC_MMU_PAGE_SIZE=CONFIG_MMU_PAGE_SIZE -DSOC_XTAL_FREQ_MHZ=CONFIG_XTAL_FREQ -D_GLIBCXX_HAVE_POSIX_SEMAPHORE -D_GLIBCXX_USE_POSIX_SEMAPHORE -D_GNU_SOURCE -D_POSIX_READER_WRITER_LOCKS -I/home/simon/MaBecker/Espruino_IDF5_Gordon_validation/bin/build/config -I/home/simon/MaBecker/Espruino_IDF5_Gordon_validation -I/home/simon/MaBecker/Espruino_IDF5_Gordon_validation/targets -I/home/simon/MaBecker/Espruino_IDF5_Gordon_validation/src -I/home/simon/MaBecker/Espruino_IDF5_Gordon_validation/libs/compression -I/home/simon/MaBecker/Espruino_IDF5_Gordon_validation/libs/compression/heatshrink -I/home/simon/MaBecker/Espruino_IDF5_Gordon_validation/libs/graphics -I/home/simon/MaBecker/Espruino_IDF5_Gordon_validation/libs/network -I/home/simon/MaBecker/Espruino_IDF5_Gordon_validation/libs/network/http -I/home/simon/MaBecker/Espruino_IDF5_Gordon_validation/libs/network/js -I/home/simon/MaBecker/Espruino_IDF5_Gordon_validation/libs/network/esp32 -I/home/simon/MaBecker/Espruino_IDF5_Gordon_validation/libs/bluetooth -I/home/simon/MaBecker/Espruino_IDF5_Gordon_validation/libs/neopixel -I/home/simon/MaBecker/Espruino_IDF5_Gordon_validation/targets/esp32 -I/home/simon/MaBecker/Espruino_IDF5_Gordon_validation/gen -I/home/simon/MaBecker/Espruino_IDF5_Gordon_validation/esp-idf-5/esp-idf/components/newlib/platform_include -I/home/simon/MaBecker/Espruino_IDF5_Gordon_validation/esp-idf-5/esp-idf/components/freertos/config/include -I/home/simon/MaBecker/Espruino_IDF5_Gordon_validation/esp-idf-5/esp-idf/components/freertos/config/include/freertos -I/home/simon/MaBecker/Espruino_IDF5_Gordon_validation/esp-idf-5/esp-idf/components/freertos/config/xtensa/include -I/home/simon/MaBecker/Espruino_IDF5_Gordon_validation/esp-idf-5/esp-idf/components/freertos/FreeRTOS-Kernel/include -I/home/simon/MaBecker/Espruino_IDF5_Gordon_validation/esp-idf-5/esp-idf/components/freertos/FreeRTOS-Kernel/portable/xtensa/include -I/home/simon/MaBecker/Espruino_IDF5_Gordon_validation/esp-idf-5/esp-idf/components/freertos/FreeRTOS-Kernel/portable/xtensa/include/freertos -I/home/simon/MaBecker/Espruino_IDF5_Gordon_validation/esp-idf-5/esp-idf/components/freertos/esp_additions/include -I/home/simon/MaBecker/Espruino_IDF5_Gordon_validation/esp-idf-5/esp-idf/components/esp_hw_support/include -I/home/simon/MaBecker/Espruino_IDF5_Gordon_validation/esp-idf-5/esp-idf/components/esp_hw_support/include/soc -I/home/simon/MaBecker/Espruino_IDF5_Gordon_validation/esp-idf-5/esp-idf/components/esp_hw_support/include/soc/esp32 -I/home/simon/MaBecker/Espruino_IDF5_Gordon_validation/esp-idf-5/esp-idf/components/esp_hw_support/dma/include -I/home/simon/MaBecker/Espruino_IDF5_Gordon_validation/esp-idf-5/esp-idf/components/esp_hw_support/ldo/include -I/home/simon/MaBecker/Espruino_IDF5_Gordon_validation/esp-idf-5/esp-idf/components/esp_hw_support/debug_probe/include -I/home/simon/MaBecker/Espruino_IDF5_Gordon_validation/esp-idf-5/esp-idf/components/esp_hw_support/mspi_timing_tuning/include -I/home/simon/MaBecker/Espruino_IDF5_Gordon_validation/esp-idf-5/esp-idf/components/esp_hw_support/mspi_timing_tuning/tuning_scheme_impl/include -I/home/simon/MaBecker/Espruino_IDF5_Gordon_validation/esp-idf-5/esp-idf/components/esp_hw_support/power_supply/include -I/home/simon/MaBecker/Espruino_IDF5_Gordon_validation/esp-idf-5/esp-idf/components/esp_hw_support/port/esp32/. -I/home/simon/MaBecker/Espruino_IDF5_Gordon_validation/esp-idf-5/esp-idf/components/esp_hw_support/port/esp32/include -I/home/simon/MaBecker/Espruino_IDF5_Gordon_validation/esp-idf-5/esp-idf/components/heap/include -I/home/simon/MaBecker/Espruino_IDF5_Gordon_validation/esp-idf-5/esp-idf/components/heap/tlsf -I/home/simon/MaBecker/Espruino_IDF5_Gordon_validation/esp-idf-5/esp-idf/components/log/include -I/home/simon/MaBecker/Espruino_IDF5_Gordon_validation/esp-idf-5/esp-idf/components/soc/include -I/home/simon/MaBecker/Espruino_IDF5_Gordon_validation/esp-idf-5/esp-idf/components/soc/esp32 -I/home/simon/MaBecker/Espruino_IDF5_Gordon_validation/esp-idf-5/esp-idf/components/soc/esp32/include -I/home/simon/MaBecker/Espruino_IDF5_Gordon_validation/esp-idf-5/esp-idf/components/soc/esp32/register -I/home/simon/MaBecker/Espruino_IDF5_Gordon_validation/esp-idf-5/esp-idf/components/hal/platform_port/include -I/home/simon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
ation/esp-idf-5/esp-idf/components/bootloader_support/bootloader_flash/include -I/home/simon/MaBecker/Espruino_IDF5_Gordon_validation/esp-idf-5/esp-idf/components/esp_partition/include -I/home/simon/MaBecker/Espruino_IDF5_Gordon_validation/esp-idf-5/esp-idf/components/efuse/include -I/home/simon/MaBecker/Espruino_IDF5_Gordon_validation/esp-idf-5/esp-idf/components/efuse/esp32/include -I/home/simon/MaBecker/Espruino_IDF5_Gordon_validation/esp-idf-5/esp-idf/components/esp_mm/include -I/home/simon/MaBecker/Espruino_IDF5_Gordon_validation/esp-idf-5/esp-idf/components/spi_flash/include -I/home/simon/MaBecker/Espruino_IDF5_Gordon_validation/esp-idf-5/esp-idf/components/esp_security/include -I/home/simon/MaBecker/Espruino_IDF5_Gordon_validation/esp-idf-5/esp-idf/components/pthread/include -I/home/simon/MaBecker/Espruino_IDF5_Gordon_validation/esp-idf-5/esp-idf/components/esp_ringbuf/include -I/home/simon/MaBecker/Espruino_IDF5_Gordon_validation/esp-idf-5/esp-idf/components/esp_driver_spi/include -I/home/simon/MaBecker/Espruino_IDF5_Gordon_validation/esp-idf-5/esp-idf/components/esp_psram/include -I/home/simon/MaBecker/Espruino_IDF5_Gordon_validation/esp-idf-5/esp-idf/components/esp_driver_uart/include -I/home/simon/MaBecker/Espruino_IDF5_Gordon_validation/esp-idf-5/esp-idf/components/esp_driver_usb_serial_jtag/include -I/home/simon/MaBecker/Espruino_IDF5_Gordon_validation/esp-idf-5/esp-idf/components/nvs_flash/include -I/home/simon/MaBecker/Espruino_IDF5_Gordon_validation/esp-idf-5/esp-idf/components/esp_phy/include -I/home/simon/MaBecker/Espruino_IDF5_Gordon_validation/esp-idf-5/esp-idf/components/esp_phy/esp32/include -I/home/simon/MaBecker/Espruino_IDF5_Gordon_validation/esp-idf-5/esp-idf/components/wpa_supplicant/include -I/home/simon/MaBecker/Espruino_IDF5_Gordon_validation/esp-idf-5/esp-idf/components/wpa_supplicant/port/include -I/home/simon/MaBecker/Espruino_IDF5_Gordon_validation/esp-idf-5/esp-idf/components/wpa_supplicant/esp_supplicant/include -I/home/simon/MaBecker/Espruino_IDF5_Gordon_validation/esp-idf-5/esp-idf/components/esp_coex/include -I/home/simon/MaBecker/Espruino_IDF5_Gordon_validation/esp-idf-5/esp-idf/components/esp_wifi/include -I/home/simon/MaBecker/Espruino_IDF5_Gordon_validation/esp-idf-5/esp-idf/components/esp_wifi/include/local -I/home/simon/MaBecker/Espruino_IDF5_Gordon_validation/esp-idf-5/esp-idf/components/esp_wifi/wifi_apps/include -I/home/simon/MaBecker/Espruino_IDF5_Gordon_validation/esp-idf-5/esp-idf/components/esp_wifi/wifi_apps/nan_app/include -mlongcalls -Wno-frame-address  -fno-builtin-memcpy -fno-builtin-memset -fno-builtin-bzero -fno-builtin-stpcpy -fno-builtin-strncpy -fdiagnostics-color=always -ffunction-sections -fdata-sections -Wall -Werror=all -Wno-error=unused-function -Wno-error=unused-variable -Wno-error=unused-but-set-variable -Wno-error=deprecated-declarations -Wextra -Wno-error=extra -Wno-unused-parameter -Wno-sign-compare -Wno-enum-conversion -gdwarf-4 -ggdb -Os -freorder-blocks -fmacro-prefix-map=/home/simon/MaBecker/Espruino_IDF5_Gordon_validation/bin=. -fmacro-prefix-map=/home/simon/MaBecker/Espruino_IDF5_Gordon_validation/esp-idf-5/esp-idf=/IDF -fstrict-volatile-bitfields -fno-jump-tables -fno-tree-switch-conversion -std=gnu17 -Wno-old-style-declaration -DESP_IDF_VERSION_MAJOR=4 -DGIT_COMMIT=391070be2 -DNO_ASSERT -DRELEASE -DBUILDNUMBER=\"41\" -DESP32_IDF4 -DESP_PLATFORM -DESP32=1 -DESP_STACK_SIZE=25000 -DJSVAR_MALLOC -DUSE_FONT_6X8 -DUSE_DEBUGGER -DUSE_TAB_COMPLETE -DUSE_HEATSHRINK -DUSE_GRAPHICS -DUSE_NET -DUSE_NETWORK_JS -DUSE_ESP32 -DBLUETOOTH -DUSE_NEOPIXEL -DESP32 -DESPR_DEFINES_ON_COMMANDLINE -DEMBEDDED -Og -fno-strict-aliasing -fgnu89-inline -nostdlib -MMD -MP -Wno-enum-compare -Wno-pointer-sign -Wno-implicit-int -Wno-maybe-uninitialized -Wno-return-type -Wno-switch -Wno-unused-variable -Wno-unused-function -Wno-unused-but-set-variable -Wno-cast-function-type -Wno-format -MD -MT esp-idf/main/CMakeFiles/__idf_main.dir/home/simon/MaBecker/Espruino_IDF5_Gordon_validation/targets/esp32/jshardwareUart.c.obj -MF esp-idf/main/CMakeFiles/__idf_main.dir/home/simon/MaBecker/Espruino_IDF5_Gordon_validation/targets/esp32/jshardwareUart.c.obj.d -o esp-idf/main/CMakeFiles/__idf_main.dir/home/simon/MaBecker/Espruino_IDF5_Gordon_validation/targets/esp32/jshardwareUart.c.obj -c /home/simon/MaBecker/Espruino_IDF5_Gordon_validation/targets/esp32/jshardwareUart.c
In file included from /home/simon/MaBecker/Espruino_IDF5_Gordon_validation/esp-idf-5/esp-idf/components/esp_system/include/esp_system.h:15,
                 from /home/simon/MaBecker/Espruino_IDF5_Gordon_validation/esp-idf-5/esp-idf/components/freertos/FreeRTOS-Kernel/portable/xtensa/include/freertos/portmacro.h:58,
                 from /home/simon/MaBecker/Espruino_IDF5_Gordon_validation/esp-idf-5/esp-idf/components/freertos/FreeRTOS-Kernel/include/freertos/portable.h:57,
                 from /home/simon/MaBecker/Espruino_IDF5_Gordon_validation/esp-idf-5/esp-idf/components/freertos/FreeRTOS-Kernel/include/freertos/FreeRTOS.h:69,
                 from /home/simon/MaBecker/Espruino_IDF5_Gordon_validation/esp-idf-5/esp-idf/components/esp_driver_uart/include/driver/uart.h:12,
                 from /home/simon/MaBecker/Espruino_IDF5_Gordon_validation/targets/esp32/jshardwareUart.c:19:
/home/simon/MaBecker/Espruino_IDF5_Gordon_validation/esp-idf-5/esp-idf/components/esp_common/include/esp_idf_version.h:14:9: warning: "ESP_IDF_VERSION_MAJOR" redefined
   14 | #define ESP_IDF_VERSION_MAJOR   5
      |         ^~~~~~~~~~~~~~~~~~~~~
<command-line>: note: this is the location of the previous definition
In file included from /home/simon/MaBecker/Espruino_IDF5_Gordon_validation/targets/esp32/jshardwareUart.c:30:
/home/simon/MaBecker/Espruino_IDF5_Gordon_validation/targets/esp32/BLE/esp32_gatts_func.h:17:10: fatal error: esp_gatts_api.h: No such file or directory
   17 | #include "esp_gatts_api.h"
      |          ^~~~~~~~~~~~~~~~~
compilation terminated.
[801/863] Building C object esp-idf/main/CMakeFiles/__idf_main.dir/home/simon/MaBecker/Espruino_IDF5_Gordon_validation/libs/network/esp32/network_esp32.c.obj
In file included from /home/simon/MaBecker/Espruino_IDF5_Gordon_validation/esp-idf-5/esp-idf/components/esp_system/include/esp_system.h:15,
                 from /home/simon/MaBecker/Espruino_IDF5_Gordon_validation/esp-idf-5/esp-idf/components/freertos/FreeRTOS-Kernel/portable/xtensa/include/freertos/portmacro.h:58,
                 from /home/simon/MaBecker/Espruino_IDF5_Gordon_validation/esp-idf-5/esp-idf/components/freertos/FreeRTOS-Kernel/include/freertos/portable.h:57,
                 from /home/simon/MaBecker/Espruino_IDF5_Gordon_validation/esp-idf-5/esp-idf/components/freertos/FreeRTOS-Kernel/include/freertos/FreeRTOS.h:69,
                 from /home/simon/MaBecker/Espruino_IDF5_Gordon_validation/esp-idf-5/esp-idf/components/esp_system/include/esp_task.h:24,
                 from /home/simon/MaBecker/Espruino_IDF5_Gordon_validation/esp-idf-5/esp-idf/components/lwip/port/include/lwipopts.h:20,
                 from /home/simon/MaBecker/Espruino_IDF5_Gordon_validation/esp-idf-5/esp-idf/components/lwip/lwip/src/include/lwip/opt.h:51,
                 from /home/simon/MaBecker/Espruino_IDF5_Gordon_validation/esp-idf-5/esp-idf/components/lwip/lwip/src/include/lwip/sockets.h:42,
                 from /home/simon/MaBecker/Espruino_IDF5_Gordon_validation/esp-idf-5/esp-idf/components/lwip/include/lwip/sockets.h:8,
                 from /home/simon/MaBecker/Espruino_IDF5_Gordon_validation/esp-idf-5/esp-idf/components/lwip/port/esp32xx/include/sys/socket.h:15,
                 from /home/simon/MaBecker/Espruino_IDF5_Gordon_validation/libs/network/esp32/network_esp32.c:35:
/home/simon/MaBecker/Espruino_IDF5_Gordon_validation/esp-idf-5/esp-idf/components/esp_common/include/esp_idf_version.h:14:9: warning: "ESP_IDF_VERSION_MAJOR" redefined
   14 | #define ESP_IDF_VERSION_MAJOR   5
      |         ^~~~~~~~~~~~~~~~~~~~~
<command-line>: note: this is the location of the previous definition
[802/863] Building C object esp-idf/main/CMakeFiles/__idf_main.dir/home/simon/MaBecker/Espruino_IDF5_Gordon_validation/targets/esp32/jshardwareSpi.c.obj
In file included from /home/simon/MaBecker/Espruino_IDF5_Gordon_validation/esp-idf-5/esp-idf/components/esp_system/include/esp_system.h:15,
                 from /home/simon/MaBecker/Espruino_IDF5_Gordon_validation/esp-idf-5/esp-idf/components/freertos/FreeRTOS-Kernel/portable/xtensa/include/freertos/portmacro.h:58,
                 from /home/simon/MaBecker/Espruino_IDF5_Gordon_validation/esp-idf-5/esp-idf/components/freertos/FreeRTOS-Kernel/include/freertos/portable.h:57,
                 from /home/simon/MaBecker/Espruino_IDF5_Gordon_validation/esp-idf-5/esp-idf/components/freertos/FreeRTOS-Kernel/include/freertos/FreeRTOS.h:69,
                 from /home/simon/MaBecker/Espruino_IDF5_Gordon_validation/esp-idf-5/esp-idf/components/esp_driver_spi/include/driver/spi_master.h:10,
                 from /home/simon/MaBecker/Espruino_IDF5_Gordon_validation/targets/esp32/jshardwareSpi.h:21,
                 from /home/simon/MaBecker/Espruino_IDF5_Gordon_validation/targets/esp32/jshardwareSpi.c:34:
/home/simon/MaBecker/Espruino_IDF5_Gordon_validation/esp-idf-5/esp-idf/components/esp_common/include/esp_idf_version.h:14:9: warning: "ESP_IDF_VERSION_MAJOR" redefined
   14 | #define ESP_IDF_VERSION_MAJOR   5
      |         ^~~~~~~~~~~~~~~~~~~~~
<command-line>: note: this is the location of the previous definition
/home/simon/MaBecker/Espruino_IDF5_Gordon_validation/targets/esp32/jshardwareSpi.c: In function 'jshSPISendMany':
/home/simon/MaBecker/Espruino_IDF5_Gordon_validation/targets/esp32/jshardwareSpi.c:197:12: warning: passing argument 1 of 'memset' discards 'volatile' qualifier from pointer target type [-Wdiscarded-qualifiers]
  197 |     memset(&spi_trans, 0, sizeof(spi_trans));
      |            ^~~~~~~~~~
In file included from /home/simon/MaBecker/Espruino_IDF5_Gordon_validation/src/jsutils.h:22,
                 from /home/simon/MaBecker/Espruino_IDF5_Gordon_validation/src/jspin.h:21,
                 from /home/simon/MaBecker/Espruino_IDF5_Gordon_validation/gen/jspininfo.h:7,
                 from /home/simon/MaBecker/Espruino_IDF5_Gordon_validation/targets/esp32/jshardwareSpi.c:31:
/home/simon/.espressif/tools/xtensa-esp-elf/esp-14.2.0_20251107/xtensa-esp-elf/xtensa-esp-elf/include/string.h:33:18: note: expected 'void *' but argument is of type 'volatile spi_transaction_t *'
   33 | void *   memset (void *, int, size_t);
      |                  ^~~~~~
/home/simon/MaBecker/Espruino_IDF5_Gordon_validation/targets/esp32/jshardwareSpi.c:201:54: warning: passing argument 2 of 'spi_device_transmit' discards 'volatile' qualifier from pointer target type [-Wdiscarded-qualifiers]
  201 |     spi_device_transmit(SPIChannels[channelPnt].spi, &spi_trans); // blocking
      |                                                      ^~~~~~~~~~
/home/simon/MaBecker/Espruino_IDF5_Gordon_validation/esp-idf-5/esp-idf/components/esp_driver_spi/include/driver/spi_master.h:268:78: note: expected 'spi_transaction_t *' but argument is of type 'volatile spi_transaction_t *'
  268 | esp_err_t spi_device_transmit(spi_device_handle_t handle, spi_transaction_t *trans_desc);
      |                                                           ~~~~~~~~~~~~~~~~~~~^~~~~~~~~~
ninja: build stopped: subcommand failed.
ninja failed with exit code 1, output of the command is in the /home/simon/MaBecker/Espruino_IDF5_Gordon_validation/bin/build/log/idf_py_stderr_output_110063 and /home/simon/MaBecker/Espruino_IDF5_Gordon_validation/bin/build/log/idf_py_stdout_output_110063
make: *** [make/targets/ESP32_IDF5.make:92: bin/espruino_2v29.41_esp32.bin] Error 2
simon@OptiPlex3050:~/MaBecker/Espruino_IDF5_Gordon_validation$
