SimonGAndrews/ESP32_SGATest/docs/investigations/IDF5_port_testing/IDF4_build/ESP32_GW_baseline_ESP32_IDF4_build_error_01.txt

[66/100] Building C object esp-idf/esp_hw_support/CMakeFiles/__idf_esp_hw_support.dir/port/esp32/rtc_init.c.obj
[67/100] Building C object esp-idf/esp_hw_support/CMakeFiles/__idf_esp_hw_support.dir/port/esp32/rtc_time.c.obj
[68/100] Building C object esp-idf/esp_hw_support/CMakeFiles/__idf_esp_hw_support.dir/port/esp32/chip_info.c.obj
[69/100] Building C object esp-idf/esp_hw_support/CMakeFiles/__idf_esp_hw_support.dir/port/esp32/rtc_sleep.c.obj
[70/100] Building C object esp-idf/xtensa/CMakeFiles/__idf_xtensa.dir/eri.c.obj
[71/100] Building C object esp-idf/esp_rom/CMakeFiles/__idf_esp_rom.dir/patches/esp_rom_crc.c.obj
[72/100] Building C object esp-idf/xtensa/CMakeFiles/__idf_xtensa.dir/xt_trax.c.obj
[73/100] Building C object esp-idf/esp_hw_support/CMakeFiles/__idf_esp_hw_support.dir/port/esp32/rtc_wdt.c.obj
[74/100] Building C object esp-idf/esp_rom/CMakeFiles/__idf_esp_rom.dir/patches/esp_rom_sys.c.obj
[75/100] Building C object esp-idf/esp_rom/CMakeFiles/__idf_esp_rom.dir/patches/esp_rom_tjpgd.c.obj
[76/100] Building ASM object esp-idf/esp_rom/CMakeFiles/__idf_esp_rom.dir/patches/esp_rom_longjmp.S.obj
[77/100] Building C object esp-idf/esp_hw_support/CMakeFiles/__idf_esp_hw_support.dir/port/esp32/rtc_clk.c.obj
[78/100] Building C object esp-idf/esp_rom/CMakeFiles/__idf_esp_rom.dir/patches/esp_rom_efuse.c.obj
[79/100] Building C object esp-idf/esp_common/CMakeFiles/__idf_esp_common.dir/src/esp_err_to_name.c.obj
[80/100] Building C object esp-idf/esp_rom/CMakeFiles/__idf_esp_rom.dir/patches/esp_rom_uart.c.obj
[81/100] Building C object esp-idf/log/CMakeFiles/__idf_log.dir/log_noos.c.obj
[82/100] Building C object esp-idf/log/CMakeFiles/__idf_log.dir/log_buffers.c.obj
[83/100] Building C object esp-idf/main/CMakeFiles/__idf_main.dir/bootloader_start.c.obj
[84/100] Building C object esp-idf/log/CMakeFiles/__idf_log.dir/log.c.obj
[85/100] Linking C static library esp-idf/log/liblog.a
[86/100] Linking C static library esp-idf/esp_rom/libesp_rom.a
[87/100] Linking C static library esp-idf/esp_common/libesp_common.a
[88/100] Linking C static library esp-idf/xtensa/libxtensa.a
[89/100] Linking C static library esp-idf/esp_hw_support/libesp_hw_support.a
[90/100] Linking C static library esp-idf/esp_system/libesp_system.a
[91/100] Linking C static library esp-idf/efuse/libefuse.a
[92/100] Linking C static library esp-idf/bootloader_support/libbootloader_support.a
[93/100] Linking C static library esp-idf/spi_flash/libspi_flash.a
[94/100] Linking C static library esp-idf/micro-ecc/libmicro-ecc.a
[95/100] Linking C static library esp-idf/soc/libsoc.a
[96/100] Linking C static library esp-idf/hal/libhal.a
[97/100] Linking C static library esp-idf/main/libmain.a
[98/100] Linking C executable bootloader.elf
[99/100] Generating binary image from built executable
esptool.py v3.3.4-dev
Creating esp32 image...
Merged 1 ELF section
Successfully created esp32 image.
Generated /home/simon/MaBecker/Espruino_IDF5_MaBecker_baseline/bin/build/bootloader/bootloader.bin
[100/100] cd /home/simon/MaBecker/Espruino_IDF5_MaBecker_baseline/bin/build/bootloader/esp-idf/esptool_py && /home/simon/.espressif/python_env/idf4.4_py3.12_env/bin/python /home/simon/MaBecker/Espruino_IDF5_MaBecker_baseline/esp-idf-4/esp-idf/components/partition_table/check_sizes.py --offset 0x8000 bootloader 0x1000 /home/simon/MaBecker/Espruino_IDF5_MaBecker_baseline/bin/build/bootloader/bootloader.bin
Bootloader binary size 0x5e10 bytes. 0x11f0 bytes (16%) free.
[1349/1437] Building C object esp-idf/main/CMakeFiles/__idf_main.dir/home/simon/MaBecker/Espruino_IDF5_MaBecker_baseline/gen/jswrapper.c.obj
FAILED: esp-idf/main/CMakeFiles/__idf_main.dir/home/simon/MaBecker/Espruino_IDF5_MaBecker_baseline/gen/jswrapper.c.obj
/home/simon/.espressif/tools/xtensa-esp32-elf/esp-2021r2-patch5-8.4.0/xtensa-esp32-elf/bin/xtensa-esp32-elf-gcc -DHAVE_CONFIG_H -DMBEDTLS_CONFIG_FILE=\"mbedtls/esp_config.h\" -DUNITY_INCLUDE_CONFIG_H -DWITH_POSIX -I/home/simon/MaBecker/Espruino_IDF5_MaBecker_baseline/bin/build/config -I/home/simon/M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
nts/bt/common/api/include/api -I/home/simon/MaBecker/Espruino_IDF5_MaBecker_baseline/esp-idf-4/esp-idf/components/bt/common/btc/profile/esp/blufi/include -I/home/simon/MaBecker/Espruino_IDF5_MaBecker_baseline/esp-idf-4/esp-idf/components/bt/common/btc/profile/esp/include -I/home/simon/MaBecker/Espruino_IDF5_MaBecker_baseline/esp-idf-4/esp-idf/components/bt/common/hci_log/include -I/home/simon/MaBecker/Espruino_IDF5_MaBecker_baseline/esp-idf-4/esp-idf/components/bt/host/bluedroid/api/include/api -I/home/simon/MaBecker/Espruino_IDF5_MaBecker_baseline/esp-idf-4/esp-idf/components/cbor/port/include -I/home/simon/MaBecker/Espruino_IDF5_MaBecker_baseline/esp-idf-4/esp-idf/components/unity/include -I/home/simon/MaBecker/Espruino_IDF5_MaBecker_baseline/esp-idf-4/esp-idf/components/unity/unity/src -I/home/simon/MaBecker/Espruino_IDF5_MaBecker_baseline/esp-idf-4/esp-idf/components/cmock/CMock/src -I/home/simon/MaBecker/Espruino_IDF5_MaBecker_baseline/esp-idf-4/esp-idf/components/coap/port/include -I/home/simon/MaBecker/Espruino_IDF5_MaBecker_baseline/esp-idf-4/esp-idf/components/coap/libcoap/include -I/home/simon/MaBecker/Espruino_IDF5_MaBecker_baseline/esp-idf-4/esp-idf/components/nghttp/port/include -I/home/simon/MaBecker/Espruino_IDF5_MaBecker_baseline/esp-idf-4/esp-idf/components/nghttp/nghttp2/lib/includes -I/home/simon/MaBecker/Espruino_IDF5_MaBecker_baseline/esp-idf-4/esp-idf/components/esp-tls -I/home/simon/MaBecker/Espruino_IDF5_MaBecker_baseline/esp-idf-4/esp-idf/components/esp-tls/esp-tls-crypto -I/home/simon/MaBecker/Espruino_IDF5_MaBecker_baseline/esp-idf-4/esp-idf/components/esp_adc_cal/include -I/home/simon/MaBecker/Espruino_IDF5_MaBecker_baseline/esp-idf-4/esp-idf/components/esp_hid/include -I/home/simon/MaBecker/Espruino_IDF5_MaBecker_baseline/esp-idf-4/esp-idf/components/tcp_transport/include -I/home/simon/MaBecker/Espruino_IDF5_MaBecker_baseline/esp-idf-4/esp-idf/components/esp_http_client/include -I/home/simon/MaBecker/Espruino_IDF5_MaBecker_baseline/esp-idf-4/esp-idf/components/esp_http_server/include -I/home/simon/MaBecker/Espruino_IDF5_MaBecker_baseline/esp-idf-4/esp-idf/components/esp_https_ota/include -I/home/simon/MaBecker/Espruino_IDF5_MaBecker_baseline/esp-idf-4/esp-idf/components/esp_lcd/include -I/home/simon/MaBecker/Espruino_IDF5_MaBecker_baseline/esp-idf-4/esp-idf/components/esp_lcd/interface -I/home/simon/MaBecker/Espruino_IDF5_MaBecker_baseline/esp-idf-4/esp-idf/components/protobuf-c/protobuf-c -I/home/simon/MaBecker/Espruino_IDF5_MaBecker_baseline/esp-idf-4/esp-idf/components/protocomm/include/common -I/home/simon/MaBecker/Espruino_IDF5_MaBecker_baseline/esp-idf-4/esp-idf/components/protocomm/include/security -I/home/simon/MaBecker/Espruino_IDF5_MaBecker_baseline/esp-idf-4/esp-idf/components/protocomm/include/transports -I/home/simon/MaBecker/Espruino_IDF5_MaBecker_baseline/esp-idf-4/esp-idf/components/mdns/include -I/home/simon/MaBecker/Espruino_IDF5_MaBecker_baseline/esp-idf-4/esp-idf/components/esp_local_ctrl/include -I/home/simon/MaBecker/Espruino_IDF5_MaBecker_baseline/esp-idf-4/esp-idf/components/sdmmc/include -I/home/simon/MaBecker/Espruino_IDF5_MaBecker_baseline/esp-idf-4/esp-idf/components/esp_serial_slave_link/include -I/home/simon/MaBecker/Espruino_IDF5_MaBecker_baseline/esp-idf-4/esp-idf/components/esp_websocket_client/include -I/home/simon/MaBecker/Espruino_IDF5_MaBecker_baseline/esp-idf-4/esp-idf/components/expat/expat/expat/lib -I/home/simon/MaBecker/Espruino_IDF5_MaBecker_baseline/esp-idf-4/esp-idf/components/expat/port/include -I/home/simon/MaBecker/Espruino_IDF5_MaBecker_baseline/esp-idf-4/esp-idf/components/wear_levelling/include -I/home/simon/MaBecker/Espruino_IDF5_MaBecker_baseline/esp-idf-4/esp-idf/components/fatfs/diskio -I/home/simon/MaBecker/Espruino_IDF5_MaBecker_baseline/esp-idf-4/esp-idf/components/fatfs/vfs -I/home/simon/MaBecker/Espruino_IDF5_MaBecker_baseline/esp-idf-4/esp-idf/components/fatfs/src -I/home/simon/MaBecker/Espruino_IDF5_MaBecker_baseline/esp-idf-4/esp-idf/components/freemodbus/freemodbus/common/include -I/home/simon/MaBecker/Espruino_IDF5_MaBecker_baseline/esp-idf-4/esp-idf/components/idf_test/include -I/home/simon/MaBecker/Espruino_IDF5_MaBecker_baseline/esp-idf-4/esp-idf/components/idf_test/include/esp32 -I/home/simon/MaBecker/Espruino_IDF5_MaBecker_baseline/esp-idf-4/esp-idf/components/jsmn/include -I/home/simon/MaBecker/Espruino_IDF5_MaBecker_baseline/esp-idf-4/esp-idf/components/json/cJSON -I/home/simon/MaBecker/Espruino_IDF5_MaBecker_baseline/esp-idf-4/esp-idf/components/libsodium/libsodium/src/libsodium/include -I/home/simon/MaBecker/Espruino_IDF5_MaBecker_baseline/esp-idf-4/esp-idf/components/libsodium/port_include -I/home/simon/MaBecker/Espruino_IDF5_MaBecker_baseline/esp-idf-4/esp-idf/components/mqtt/esp-mqtt/include -I/home/simon/MaBecker/Espruino_IDF5_MaBecker_baseline/esp-idf-4/esp-idf/components/openssl/include -I/home/simon/MaBecker/Espruino_IDF5_MaBecker_baseline/esp-idf-4/esp-idf/components/perfmon/include -I/home/simon/MaBecker/Espruino_IDF5_MaBecker_baseline/esp-idf-4/esp-idf/components/spiffs/include -I/home/simon/MaBecker/Espruino_IDF5_MaBecker_baseline/esp-idf-4/esp-idf/components/ulp/include -I/home/simon/MaBecker/Espruino_IDF5_MaBecker_baseline/esp-idf-4/esp-idf/components/wifi_provisioning/include -mlongcalls -Wno-frame-address  -ffunction-sections -fdata-sections -Wall -Werror=all -Wno-error=unused-function -Wno-error=unused-variable -Wno-error=deprecated-declarations -Wextra -Wno-unused-parameter -Wno-sign-compare -ggdb -Os -freorder-blocks -fmacro-prefix-map=/home/simon/MaBecker/Espruino_IDF5_MaBecker_baseline/bin=. -fmacro-prefix-map=/home/simon/MaBecker/Espruino_IDF5_MaBecker_baseline/esp-idf-4/esp-idf=IDF -fstrict-volatile-bitfields -Wno-error=unused-but-set-variable -fno-jump-tables -fno-tree-switch-conversion -std=gnu99 -Wno-old-style-declaration -D_GNU_SOURCE -DIDF_VER=\"v4.4.8\" -DESP_PLATFORM -DNDEBUG -D_POSIX_READER_WRITER_LOCKS -DESP_IDF_VERSION_MAJOR=4 -DGIT_COMMIT=ca6b3592c -DNO_ASSERT -DRELEASE -DESP32_IDF4 -DESP32=1 -DESP_STACK_SIZE=25000 -DJSVAR_MALLOC -DUSE_FONT_6X8 -DUSE_DEBUGGER -DUSE_TAB_COMPLETE -DUSE_HEATSHRINK -DUSE_GRAPHICS -DUSE_NET -DUSE_NETWORK_JS -DUSE_ESP32 -DBLUETOOTH -DUSE_NEOPIXEL -DESP32 -DESPR_DEFINES_ON_COMMANDLINE -DEMBEDDED -Og -fno-strict-aliasing -fgnu89-inline -nostdlib -MMD -MP -Wno-enum-compare -Wno-pointer-sign -Wno-implicit-int -Wno-maybe-uninitialized -Wno-return-type -Wno-switch -Wno-unused-variable -Wno-unused-function -Wno-unused-but-set-variable -Wno-cast-function-type -Wno-format -MD -MT esp-idf/main/CMakeFiles/__idf_main.dir/home/simon/MaBecker/Espruino_IDF5_MaBecker_baseline/gen/jswrapper.c.obj -MF esp-idf/main/CMakeFiles/__idf_main.dir/home/simon/MaBecker/Espruino_IDF5_MaBecker_baseline/gen/jswrapper.c.obj.d -o esp-idf/main/CMakeFiles/__idf_main.dir/home/simon/MaBecker/Espruino_IDF5_MaBecker_baseline/gen/jswrapper.c.obj -c /home/simon/MaBecker/Espruino_IDF5_MaBecker_baseline/gen/jswrapper.c
In file included from /home/simon/MaBecker/Espruino_IDF5_MaBecker_baseline/gen/jswrapper.c:4:
/home/simon/MaBecker/Espruino_IDF5_MaBecker_baseline/gen/jswrapper.c:1634:144: error: 'jswrap_crypto_PBKDF2' undeclared here (not in a function); did you mean 'jswrap_crypto_SHAx'?
   JSWSYMPTR_ENTRY(4, JSWAT_JSVAR | (JSWAT_JSVAR << (JSWAT_BITS*1)) | (JSWAT_JSVAR << (JSWAT_BITS*2)) | (JSWAT_JSVAR << (JSWAT_BITS*3)), (void*)jswrap_crypto_PBKDF2),
                                                                                                                                                ^~~~~~~~~~~~~~~~~~~~
/home/simon/MaBecker/Espruino_IDF5_MaBecker_baseline/src/jswrapper.h:85:22: note: in definition of macro 'JSWSYMPTR_ENTRY'
   { offset, argSpec, pointer}
                      ^~~~~~~
/home/simon/MaBecker/Espruino_IDF5_MaBecker_baseline/gen/jswrapper.c:1634:3: warning: missing initializer for field 'functionPtr' of 'JswSymPtr' {aka 'const struct <anonymous>'} [-Wmissing-field-initializers]
   JSWSYMPTR_ENTRY(4, JSWAT_JSVAR | (JSWAT_JSVAR << (JSWAT_BITS*1)) | (JSWAT_JSVAR << (JSWAT_BITS*2)) | (JSWAT_JSVAR << (JSWAT_BITS*3)), (void*)jswrap_crypto_PBKDF2),
   ^~~~~~~~~~~~~~~
In file included from /home/simon/MaBecker/Espruino_IDF5_MaBecker_baseline/gen/jswrapper.c:4:
/home/simon/MaBecker/Espruino_IDF5_MaBecker_baseline/src/jswrapper.h:81:10: note: 'functionPtr' declared here
   void (*functionPtr)(void);
          ^~~~~~~~~~~
/home/simon/MaBecker/Espruino_IDF5_MaBecker_baseline/gen/jswrapper.c:1643:144: error: 'jswrap_crypto_AES_decrypt' undeclared here (not in a function); did you mean 'jswrap_crypto_SHAx'?
   JSWSYMPTR_ENTRY(0, JSWAT_JSVAR | (JSWAT_JSVAR << (JSWAT_BITS*1)) | (JSWAT_JSVAR << (JSWAT_BITS*2)) | (JSWAT_JSVAR << (JSWAT_BITS*3)), (void*)jswrap_crypto_AES_decrypt),
                                                                                                                                                ^~~~~~~~~~~~~~~~~~~~~~~~~
/home/simon/MaBecker/Espruino_IDF5_MaBecker_baseline/src/jswrapper.h:85:22: note: in definition of macro 'JSWSYMPTR_ENTRY'
   { offset, argSpec, pointer}
                      ^~~~~~~
/home/simon/MaBecker/Espruino_IDF5_MaBecker_baseline/gen/jswrapper.c:1643:137: error: initializer element is not constant
   JSWSYMPTR_ENTRY(0, JSWAT_JSVAR | (JSWAT_JSVAR << (JSWAT_BITS*1)) | (JSWAT_JSVAR << (JSWAT_BITS*2)) | (JSWAT_JSVAR << (JSWAT_BITS*3)), (void*)jswrap_crypto_AES_decrypt),
                                                                                                                                         ^
/home/simon/MaBecker/Espruino_IDF5_MaBecker_baseline/src/jswrapper.h:85:22: note: in definition of macro 'JSWSYMPTR_ENTRY'
   { offset, argSpec, pointer}
                      ^~~~~~~
/home/simon/MaBecker/Espruino_IDF5_MaBecker_baseline/gen/jswrapper.c:1643:137: note: (near initialization for 'jswSymbols_AES[0].functionPtr')
   JSWSYMPTR_ENTRY(0, JSWAT_JSVAR | (JSWAT_JSVAR << (JSWAT_BITS*1)) | (JSWAT_JSVAR << (JSWAT_BITS*2)) | (JSWAT_JSVAR << (JSWAT_BITS*3)), (void*)jswrap_crypto_AES_decrypt),
                                                                                                                                         ^
/home/simon/MaBecker/Espruino_IDF5_MaBecker_baseline/src/jswrapper.h:85:22: note: in definition of macro 'JSWSYMPTR_ENTRY'
   { offset, argSpec, pointer}
                      ^~~~~~~
/home/simon/MaBecker/Espruino_IDF5_MaBecker_baseline/gen/jswrapper.c:1643:3: warning: missing initializer for field 'functionPtr' of 'JswSymPtr' {aka 'const struct <anonymous>'} [-Wmissing-field-initializers]
   JSWSYMPTR_ENTRY(0, JSWAT_JSVAR | (JSWAT_JSVAR << (JSWAT_BITS*1)) | (JSWAT_JSVAR << (JSWAT_BITS*2)) | (JSWAT_JSVAR << (JSWAT_BITS*3)), (void*)jswrap_crypto_AES_decrypt),
   ^~~~~~~~~~~~~~~
In file included from /home/simon/MaBecker/Espruino_IDF5_MaBecker_baseline/gen/jswrapper.c:4:
/home/simon/MaBecker/Espruino_IDF5_MaBecker_baseline/src/jswrapper.h:81:10: note: 'functionPtr' declared here
   void (*functionPtr)(void);
          ^~~~~~~~~~~
/home/simon/MaBecker/Espruino_IDF5_MaBecker_baseline/gen/jswrapper.c:1644:144: error: 'jswrap_crypto_AES_encrypt' undeclared here (not in a function); did you mean 'jswrap_crypto_SHAx'?
   JSWSYMPTR_ENTRY(8, JSWAT_JSVAR | (JSWAT_JSVAR << (JSWAT_BITS*1)) | (JSWAT_JSVAR << (JSWAT_BITS*2)) | (JSWAT_JSVAR << (JSWAT_BITS*3)), (void*)jswrap_crypto_AES_encrypt)
                                                                                                                                                ^~~~~~~~~~~~~~~~~~~~~~~~~
/home/simon/MaBecker/Espruino_IDF5_MaBecker_baseline/src/jswrapper.h:85:22: note: in definition of macro 'JSWSYMPTR_ENTRY'
   { offset, argSpec, pointer}
                      ^~~~~~~
/home/simon/MaBecker/Espruino_IDF5_MaBecker_baseline/gen/jswrapper.c:1644:137: error: initializer element is not constant
   JSWSYMPTR_ENTRY(8, JSWAT_JSVAR | (JSWAT_JSVAR << (JSWAT_BITS*1)) | (JSWAT_JSVAR << (JSWAT_BITS*2)) | (JSWAT_JSVAR << (JSWAT_BITS*3)), (void*)jswrap_crypto_AES_encrypt)
                                                                                                                                         ^
/home/simon/MaBecker/Espruino_IDF5_MaBecker_baseline/src/jswrapper.h:85:22: note: in definition of macro 'JSWSYMPTR_ENTRY'
   { offset, argSpec, pointer}
                      ^~~~~~~
/home/simon/MaBecker/Espruino_IDF5_MaBecker_baseline/gen/jswrapper.c:1644:137: note: (near initialization for 'jswSymbols_AES[1].functionPtr')
   JSWSYMPTR_ENTRY(8, JSWAT_JSVAR | (JSWAT_JSVAR << (JSWAT_BITS*1)) | (JSWAT_JSVAR << (JSWAT_BITS*2)) | (JSWAT_JSVAR << (JSWAT_BITS*3)), (void*)jswrap_crypto_AES_encrypt)
                                                                                                                                         ^
/home/simon/MaBecker/Espruino_IDF5_MaBecker_baseline/src/jswrapper.h:85:22: note: in definition of macro 'JSWSYMPTR_ENTRY'
   { offset, argSpec, pointer}
                      ^~~~~~~
/home/simon/MaBecker/Espruino_IDF5_MaBecker_baseline/gen/jswrapper.c:1644:3: warning: missing initializer for field 'functionPtr' of 'JswSymPtr' {aka 'const struct <anonymous>'} [-Wmissing-field-initializers]
   JSWSYMPTR_ENTRY(8, JSWAT_JSVAR | (JSWAT_JSVAR << (JSWAT_BITS*1)) | (JSWAT_JSVAR << (JSWAT_BITS*2)) | (JSWAT_JSVAR << (JSWAT_BITS*3)), (void*)jswrap_crypto_AES_encrypt)
   ^~~~~~~~~~~~~~~
In file included from /home/simon/MaBecker/Espruino_IDF5_MaBecker_baseline/gen/jswrapper.c:4:
/home/simon/MaBecker/Espruino_IDF5_MaBecker_baseline/src/jswrapper.h:81:10: note: 'functionPtr' declared here
   void (*functionPtr)(void);
          ^~~~~~~~~~~
[1354/1437] Building C object esp-idf/main/CMakeFiles/__idf_main.dir/home/simon/MaBecker/Espruino_IDF5_MaBecker_baseline/src/jsvar.c.obj
/home/simon/MaBecker/Espruino_IDF5_MaBecker_baseline/src/jsvar.c: In function 'jsvNewFromStringVar':
/home/simon/MaBecker/Espruino_IDF5_MaBecker_baseline/src/jsvar.c:2028:50: warning: passing argument 1 of 'jsvNewFlatStringFromStringVar' discards 'const' qualifier from pointer target type [-Wdiscarded-qualifiers]
       JsVar *var = jsvNewFlatStringFromStringVar(str, stridx, length);
                                                  ^~~
/home/simon/MaBecker/Espruino_IDF5_MaBecker_baseline/src/jsvar.c:1973:45: note: expected 'JsVar *' {aka 'struct JsVarStruct *'} but argument is of type 'const JsVar *' {aka 'const struct JsVarStruct *'}
 JsVar *jsvNewFlatStringFromStringVar(JsVar *var, size_t stridx, size_t maxLength) {
                                      ~~~~~~~^~~
ninja: build stopped: subcommand failed.
ninja failed with exit code 1
make: *** [make/targets/ESP32_IDF4.make:57: bin/espruino_2v28_esp32.bin] Error 2
