SimonGAndrews/ESP32_SGATest/docs/design/V2Harness/implementation/review-images/PC01-operating-mode-and-3v3-rail.png

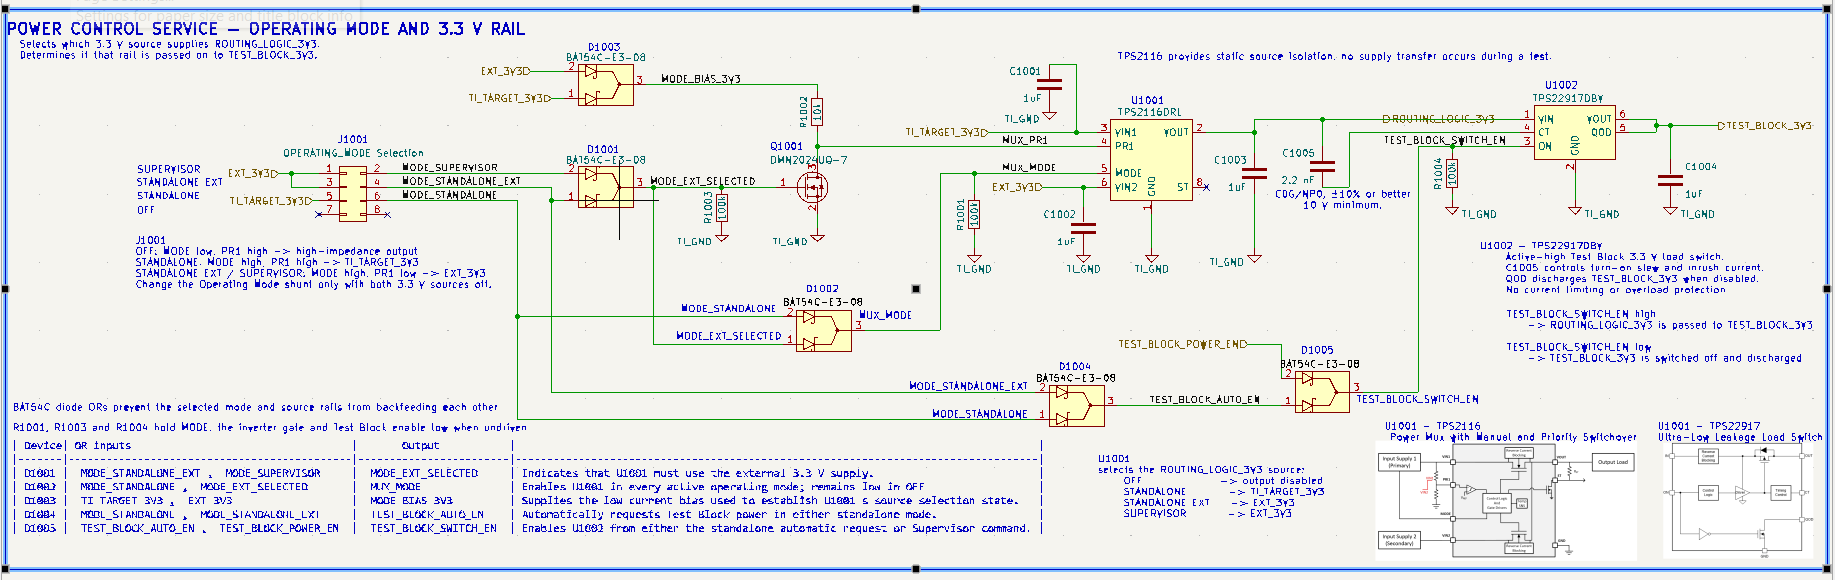
docs/design/V2Harness/implementation/review-images/PC01-operating-mode-and-3v3-rail.png
