SimonGAndrews/ESP32_SGATest/KICAD/V2/RevA/Espruino_Harness_RevA/verification/README.md

# Rev-A Schematic Verification

This directory separates regenerated working outputs from reviewed baseline
evidence for the V2 Rev-A Reusable Harness Board.

The governing human-readable baseline is:

```text
docs/design/V2Harness/implementation/ReusableHarnessRevA_DesignBaseline.md
```

The checker's requirements, design and operating model are specified in:

```text
docs/design/V2Harness/implementation/ReusableHarnessRevA_ConnectivityChecker.md
```

## Production exports

Always run production ERC and netlist export from the root schematic:

```text
Espruino_Harness_RevA.kicad_sch
```

For interactive iterative checks, save these working outputs in the KiCad
project directory using the exact names:

```text
Espruino_Harness_RevA.net
ERC.rpt
```

These files are replaceable working outputs and are not accepted evidence.
Raw KiCad netlists contain timestamps and checkout-specific paths, so they are
unsuitable as deterministic, cross-platform baselines. The ignored
`verification/generated/` directory may hold temporary checker output.

Workbench-only diagnostics use:

```text
generated/draft_workbench_Working.net
generated/draft_workbench_Working_ERC.rpt
```

They are not production evidence.

## Tracked baseline evidence

Reviewed evidence is stored under `baseline/`:

```text
baseline/Espruino_Harness_RevA_FullHierarchy_Connectivity.json
baseline/Espruino_Harness_RevA_FullHierarchy_ERC.rpt
baseline/Espruino_Harness_RevA_BOM.csv
```

The connectivity JSON will be a sorted, path-free representation generated
from the raw netlist. The Git commit recorded in the design baseline identifies
the exact KiCad sources from which the evidence was generated. The design
baseline records the release checklist and final manufacturing decision; a
second manually maintained summary is not required.

`ReusableHarnessRevA_Connectivity.yaml` is the contract-set manifest. It
identifies only block contracts that contain real reviewed intent:

```text
ReusableHarnessRevA_Connectivity.yaml
contracts/
  PC01-operating-mode-and-3v3-rail.yaml
  PC02-target-5v-switch-and-two-range-monitor.yaml
  RC01-routing-fabric.yaml
  RC02-routing-controllers-and-fixed-i2c-isolation.yaml
  TB01-digital-gpio-loopback.yaml
  TB02-analogue-pwm-feedback.yaml
  TB03-i2c-functional-device.yaml
  TB04-spi-functional-device-and-storage.yaml
  TB05-onewire-functional-devices-and-gpio.yaml
  TB07-uart-crosslink-and-external-peer.yaml
  TB09-addressable-rgb-output.yaml
  TI01-target-interface-connector-banks.yaml
  SYS01-power-events-to-rack-control.yaml
```

The manifest and every referenced file together form the independent
connectivity contract. They are reviewed design input, not generated from the
schematic. Planned blocks remain in the design-baseline register until their
analysis produces a substantive contract. `SYS01` records the first reviewed
cross-block rule: the PC02 low-range alert/interlock path into the Rack Control
Endpoint.

## Connectivity checker

Run the dependency-free Node.js checker from the repository root after
exporting the complete production netlist:

```powershell
node KICAD/V2/RevA/Espruino_Harness_RevA/verification/check-connectivity.mjs `
  --netlist KICAD/V2/RevA/Espruino_Harness_RevA/Espruino_Harness_RevA.net
```

This invocation loads `ReusableHarnessRevA_Connectivity.yaml`, checks every
contract listed by it against the explicit working full-hierarchy netlist, and
writes the deterministic accepted result to:

```text
baseline/Espruino_Harness_RevA_FullHierarchy_Connectivity.json
```

The checker evaluates the current contract schema's `pin_net`,
`component_value` and `forbidden_same_net` assertions. It returns exit code
zero only when every assertion passes. A failed run prints every mismatch,
returns a non-zero exit code and does not overwrite an existing accepted
baseline. Use `node .../check-connectivity.mjs --help` for explicit input and
output overrides.

## Acceptance rule

An individual sheet ERC or netlist may be used while editing, but only a
full-hierarchy check can provide accepted production evidence. Every exclusion
or intentional difference must be recorded in the design baseline.
