SimonGAndrews/ESP32_SGATest/docs/investigations/IDF5_port_testing/2026-08-31-pr2-i2c-config.md

# PR 2: Initialise the Complete ESP32 I2C Configuration

## Upstream Outcome

Merged as Espruino PR `#2734` by commit `25f81a8e1` and included in master
merge `5d79af218`.

## Submission Details

- Upstream repository: `espruino/Espruino`
- Base branch: `IDF5`
- Fork: `SimonGAndrews/Espruino`
- Head branch: `fix/esp32-idf5-i2c-config`
- Commit: `3be2bb5c1`
- PR title: `ESP32: initialise the complete I2C configuration`

This branch is based directly on `official/IDF5`. It does not depend on PR 1.

## Copy-ready PR Description

### Issue

The ESP32 I2C setup path declared its local `i2c_config_t` without
initialising it. It then set `clk_flags` only when compiling for ESP32-C3 or
ESP32-S3. On the classic ESP32 IDF5 target, `clk_flags` and any other fields
not explicitly assigned therefore contained indeterminate stack data.

On the tested classic ESP32 IDF5 build, Espruino `I2C1.setup()` could fail
before any I2C transaction was attempted.

### Fix

Zero-initialise the complete `i2c_config_t`, then set `clk_flags` to select the
default I2C clock source for ESP-IDF 4 and later on every ESP32-family target.

This removes the target-specific gap and ensures that fields introduced by
newer ESP-IDF versions always start from defined values.

### Validation

The exact I2C patch in this standalone branch was built and tested as part of
the staged classic ESP32 IDF5 candidate using ESP-IDF 5.5.3 and
`BOARD=ESP32_IDF5`:

- clean standard release build: pass;
- firmware flash, boot and USB-UART REPL connection: pass;
- reported staged commit: `26d927e64`;
- `I2C1.setup({scl:D22,sda:D21,bitrate:100000})`: pass;
- MCP23008 at address `0x20`, using `I2C.writeTo()` and `I2C.readFrom()` for
  register readback plus GPIO feedback: 6/6 pass;
- secondary MCP23008 at address `0x21`, including register changes, restoration
  and isolation from the first device: 8/8 pass;
- MCP23008 interrupt status/capture and interrupt clearing over I2C: pass.

One physical interrupt-level assertion on ESP32 pin D35 was not observed,
despite the MCP23008 `INTF` and `INTCAP` registers proving that the interrupt
occurred. That remaining observation concerns the V1 harness `SEL_D35` signal
path and is not an I2C setup or transaction failure.

The standalone PR diff was checked byte-for-byte against the tested I2C
commit patch and is identical.

## Manual Submission

Run from a terminal:

```bash
cd /home/simon/MaBecker/Espruino_IDF5_PR
git status --short --branch
git log --oneline official/IDF5..fix/esp32-idf5-i2c-config
git diff --check official/IDF5...fix/esp32-idf5-i2c-config
git push -u simon fix/esp32-idf5-i2c-config
```

On the GitHub **Compare changes** page, select **compare across forks**, then
set:

- base repository: `espruino/Espruino`;
- base branch: `IDF5`;
- head repository: `SimonGAndrews/Espruino`;
- compare branch: `fix/esp32-idf5-i2c-config`.

Use the title and description above. Before selecting **Create pull request**,
confirm that GitHub shows one commit and only
`targets/esp32/jshardwareI2c.c` in **Files changed**.
