SimonGAndrews/ESP32_SGATest/docs/investigations/IDF5_port_testing/2026-08-31-pr3-adc.md

# PR 3: Restore ESP32 IDF5 Analogue Input

## Upstream Outcome

Merged as Espruino PR `#2735` by commit `149ccda22` and included in master
merge `5d79af218`.

## Submission Details

- Upstream repository: `espruino/Espruino`
- Base branch: `IDF5`
- Fork: `SimonGAndrews/Espruino`
- Head branch: `fix/esp32-idf5-adc`
- Commit: `bb7282d6140198067d0368fd70a217e6c8071b5c`
- PR title: `ESP32 IDF5: restore analogue input`

This branch is based directly on `official/IDF5` at `25f81a8e1`, after PR 1
and PR 2 were merged.

## Copy-ready PR Description

### Issue

The ESP32 hardware layer explicitly disabled both analogue-input functions
when compiling with ESP-IDF 5 or later. `analogRead()` therefore reported that
`jshPinAnalog()` was not implemented and returned `NaN`, even though the
classic ESP32 ADC backend and its initialisation path are present in the IDF5
build.

The same guard also disabled the fast analogue-input path used internally by
Espruino.

### Fix

Remove the IDF5-only stubs from `jshPinAnalog()` and `jshPinAnalogFast()` so
that IDF5 uses the existing ESP32 `readADC()` implementation, including the
normal pin validation, scaling and inverted-pin handling.

The correction removes ten preprocessor/stub lines and changes no ADC
conversion logic.

### Validation

The standalone branch was built from a clean tree using ESP-IDF 5.5.3 and
`BOARD=ESP32_IDF5`:

- clean standard release build with `RELEASE=1`: pass;
- generated firmware version: `2v29.63`;
- firmware binary SHA-256:
  `f25702762e7da5b8c2b434f0560941d36b4a36de589e6fa11dd56a8f219e2eef`;
- release archive SHA-256:
  `c93e7325781b7a108afda4ee0c0b135cc116b3737d59792dfa547c95675c7421`.

The exact patch was also included in the staged classic ESP32 IDF5 firmware
flashed to the V1 test bench. Using an output pin wired to an ADC-capable input
pin, Espruino `analogRead()` produced:

- driven low: `0`;
- driven high: `0.99975585937`;
- four assertions passed out of four.

The standalone commit and the tested staged commit have the same stable Git
patch ID: `187035eeb9c5769a5e6ec24d0867a616c0a02693`.

After Gordon merged PR 1 and PR 2, the branch was rebased onto `25f81a8e1`.
The commit ID changed to `bb7282d61`; the stable patch ID and file diff are
unchanged, and `git diff --check` passes.

## Manual Submission

Run from a terminal:

```bash
cd /home/simon/MaBecker/Espruino_IDF5_PR
git status --short --branch
git log --oneline official/IDF5..fix/esp32-idf5-adc
git diff --check official/IDF5...fix/esp32-idf5-adc
git push -u simon fix/esp32-idf5-adc
```

On the GitHub **Compare changes** page, select **compare across forks**, then
set:

- base repository: `espruino/Espruino`;
- base branch: `IDF5`;
- head repository: `SimonGAndrews/Espruino`;
- compare branch: `fix/esp32-idf5-adc`.

Use the title and description above. Before selecting **Create pull request**,
confirm that GitHub shows one commit and only `targets/esp32/jshardware.c` in
**Files changed**. The expected change is ten deletions.
