SimonGAndrews/ESP32_SGATest/tests/Results/WIFI_BLE_Results/2026-07-20-usb-path-identity-baseline.md

# USB Path Identity Baseline

Date: 20 July 2026

## Conclusion

The standalone V1 Wi-Fi/BLE bench passed the positive configuration check.
Each fixed `/dev/serial/by-path/` connection resolved to one unique serial
device and returned the board, firmware and wireless capabilities assigned to
that physical bench position.

This proves the positive half of the V2 Section 5.5 host-identity principle.
The physical-port swap also produced the expected configuration failure,
providing the corresponding negative test.

## Preconditions

- both harnesses in `STANDALONE` mode
- targets powered only through fully connected USB cables with VBUS present
- no external target power
- no Harness Supervisor or controlled target-power service
- no other REPL or serial tool attached
- configuration: `tests/WIFI_BLE/standalone_bench_config.json`

## Command

```bash
python3 tools/repl/verify_bench_config.py \
  tests/WIFI_BLE/standalone_bench_config.json
```

## Observed Identity

| Position | Configured physical path suffix | Resolved device | Board | Version | Git commit | Wi-Fi | BLE |
|---|---|---|---|---|---|---|---|
| `esp32_v1` | `usb-0:10.3:1.0-port0` | `/dev/ttyUSB0` | `ESP32` | `2v29.97` | `d3d33f4aa` | function | function |
| `esp32_c3_v1` | `usb-0:10.4:1.0-port0` | `/dev/ttyUSB1` | `ESP32C3_IDF4` | `2v29.107` | `0af6e1568` | function | function |

Final verifier result:

```text
DONE=PASS
```
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
