SimonGAndrews/ESP32_SGATest/tests/Results/WIFI_BLE_Results/2026-07-20-wifi-station-static-ip.md

# Wi-Fi Station Static IP

Date: 20 July 2026

## Conclusion

`Wifi.setIP()` did not apply a post-association static station address on
either the classic ESP32 legacy or ESP32-C3 IDF4 build. Both stations first
received `192.168.4.2` by DHCP, called `setIP()` requesting `192.168.4.77`, and
then received `null` through the callback as though the operation had
succeeded. `Wifi.getIP()` nevertheless remained at `.2`, and the target AP
independently observed application traffic originating from `.2`.
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
