SimonGAndrews/ESP32_SGATest/docs/investigations/uart/canidate_fix_01.png

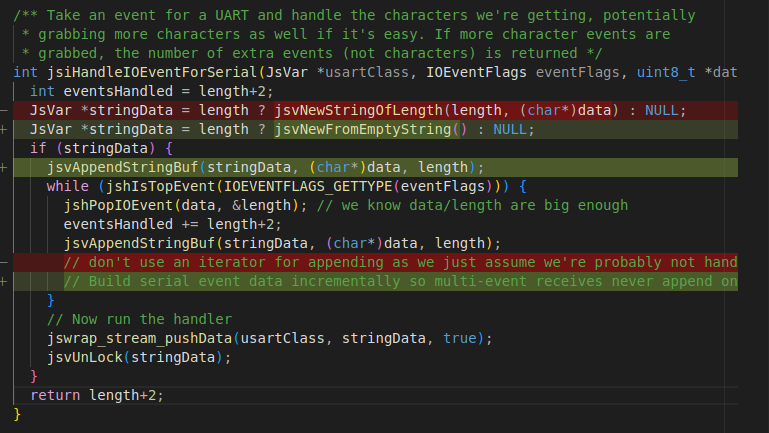
docs/investigations/uart/canidate_fix_01.png
