SimonGAndrews/ESP32_SGATest/docs/targets/olimex-esp32-devkit-lipo/Resources/ESP32-S3-DevKit-LiPo_Rev_B.pdf

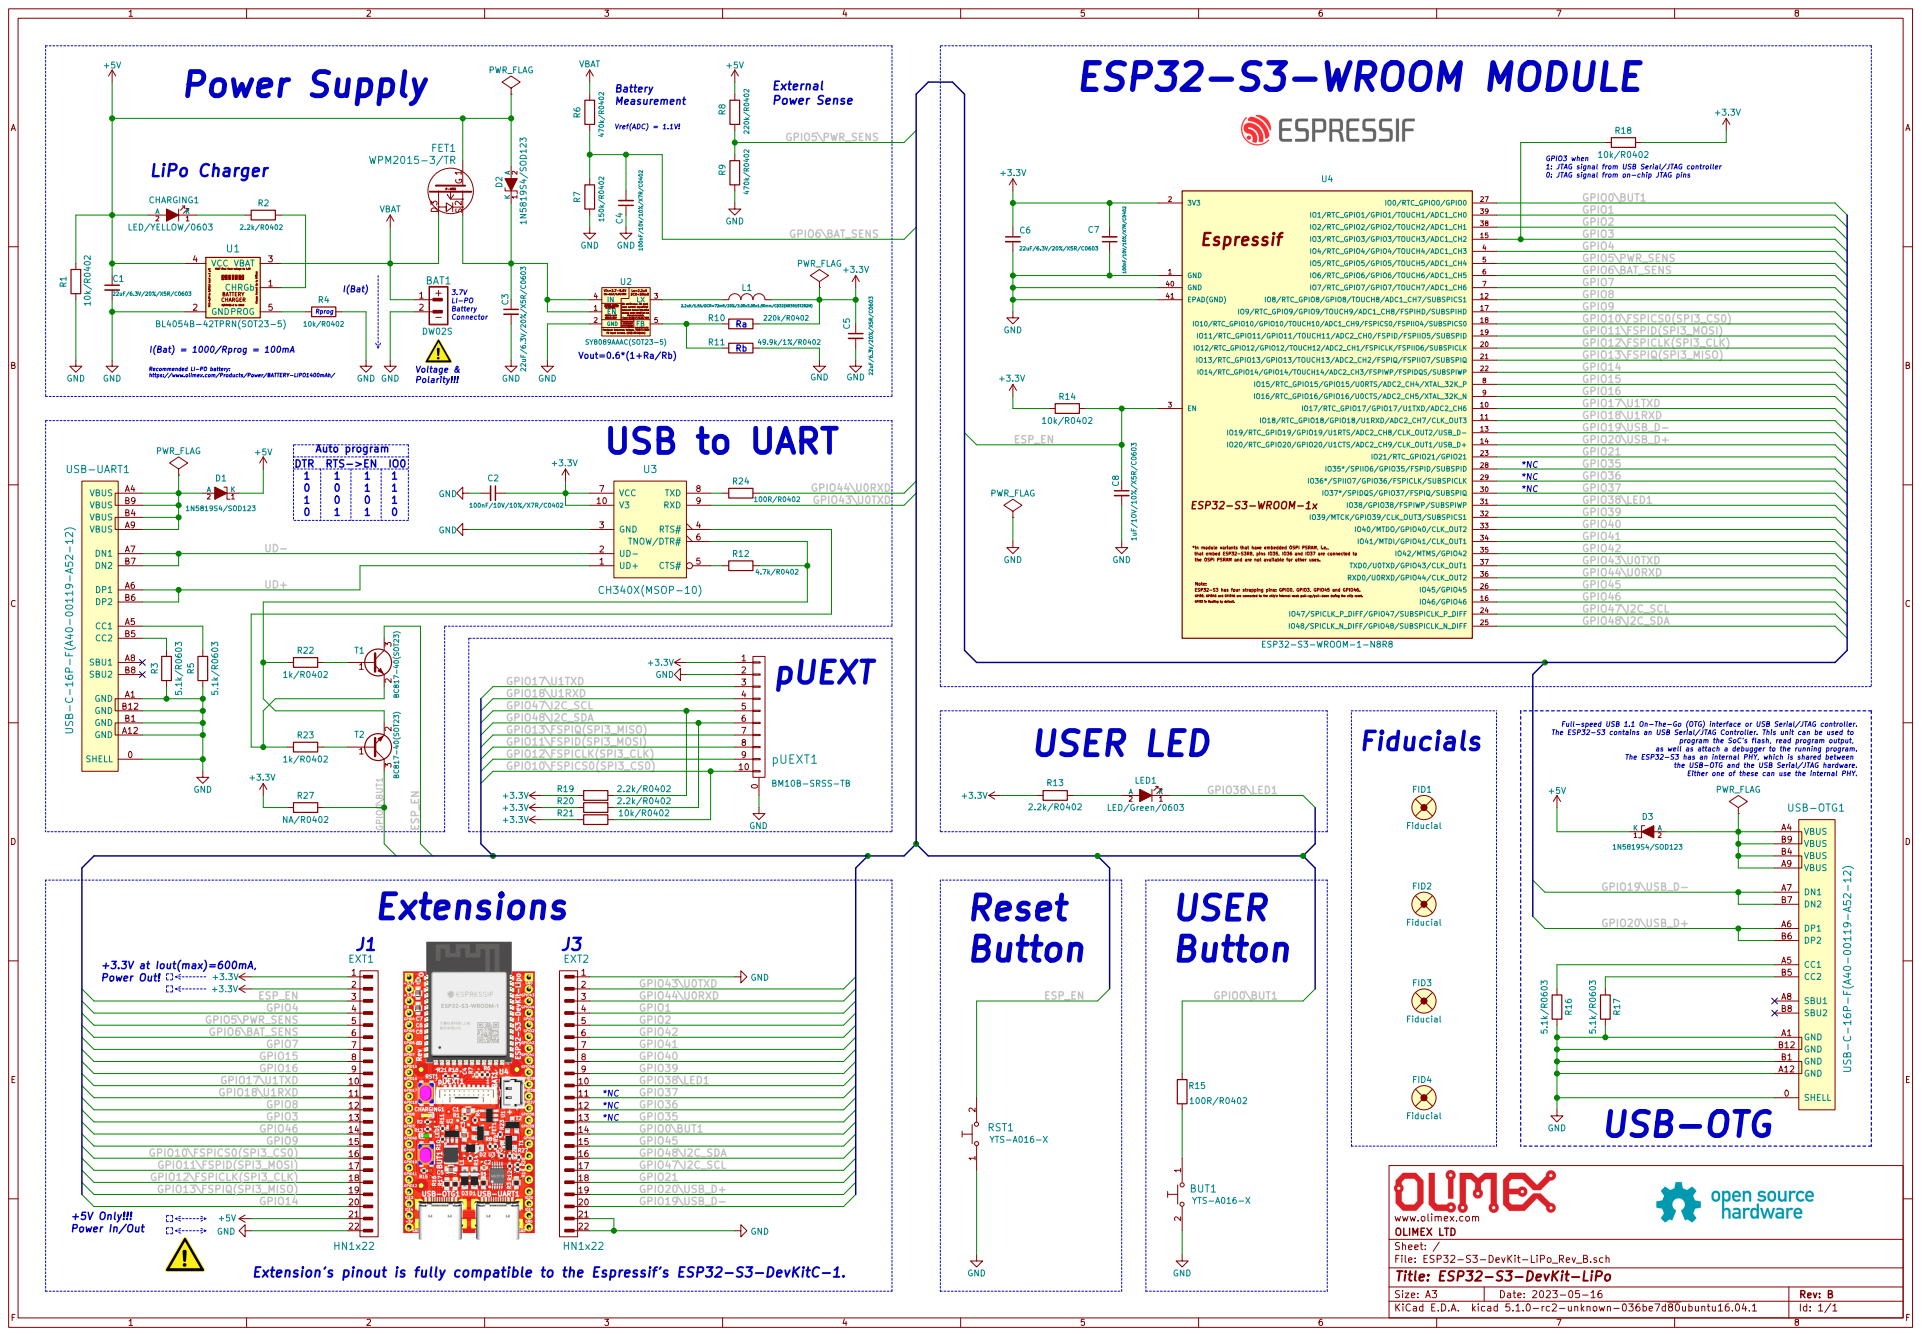
[picture p37: page 1]

External
Power Sense
the OSPI PSRAM and are not available for other uses. GND 1

10k/R0402 GPIO3 when 1: JTAG signal from USB Serial/JTAG controller 0: JTAG signal from on-chip JTAG pins

Full-speed USB 1.1 On-The-Go (OTG) interface or USB Serial/JTAG controller. The ESP32-S3 contains an USB Serial/JTAG Controller. This unit can be used to program the SoCs flash, read program output, as well as attach a debugger to the running program. The ESP32-S3 has an internal PHY, which is shared between the USB-OTG and the USB Serial/JTAG hardware. Either one of these can use the internal PHY. GPIO6\BAT_SENS

load current capability! Lx=2.2uH

Do not float. Enable control. FB Input Current, I(FB)=50nA(max) Feedback Reference Voltage, V(REF)=0.6V

*In module variants that have embedded OSPI PSRAM, i.e., ESP32-S3 has four strapping pins: GPIO0, GPIO3, GPIO45 and GPIO46. ESP32-S3-WROOM-1x

that embed ESP32-S3R8, pins IO35, IO36 and IO37 are connected to

GPIO0, GPIO45 and GPIO46 are connected to the chips internal weak pull-up/pull-down during the chip reset. GPIO3 is floating by default. Note:

9EXT1 HN1x22 Extension's pinout is fully compatible to the Espressif's ESP32-S3-DevKitC-1.
+3.3V GND
ESP_EN GPIO4 GPIO5\PWR_SENS

www.olimex.com
File: ESP32-S3-DevKit-LiPo_Rev_B.sch Sheet: / OLIMEX LTD

Id: 1/1 Title: ESP32-S3-DevKit-LiPo
